mzandrew/idlab-scrod/mechanical-designs/board-stack/fDIRC/from-Jerry/Detector_holder copy.pdf

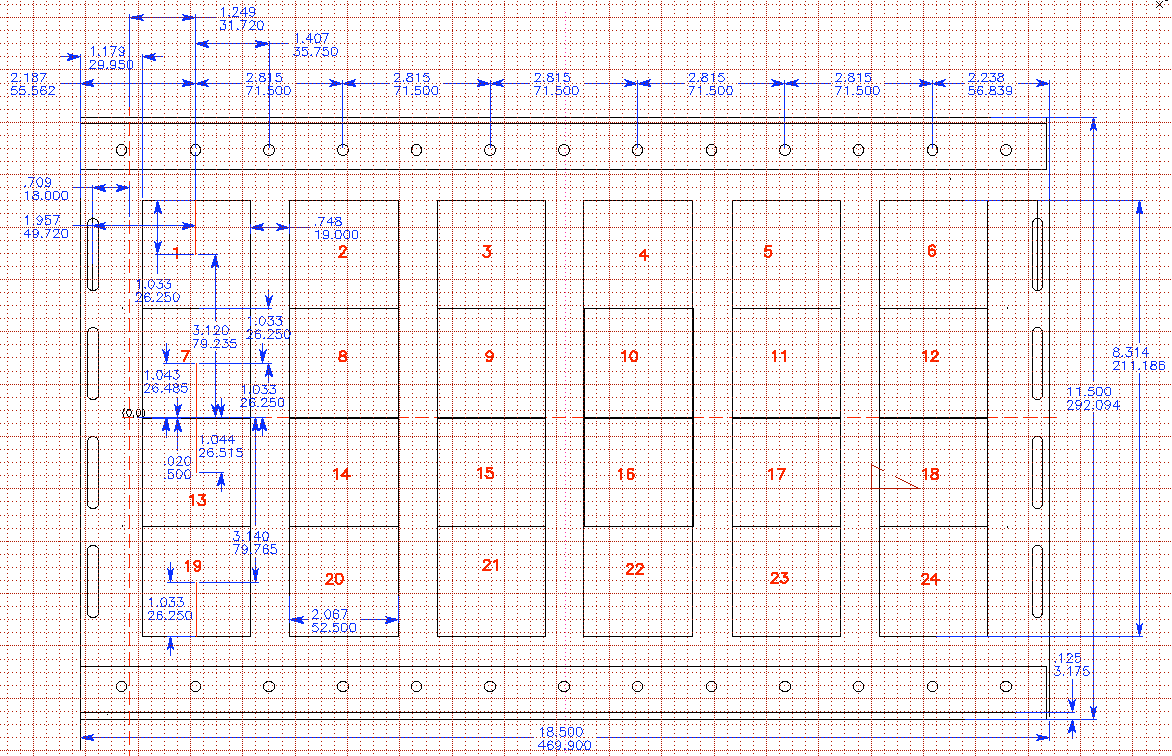
[picture p3: page 1]
