mzandrew/idlab-scrod/mechanical-designs/board-stack/fDIRC/from-Jerry/FDIRC_detector_enclosure.pdf

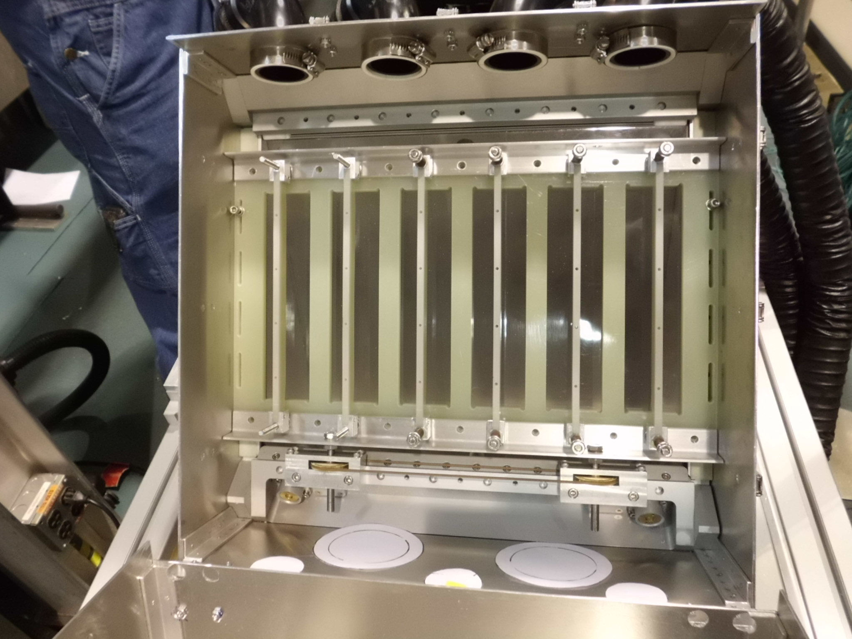
[picture p4: page 1]
