mzandrew/idlab-scrod/mechanical-designs/board-stack/fDIRC/from-Jerry/FDIRC_detector_frame.pdf

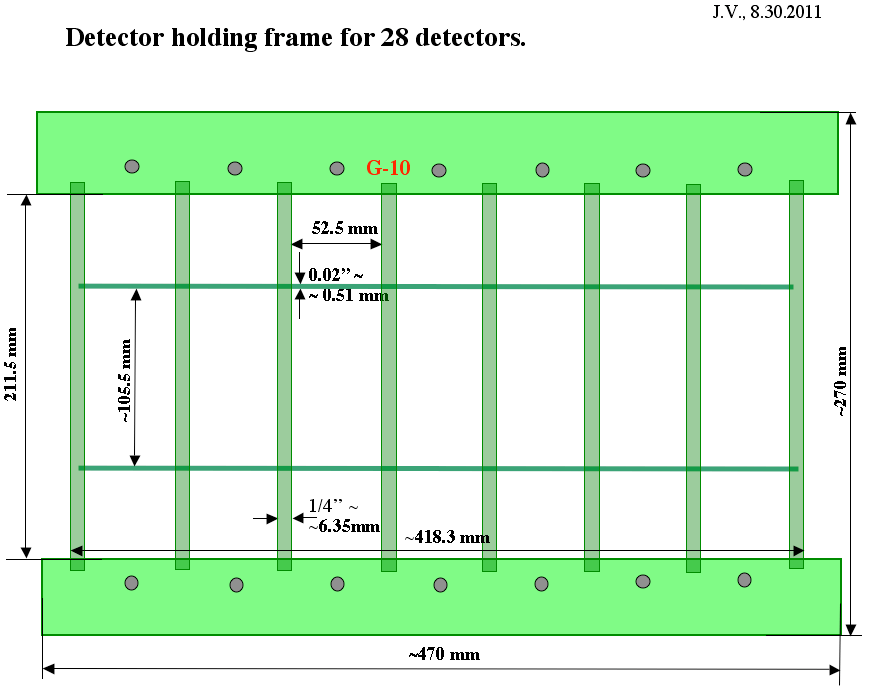
[picture p5: page 1]
