mzandrew/idlab-scrod/mechanical-designs/board-stack/fDIRC/from-Jerry/FDIRC_detector_frame_c.pdf

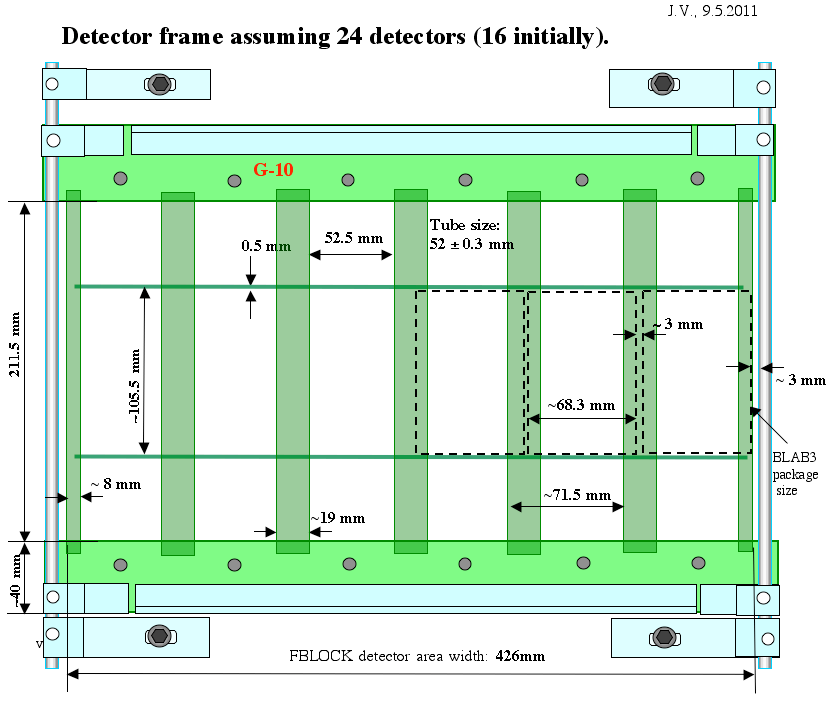
[picture p6: page 1]
