mzandrew/idlab-scrod/mechanical-designs/board-stack/fDIRC/from-Jerry/FDIRC_with_IRS2_electronics.6.pdf

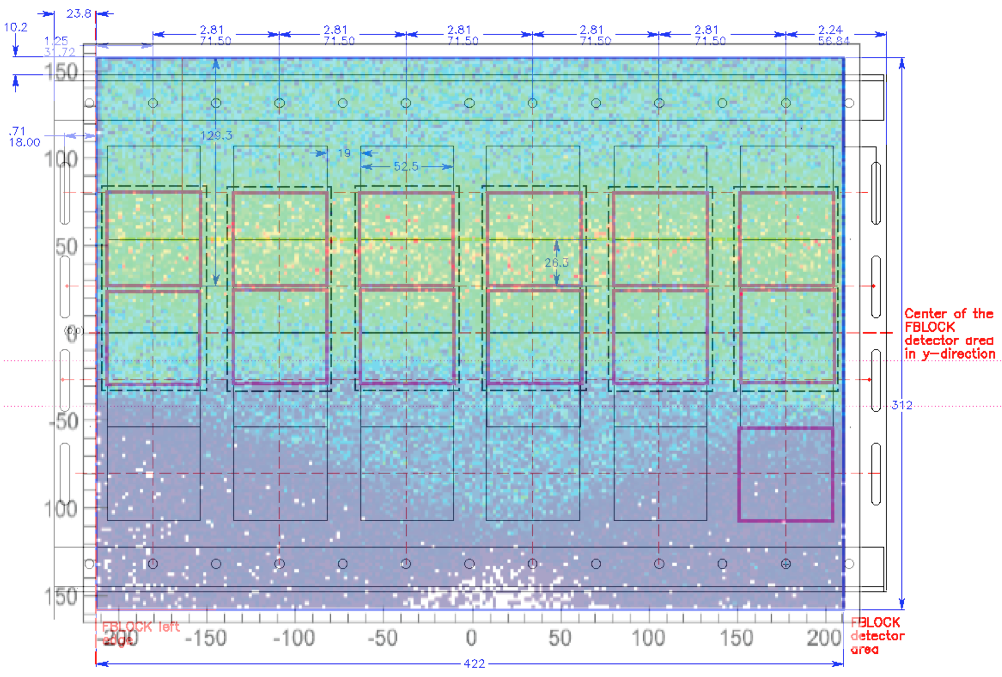
[picture p7: page 1]
