mzandrew/idlab-scrod/mechanical-designs/board-stack/fDIRC/from-Jerry/CIMG1078.JPG

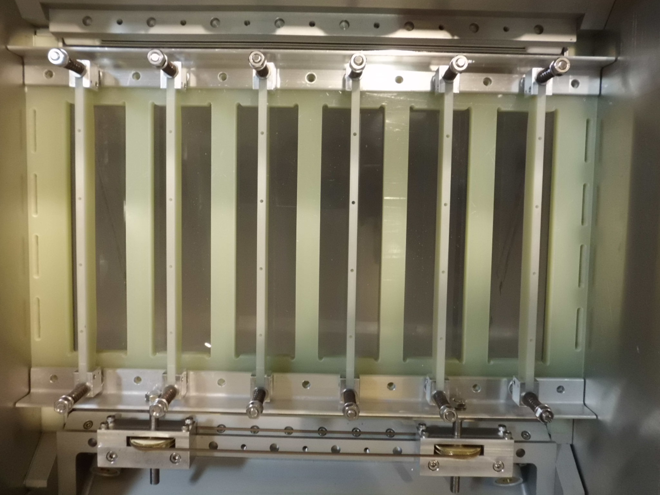
mechanical-designs/board-stack/fDIRC/from-Jerry/CIMG1078.JPG
