mzandrew/idlab-scrod/mechanical-designs/board-stack/fDIRC/from-Jerry/fDIRC_BLAB_PKG.JPG

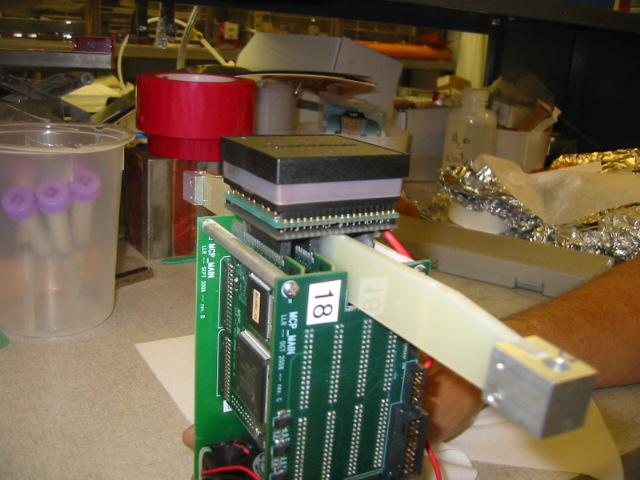
mechanical-designs/board-stack/fDIRC/from-Jerry/fDIRC_BLAB_PKG.JPG
