mzandrew/idlab-scrod/mechanical-designs/board-stack/fDIRC/from-Jerry/IMG_2022.JPG

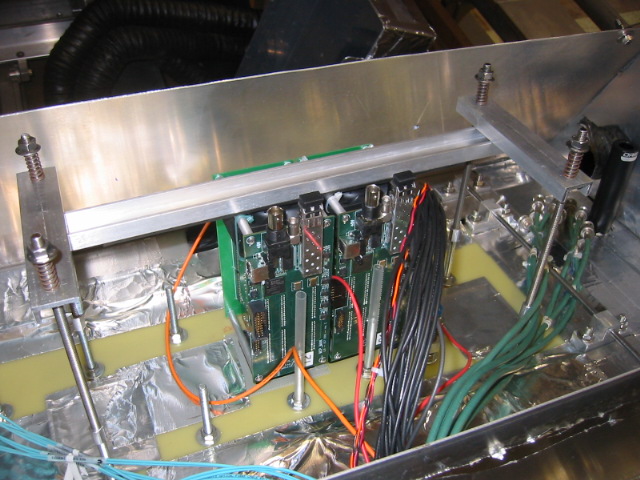
mechanical-designs/board-stack/fDIRC/from-Jerry/IMG_2022.JPG
