mzandrew/idlab-scrod/mechanical-designs/board-stack/iTOP/export/HV-bracket-and-boardstack-spacers.png

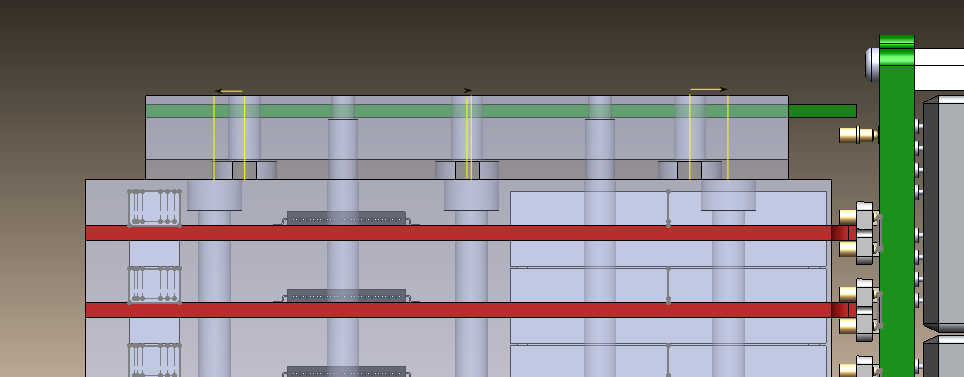
mechanical-designs/board-stack/iTOP/export/HV-bracket-and-boardstack-spacers.png
