mzandrew/idlab-scrod/mechanical-designs/board-stack/iTOP/export/intermediate-boardstack-spacers.cropped.png

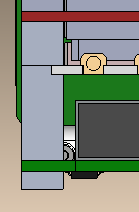
mechanical-designs/board-stack/iTOP/export/intermediate-boardstack-spacers.cropped.png
