mzandrew/idlab-scrod/mechanical-designs/board-stack/iTOP/export/intermediate-boardstack-spacers.png

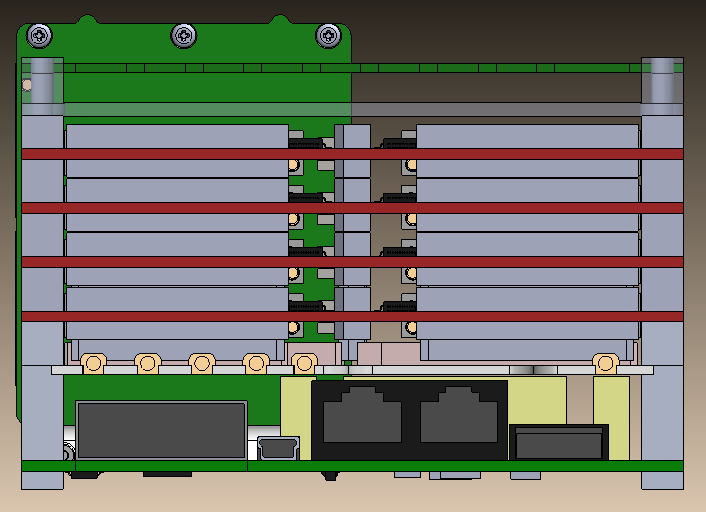
mechanical-designs/board-stack/iTOP/export/intermediate-boardstack-spacers.png
