mzandrew/idlab-scrod/mechanical-designs/board-stack/iTOP/export/iTOP-side-view.intermediate-version.cropped.png

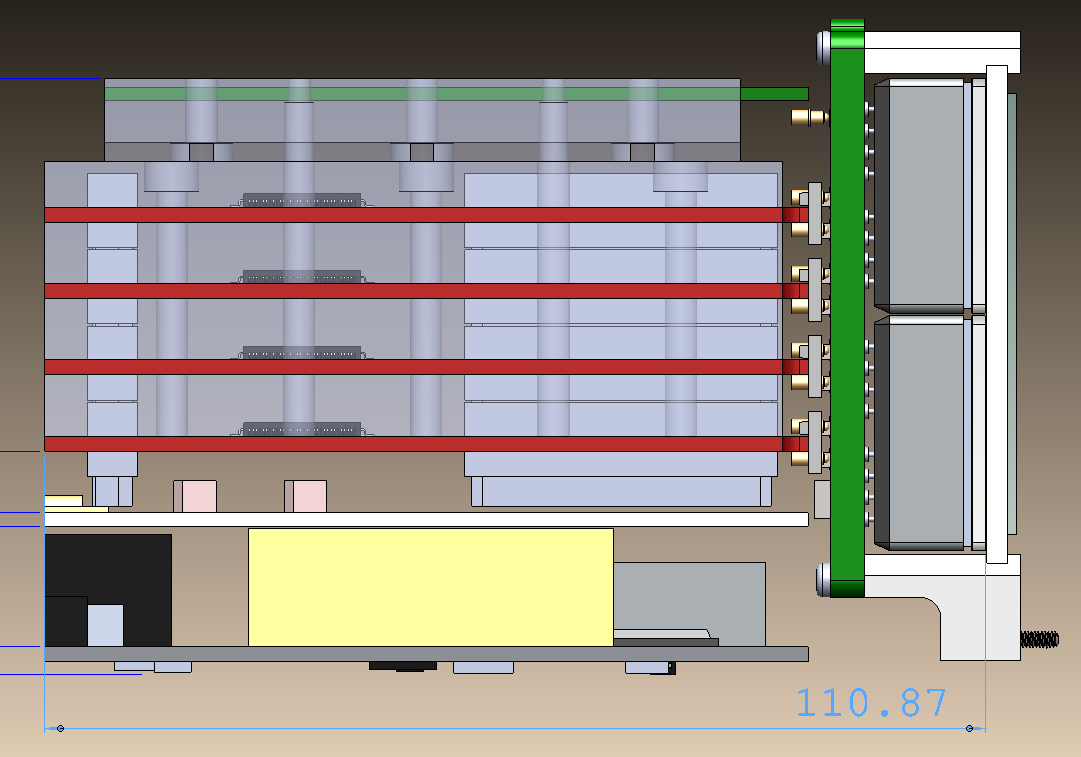
mechanical-designs/board-stack/iTOP/export/iTOP-side-view.intermediate-version.cropped.png
