mzandrew/idlab-scrod/mechanical-designs/board-stack/iTOP/export/iTOP-side-view.pre-production-prototype-version.png

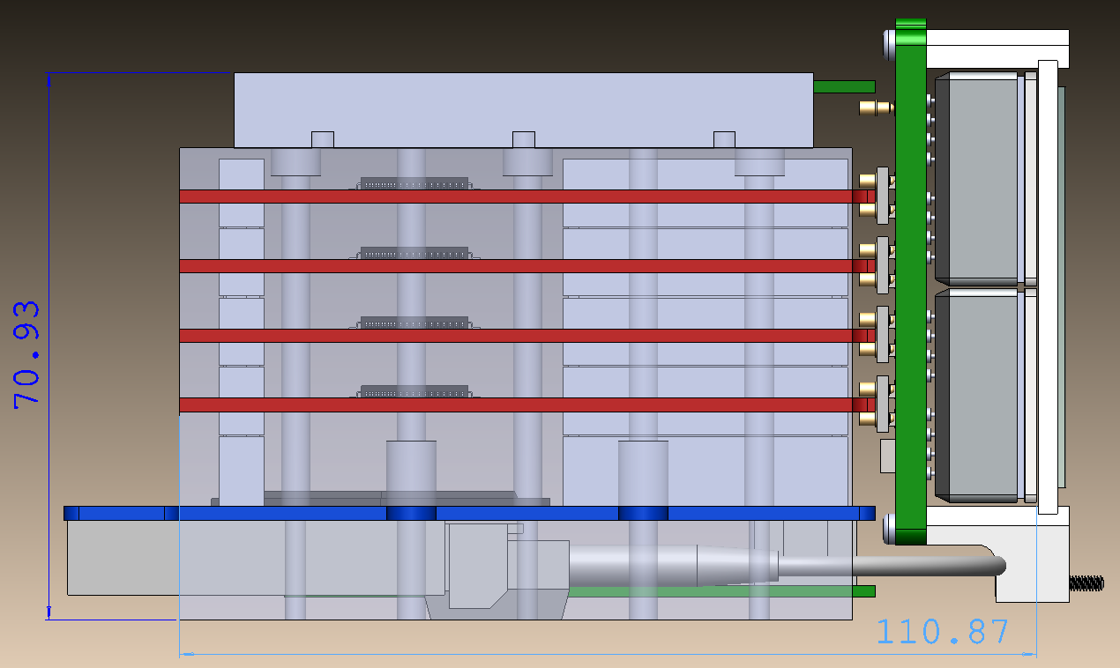
mechanical-designs/board-stack/iTOP/export/iTOP-side-view.pre-production-prototype-version.png
