mzandrew/idlab-scrod/mechanical-designs/board-stack/iTOP/export/iTOP.JPG

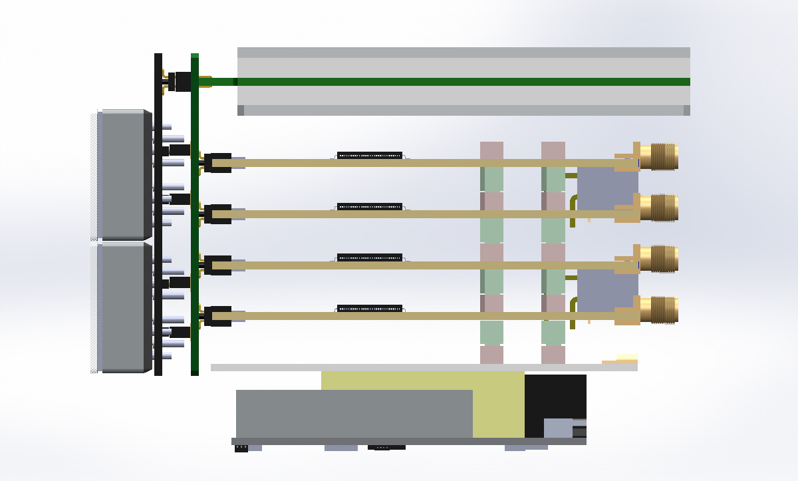
mechanical-designs/board-stack/iTOP/export/iTOP.JPG
