mzandrew/idlab-scrod/mechanical-designs/board-stack/iTOP/export/pogo-pin-carriers.png

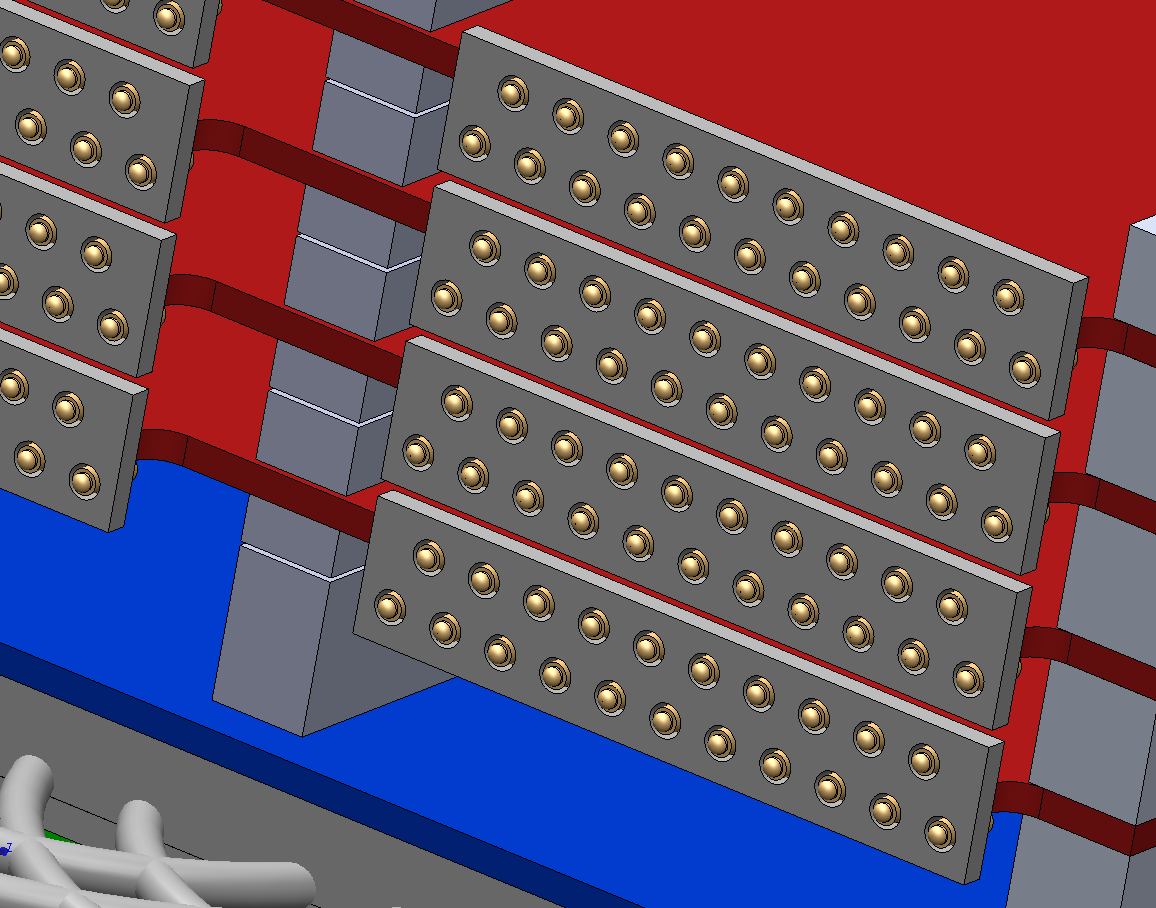
mechanical-designs/board-stack/iTOP/export/pogo-pin-carriers.png
