mzandrew/idlab-scrod/mechanical-designs/board-stack/iTOP/export/pogo-pin-carriers.revB.loaded.png

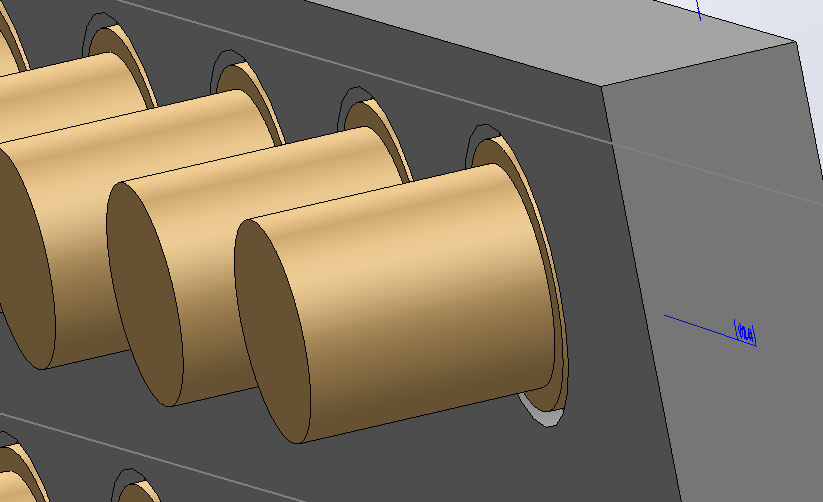
mechanical-designs/board-stack/iTOP/export/pogo-pin-carriers.revB.loaded.png
