mzandrew/idlab-scrod/mechanical-designs/board-stack/iTOP/export/pogo-pin-carriers.revB.png

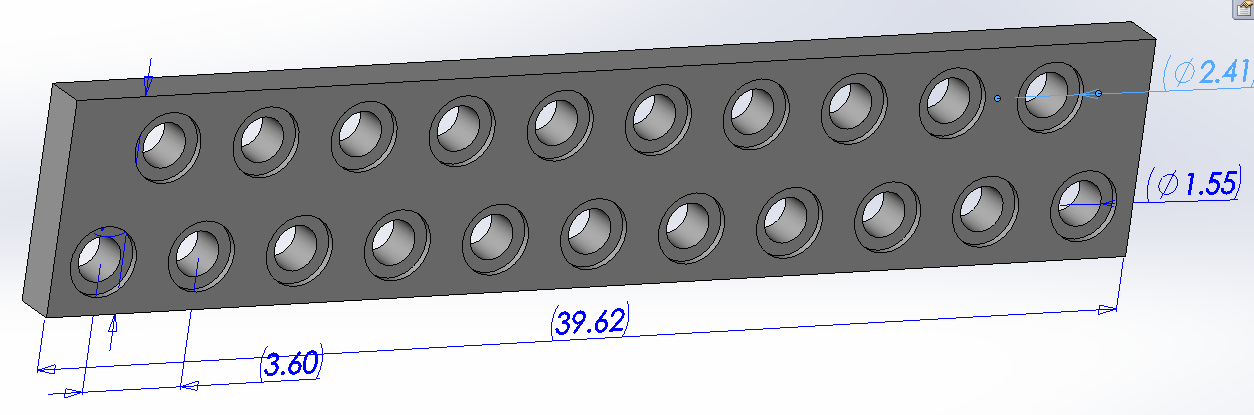
mechanical-designs/board-stack/iTOP/export/pogo-pin-carriers.revB.png
