mzandrew/idlab-scrod/mechanical-designs/board-stack/iTOP/export/pogo-pin-side-view.png

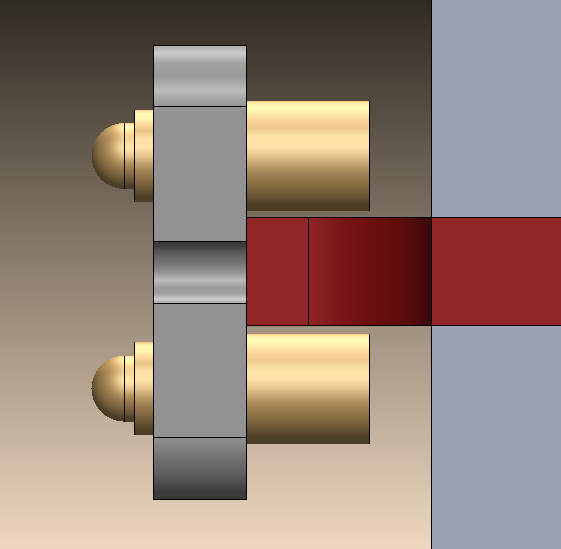
mechanical-designs/board-stack/iTOP/export/pogo-pin-side-view.png
