mzandrew/idlab-scrod/mechanical-designs/board-stack/iTOP/export/pogo-pins-in-pogo-pin-carrier-on-carrier.png

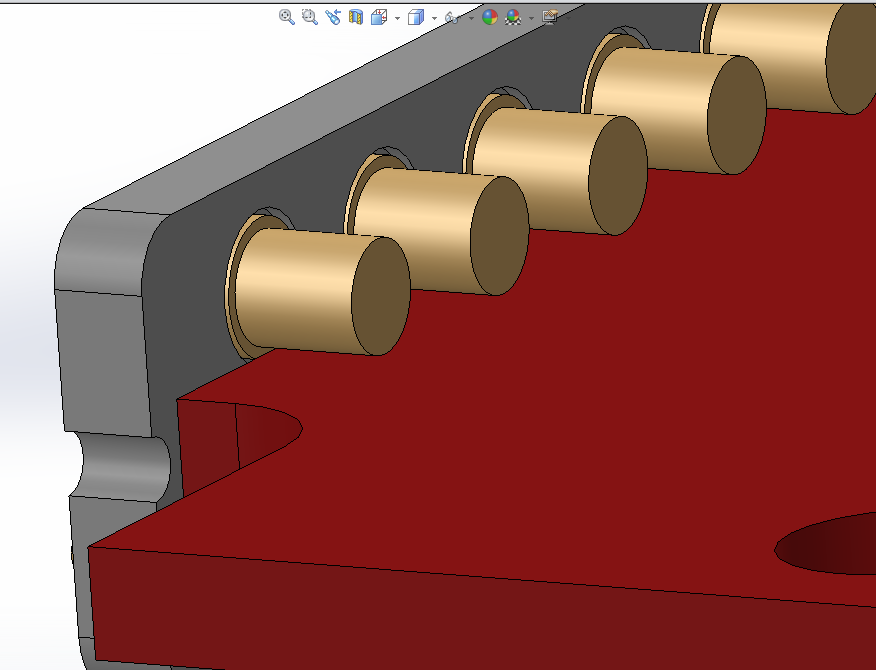
mechanical-designs/board-stack/iTOP/export/pogo-pins-in-pogo-pin-carrier-on-carrier.png
