mzandrew/idlab-scrod/mechanical-designs/board-stack/iTOP/export/SCROD-and-carriers-with-walls.JPG

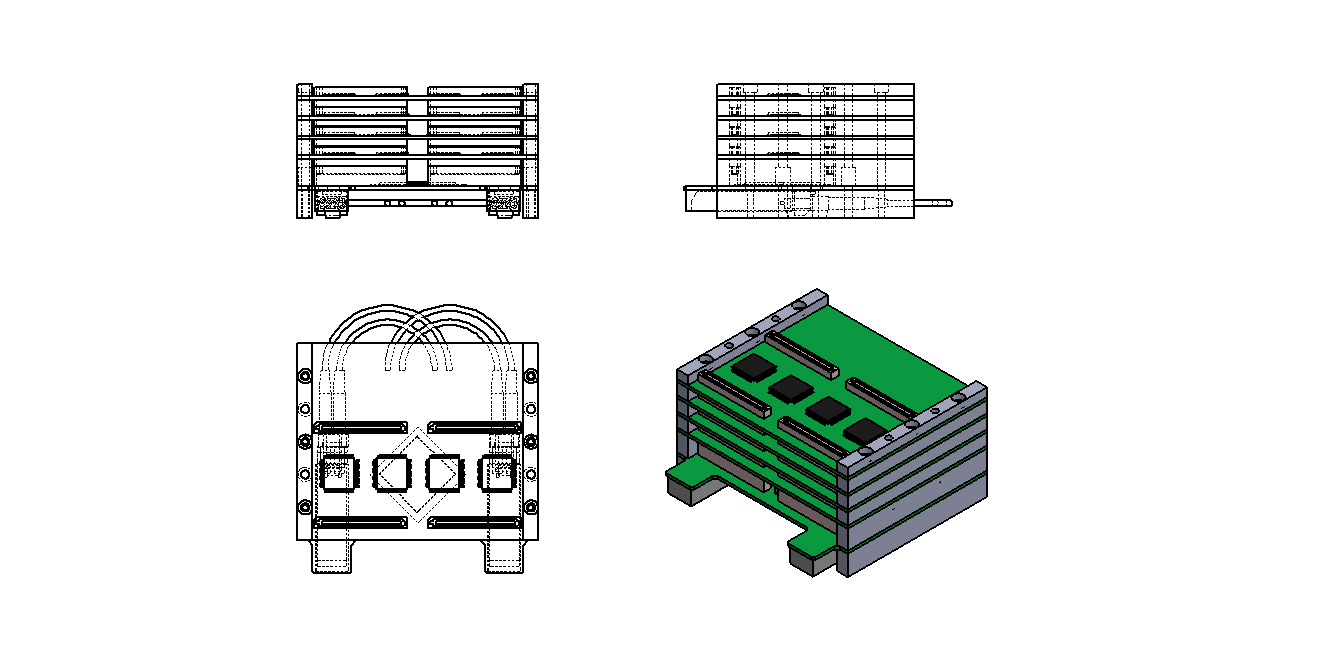
mechanical-designs/board-stack/iTOP/export/SCROD-and-carriers-with-walls.JPG
