mzandrew/idlab-scrod/mechanical-designs/board-stack/iTOP/export/SCROD-to-screwhead-clearance.png

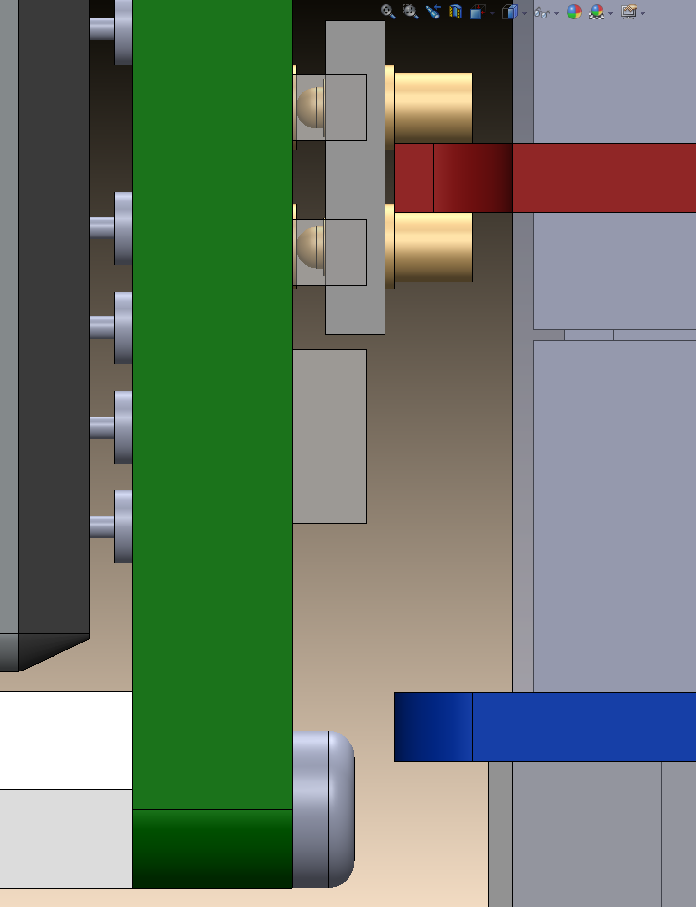
mechanical-designs/board-stack/iTOP/export/SCROD-to-screwhead-clearance.png
