mzandrew/idlab-scrod/mechanical-designs/board-stack/iTOP/export/XY-stage-with-brackets-laser-jig-and-intermediate-boardstack.png

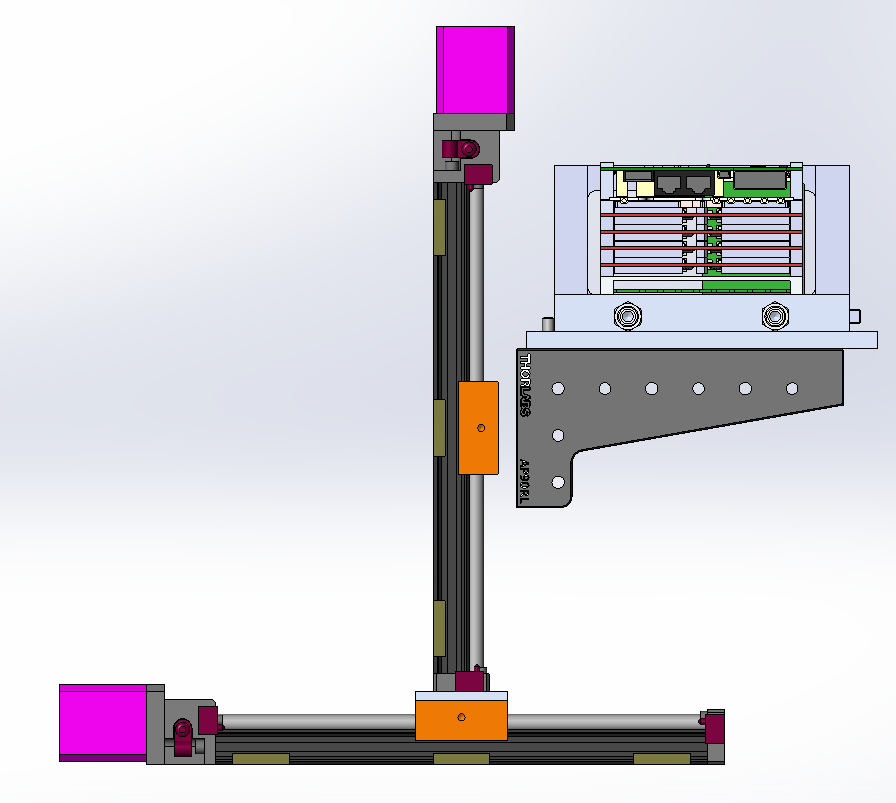
mechanical-designs/board-stack/iTOP/export/XY-stage-with-brackets-laser-jig-and-intermediate-boardstack.png
