mzandrew/idlab-scrod/mechanical-designs/board-stack/mTC/export/mTC.24PMTs.JPG

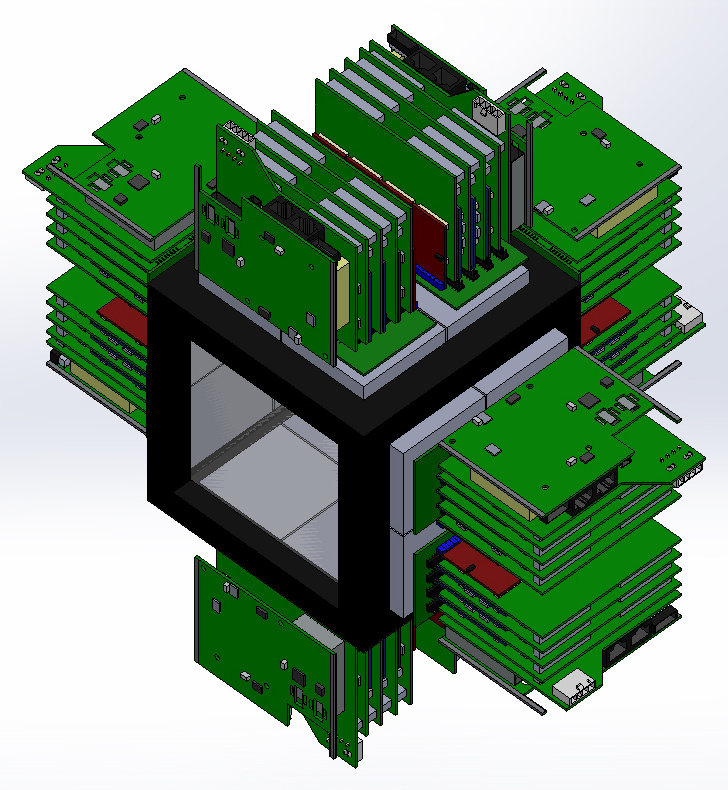
mechanical-designs/board-stack/mTC/export/mTC.24PMTs.JPG
