mzandrew/idlab-scrod/mechanical-designs/tags/r282.iTOP-module-used-at-LEPS-SPRING8/board-stack/export/board-stack.common.top.JPG

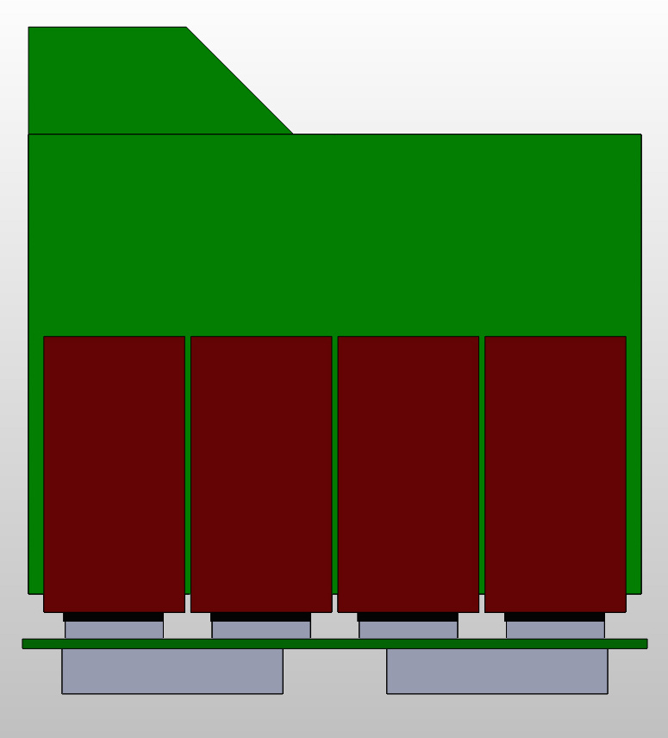
mechanical-designs/tags/r282.iTOP-module-used-at-LEPS-SPRING8/board-stack/export/board-stack.common.top.JPG
