mzandrew/idlab-scrod/mechanical-designs/tags/r282.iTOP-module-used-at-LEPS-SPRING8/board-stack/iTOP/export/iTOP-cutaway.JPG

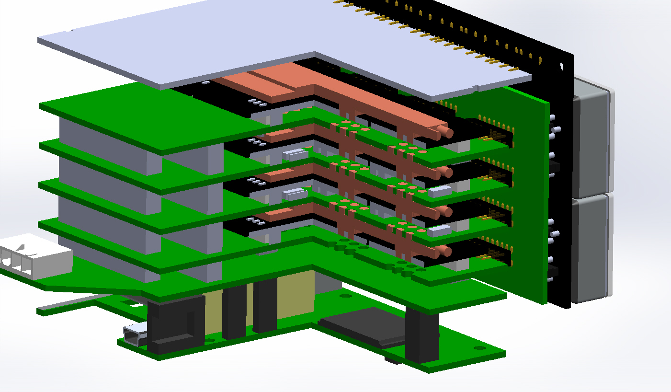
mechanical-designs/tags/r282.iTOP-module-used-at-LEPS-SPRING8/board-stack/iTOP/export/iTOP-cutaway.JPG
