mzandrew/idlab-scrod/mechanical-designs/tags/r282.iTOP-module-used-at-LEPS-SPRING8/board-stack/iTOP/export/iTOP.JPG

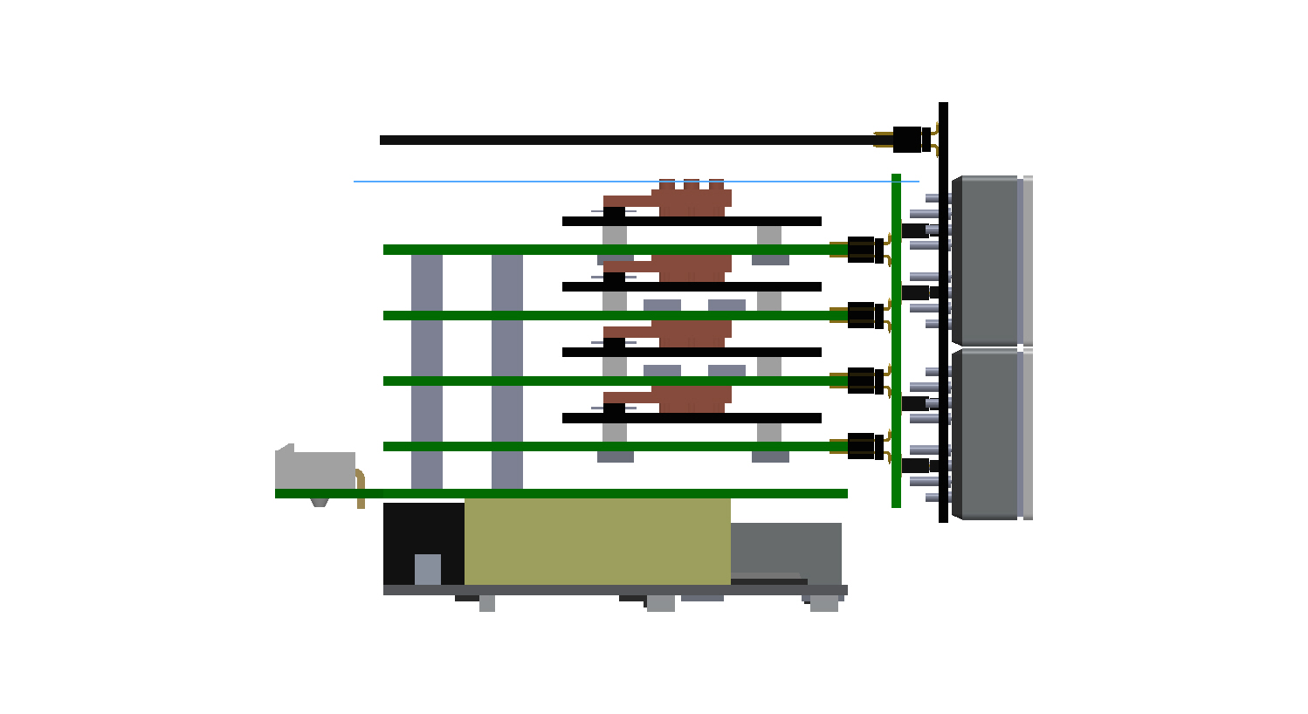
mechanical-designs/tags/r282.iTOP-module-used-at-LEPS-SPRING8/board-stack/iTOP/export/iTOP.JPG
