mzandrew/idlab-scrod/wiki/images/2012-07-12.boardstack.jpeg

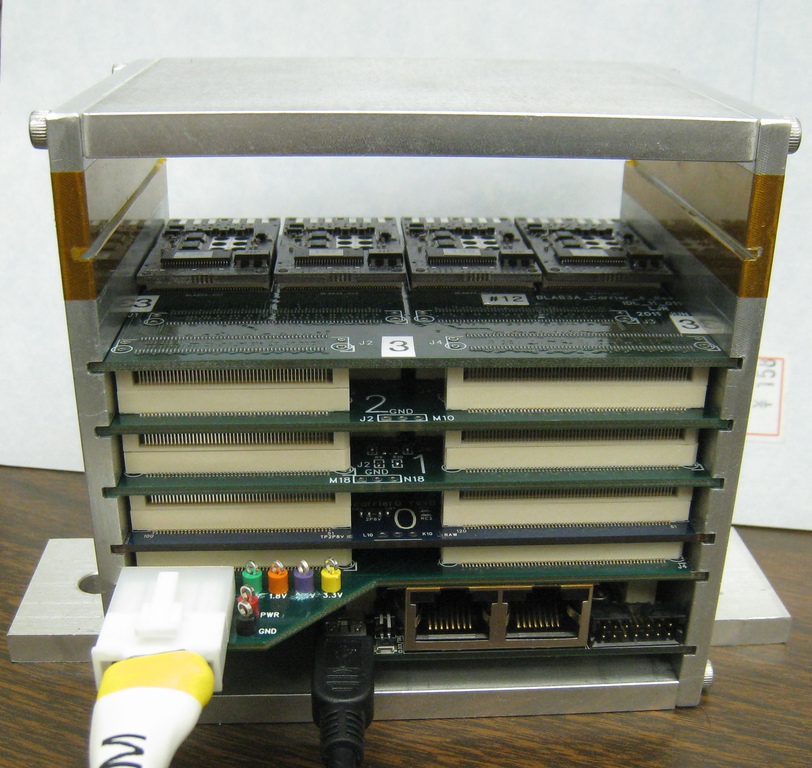
wiki/images/2012-07-12.boardstack.jpeg
