mzandrew/idlab-scrod/wiki/images/2013-12-02.frankenstack.JPG

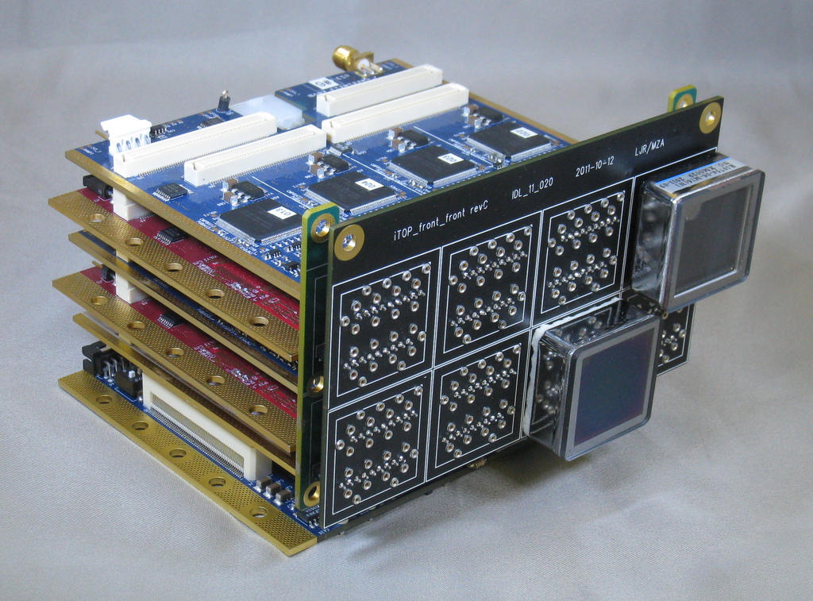
wiki/images/2013-12-02.frankenstack.JPG
