mzandrew/idlab-scrod/wiki/images/intermediate-boardstack-with-thermal-walls.front.jpeg

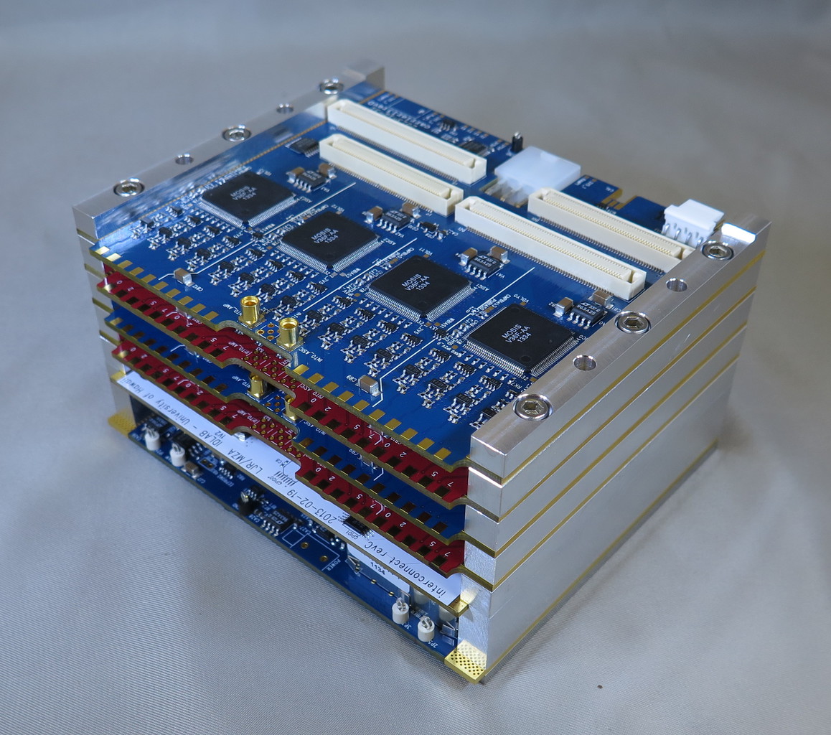
wiki/images/intermediate-boardstack-with-thermal-walls.front.jpeg
