mzandrew/idlab-scrod/wiki/images/pre-production-boardstack.jpeg

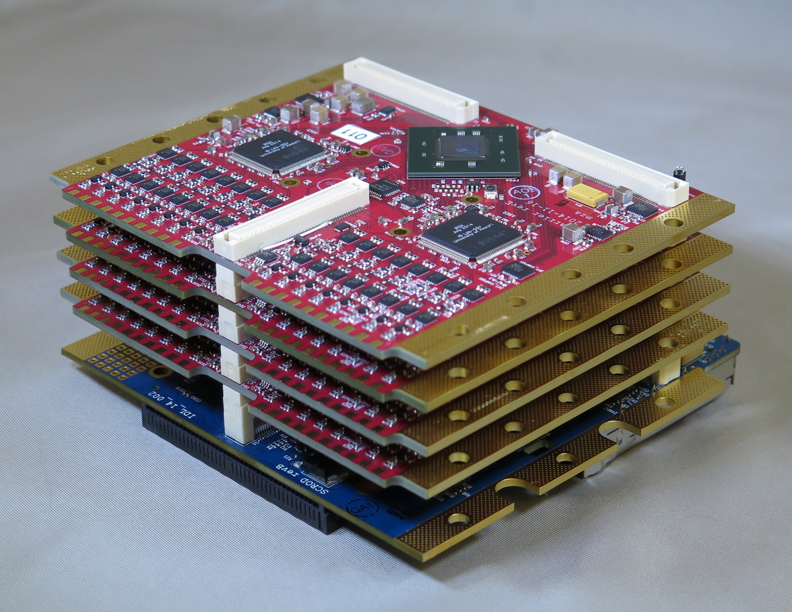
wiki/images/pre-production-boardstack.jpeg
