mzandrew/idlab-scrod/wiki/images/TOP-production-boardstack.carrier3-side.with-heatsinks.JPG

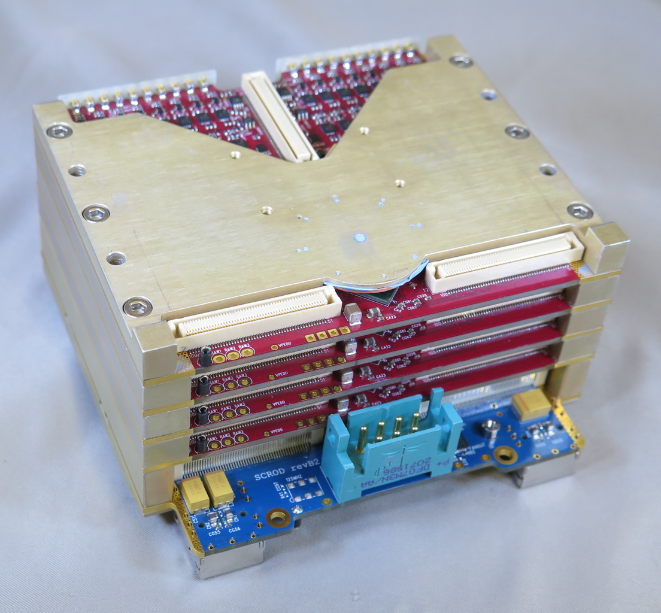
wiki/images/TOP-production-boardstack.carrier3-side.with-heatsinks.JPG
