mzandrew/idlab-scrod/wiki/images/TOP-production-boardstack.SCROD-side.with-heatsinks.JPG

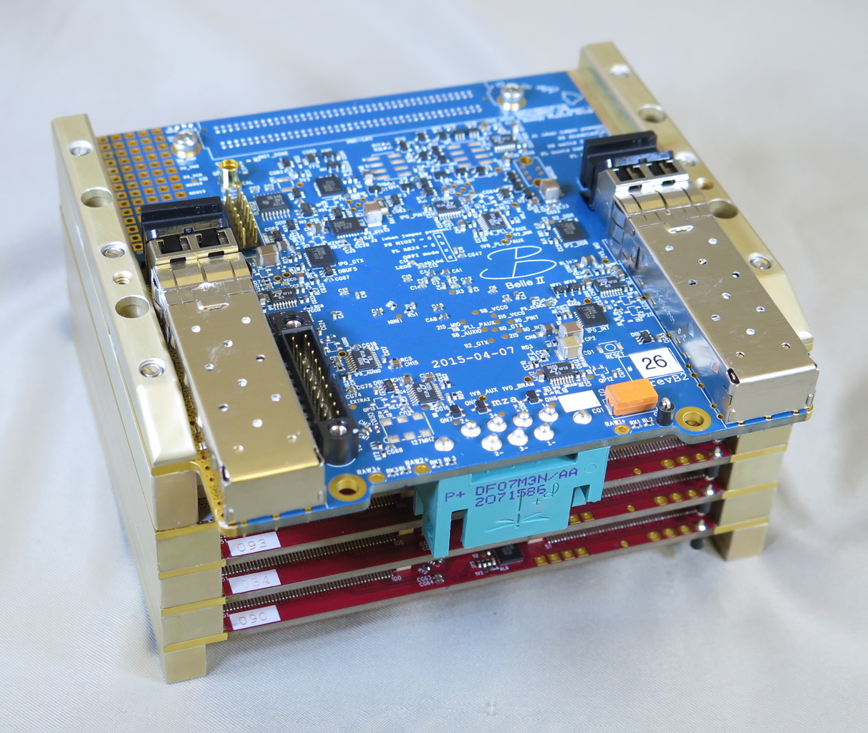
wiki/images/TOP-production-boardstack.SCROD-side.with-heatsinks.JPG
