mzandrew/idlab-scrod/SCROD-boardstack/KLM/TX9UMB-4/src/SCRODRevA4-KLM_TX9UMB_RevB_CONN_pin_mapping.xls

Sheet: SCRODrevA4-TXMBrevB
CONN# | SCRODrevA4 | BANK# | VOLTAGE BANK | SPARTAN-6 PIN | TX 9U M.B. – D.C. (REVB) | COMMENTS | CONN# | SCRODrevA4 | BANK# | VOLTAGE BANK | SPARTAN-6 PIN | TX 9U M.B. – D.C. | COMMENTS
J1.1 | GND |  |  |  |  |  | J3.1 | +5V
J1.2 | J1_002_B1 |  |  |  | J1_002_B1 |  | J3.2 | +5V
J1.3 | J1_003_C2 |  |  |  | J1_003_C2 |  | J3.3 | +5V
J1.4 | J1_004_C1 |  |  |  | J1_004_C1 |  | J3.4 | +5V
J1.5 | D3.3V |  |  |  |  |  | J3.5 | +5V
J1.6 | J1_006_D1 |  |  |  | J1_006_D1 |  | J3.6 | +5V
J1.7 | J1_007_E2 |  |  |  | J1_007_E2 |  | J3.7 | +5V
J1.8 | J1_008_E1 |  |  |  | J1_008_E1 |  | J3.8 | +5V
J1.9 | GND |  |  |  |  |  | J3.9 | GND
J1.10 | J1_010_F1 |  |  |  | TDC3_SIN | D | J3.10 | GND
J1.11 | J1_011_G2 |  |  |  | TDC3_SCLK | D | J3.11 | J3_011_M3 |  |  |  | TDC1_SIN | D
J1.12 | J1_012_G1 |  |  |  | TDC3_PCLK | D | J3.12 | J3_012_K3 |  |  |  | TDC1_SCLK | D
J1.13 | D3.3V |  |  |  |  |  | J3.13 | J3_013_H3 |  |  |  | TDC1_PCLK | D
J1.14 | J1_014_H1 |  |  |  | TDC3_SHOUT | D | J3.14 | GND
J1.15 | J1_015_J2 |  |  |  | TDC3_TRG_3 | D | J3.15 | J3_015_F3 |  |  |  | TDC1_SHOUT | D
J1.16 | J1_016_J1 |  |  |  | TDC3_TRG_4 | D | J3.16 | J3_016_D3 |  |  |  | TDC1_TRG_3 | D
J1.17 | GND |  |  |  |  |  | J3.17 | J3_017_L4 |  |  |  | TDC1_TRG_4 | D
J1.18 | J1_018_K1 |  |  |  | TDC3_TRG_5 | D | J3.18 | D2.5V
J1.19 | J1_019_L2 |  |  |  | TDC3_WR1_ENA | D | J3.19 | J3_019_G4 |  |  |  | TDC1_TRG_5 | D
J1.20 | J1_020_L1 |  |  |  | TDC3_WR2_ENA | D | J3.20 | J3_020_K5 |  |  |  | TDC1_WR1_ENA | D
J1.21 | D3.3V |  |  |  |  |  | J3.21 | J3_021_H5 |  |  |  | TDC1_WR2_ENA | D
J1.22 | J1_022_M1 |  |  |  | TDC3_SAMPLESEL_ANY | D | J3.22 | GND
J1.23 | J1_023_N2 |  |  |  | TDC3_SR_CLOCK | D | J3.23 | J3_023_L6 |  |  |  | TDC1_SAMPLESEL_ANY | D
J1.24 | J1_024_N1 |  |  |  | TDC3_DONE | D | J3.24 | J3_024_H6 |  |  |  | TDC1_SR_CLOCK | D
J1.25 | GND |  |  |  |  |  | J3.25 | J3_025_K7 |  |  |  | TDC1_DONE | D
J1.26 | J1_026_R5 |  |  |  | TDC3_MON_TIMING | D | J3.26 | D2.5V
J1.27 | J1_027_T9 |  |  |  | TDC3_TRG_2 | D | J3.27 | J3_027_M8 |  |  |  | TDC1_MON_TIMING | D
J1.28 | J1_028_T8 |  |  |  | TDC3_TRG_1 | D | J3.28 | J3_028_K8 |  |  |  | TDC1_TRG_2 | D
J1.29 | D3.3V |  |  |  |  |  | J3.29 | J3_029_L9 |  |  |  | TDC1_TRG_1 | D
J1.30 | J1_030_U9 |  |  |  | TDC4_SIN | D | J3.30 | GND
J1.31 | J1_031_U8 |  |  |  | TDC4_SCLK | D | J3.31 | J3_031_K9 |  |  |  | J3_031_K9
J1.32 | J1_032_U5 |  |  |  | TDC4_PCLK | D | J3.32 | J3_032_L10 |  |  |  | J3_032_L10
J1.33 | GND |  |  |  |  |  | J3.33 | NO CONNECTION |  |  |  | NO CONNECTION
J1.34 | J1_034_V7 |  |  |  | TDC4_SHOUT | D | J3.34 | D2.5V
J1.35 | J1_035_V6 |  |  |  | TDC4_TRG_3 | D | J3.35 | J3_035_B3 |  |  |  | PA6 | D
J1.36 | J1_036_V4 |  |  |  | TDC4_TRG_4 | D | J3.36 | J3_036_C3 |  |  |  | PA-5 | D
J1.37 | D3.3V |  |  |  |  |  | J3.37 | J3_037_B4 |  |  |  | PA-4 | D
J1.38 | J1_038_W5 |  |  |  | TDC4_TRG_5 | D | J3.38 | GND
J1.39 | J1_039_P1 |  |  |  | TDC4_WR1_ENA | D | J3.39 | J3_039_E5 |  |  |  | PA-3 | D
J1.40 | J1_040_R1 |  |  |  | TDC4_WR2_ENA | D | J3.40 | J3_040_E6 |  |  |  | PA-2 | D
J1.41 | GND |  |  |  |  |  | J3.41 | J3_041_G6 |  |  |  | PA-1 | D
J1.42 | J1_042_R2 |  |  |  | TDC4_SAMPLESEL_ANY | D | J3.42 | D2.5V
J1.43 | J1_043_U1 |  |  |  | TDC4_SR_CLOCK | D | J3.43 | J3_043_G7 |  |  |  | PA0 | D
J1.44 | J1_044_U2 |  |  |  | TDC4_DONE | D | J3.44 | J3_044_G8 |  |  |  | CTL2 | D
J1.45 | D3.3V |  |  |  |  |  | J3.45 | J3_045_G9 |  |  |  | CTL1 | D
J1.46 | J1_046_V1 |  |  |  | TDC4_MON_TIMING | D | J3.46 | GND
J1.47 | J1_047_W1 |  |  |  | TDC4_TRG_2 | D | J3.47 | J3_047_E10 |  |  |  | CTL0 | D
J1.48 | J1_048_W2 |  |  |  | TDC4_TRG_1 | D | J3.48 | J3_048_G10 |  |  |  | FD0 | D
J1.49 | GND |  |  |  |  |  | J3.49 | J3_049_F11 |  |  |  | FD1 | D
J1.50 | J1_050_Y1 |  |  |  | TDC5_TRG_1 | D | J3.50 | D2.5V
J1.51 | J1_051_AA1 |  |  |  | TDC5_TRG_2 | D | J3.51 | J3_051_J11 |  |  |  | FD2 | D
J1.52 | J1_052_AA2 |  |  |  | TDC5_MON_TIMING | D | J3.52 | J3_052_H12 |  |  |  | FD3 | D
J1.53 | D3.3V |  |  |  |  |  | J3.53 | J3_053_J12 |  |  |  | FD4 | D
J1.54 | J1_054_AB1 |  |  |  | BUSB_SCK_DAC | D | J3.54 | GND
J1.55 | J1_055_AC1 |  |  |  | BUSB_DIN_DAC | D | J3.55 | J3_055_K12 |  |  |  | FD5 | D
J1.56 | J1_056_AC2 |  |  |  | BUSA_RAMP | D | J3.56 | J3_056_D13 |  |  |  | FD6 | D
J1.57 | GND |  |  |  |  |  | J3.57 | J3_057_E13 |  |  |  | FD7 | D
J1.58 | J1_058_AD1 |  |  |  | BUSA_RD_RS_S0 | D | J3.58 | D2.5V
J1.59 | J1_059_AE1 |  |  |  | BUSA_RD_RS_S1 | D | J3.59 | D2.5V
J1.60 | J1_060_AE2 |  |  |  | BUSA_RD_RS_S2 | D | J3.60 | D2.5V
J1.61 | J1_061_AB11_L48N |  |  |  | BUSA_SR_SEL | D | J3.61 | GND
J1.62 | J1_062_AA10_L48P |  |  |  | TDC5_SR_CLOCK | D | J3.62 | GND
J1.63 | J1_063_AA7_L64P |  |  |  | BUSA_SR_CLEAR | D | J3.63 | GND
J1.64 | D3.3V |  |  |  |  |  | J3.64 | J3_064_C13_GCLK+ |  |  |  | IFCLK | D
J1.65 | J1_065_AA6_L64N |  |  |  | BUSA_DO_9 | D | J3.65 | J3_065_A13_GCLK- |  |  |  | CLKOUT | D
J1.66 | J1_066_W8_L62P |  |  |  | BUSA_DO_10 | D | J3.66 | J3_066_G13 |  |  |  | PA7 | D
J1.67 | J1_067_W7_L62N |  |  |  | BUSA_DO_11 | D | J3.67 | D2.5V
J1.68 | GND |  |  |  |  |  | J3.68 | J3_068_G12 |  |  |  | WAKEUP | D
J1.69 | J1_069_AD3 |  |  |  | BUSA_DO_12 | D | J3.69 | J3_069_F12 |  |  |  | FD8 | D
J1.70 | J1_070_AC4 |  |  |  | BUSA_DO_13 | D | J3.70 | J3_070_E12 |  |  |  | FD9 | D
J1.71 | J1_071_AC3 |  |  |  | BUSA_DO_14 | D | J3.71 | GND
J1.72 | D3.3V |  |  |  |  |  | J3.72 | J3_072_G11 |  |  |  | FD10 | D
J1.73 | J1_073_AB5 |  |  |  | BUSA_DO_15 | D | J3.73 | J3_073_H10 |  |  |  | FD11 | D
J1.74 | J1_074_AB4 |  |  |  | BUSA_DO_16 | D | J3.74 | J3_074_F10 |  |  |  | FD12 | D
J1.75 | J1_075_AB3 |  |  |  | TDC5_SAMPLESEL_ANY | D | J3.75 | D2.5V
J1.76 | GND |  |  |  |  |  | J3.76 | J3_076_H9 |  |  |  | FD13 | D
J1.77 | J1_077_AA4 |  |  |  | BUSA_SAMPLESEL_S1 | D | J3.77 | J3_077_F9 |  |  |  | FD14 | D
J1.78 | J1_078_AA3 |  |  |  | BUSA_SAMPLESEL_S2 | D | J3.78 | J3_078_H8 |  |  |  | FD15 | D
J1.79 | J1_079_Y6 |  |  |  | BUSA_SAMPLESEL_S3 | D | J3.79 | GND
J1.80 | D3.3V |  |  |  |  |  | J3.80 | J3_080_F7 |  |  |  | RDY0 | D
J1.81 | J1_081_Y5 |  |  |  | BUSA_SAMPLESEL_S4 | D | J3.81 | J3_081_F6 |  |  |  | RDY1 | D
J1.82 | J1_082_Y3 |  |  |  | TDC5_WR2_ENA | D | J3.82 | J3_082_F5 |  |  |  | J3_082_F5
J1.83 | J1_083_W3 |  |  |  | BUSA_SAMPLESEL_S5 | D | J3.83 | D2.5V
J1.84 | GND |  |  |  |  |  | J3.84 | J3_084_D5 |  |  |  | J3_084_D5
J1.85 | J1_085_V3 |  |  |  | TDC5_WR1_ENA | D | J3.85 | J3_085_A4 |  |  |  | J3_085_A4
J1.86 | J1_086_V5 |  |  |  | BUSA_RD_CS_S5 | D | J3.86 | J3_086_A3 |  |  |  | SDA_MON | D
J1.87 | J1_087_U3 |  |  |  | BUSA_WR_ADDRCLR | D | J3.87 | GND
J1.88 | D3.3V |  |  |  |  |  | J3.88 | J3_088_A2 |  |  |  | SCL_MON | D
J1.89 | J1_089_U4 |  |  |  | BUSA_RD_CS_S4 | D | J3.89 | J3_089_K10 |  |  |  | J3_089_K10
J1.90 | J1_090_U7 |  |  |  | BUSA_RD_CS_S2 | D | J3.90 | J3_090_J9 |  |  |  | J3_090_J9
J1.91 | J1_091_T4 |  |  |  | BUSA_RD_CS_S3 | D | J3.91 | D2.5V
J1.92 | GND |  |  |  |  |  | J3.92 | J3_092_B2 |  |  |  | TDC2_TRG_1 | D
J1.93 | J1_093_T6 |  |  |  | BUSA_RD_CS_S0 | D | J3.93 | J3_093_L8 |  |  |  | TDC2_TRG_2 | D
J1.94 | J1_094_R3 |  |  |  | BUSA_RD_CS_S1 | D | J3.94 | J3_094_J7 |  |  |  | TDC2_MON_TIMING | D
J1.95 | J1_095_R4 |  |  |  | TDC5_TRG_5 | D | J3.95 | GND
J1.96 | D3.3V |  |  |  |  |  | J3.96 | J3_096_L7 |  |  |  | TDC2_DONE | D
J1.97 | J1_097_R6 |  |  |  | TDC5_TRG_4 | D | J3.97 | J3_097_K6 |  |  |  | TDC2_SR_CLOCK | D
J1.98 | J1_098_R7 |  |  |  | TDC5_TRG_3 | D | J3.98 | J3_098_M6 |  |  |  | TDC2_SAMPLESEL_ANY | D
J1.99 | J1_099_R8 |  |  |  | TDC5_SHOUT | D | J3.99 | D2.5V
J1.100 | GND |  |  |  |  |  | J3.100 | J3_100_J5 |  |  |  | TDC2_WR2_ENA | D
J1.101 | J1_101_R9 |  |  |  | TDC5_PCLK | D | J3.101 | J3_101_E4 |  |  |  | TDC2_WR1_ENA | D
J1.102 | J1_102_R10 |  |  |  | TDC5_SCLK | D | J3.102 | J3_102_J4 |  |  |  | TDC2_TRG_5 | D
J1.103 | J1_103_P3 |  |  |  | TDC5_SIN | D | J3.103 | GND
J1.104 | D3.3V |  |  |  |  |  | J3.104 | J3_104_M4 |  |  |  | TDC2_TRG_4 | D
J1.105 | J1_105_P5 |  |  |  | BUSA_DO_8 | D | J3.105 | J3_105_E3 |  |  |  | TDC2_TRG_3 | D
J1.106 | J1_106_P6 |  |  |  | BUSA_DO_7 | D | J3.106 | J3_106_G3 |  |  |  | TDC2_SHOUT | D
J1.107 | J1_107_P8 |  |  |  | BUSA_DO_6 | D | J3.107 | D2.5V
J1.108 | GND |  |  |  |  |  | J3.108 | J3_108_J3 |  |  |  | TDC2_PCLK | D
J1.109 | J1_109_P10 |  |  |  | BUSA_DO_5 | D | J3.109 | J3_109_L3 |  |  |  | TDC2_SCLK | D
J1.110 | J1_110_N4 |  |  |  | BUSA_DO_4 | D | J3.110 | J3_110_N3 |  |  |  | TDC2_SIN | D
J1.111 | J1_111_N5 |  |  |  | BUSA_DO_3 | D | J3.111 | GND
J1.112 | D3.3V |  |  |  |  |  | J3.112 | GND
J1.113 | J1_113_N6 |  |  |  | BUSA_DO_2 | D | J3.113 | +5V
J1.114 | J1_114_N7 |  |  |  | BUSA_DO_1 | D | J3.114 | +5V
J1.115 | J1_115_N8 |  |  |  | TDC5_DONE | D | J3.115 | +5V
J1.116 | GND |  |  |  |  |  | J3.116 | +5V
J1.117 | J1_117_N9 |  |  |  | BUSA_CLR | D | J3.117 | +5V
J1.118 | J1_118_M9 |  |  |  | BUS_REGCLR | D | J3.118 | +5V
J1.119 | J1_119_M10 |  |  |  | BUSA_RD_ENA | D | J3.119 | +5V
J1.120 | D3.3V |  |  |  |  |  | J3.120 | +5V
J2.1 | D2.5V |  |  |  |  |  | J4.1 | D2.5V
J2.2 | D2.5V |  |  |  |  |  | J4.2 | D2.5V
J2.3 | J2_003_V10 |  |  |  | EX_TRIGGER | D | J4.3 | D2.5V
J2.4 | J2_004_AD4_L63P |  |  |  | TDC2_SSTIN_P | D | J4.4 | D2.5V
J2.5 | J2_005_AF4_L63N |  |  |  | TDC2_SSTIN_N | D | J4.5 | D2.5V
J2.6 | GND |  |  |  |  |  | J4.6 | J4_006_C24 |  |  |  | TDC10_DONE | D
J2.7 | J2_007_AE5_L51P |  |  |  | TDC1_WL_CLK_P | D | J4.7 | J4_007_D24 |  |  |  | BUSB_RD_ENA | D
J2.8 | J2_008_AF5_L51N |  |  |  | TDC1_WL_CLK_N | D | J4.8 | J4_008_D23 |  |  |  | BUSB_RD_RS_S2 | D
J2.9 | J2_009_U13 |  |  |  | BUSA_DIN_DAC | D | J4.9 | GND
J2.10 | D2.5V |  |  |  |  |  | J4.10 | J4_010_E24 |  |  |  | BUSB_RD_RS_S1 | D
J2.11 | J2_011_U15 |  |  |  | BUSA_SCK_DAC | D | J4.11 | J4_011_E23 |  |  |  | BUSB__RD_RS_S0 | D
J2.12 | J2_012_AD6_L49P |  |  |  | TDC3_SSTIN_P | D | J4.12 | J4_012_F24 |  |  |  | BUSB_RAMP | D
J2.13 | J2_013_AF6_L49N |  |  |  | TDC3_SSTIN_N | D | J4.13 | D2.5V
J2.14 | GND |  |  |  |  |  | J4.14 | J4_014_F23 |  |  |  | TDC10_MON_TIMING | D
J2.15 | J2_015_AC6_L53N |  |  |  | TDC4_SSTIN_N | D | J4.15 | J4_015_F22 |  |  |  | TDC10_TRG_2 | D
J2.16 | J2_016_AB7_L53P |  |  |  | TDC4_SSTIN_P | D | J4.16 | J4_016_G24 |  |  |  | TDC10_TRG_1 | D
J2.17 | J2_017_Y17_L16P |  |  |  | TDC_AMUX_S0 | D | J4.17 | GND
J2.18 | D1.2V |  |  |  |  |  | J4.18 | J4_018_G23 |  |  |  | BUSB_SR_SEL | D
J2.19 | J2_019_AA17_L16N |  |  |  | TDC_AMUX_S1 | D | J4.19 | J4_019_G20 |  |  |  | BUSB_SR_CLEAR | D
J2.20 | J2_020_W9_L50N |  |  |  | TDC5_SSTIN_N | D | J4.20 | J4_020_H24 |  |  |  | TDC10_SR_CLOCK | D
J2.21 | J2_021_W10_L50P |  |  |  | TDC5_SSTIN_P | D | J4.21 | D2.5V
J2.22 | GND |  |  |  |  |  | J4.22 | J4_022_H22 |  |  |  | BUSB_DO_10 | D
J2.23 | J2_023_AA8_L52N |  |  |  | TDC_AMUX_S2 | D | J4.23 | J4_023_H21 |  |  |  | BUSB_DO_9 | D
J2.24 | J2_024_Y9_L52P |  |  |  | TDC_AMUX_S3 | D | J4.24 | J4_024_H20 |  |  |  | BUSB_DO_12 | D
J2.25 | J2_025_N18 |  |  |  | TOP_AMUX_S0 | D | J4.25 | GND
J2.26 | D1.2V |  |  |  |  |  | J4.26 | J4_026_J24 |  |  |  | BUSB_DO_11 | D
J2.27 | J2_027_T19 |  |  |  | TOP_AMUX_S1 | D | J4.27 | J4_027_J23 |  |  |  | BUSB_DO_14 | D
J2.28 | J2_028_V12_L35P |  |  |  | TOP_AMUX_S2 | D | J4.28 | J4_028_J22 |  |  |  | BUSB_DO_13 | D
J2.29 | J2_029_W12_L35N |  |  |  | TOP_AMUX_S3 | D | J4.29 | D2.5V
J2.30 | GND |  |  |  |  |  | J4.30 | J4_030_J20 |  |  |  | BUSB_DO_15 | D
J2.31 | J2_031_AB13_L36P |  |  |  | TDC10_SSTIN_P | D | J4.31 | J4_031_K24 |  |  |  | BUSB_DO_16 | D
J2.32 | J2_032_AA13_L36N |  |  |  | TDC10_SSTIN_N | D | J4.32 | J4_032_K22 |  |  |  | TDC10_SAMPLESEL_ANY | D
J2.33 | J2_033_P19 |  |  |  | TDC6_DONE | D | J4.33 | GND
J2.34 | D1.2V |  |  |  |  |  | J4.34 | J4_034_K20 |  |  |  | BUSB_SAMPLESEL_S1 | D
J2.35 | J2_035_V20 |  |  |  | TDC6_MON_TIMING | D | J4.35 | J4_035_K21 |  |  |  | BUSB_SAMPLESEL_S2 | D
J2.36 | J2_036_Y16_L19N |  |  |  | TDC9_SSTIN_N | D | J4.36 | J4_036_K19 |  |  |  | BUSB_SAMPLESEL_S3 | D
J2.37 | J2_037_W16_L19P |  |  |  | TDC9_SSTIN_P | D | J4.37 | D2.5V
J2.38 | GND |  |  |  |  |  | J4.38 | J4_038_K18 |  |  |  | BUSB_SAMPLESEL_S4 | D
J2.39 | J2_039_W17_L14P |  |  |  | TDC8_SSTIN_P | D | J4.39 | J4_039_L21 |  |  |  | TDC10_WR2_ENA | D
J2.40 | J2_040_W18_L14N |  |  |  | TDC8_SSTIN_N | D | J4.40 | J4_040_L20 |  |  |  | BUSB_SAMPLESEL_S5 | D
J2.41 | J2_041_V18/D1/MISO2 |  |  |  | TDC6_TRG_2 | D | J4.41 | GND
J2.42 | D1.2V |  |  |  |  |  | J4.42 | J4_042_L19 |  |  |  | TDC10_WR1_ENA | D
J2.43 | J2_043_W19/D2/MISO3 |  |  |  | TDC6_TRG_1 | D | J4.43 | J4_043_M24 |  |  |  | BUSB_RD_CS_S5 | D
J2.44 | J2_044_Y20_L4N |  |  |  | TDC7_WL_CLK_N | D | J4.44 | J4_044_M23 |  |  |  | BUSB_WR_ADDRCLR | D
J2.45 | J2_045_W20_L4P |  |  |  | TDC7_WL_CLK_P | D | J4.45 | D2.5V
J2.46 | GND |  |  |  |  |  | J4.46 | J4_046_M21 |  |  |  | BUSB_RD_CS_S4 | D
J2.47 | J2_047_AB21_L15N |  |  |  | TDC6_SSTIN_N | D | J4.47 | J4_047_M19 |  |  |  | BUSB_RD_CS_S2 | D
J2.48 | J2_048_AA21_L15P |  |  |  | TDC6_SSTIN_P | D | J4.48 | J4_048_M18 |  |  |  | BUSB_RD_CS_S3 | D
J2.49 | J2_049_AF23/MOSI/MISO0 |  |  |  | TDC6_SIN | D | J4.49 | GND
J2.50 | D2.5V |  |  |  |  |  | J4.50 | J4_050_L24 |  |  |  | BUSB_RD_CS_S1 | D
J2.51 | J2_051_N20 |  |  |  | TDC6_SCLK | D | J4.51 | J4_051_L23 |  |  |  | BUSB_RD_CS_S0 | D
J2.52 | J2_052_U21 |  |  |  | TDC6_PCLK | D | J4.52 | J4_052_N24 |  |  |  | TDC10_TRG_4 | D
J2.53 | J2_053_P21 |  |  |  | TDC6_SHOUT | D | J4.53 | D2.5V
J2.54 | GND |  |  |  |  |  | J4.54 | J4_054_T24 |  |  |  | TDC10_TRG_5 | D
J2.55 | J2_055_U22 |  |  |  | TDC6_TRG_3 | D | J4.55 | J4_055_V24 |  |  |  | TDC10_TRG_3 | D
J2.56 | J2_056_P22 |  |  |  | TDC6_TRG_4 | D | J4.56 | J4_056_Y24 |  |  |  | TDC10_SHOUT | D
J2.57 | J2_057_N23 |  |  |  | TDC6_TRG_5 | D | J4.57 | GND
J2.58 | D2.5V |  |  |  |  |  | J4.58 | J4_058_AA24 |  |  |  | TDC10_PCLK | D
J2.59 | J2_059_R23 |  |  |  | TDC6_WR1_ENA | D | J4.59 | J4_059_AB24 |  |  |  | TDC10_SCLK | D
J2.60 | J2_060_P24 |  |  |  | TDC6_WR2_ENA | D | J4.60 | J4_060_AC24 |  |  |  | TDC10_SIN | D
J2.61 | J2_061_AA23 |  |  |  | TDC6_SAMPLESEL_ANY | D | J4.61 | J4_061_V23_GCLK+ |  |  |  | TDC7_SIN | D
J2.62 | J2_062_T23 |  |  |  | TDC6_SR_CLOCK | D | J4.62 | J4_062_W24_GCLK- |  |  |  | TDC7_SCLK | D
J2.63 | GND |  |  |  |  |  | J4.63 | J4_063_AC23 |  |  |  | TDC7_PCLK | D
J2.64 | J2_064_N22 |  |  |  | TDC7_DONE | D | J4.64 | D2.5V
J2.65 | J2_065_T22 |  |  |  | TDC7_MON_TIMING | D | J4.65 | J4_065_AD24 |  |  |  | TDC8_DONE | D
J2.66 | J2_066_N21 |  |  |  | TDC7_TRG_2 | D | J4.66 | J4_066_AE25 |  |  |  | TDC8_MON_TIMING | D
J2.67 | D2.5V |  |  |  |  |  | J4.67 | J4_067_AE26 |  |  |  | TDC8_TRG_2 | D
J2.68 | J2_068_R21 |  |  |  | TDC7_TRG_1 | D | J4.68 | GND
J2.69 | J2_069_V21 |  |  |  | TDC7_SHOUT | D | J4.69 | J4_069_AD26 |  |  |  | TDC8_TRG_1 | D
J2.70 | J2_070_R20 |  |  |  | TDC7_TRG_3 | D | J4.70 | J4_070_AC25 |  |  |  | TDC8_SIN | D
J2.71 | GND |  |  |  |  |  | J4.71 | J4_071_AC26 |  |  |  | TDC8_SCLK | D
J2.72 | J2_072_AB22_L5P |  |  |  | TDC6_WL_CLK_P | D | J4.72 | D2.5V
J2.73 | J2_073_AC22_L5N |  |  |  | TDC6_WL_CLK_N | D | J4.73 | J4_073_AB26 |  |  |  | TDC8_PCLK | D
J2.74 | J2_074_AF22 |  |  |  | TDC7_TRG_4 | D | J4.74 | J4_074_AA26 |  |  |  | TDC8_SHOUT | D
J2.75 | D1.2V |  |  |  |  |  | J4.75 | J4_075_AA25 |  |  |  | TDC8_TRG_3 | D
J2.76 | J2_076_U20 |  |  |  | TDC7_TRG_5 | D | J4.76 | GND
J2.77 | J2_077_AA19_L18P |  |  |  | TDC7_SSTIN_P | D | J4.77 | J4_077_Y26 |  |  |  | TDC8_TRG_4 | D
J2.78 | J2_078_AB19_L18N |  |  |  | TDC7_SSTIN_N | D | J4.78 | J4_078_W26 |  |  |  | TDC8_TRG_5 | D
J2.79 | GND |  |  |  |  |  | J4.79 | J4_079_W25 |  |  |  | TDC8_WR1_ENA | D
J2.80 | J2_080_AA18_L20P |  |  |  | TDC8_WL_CLK_P | D | J4.80 | D2.5V
J2.81 | J2_081_AB17_L20N |  |  |  | TDC8_WL_CLK_N | D | J4.81 | J4_081_V26 |  |  |  | TDC8_WR2_ENA | D
J2.82 | J2_082_T20 |  |  |  | TDC7_WR1_ENA | D | J4.82 | J4_082_U26_GCLK- |  |  |  | TDC8_SAMPLESEL_ANY | D
J2.83 | D1.2V |  |  |  |  |  | J4.83 | J4_083_U25_GCLK+ |  |  |  | TDC8_SR_CLOCK | D
J2.84 | J2_084_N19 |  |  |  | TDC7_WR2_ENA | D | J4.84 | GND
J2.85 | J2_085_AA15_L28P |  |  |  | TDC9_WL_CLK_P | D | J4.85 | J4_085_T26 |  |  |  | TDC9_DONE | D
J2.86 | J2_086_AB15_L28N |  |  |  | TDC9_WL_CLK_N | D | J4.86 | J4_086_R24 |  |  |  | TDC9_MON_TIMING | D
J2.87 | GND |  |  |  |  |  | J4.87 | J4_087_P26 |  |  |  | TDC9_TRG_2 | D
J2.88 | J2_088_V15_L26N |  |  |  | TDC10_WL_CLK_N | D | J4.88 | D2.5V
J2.89 | J2_089_V14_L26P |  |  |  | TDC10_WL_CLK_P | D | J4.89 | J4_089_N26 |  |  |  | TDC9_TRG_1 | D
J2.90 | J2_090_R19 |  |  |  | TDC7_SAMPLESEL_ANY | D | J4.90 | J4_090_N25 |  |  |  | TDC9_SIN | D
J2.91 | D1.2V |  |  |  |  |  | J4.91 | J4_091_M26 |  |  |  | TDC9_SCLK | D
J2.92 | J2_092_U19 |  |  |  | TDC7_SR_CLOCK | D | J4.92 | GND
J2.93 | J2_093_AA11_L41N |  |  |  | TDC10_CS_DAC | D | J4.93 | J4_093_L26 |  |  |  | TDC9_PCLK | D
J2.94 | J2_094_Y11_L41P |  |  |  | TDC9_CS_DAC | D | J4.94 | J4_094_L25 |  |  |  | TDC9_SHOUT | D
J2.95 | GND |  |  |  |  |  | J4.95 | J4_095_K26 |  |  |  | TDC9_TRG_3 | D
J2.96 | J2_096_R18 |  |  |  | TDC8_CS_DAC | D | J4.96 | D2.5V
J2.97 | J2_097_P17 |  |  |  | TDC7_CS_DAC | D | J4.97 | J4_097_J26 |  |  |  | TDC9_TRG_4 | D
J2.98 | J2_098_N17 |  |  |  | TDC6_CS_DAC | D | J4.98 | J4_098_J25 |  |  |  | TDC9_TRG_5 | D
J2.99 | D1.2V |  |  |  |  |  | J4.99 | J4_099_H26 |  |  |  | TDC9_WR1_ENA | D
J2.100 | J2_100_AA22 |  |  |  | TDC5_CS_DAC | D | J4.100 | GND
J2.101 | J2_101_AB9_L47N |  |  |  | TDC5_WL_CLK_N | D | J4.101 | J4_101_G26 |  |  |  | TDC9_WR2_ENA | D
J2.102 | J2_102_AA9_L47P |  |  |  | TDC5_WL_CLK_P | D | J4.102 | J4_102_G25 |  |  |  | TDC9_SAMPLESEL_ANY | D
J2.103 | GND |  |  |  |  |  | J4.103 | J4_103_F26 |  |  |  | TDC9_SR_CLOCK | D
J2.104 | J2_104_Y21 |  |  |  | TDC4_CS_DAC | D | J4.104 | D2.5V
J2.105 | J2_105_AA16_L24N |  |  |  | TDC4_WL_CLK_N | D | J4.105 | J4_105_E26 |  |  |  | BUSB_DO_8 | D
J2.106 | J2_106_Y15_L24P |  |  |  | TDC4_WL_CLK_P | D | J4.106 | J4_106_E25 |  |  |  | BUSB_DO_7 | D
J2.107 | D1.2V |  |  |  |  |  | J4.107 | J4_107_D26 |  |  |  | BUSB_DO_6 | D
J2.108 | J2_108_V16 |  |  |  | TDC3_CS_DAC | D | J4.108 | GND
J2.109 | J2_109_Y13_L34N |  |  |  | TDC3_WL_CLK_N | D | J4.109 | J4_109_C26 |  |  |  | BUSB_DO_5 | D
J2.110 | J2_110_W14_L34P |  |  |  | TDC3_WL_CLK_P | D | J4.110 | J4_110_C25 |  |  |  | BUSB_DO_4 | D
J2.111 | GND |  |  |  |  |  | J4.111 | J4_111_B26 |  |  |  | BUSB_DO_3 | D
J2.112 | J2_112_V13 |  |  |  | TDC2_CS_DAC | D | J4.112 | D2.5V
J2.113 | J2_113_AA12_L33N |  |  |  | TDC1_SSTIN_N | D | J4.113 | J4_113_B25 |  |  |  | BUSB_DO_2 | D
J2.114 | J2_114_Y12_L33P |  |  |  | TDC1_SSTIN_P | D | J4.114 | J4_114_A25 |  |  |  | BUSB_DO_1 | D
J2.115 | D2.5V |  |  |  |  |  | J4.115 | J4_115_B24 |  |  |  | BUSB_CLR | D
J2.116 | J2_116_V11 |  |  |  | TDC1_CS_DAC | D | J4.116 | GND
J2.117 | J2_117_AD5_L61N |  |  |  | TDC2_WL_CLK_N | D | J4.117 | GND
J2.118 | J2_118_AC5_L61P |  |  |  | TDC2_WL_CLK_P | D | J4.118 | GND
J2.119 | GND |  |  |  |  |  | J4.119 | GND
J2.120 | GND |  |  |  |  |  | J4.120 | GND

Sheet: SCRODrevA3-TXMBrevA
SCRODrevA3 | TX 9U M.B_revA. – D.C.
D3.3V
D3.3V
D3.3V
D3.3V
D3.3V
J1_006_P1 | TDC3_SHOUT
J1_007_R1 | TDC1_SSTIN_N
J1_008_R2 | TDC1_SSTIN_P
GND
J1_010_T1 | TDC3_SAMPLESEL_ANY
J1_011_U1 | TDC3_WL_CLK_N
J1_012_U2 | TDC3_WL_CLK_P
D3.3V
J1_014_V1 | TDC3_SR_CLOCK
J1_015_W1 | TDC3_SSTIN_N
J1_016_W2 | TDC3_SSTIN_P
GND | `
J1_018_Y1 | TDC3_DONE
J1_019_AA1 | TDC4_WL_CLK_N
J1_020_AA2 | TDC4_WL_CLK_P
D3.3V
J1_022_AB1 | TDC3_MON_TIMING
J1_023_AC1 | TDC4_SSTIN_N
J1_024_AC2 | TDC4_SSTIN_P
GND
J1_026_AD1 | TDC3_PCLK
J1_027_AE1 | TDC5_WL_CLK_N
J1_028_AE2 | TDC5_WL_CLK_P
D3.3V
J1_030_D3 | TDC3_SIN
J1_031_E4 | TDC3_SCLK
J1_032_G3 | TDC3_WR1_ENA
GND
J1_034_H3 | TDC3_WR2_ENA
J1_035_J3 | TDC4_TRG_1
J1_036_J5 | TDC4_TRG_2
D3.3V
J1_038_K5 | TDC4_TRG_3
J1_039_L4 | TDC4_TRG_4
J1_040_M4 | TDC4_TRG_5
GND
J1_042_N4 | TDC4_PCLK
J1_043_P3 | TDC4_SIN
J1_044_R3 | TDC4_SCLK
D3.3V
J1_046_R5 | TDC4_SHOUT
J1_047_T4 | TDC4_SAMPLESEL_ANY
J1_048_U4 | TDC4_DONE
GND
J1_050_V3 | TDC4_MON_TIMING
J1_051_V5 | TDC5_SSTIN_P
J1_052_W5 | TDC5_SSTIN_N
D3.3V
J1_054_Y5 | TDC4_SR_CLOCK
J1_055_AA4 | TDC4_WR1_ENA
J1_056_AB4 | TDC4_WR2_ENA
GND
J1_058_AC3 | TDC5_TRG_1
J1_059_AD3 | TDC5_TRG_2
NC
NC
J1_062_AC4 | TDC2_WL_CLK_N
J1_063_AB5 | TDC2_WL_CLK_P
D3.3V
J1_065_AB3 | TDC2_TRG_1
J1_066_AA3 | TDC2_TRG_2
J1_067_Y3 | TDC2_TRG_3
GND
J1_069_W3 | TDC2_SSTIN_N
J1_070_V4 | TDC2_SSTIN_P
J1_071_U5 | TDC2_TRG_4
D3.3V
J1_073_U3 | TDC2_TRG_5
J1_074_T3 | TDC2_SHOUT
J1_075_R4 | TDC2_SIN
GND
J1_077_P5 | TDC2_SCLK
J1_078_N5 | TDC2_PCLK
J1_079_N3 | TDC2_MON_TIMING
D3.3V
J1_081_M3 | TDC2_DONE
J1_082_L3 | TDC2_SR_CLOCK
J1_083_K3 | TDC2_SAMPLESEL_ANY
GND
J1_085_J4 | TDC2_WR1_ENA
J1_086_H5 | TDC2_WR2_ENA
J1_087_G4 | TDC1_TRG_1
D3.3V
J1_089_F3 | TDC1_TRG_2
J1_090_E3 | TDC1_TRG_3
J1_091_N2 | TDC1_WL_CLK_P
GND
J1_093_N1 | TDC1_WL_CLK_N
J1_094_M1 | TDC1_TRG_4
J1_095_L2 | TDC1_TRG_5
D3.3V
J1_097_L1 | TDC1_SIN
J1_098_K1 | TDC1_PCLK
J1_099_J2_SCL | TDC1_SHOUT
GND
J1_101_J1 | TDC1_SCLK
J1_102_H1 | TDC1_SAMPLESEL_ANY
J1_103_G2 | TDC1_SR_CLOCK
D3.3V
J1_105_G1 | TDC1_DONE
J1_106_B1 | TDC1_MON_TIMING
J1_107_E2 | TDC1_WR1_ENA
GND
J1_109_B2 | TDC1_WR2_ENA
J1_110_D1 | TDC3_TRG_1
J1_111_C2 | TDC3_TRG_2
D3.3V
J1_113_C1 | TDC3_TRG_3
J1_114_E1 | TDC3_TRG_4
J1_115_F1 | TDC3_TRG_5
GND
GND
GND
GND
GND
D2.5V
D2.5V
J2_003_AD4 | BUSA_DO_1
J2_004_W8 | BUSA_DO_2
J2_005_AC5 | BUSA_DO_3
GND
J2_007_R10 | BUSA_DO_4
J2_008_AF4 | BUSA_DO_5
J2_009_AF5 | BUSA_DO_6
D2.5V
J2_011_AE5 | BUSA_DO_7
J2_012_AF6 | BUSA_DO_8
J2_013_AD6 | BUSA_DO_9
GND
J2_015_AA10 | BUSA_DO_10
J2_016_AA9 | BUSA_DO_11
J2_017_V11 | BUSA_DO_12
D1.2V
J2_019_Y11 | BUSA_DO_13
J2_020_AB13 | BUSA_DO_14
J2_021_V12 | BUSA_DO_15
GND
J2_023_AA12 | BUSA_DO_16
J2_024_AA6 | BUSB_DO_1
J2_025_P10 | BUSB_DO_2
D1.2V
J2_027_M10_SDA | BUSB_DO_3
J2_028_L10_SCL | BUSB_DO_4
J2_029_K10_SDA | BUSB_DO_5
GND
J2_031_AA15 | BUSB_DO_6
J2_032_V14 | BUSB_DO_7
J2_033_Y15 | BUSB_DO_8
D1.2V
J2_035_AA18 | BUSB_DO_9
J2_035_W16 | BUSB_DO_10
J2_037_AA19 | BUSB_DO_11
GND
J2_039_U15 | BUSB_DO_12
J2_040_Y17 | BUSB_DO_13
J2_041_AA21 | BUSB_DO_14
D1.8V
J2_043_W17 | BUSB_DO_15
J2_044_AF22 | BUSB_DO_16
J2_045_B24 | BUSB_CLR
GND
J2_047_AB22 | BUSB_WR_ADDRCLR
J2_048_W20 | BUSB_RAMP
J2_049_Y21 | BUSB_RD_ENA
NC
GND
J2_052_AA22 | BUSB_RD_RS_S0
J2_053_Y20 | BUSB_RD_RS_S1
J2_054_AC22 | BUSB_RD_RS_S2
D1.8V
J2_056_V18/D1/MISO2 | TDC10_MON_TIMING
J2_057_W19/D2/MISO3 | BUS_REGCLR
J2_058_W18 | BUSB_RD_CS_S0
GND
J2_060_AB21 | BUSB_RD_CS_S1
J2_061_AA17 | BUSB_RD_CS_S2
J2_062_V16 | BUSB_RD_CS_S3
D1.2V
J2_064_AB19 | BUSB_RD_CS_S4
J2_065_Y16 | BUSB_RD_CS_S5
J2_066_AB17 | BUSB_SAMPLESEL_S1
GND
J2_068_AA16 | BUSB_SAMPLESEL_S2
J2_069_V15 | BUSB_SAMPLESEL_S3
J2_070_AB15 | BUSB_SAMPLESEL_S4
D1.2V
J2_072_P17 | BUSB_SAMPLESEL_S5
J2_073_W14 | BUSB_SR_CLEAR
J2_074_U13 | BUSB_SR_SEL
GND
J2_076_V13 | BUSA_SAMPLESEL_S1
J2_077_Y12 | BUSA_SAMPLESEL_S2
J2_078_Y13 | BUSA_SAMPLESEL_S3
D1.2V
J2_080_W12 | BUSA_SAMPLESEL_S4
J2_081_AA13 | BUSA_SAMPLESEL_S5
J2_082_AA11 | BUSA_RD_ENA
GND
J2_084_V10 | BUSA_RD_RS_S0
J2_085_AB9 | BUSA_RD_RS_S1
J2_086_AB11 | BUSA_RD_RS_S2
D1.2V
J2_088_W10 | BUSA_RD_CS_S0
J2_089_W9 | BUSA_RD_CS_S1
J2_090_Y9 | BUSA_RD_CS_S2
GND
J2_092_AA8 | BUSA_RD_CS_S3
J2_093_AB7 | BUSA_RD_CS_S4
J2_094_AC6 | BUSA_RD_CS_S5
D2.5V
J2_096_AD5 | BUSA_WR_ADDRCLR
J2_097_W7 | BUSA_RAMP
J2_098_AA7 | BUSA_CLR
GND
GND
D2.5V
D2.5V
J3_003_H6 | BUS_RAM_RS_A10
J3_004_K6 | BUS_RAM_RS_A9
J3_005_K8 | BUS_RAM_RS_A8
GND
J3_007_L7 | BUS_RAM_RS_A7
J3_008_M6 | BUS_RAM_RS_A6
J3_009_N6 | BUS_RAM_RS_A5
D2.5V
J3_011_N8 | BUS_RAM_RS_A4
J3_012_P8 | BUS_RAM_RS_A3
J3_013_R7 | BUS_RAM_RS_A2
GND
J3_015_T6 | BUS_RAM_RS_A1
J3_016_U7 | BUS_RAM_RS_A0
J3_017_V6 | RAM1_WE
D2.5V
J3_019_Y6 | BUSA_SR_CLEAR
J3_020_K9 | BUSA_SR_SEL
J3_021_H13_SCL0 | SCL_MON
GND
J3_023_F14_SDA0 | SDA_MON
J3_024_E14_SCL1 | EX_TRIGGER1
J3_025_K14_SDA1 | EX_TRIGGER2
D2.5V
J3_027_H14_SCL2 | BUSA_SCK_DAC
J3_028_J15_SDA2 | BUSA_DIN_DAC
J3_029_H15_SCL3 | BUSB_SCK_DAC
GND
J3_031_J16_SDA3 | BUSB_DIN_DAC
J3_032_V20 | TOP_AMUX_S0
J3_033_U19 | TOP_AMUX_S1
D2.5V
J3_035_U21 | TOP_AMUX_S2
J3_036_T20 | TOP_AMUX_S3
J3_037_R20 | TDC_AMUX_S0
GND
J3_039_P19 | TDC_AMUX_S1
J3_040_N19 | TDC_AMUX_S2
J3_041_N21 | TDC_AMUX_S3
D2.5V
J3_043_M21 | RAM1_OE
J3_044_L20 | RAM1_CE1
J3_045_K19 | RAM1_CE2
GND
J3_047_K21 | RAM2_WE
J3_048_H20 | RAM2_OE
J3_049_G20 | RAM2_CE1
D2.5V
GND
J3_052_H21 | RAM2_CE2
J3_053_J20 | TDC10_CS_DAC
J3_054_K20 | TDC9_CS_DAC
D2.5V
J3_056_L21 | TDC8_CS_DAC
J3_057_L19 | TDC7_CS_DAC
J3_058_M19 | TDC6_CS_DAC
GND
J3_060_N20 | TDC5_CS_DAC
J3_061_P21 | TDC4_CS_DAC
J3_062_R21 | TDC3_CS_DAC
D2.5V
J3_064_R19 | TDC2_CS_DAC
J3_065_T19 | TDC1_CS_DAC
J3_066_U20 | TDC10_SHOUT
GND
J3_068_V21 | TDC10_TRG_3
J3_069_K18 | TDC10_TRG_4
J3_070_M18_SCL | TDC10_TRG_5
D2.5V
J3_072_N18_SDA | TDC10_WR1_ENA
J3_073_R18 | TDC10_WR2_ENA
J3_074_U9 | TDC10_SAMPLESEL_ANY
GND
J3_076_T9 | TDC10_PCLK
J3_077_R9 | TDC10_SIN
J3_078_N9 | TDC10_SCLK
D2.5V
J3_080_M9 | TDC10_DONE
J3_081_L9 | TDC10_SR_CLOCK
J3_082_J9 | TDC5_MON_TIMING
GND
J3_084_V7 | TDC5_SAMPLESEL_ANY
J3_085_U8 | TDC5_SR_CLOCK
J3_086_T8 | TDC5_DONE
D2.5V
J3_088_R8 | TDC5_PCLK
J3_089_R6 | TDC5_SIN
J3_090_P6 | TDC5_SCLK
GND
J3_092_N7 | TDC5_SHOUT
J3_093_M8 | TDC5_WR1_ENA
J3_094_L8 | TDC5_WR2_ENA
D2.5V
J3_096_L6 | TDC5_TRG_3
J3_097_K7 | TDC5_TRG_4
J3_098_J7 | TDC5_TRG_5
GND
GND
GND
GND
GND
GND
GND
J4_006_A25 | TDC8_TRG_2
J4_007_B26 | TDC8_TRG_3
J4_008_B25 | TDC8_TRG_4
D2.5V
J4_010_C26 | TDC8_WL_CLK_N
J4_011_C25 | TDC8_WL_CLK_P
J4_012_D26 | TDC8_TRG_5
GND
J4_014_E26 | TDC9_SSTIN_N
J4_015_E25 | TDC9_SSTIN_P
J4_016_F26 | TDC8_SHOUT
D2.5V
J4_018_G26 | TDC9_WL_CLK_N
J4_019_G25 | TDC9_WL_CLK_P
J4_020_H26 | TDC8_SAMPLESEL_ANY
GND
J4_022_J26 | TDC10_SSTIN_N
J4_023_J25 | TDC10_SSTIN_P
J4_024_K26 | TDC8_DONE
D2.5V
J4_026_L26 | TDC10_WL_CLK_N
J4_027_L25 | TDC10_WL_CLK_P
J4_028_M26 | TDC8_SR_CLOCK
GND
J4_030_N26 | TDC8_PCLK
J4_031_N25 | TDC8_SIN
J4_032_D23 | TDC8_SCLK
D2.5V
J4_034_E23 | TDC8_WR1_ENA
J4_035_F23 | TDC8_WR2_ENA
J4_036_G24 | TDC8_MON_TIMING
GND
J4_038_H24 | TDC9_TRG_1
J4_039_J24 | TDC9_TRG_2
J4_040_J22 | TDC9_TRG_3
D2.5V
J4_042_K22 | TDC9_TRG_4
NC
J4_044_M24 | TDC9_TRG_5
GND
J4_046_N24 | TDC9_SHOUT
J4_047_N22 | TDC9_WR1_ENA
J4_048_P22 | TDC9_WR2_ENA
D2.5V
J4_050_R23 | TDC9_MON_TIMING
J4_051_T23 | TDC9_SR_CLOCK
J4_052_N17 | TDC9_SAMPLESEL_ANY
GND
J4_054_U22 | TDC9_PCLK
J4_055_V23 | TDC9_SIN
J4_056_Y24 | TDC9_SCLK
D2.5V
J4_058_AA23 | TDC9_DONE
J4_059_AC24 | TDC10_TRG_1
J4_060_AD24 | TDC10_TRG_2
J4_061_AC23 | TDC6_TRG_1
J4_062_AB24 | TDC6_TRG_2
J4_063_AA24 | TDC6_TRG_3
GND
J4_065_W24 | TDC6_TRG_4
J4_066_V24 | TDC6_TRG_5
NC
D2.5V
J4_069_T22 | TDC6_SHOUT
J4_070_T24 | TDC6_WR1_ENA
J4_071_R24 | TDC6_WR2_ENA
GND
J4_073_P24 | TDC6_SCLK
J4_074_N23 | TDC6_SIN
J4_075_M23 | TDC6_PCLK
D2.5V
J4_077_L23 | TDC6_SSTIN_P
J4_078_L24 | TDC6_SSTIN_N
J4_079_K24 | TDC6_MON_TIMING
GND
J4_081_J23 | TDC6_SR_CLOCK
J4_082_H22 | TDC6_SAMPLESEL_ANY
J4_083_G23 | TDC6_DONE
D2.5V
J4_085_F22 | TDC7_TRG_1
J4_086_F24 | TDC7_TRG_2
J4_087_E24 | TDC7_TRG_3
GND
J4_089_D24 | TDC7_TRG_4
J4_090_C24 | TDC7_TRG_5
J4_091_AF23/MOSI/MISO0 | TDC7_SHOUT
D2.5V
J4_093_AE25 | TDC6_WL_CLK_P
J4_094_AE26 | TDC6_WL_CLK_N
J4_095_AD26 | TDC7_SR_CLOCK
GND
J4_097_AC26 | TDC7_SSTIN_N
J4_098_AC25 | TDC7_SSTIN_P
J4_099_AB26 | TDC7_SAMPLESEL_ANY
D2.5V
J4_101_AA26 | TDC7_WL_CLK_N
J4_102_AA25 | TDC7_WL_CLK_P
J4_103_Y26 | TDC7_DONE
GND
J4_105_W25 | TDC8_SSTIN_P
J4_106_W26 | TDC8_SSTIN_N
J4_107_V26 | TDC7_MON_TIMING
D2.5V
J4_109_U24 | TDC7_PCLK
J4_110_U23 | TDC7_SIN
J4_111_T26 | TDC7_SCLK
GND
J4_113_R25 | TDC7_WR1_ENA
J4_114_R26 | TDC7_WR2_ENA
J4_115_P26 | TDC8_TRG_1
D2.5V
D2.5V
D2.5V
D2.5V
D2.5V

Sheet: interconnect
TX 9U M.B_revA. – D.C. | ActualRevA4PinsConnected | MARK | notes
TDC3_SHOUT | J1_006_D1 | D
TDC1_SSTIN_N | J2_015_AC6_L53N | D
TDC1_SSTIN_P | J2_016_AB7_L53P | D
TDC3_SAMPLESEL_ANY | J1_010_F1 | D
TDC3_WL_CLK_N | J2_013_AF6_L49N | D
TDC3_WL_CLK_P | J2_012_AD6_L49P | D
TDC3_SR_CLOCK | J1_014_H1 | D
TDC3_SSTIN_N | J2_109_Y13_L34N | D
TDC3_SSTIN_P | J2_110_W14_L34P | D
`
TDC3_DONE | J1_018_K1 | D
TDC4_WL_CLK_N | J2_008_AF5_L51N | D
TDC4_WL_CLK_P | J2_007_AE5_L51P | D
TDC3_MON_TIMING | J1_022_M1 | D
TDC4_SSTIN_N | J2_113_AA12_L33N | D
TDC4_SSTIN_P | J2_114_Y12_L33P | D
TDC3_PCLK | J1_026_R5 | D
TDC5_WL_CLK_N | J2_005_AF4_L63N | D
TDC5_WL_CLK_P | J2_004_AD4_L63P | D
TDC3_SIN | J1_030_U9 | D
TDC3_SCLK | J1_031_U8 | D
TDC3_WR1_ENA | J1_032_U5 | D
TDC3_WR2_ENA | J1_034_V7 | D
TDC4_TRG_1 | J1_035_V6 | D
TDC4_TRG_2 | J1_036_V4 | D
TDC4_TRG_3 | J1_038_W5 | D
TDC4_TRG_4 | J1_039_P1 | D
TDC4_TRG_5 | J1_040_R1 | D
TDC4_PCLK | J1_042_R2 | D
TDC4_SIN | J1_043_U1 | D
TDC4_SCLK | J1_044_U2 | D
TDC4_SHOUT | J1_046_V1 | D
TDC4_SAMPLESEL_ANY | J1_047_W1 | D
TDC4_DONE | J1_048_W2 | D
TDC4_MON_TIMING | J1_050_Y1 | D
TDC5_SSTIN_P | J2_118_AC5_L61P | D
TDC5_SSTIN_N | J2_117_AD5_L61N | D
TDC4_SR_CLOCK | J1_054_AB1 | D
TDC4_WR1_ENA | J1_055_AC1 | D
TDC4_WR2_ENA | J1_056_AC2 | D
TDC5_TRG_1 | J1_058_AD1 | D
TDC5_TRG_2 | J1_059_AE1 | D
 | J1_060_AE2
TDC2_WL_CLK_N | J1_061_AB11_L48N | D
TDC2_WL_CLK_P | J1_062_AA10_L48P | D
TDC2_TRG_1 | J1_069_AD3 | D
TDC2_TRG_2 | J1_070_AC4 | D
TDC2_TRG_3 | J1_091_T4 | D
TDC2_SSTIN_N | J1_065_AA6_L64N | D
TDC2_SSTIN_P | J1_063_AA7_L64P | D
TDC2_TRG_4 | J1_071_AC3 | D
TDC2_TRG_5 | J1_073_AB5 | D
TDC2_SHOUT | J1_074_AB4 | D
TDC2_SIN | J1_075_AB3 | D
TDC2_SCLK | J1_077_AA4 | D
TDC2_PCLK | J1_078_AA3 | D
TDC2_MON_TIMING | J1_079_Y6 | D
TDC2_DONE | J1_081_Y5 | D
TDC2_SR_CLOCK | J1_082_Y3 | D
TDC2_SAMPLESEL_ANY | J1_083_W3 | D
TDC2_WR1_ENA | J1_085_V3 | D
TDC2_WR2_ENA | J1_086_V5 | D
TDC1_TRG_1 | J1_087_U3 | D
TDC1_TRG_2 | J1_089_U4 | D
TDC1_TRG_3 | J1_090_U7 | D
TDC1_WL_CLK_P | J1_066_W8_L62P | D
TDC1_WL_CLK_N | J1_067_W7_L62N | D
TDC1_TRG_4 | J1_094_R3 | D
TDC1_TRG_5 | J1_095_R4 | D
TDC1_SIN | J1_097_R6 | D
TDC1_PCLK | J1_098_R7 | D
TDC1_SHOUT | J1_099_R8 | D
TDC1_SCLK | J1_101_R9 | D
TDC1_SAMPLESEL_ANY | J1_102_R10 | D
TDC1_SR_CLOCK | J1_103_P3 | D
TDC1_DONE | J1_105_P5 | D
TDC1_MON_TIMING | J1_106_P6 | D
TDC1_WR1_ENA | J1_107_P8 | D
TDC1_WR2_ENA | J1_109_P10 | D
TDC3_TRG_1 | J1_110_N4 | D
TDC3_TRG_2 | J1_111_N5 | D
TDC3_TRG_3 | J1_113_N6 | D
TDC3_TRG_4 | J1_114_N7 | D
TDC3_TRG_5 | J1_115_N8 | D
BUSA_DO_1 | J3_011_M3 | D
BUSA_DO_2 | J3_012_K3 | D
BUSA_DO_3 | J3_013_H3 | D
BUSA_DO_4 | J3_015_F3 | D
BUSA_DO_5 | J3_016_D3 | D
BUSA_DO_6 | J3_017_L4 | D
BUSA_DO_7 | J3_019_G4 | D
BUSA_DO_8 | J3_020_K5 | D
BUSA_DO_9 | J3_021_H5 | D
BUSA_DO_10 | J3_023_L6 | D
BUSA_DO_11 | J3_024_H6 | D
BUSA_DO_12 | J3_025_K7 | D
BUSA_DO_13 | J3_027_M8 | D
BUSA_DO_14 | J3_028_K8 | D
BUSA_DO_15 | J3_032_L10 | D
BUSA_DO_16 | J1_002_B1 | D
BUSB_DO_1 | J1_003_C2 | D
BUSB_DO_2 | J1_004_C1 | D
BUSB_DO_3 | J1_007_E2 | D
BUSB_DO_4 | J1_008_E1 | D
BUSB_DO_5 | J1_011_G2 | D
BUSB_DO_6 | J1_012_G1 | D
BUSB_DO_7 | J1_015_J2 | D
BUSB_DO_8 | J1_016_J1 | D
BUSB_DO_9 | J1_019_L2 | D
BUSB_DO_10 | J1_020_L1 | D
BUSB_DO_11 | J1_023_N2 | D
BUSB_DO_12 | J1_024_N1 | D
BUSB_DO_13 | J1_027_T9 | D
BUSB_DO_14 | J1_028_T8 | D
BUSB_DO_15 | J2_059_R23 | D
BUSB_DO_16 | J2_060_P24 | D
BUSB_CLR | J4_010_E24 | D
BUSB_WR_ADDRCLR | J4_011_E23 | D
BUSB_RAMP | J4_014_F23 | D
BUSB_RD_ENA | J4_015_F22 | D
BUSB_RD_RS_S0 | J2_028_V12_L35P | D
BUSB_RD_RS_S1 | J2_027_T19 | D
BUSB_RD_RS_S2 | J2_025_N18 | D
TDC10_MON_TIMING | J2_024_Y9_L52P | D
BUS_REGCLR | J2_023_AA8_L52N | D
BUSB_RD_CS_S0 | J2_021_W10_L50P | D
BUSB_RD_CS_S1 | J2_020_W9_L50N | D
BUSB_RD_CS_S2 | J2_019_AA17_L16N | D
BUSB_RD_CS_S3 | J1_093_T6 | D
BUSB_RD_CS_S4 | J1_117_N9 | D
BUSB_RD_CS_S5 | J1_118_M9 | D
BUSB_SAMPLESEL_S1 | J1_119_M10 | D
BUSB_SAMPLESEL_S2 | J4_093_L26 | D
BUSB_SAMPLESEL_S3 | J4_094_L25 | D
BUSB_SAMPLESEL_S4 | J4_097_J26 | D
BUSB_SAMPLESEL_S5 | J4_098_J25 | D
BUSB_SR_CLEAR | J4_101_G26 | D
BUSB_SR_SEL | J4_102_G25 | D
BUSA_SAMPLESEL_S1 | J4_105_E26 | D
BUSA_SAMPLESEL_S2 | J4_106_E25 | D
BUSA_SAMPLESEL_S3 | J3_090_J9 | D
BUSA_SAMPLESEL_S4 | J3_092_B2 | D
BUSA_SAMPLESEL_S5 | J3_093_L8 | D
BUSA_RD_ENA | J3_094_J7 | D
BUSA_RD_RS_S0 | J3_096_L7 | D
BUSA_RD_RS_S1 | J3_097_K6 | D
BUSA_RD_RS_S2 | J3_098_M6 | D
BUSA_RD_CS_S0 | J3_100_J5 | D
BUSA_RD_CS_S1 | J3_101_E4 | D
BUSA_RD_CS_S2 | J3_102_J4 | D
BUSA_RD_CS_S3 | J3_104_M4 | D
BUSA_RD_CS_S4 | J3_105_E3 | D
BUSA_RD_CS_S5 | J3_106_G3 | D
BUSA_WR_ADDRCLR | J3_108_J3 | D
BUSA_RAMP | J3_109_L3 | D
BUSA_CLR | J3_110_N3 | D
BUS_RAM_RS_A10 | J2_003_V10 | D | LED0 overloaded
BUS_RAM_RS_A9 | J2_009_U13 | D | LED1 overloaded
BUS_RAM_RS_A8 | NC
BUS_RAM_RS_A7 | NC
BUS_RAM_RS_A6 | NC
BUS_RAM_RS_A5 | NC
BUS_RAM_RS_A4 | NC
BUS_RAM_RS_A3 | NC
BUS_RAM_RS_A2 | NC
BUS_RAM_RS_A1 | NC
BUS_RAM_RS_A0 | NC
RAM1_WE | NC
BUSA_SR_CLEAR | J2_029_W12_L35N | D
BUSA_SR_SEL | J2_033_P19 | D
SCL_MON | J3_088_A2 | D | 3.3V BANK
SDA_MON | J3_086_A3 | D | 3.3V BANK
EX_TRIGGER1 | J2_035_V20 | D | 2.5V BANK
EX_TRIGGER2 | J2_041_V18/D1/MISO2 |  | 2.5V BANK
BUSA_SCK_DAC | J3_085_A4 | D | 3.3V BANK
BUSA_DIN_DAC | J3_084_D5 | D | 3.3V BANK
BUSB_SCK_DAC | J3_082_F5 | D | 3.3V BANK
BUSB_DIN_DAC | J3_089_K10 | D | 2.5V BANK
TOP_AMUX_S0 | J2_043_W19/D2/MISO3 | D
TOP_AMUX_S1 | J2_049_AF23/MOSI/MISO0 | D
TOP_AMUX_S2 | J2_051_N20 | D
TOP_AMUX_S3 | J2_052_U21 | D
TDC_AMUX_S0 | J2_053_P21 | D
TDC_AMUX_S1 | J2_055_U22 | D
TDC_AMUX_S2 | J2_056_P22 | D
TDC_AMUX_S3 | J2_057_N23 | D
RAM1_OE | J2_011_U15 | D | LED2 overloaded with the RAM on MB RevA
RAM1_CE1 | J2_017_Y17_L16P | D | LED3
RAM1_CE2 | J1_051_AA1 | D | LED4
RAM2_WE | J1_052_AA2 | D | LED5
RAM2_OE | J3_029_L9 | D | LED6
RAM2_CE1 | J3_031_K9 | D | LED7
RAM2_CE2 | J4_077_Y26 | D | LED8
TDC10_CS_DAC | J4_078_W26 | D
TDC9_CS_DAC | J4_027_J23 | D
TDC8_CS_DAC | J4_026_J24 | D
TDC7_CS_DAC | J4_023_H21 | D
TDC6_CS_DAC | J4_022_H22 | D
TDC5_CS_DAC | J4_020_H24 | D
TDC4_CS_DAC | J4_018_G23 | D
TDC3_CS_DAC | J2_061_AA23 | D
TDC2_CS_DAC | J2_062_T23 | D
TDC1_CS_DAC | J2_064_N22 | D
TDC10_SHOUT | J2_065_T22 | D
TDC10_TRG_3 | J2_066_N21 | D
TDC10_TRG_4 | J2_068_R21 | D
TDC10_TRG_5 | J2_069_V21 | D
TDC10_WR1_ENA | J2_070_R20 | D
TDC10_WR2_ENA | J2_074_AF22 | D
TDC10_SAMPLESEL_ANY | J2_076_U20 | D
TDC10_PCLK | J2_082_T20 | D
TDC10_SIN | J2_084_N19 | D
TDC10_SCLK | J2_090_R19 | D
TDC10_DONE | J2_092_U19 | D
TDC10_SR_CLOCK | J2_093_AA11_L41N | D
TDC5_MON_TIMING | J2_094_Y11_L41P | D
TDC5_SAMPLESEL_ANY | J2_096_R18 | D
TDC5_SR_CLOCK | J2_097_P17 | D
TDC5_DONE | J2_098_N17 | D
TDC5_PCLK | J2_100_AA22 | D
TDC5_SIN | J2_101_AB9_L47N | D
TDC5_SCLK | J2_102_AA9_L47P | D
TDC5_SHOUT | J2_104_Y21 | D
TDC5_WR1_ENA | J2_105_AA16_L24N | D
TDC5_WR2_ENA | J2_106_Y15_L24P | D
TDC5_TRG_3 | J2_108_V16 | D
TDC5_TRG_4 | J2_112_V13 | D
TDC5_TRG_5 | J2_116_V11 | D
TDC8_TRG_2 | J4_006_C24 | D
TDC8_TRG_3 | J4_007_D24 | D
TDC8_TRG_4 | J4_008_D23 | D
TDC8_WL_CLK_N | J2_032_AA13_L36N | D
TDC8_WL_CLK_P | J2_031_AB13_L36P | D
TDC8_TRG_5 | J4_012_F24 | D
TDC9_SSTIN_N | J2_036_Y16_L19N | D
TDC9_SSTIN_P | J2_037_W16_L19P | D
TDC8_SHOUT | J4_016_G24 | D
TDC9_WL_CLK_N | J2_040_W18_L14N | D
TDC9_WL_CLK_P | J2_039_W17_L14P | D
TDC8_SAMPLESEL_ANY | J4_019_G20 | D
TDC10_SSTIN_N | J2_044_Y20_L4N | D
TDC10_SSTIN_P | J2_045_W20_L4P | D
TDC8_DONE | J4_024_H20 | D
TDC10_WL_CLK_N | J2_047_AB21_L15N | D
TDC10_WL_CLK_P | J2_048_AA21_L15P | D
TDC8_SR_CLOCK | J4_028_J22 | D
TDC8_PCLK | J4_030_J20 | D
TDC8_SIN | J4_031_K24 | D
TDC8_SCLK | J4_032_K22 | D
TDC8_WR1_ENA | J4_034_K20 | D
TDC8_WR2_ENA | J4_035_K21 | D
TDC8_MON_TIMING | J4_036_K19 | D
TDC9_TRG_1 | J4_038_K18 | D
TDC9_TRG_2 | J4_039_L21 | D
TDC9_TRG_3 | J4_040_L20 | D
TDC9_TRG_4 | J4_042_L19 | D
 | J4_043_M24
TDC9_TRG_5 | J4_044_M23 | D
TDC9_SHOUT | J4_046_M21 | D
TDC9_WR1_ENA | J4_047_M19 | D
TDC9_WR2_ENA | J4_048_M18 | D
TDC9_MON_TIMING | J4_050_L24 | D
TDC9_SR_CLOCK | J4_051_L23 | D
TDC9_SAMPLESEL_ANY | J4_052_N24 | D
TDC9_PCLK | J4_054_T24 | D
TDC9_SIN | J4_055_V24 | D
TDC9_SCLK | J4_056_Y24 | D
TDC9_DONE | J4_058_AA24 | D
TDC10_TRG_1 | J4_059_AB24 | D
TDC10_TRG_2 | J4_060_AC24 | D
TDC6_TRG_1 | J4_061_V23_GCLK+ | D
TDC6_TRG_2 | J4_062_W24_GCLK- | D
TDC6_TRG_3 | J4_063_AC23 | D
TDC6_TRG_4 | J4_065_AD24 | D
TDC6_TRG_5 | J4_066_AE25 | D
 | J4_067_AE26
TDC6_SHOUT | J4_069_AD26 | D
TDC6_WR1_ENA | J4_070_AC25 | D
TDC6_WR2_ENA | J4_071_AC26 | D
TDC6_SCLK | J4_073_AB26 | D
TDC6_SIN | J4_074_AA26 | D
TDC6_PCLK | J4_075_AA25 | D
TDC6_SSTIN_P | J2_072_AB22_L5P | D
TDC6_SSTIN_N | J2_073_AC22_L5N | D
TDC6_MON_TIMING | J4_079_W25 | D
TDC6_SR_CLOCK | J4_081_V26 | D
TDC6_SAMPLESEL_ANY | J4_082_U26_GCLK- | D
TDC6_DONE | J4_083_U25_GCLK+ | D
TDC7_TRG_1 | J4_085_T26 | D
TDC7_TRG_2 | J4_086_R24 | D
TDC7_TRG_3 | J4_087_P26 | D
TDC7_TRG_4 | J4_089_N26 | D
TDC7_TRG_5 | J4_090_N25 | D
TDC7_SHOUT | J4_091_M26 | D
TDC6_WL_CLK_P | J2_077_AA19_L18P | D
TDC6_WL_CLK_N | J2_078_AB19_L18N | D
TDC7_SR_CLOCK | J4_095_K26 | D
TDC7_SSTIN_N | J2_081_AB17_L20N | D
TDC7_SSTIN_P | J2_080_AA18_L20P | D
TDC7_SAMPLESEL_ANY | J4_099_H26 | D
TDC7_WL_CLK_N | J2_086_AB15_L28N | D
TDC7_WL_CLK_P | J2_085_AA15_L28P | D
TDC7_DONE | J4_103_F26 | D
TDC8_SSTIN_P | J2_089_V14_L26P | D
TDC8_SSTIN_N | J2_088_V15_L26N | D
TDC7_MON_TIMING | J4_107_D26 | D
TDC7_PCLK | J4_109_C26 | D
TDC7_SIN | J4_110_C25 | D
TDC7_SCLK | J4_111_B26 | D
TDC7_WR1_ENA | J4_113_B25 | D
TDC7_WR2_ENA | J4_114_A25 | D
TDC8_TRG_1 | J4_115_B24 | D
