mzandrew/idlab-scrod/mechanical-designs/board-stack/fDIRC/existing-support-structure/G10-frame.SLDASM

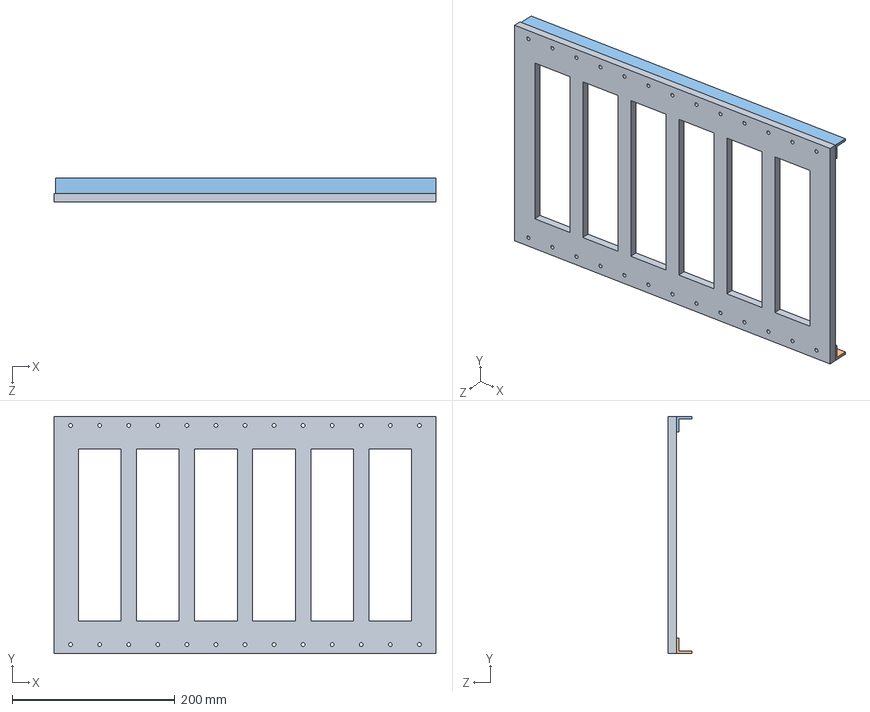
[picture p61: CAD file, 2012-07-12]
mechanical-designs/board-stack/fDIRC/existing-support-structure/G10-frame.SLDASM
469.9 x 292.1 x 29.0 mm
G10-frame
angle-aluminum-with-holes.bottom
angle-aluminum-with-holes.top
