mzandrew/idlab-scrod/mechanical-designs/board-stack/fDIRC/H8500-amp.revB.SLDASM

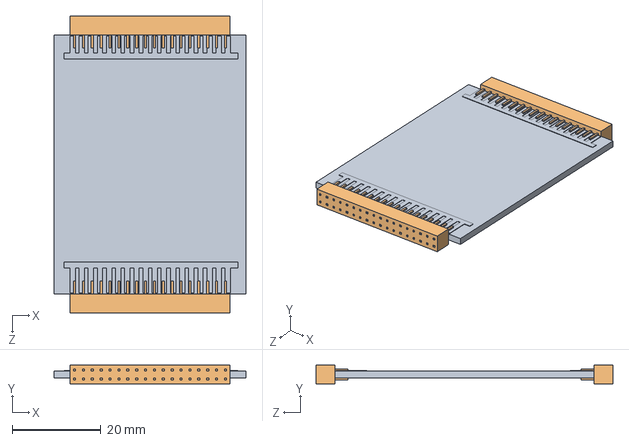
[picture p62: CAD file, 2013-02-14]
mechanical-designs/board-stack/fDIRC/H8500-amp.revB.SLDASM
43.2 x 4.25 x 66.9 mm
H8500-amp.revB
connector.2mm.36-pin.female x 2
