mzandrew/idlab-scrod/mechanical-designs/board-stack/iTOP/contrib/front-board.SLDASM

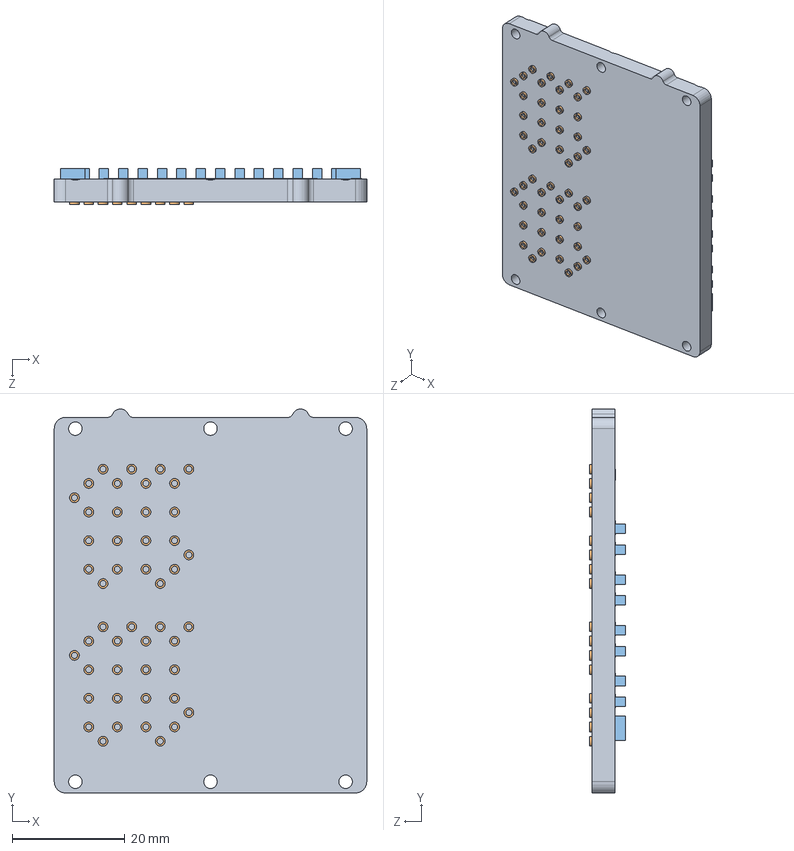
[picture p63: CAD file, 2014-05-03]
mechanical-designs/board-stack/iTOP/contrib/front-board.SLDASM
55.5 x 68.2 x 6.47 mm
front-board
pin-socket.mill-max-8252-32 x 48
1206.capacitor x 32
pogo-pin.millmax-0926-1 x 85
