mzandrew/idlab-scrod/mechanical-designs/board-stack/iTOP/CRT/HV-panel.SLDASM

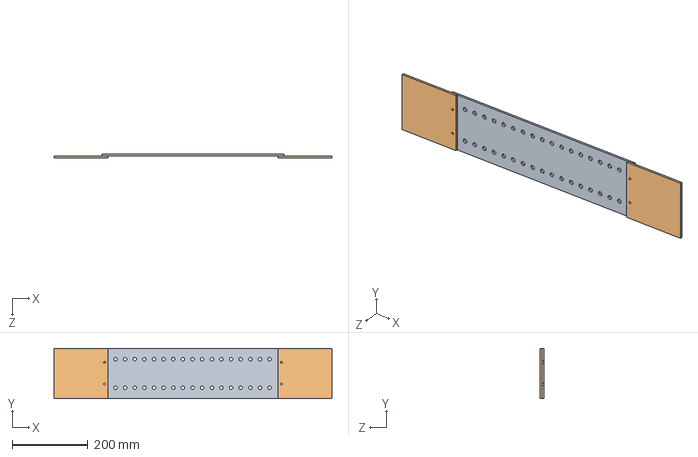
[picture p64: CAD file, 2013-03-19]
mechanical-designs/board-stack/iTOP/CRT/HV-panel.SLDASM
733.4 x 132.2 x 9.53 mm
HV-panel
HV-panel-holder x 2
