mzandrew/idlab-scrod/mechanical-designs/board-stack/iTOP/SCROD-and-carriers.SLDASM

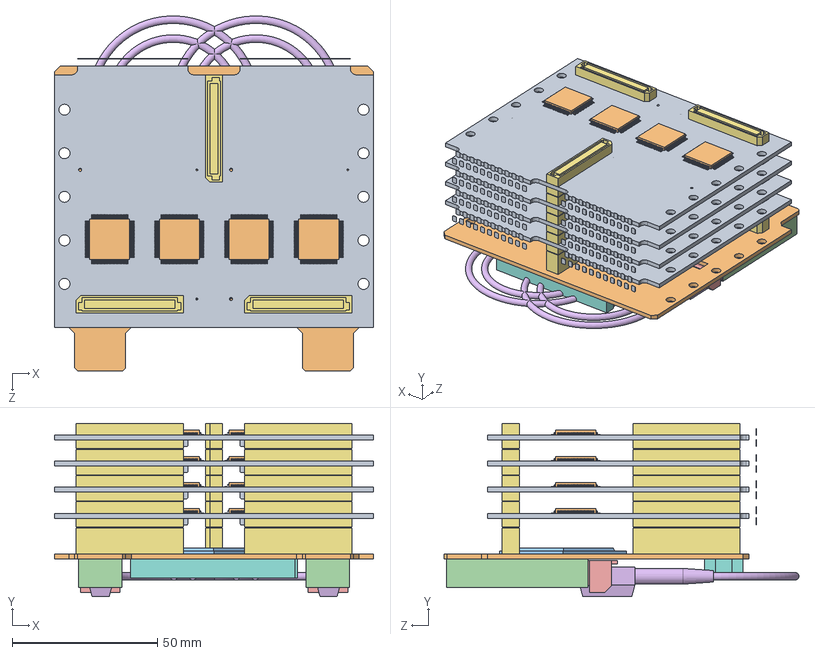
[picture p65: CAD file, 2014-05-03]
mechanical-designs/board-stack/iTOP/SCROD-and-carriers.SLDASM
110.0 x 59.8 x 122.3 mm
SCROD.revB
zynq.900-FFG
fiber-cage.single-wide x 2
fiber-transceiver x 2
fiber-cable-end.LC-duplex x 2
FX8C-board-to-board-interconnects x 15
VITA57-FMC-female
carrier.revE x 4
TQFP-128 x 16
pogo-pin.millmax-0926-1 x 168
