mzandrew/idlab-scrod/mechanical-designs/board-stack/SCROD.revB.SLDASM

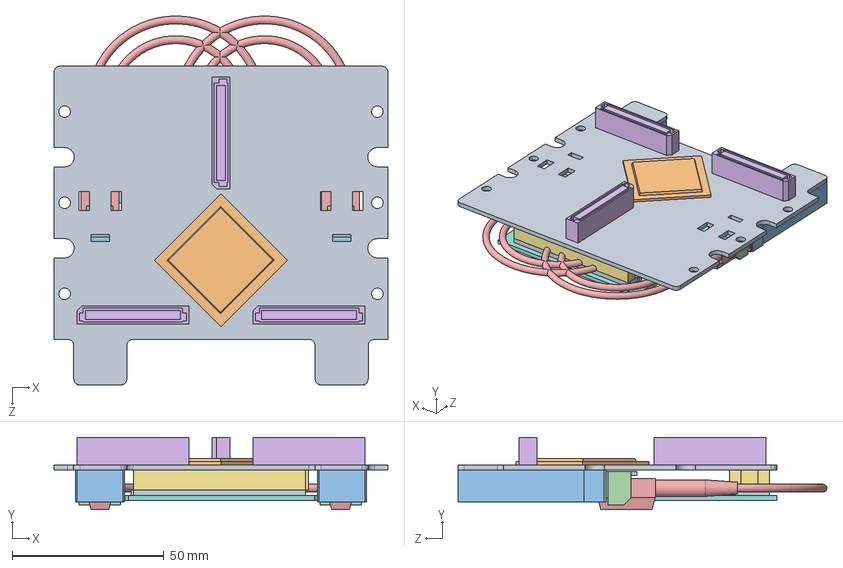
[picture p66: CAD file, 2014-05-03]
mechanical-designs/board-stack/SCROD.revB.SLDASM
110.0 x 23.8 x 121.5 mm
SCROD.revB
zynq.900-FFG
fiber-cage.single-wide x 2
fiber-transceiver x 2
fiber-cable-end.LC-duplex x 2
FX8C-board-to-board-interconnects x 3
VITA57-FMC-female
VITA57-FMC-PCB
VITA57-FMC-male
