mzandrew/idlab-scrod/mechanical-designs/common-components/boxes/FTSW-in-box.SLDASM

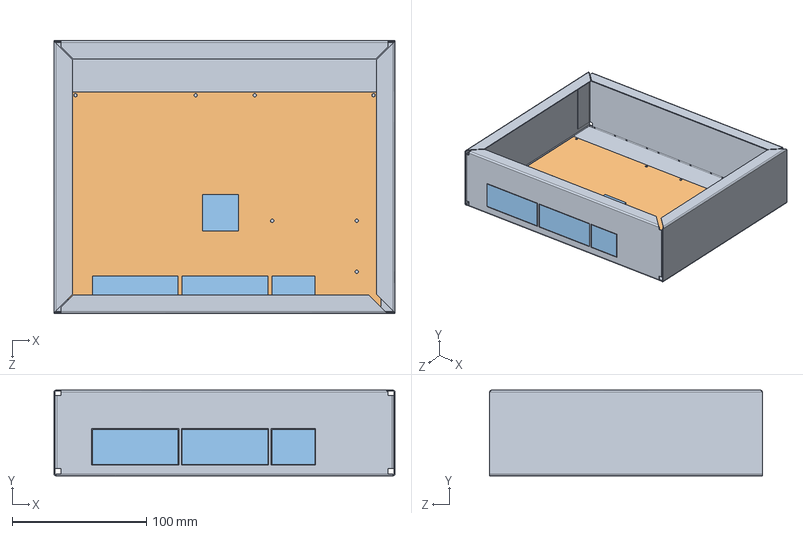
[picture p67: CAD file, 2013-10-08]
mechanical-designs/common-components/boxes/FTSW-in-box.SLDASM
254.0 x 63.9 x 203.2 mm
bud-10x8x2.5-for-FTSW
VME-6U-PCB
VME-6U-PCB.FTSW
