mzandrew/idlab-scrod/mechanical-designs/common-components/VITA57-FMC.SLDASM

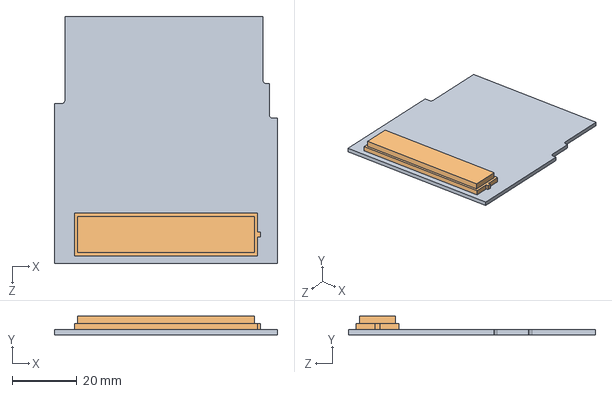
[picture p68: CAD file, 2013-11-13]
mechanical-designs/common-components/VITA57-FMC.SLDASM
69.0 x 5.79 x 76.5 mm
VITA57-FMC-PCB
VITA57-FMC-male
