mzandrew/idlab-scrod/mechanical-designs/other/velmex-motor-to-motor-mount.right-angle.SLDASM

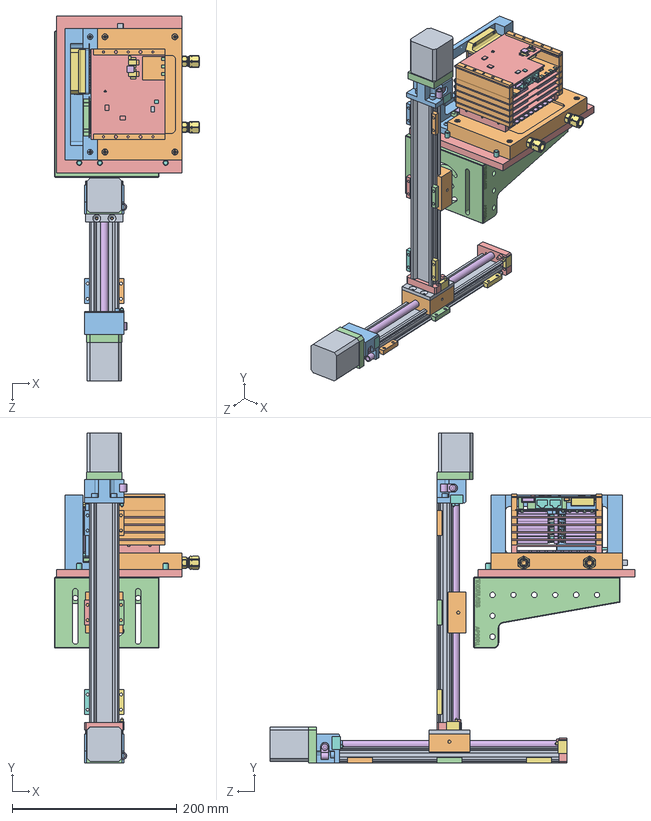
[picture p69: CAD file, 2014-02-25]
mechanical-designs/other/velmex-motor-to-motor-mount.right-angle.SLDASM
176.3 x 400.6 x 443.5 mm
Velmex-xn10_0080_71_Imported x 2
Velmex-xn10_0080_71_Imported1 x 2
Velmex-xn10_0080_71_Imported2 x 2
Velmex-xn10_0080_71_Imported3 x 2
Velmex-xn10_0080_71_Imported4 x 2
Velmex-xn10_0080_71_Imported5 x 2
Velmex-xn10_0080_71_Imported6 x 2
Velmex-xn10_0080_71_Imported7 x 2
Velmex-xn10_0080_71_Imported8 x 2
Velmex-xn10_0080_71_Imported9 x 2
Velmex-xn10_0080_71_Imported10 x 2
Velmex-xn10_0080_71_Imported11 x 2
Velmex-xn10_0080_71_Imported12 x 2
Velmex-xn10_0080_71_Imported13 x 2
Velmex-xn10_0080_71_Imported14 x 2
Velmex-xn10_0080_71_Imported15 x 2
velmex-motor-to-motor-mount.right-angle
ElectronicsTestPlate
ElectronicsTestFrontPlate
ElectronicTestPMTClamp x 2
McMaster-Carr-3511T22
MC91292A32 x 4
5220K670 x 2
97325A460 x 3
44705K382
BUTTON HEAD NUM6 x 4
BUTTON HEAD NUM6 short x 2
AP90RL-Solidworks
carrier.revE x 4
FX8C-board-to-board-interconnects x 12
TQFP-128 x 16
pogo-pin.millmax-0926-1 x 254
pogo-pin-carrier-for-signal-pins x 8
interconnect.revC
board-interconnects.100-and-120-pin.bottom-SV4.top-SV.interconnect
MMCX-board-edge-cutout x 6
SCROD.revA3
14-pin.2mm.jtag-header.right-angle
fiber-cage.double-wide
RJ45.surface-mount.double-wide
spartan6.676-FGG
USB-mini
SOT23-5
board-to-board-interconnects.SCROD-pattern
5mm-by-7mm.oscillator x 2
8mm-by-8mm.cypress
TSSOP-8
TSSOP-16
TSSOP-20
board-spacers x 7
front-board
pin-socket.mill-max-8252-32 x 48
1206.capacitor x 32
SL10.4x4 x 4
MOCKUP LOWER peek in between filter and front board
peek in between filter and front board
92492A104 x 6
full filterrev b
cookie jellorev b
92290A019 x 2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
