mzandrew/idlab-scrod/mechanical-designs/tags/r282.iTOP-module-used-at-LEPS-SPRING8/board-stack/interconnect.revC.SLDASM

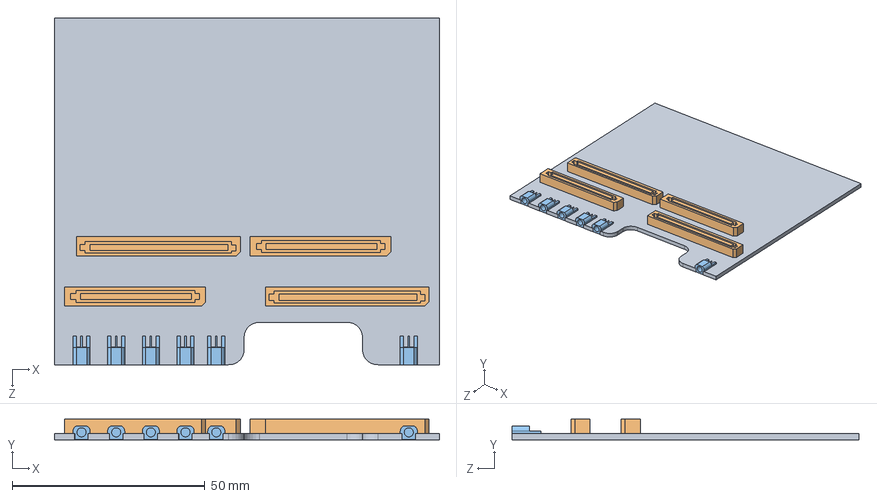
[picture p70: CAD file, 2013-11-14]
mechanical-designs/tags/r282.iTOP-module-used-at-LEPS-SPRING8/board-stack/interconnect.revC.SLDASM
100.0 x 5.34 x 90.0 mm
interconnect.revC
board-interconnects.100-and-120-pin.bottom-SV4.top-SV.interconnect
MMCX-board-edge-cutout x 6
