mzandrew/idlab-scrod/mechanical-designs/board-stack/fDIRC/H8500-front.components-back.SLDASM

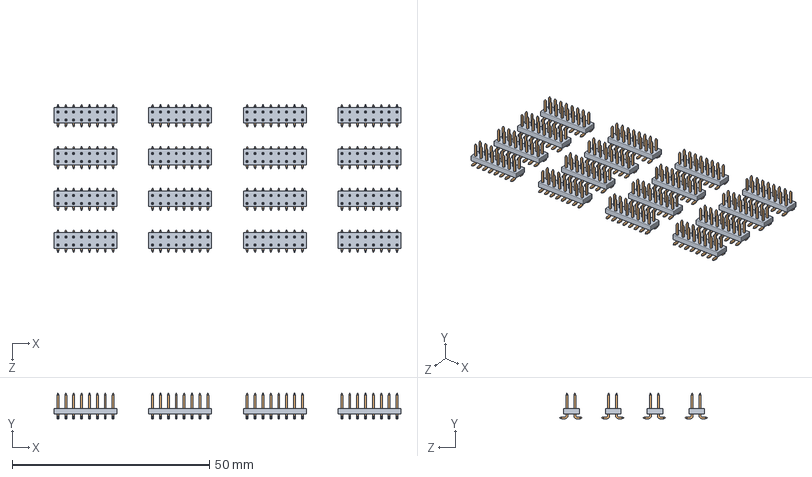
[picture p71: CAD file, 2013-02-14]
mechanical-designs/board-stack/fDIRC/H8500-front.components-back.SLDASM
88.0 x 6.50 x 37.5 mm
connector.2mm.16-pin.male x 16
2mm-connector-male-pin-surface-mount.pair.1 x 128
