mzandrew/idlab-scrod/mechanical-designs/board-stack/IRS2_DC.revB2/IRS2_DC.revB2.4.SLDASM

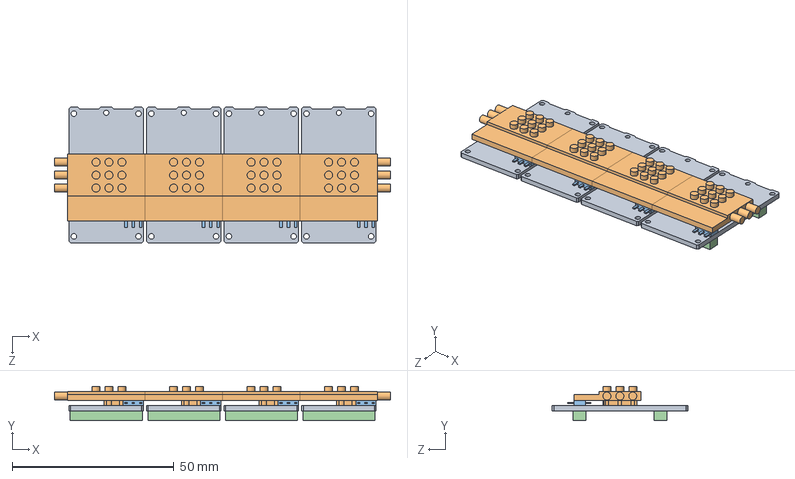
[picture p72: CAD file, 2013-01-11]
mechanical-designs/board-stack/IRS2_DC.revB2/IRS2_DC.revB2.4.SLDASM
104.0 x 10.6 x 42.0 mm
IRS2_DC.revB2 x 4
IRS2_DC.revB2.heatsink x 4
SOT-223 x 4
80-pin-connectors x 4
