mzandrew/idlab-scrod/mechanical-designs/board-stack/iTOP/contrib/MOCKUP PMT unit assembly.SLDASM

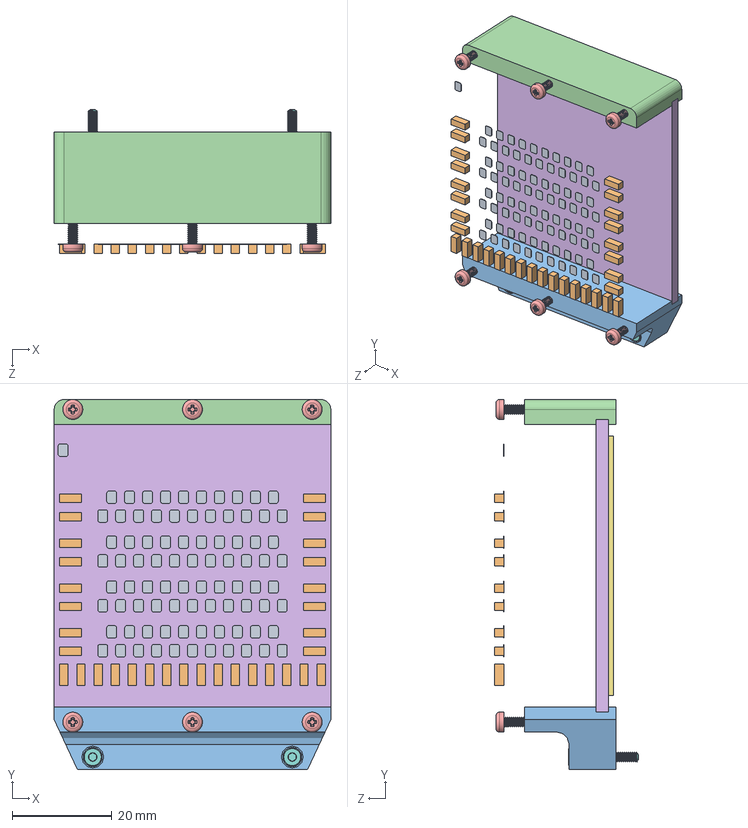
[picture p73: CAD file, 2014-05-03]
mechanical-designs/board-stack/iTOP/contrib/MOCKUP PMT unit assembly.SLDASM
55.5 x 74.2 x 28.9 mm
1206.capacitor x 32
pogo-pin.millmax-0926-1 x 85
MOCKUP LOWER peek in between filter and front board
peek in between filter and front board
92492A104 x 6
full filterrev b
cookie jellorev b
92290A019 x 2
