mzandrew/idlab-scrod/mechanical-designs/board-stack/iTOP/pogo-pins-for-signals.SLDASM

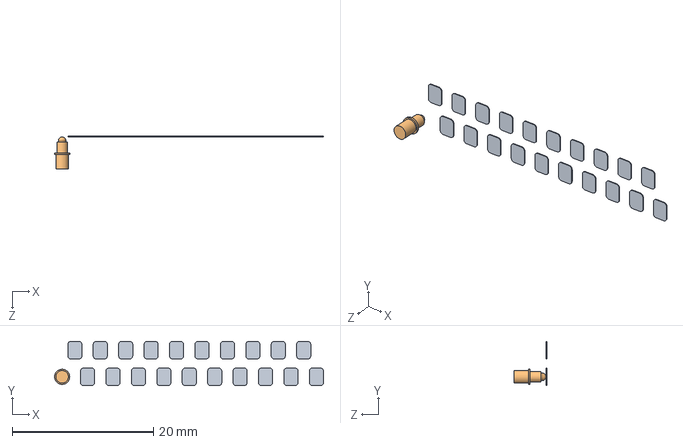
[picture p74: CAD file, 2014-05-03]
mechanical-designs/board-stack/iTOP/pogo-pins-for-signals.SLDASM
38.1 x 6.27 x 4.61 mm
pogo-pin.millmax-0926-1 x 21
