mzandrew/idlab-scrod/mechanical-designs/board-stack/mTC/detector.24PMTs.sldasm

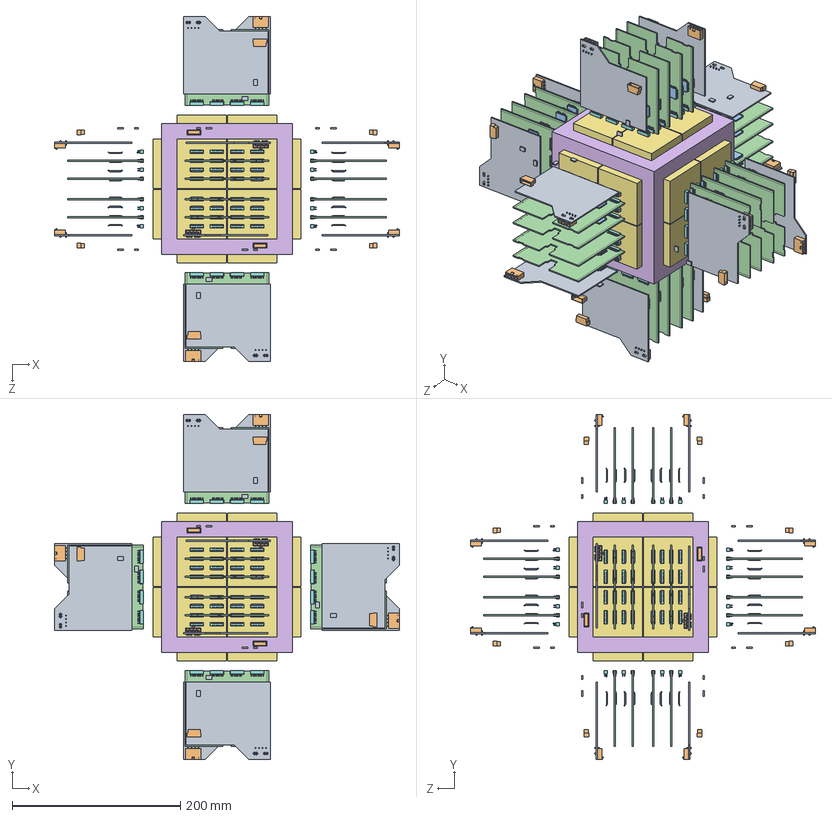
[picture p75: CAD file, 2013-01-31]
mechanical-designs/board-stack/mTC/detector.24PMTs.sldasm
410.6 x 410.6 x 410.6 mm
scintillator
polyoxymethylene.4PMTs x 6
planacon-XP85012-A1 x 24
carrier13.revB.PCB x 24
connector.2mm.16-pin.female x 192
TQFP-128 x 120
interconnect.revB x 12
mini-fit-jr.right-angle.4-position x 12
14-pin.2mm.jtag-header.right-angle x 12
5mm-by-7mm.oscillator x 24
