mzandrew/idlab-scrod/mechanical-designs/common-components/connectors/fiber-optic.SLDASM

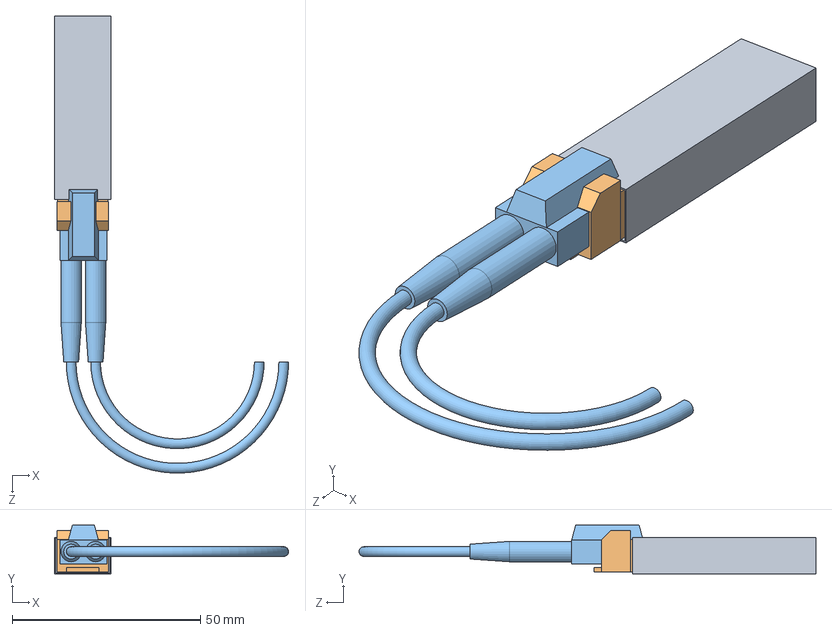
[picture p76: CAD file, 2014-05-03]
mechanical-designs/common-components/connectors/fiber-optic.SLDASM
62.3 x 13.0 x 121.5 mm
fiber-cage.single-wide
fiber-transceiver
fiber-cable-end.LC-duplex
