mzandrew/idlab-scrod/mechanical-designs/tags/r282.iTOP-module-used-at-LEPS-SPRING8/board-stack/carriers/carrier02.revB.SLDASM

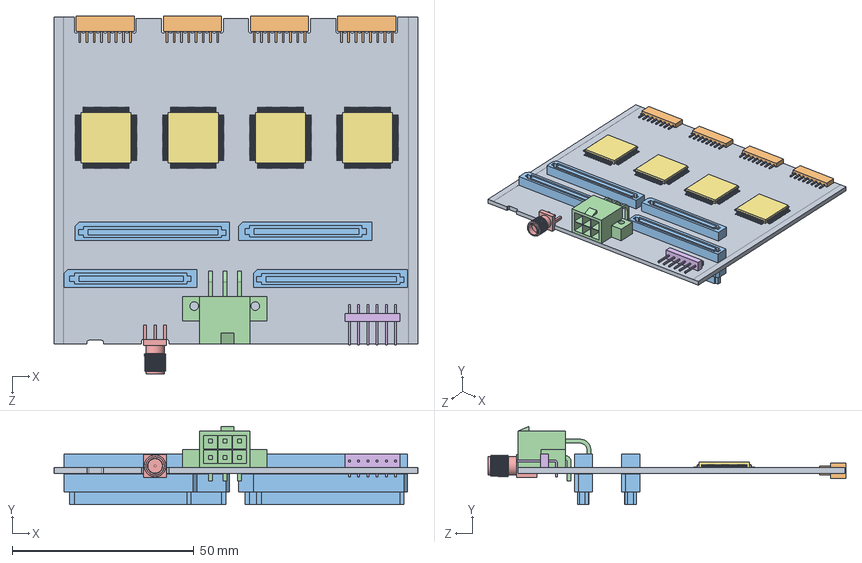
[picture p77: CAD file, 2013-11-14]
mechanical-designs/tags/r282.iTOP-module-used-at-LEPS-SPRING8/board-stack/carriers/carrier02.revB.SLDASM
100.1 x 21.6 x 98.5 mm
carrier02.revB.PCB
connector.2mm.16-pin.female x 4
board-interconnects.100-and-120-pin.bottom-SV4.top-SV.carrier02
molex-mini-fit-jr-6-pin-right-angle.simplified
SMA.PC-edge-mount.short
6-pin-0.1-inch-right-angle
TQFP-128 x 4
