mzandrew/idlab-scrod/mechanical-designs/tags/r282.iTOP-module-used-at-LEPS-SPRING8/board-stack/frames/2013-Rosen-cardcage/crt-card-cage-mated-to-iTOP-boardstack.SLDASM

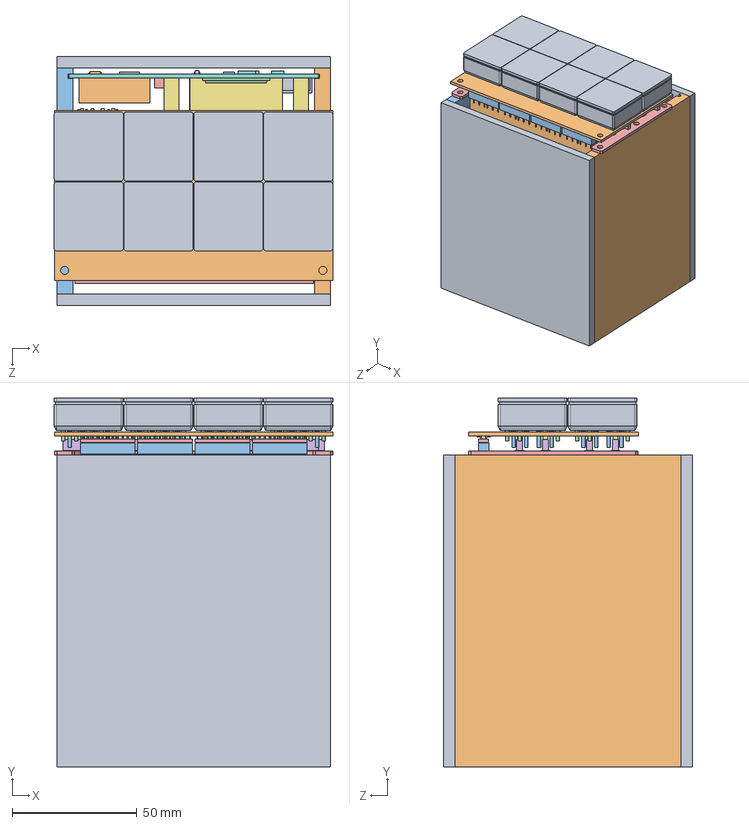
[picture p78: CAD file, 2013-01-31]
mechanical-designs/tags/r282.iTOP-module-used-at-LEPS-SPRING8/board-stack/frames/2013-Rosen-cardcage/crt-card-cage-mated-to-iTOP-boardstack.SLDASM
111.7 x 148.0 x 100.0 mm
CAP-PLATE x 2
LH-SIDE-PLATE
RH-SIDE_PLATE
carrier13.revB.PCB x 2
connector.2mm.16-pin.female x 16
board-interconnects.100-and-120-pin.bottom-SV4.top-SV.carrier13 x 2
SMA.PC-edge-mount.short x 4
TQFP-128 x 16
carrier02.revB.PCB x 2
board-interconnects.100-and-120-pin.bottom-SV4.top-SV.carrier02 x 2
molex-mini-fit-jr-6-pin-right-angle.simplified x 2
6-pin-0.1-inch-right-angle x 2
interconnect.revB
board-interconnects.100-and-120-pin.bottom-SV4.top-SV.interconnect
mini-fit-jr.right-angle.4-position
SCROD.revA2
14-pin.2mm.jtag-header.right-angle
fiber-cage.double-wide
RJ45.surface-mount.double-wide
spartan6.676-FGG
USB-mini
SOT23-5
board-to-board-interconnects.SCROD-pattern
5mm-by-7mm.oscillator x 2
8mm-by-8mm.cypress
TSSOP-8
TSSOP-16
TSSOP-20
front-back.revC
connector.2mm.09-pin.male.2 x 16
surface-mount-2mm-pin-socket-tab x 144
connector.2mm.16-pin.male x 16
2mm-connector-male-pin-surface-mount.pair.1 x 128
front-front.revC
pin-socket.ED5008 x 128
pin-socket.ED5044 x 64
connector.2mm.22-pin.male x 4
2mm-connector-male-pin-surface-mount.3 x 48
connector.2mm.09-pin.male.1 x 16
2mm-connector-male-pin-through-hole.chopped-off.3 x 192
SL10.4x4 x 8
SL10-HV-module.revA.IU.PCB
connector.2mm.22-pin.female x 4
SL10-HV-module.revA.IU.bottom-plate
SL10-HV-module.revA.IU.top-plate
SL10-HV-module.revA.IU.gap-pad x 2
