mzandrew/idlab-scrod/mechanical-designs/tags/r282.iTOP-module-used-at-LEPS-SPRING8/common-components/connectors/2mm/connector.2mm.22-pin.female.through-hole.11-pins-populated.SLDASM

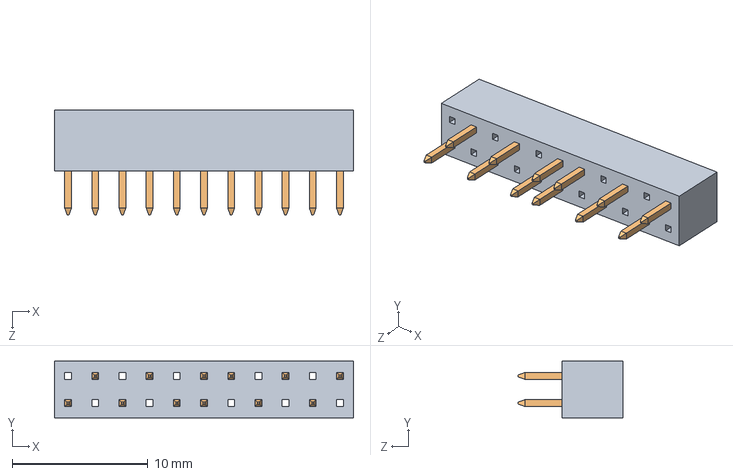
[picture p80: CAD file, 2013-02-14]
mechanical-designs/tags/r282.iTOP-module-used-at-LEPS-SPRING8/common-components/connectors/2mm/connector.2mm.22-pin.female.through-hole.11-pins-populated.SLDASM
22.0 x 4.17 x 7.72 mm
connector.2mm.22-pin.female
2mm-connector-male-pin-through-hole.chopped-off.3 x 12
