mzandrew/idlab-scrod/mechanical-designs/board-stack/fDIRC/fDIRC-boardstack-with-8-amps-and-2-PMTs.SLDASM

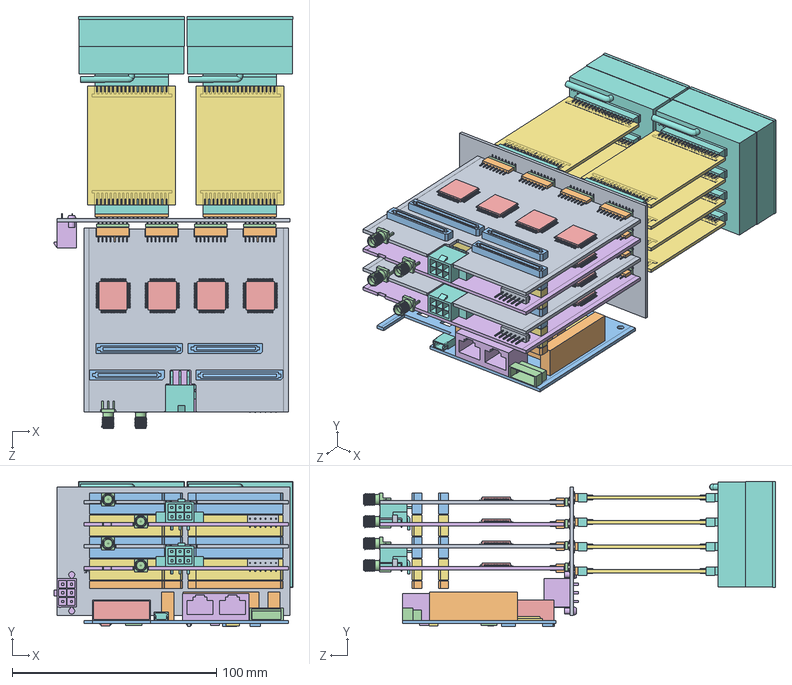
[picture p81: CAD file, 2013-02-14]
mechanical-designs/board-stack/fDIRC/fDIRC-boardstack-with-8-amps-and-2-PMTs.SLDASM
117.0 x 71.2 x 201.9 mm
carrier13.revB.PCB x 2
connector.2mm.16-pin.female x 16
board-interconnects.100-and-120-pin.bottom-SV4.top-SV.carrier13 x 2
SMA.PC-edge-mount.short x 4
TQFP-128 x 16
carrier02.revB.PCB x 2
board-interconnects.100-and-120-pin.bottom-SV4.top-SV.carrier02 x 2
molex-mini-fit-jr-6-pin-right-angle.simplified x 2
6-pin-0.1-inch-right-angle x 2
board-interconnects.100-and-120-pin.bottom-SV4.top-SV.interconnect
SCROD.revA2
14-pin.2mm.jtag-header.right-angle
fiber-cage.double-wide
RJ45.surface-mount.double-wide
spartan6.676-FGG
USB-mini
SOT23-5
board-to-board-interconnects.SCROD-pattern
5mm-by-7mm.oscillator x 2
8mm-by-8mm.cypress
TSSOP-8
TSSOP-16
TSSOP-20
H8500 x 2
H8500-front.revB
connector.2mm.36-pin.male x 8
2mm-connector-male-pin-surface-mount.pair.2 x 144
connector.2mm.16-pin.male x 16
2mm-connector-male-pin-surface-mount.pair.1 x 128
mini-fit-jr.vertical.6-position
H8500-amp.revB x 8
connector.2mm.36-pin.female x 16
