mzandrew/idlab-scrod/mechanical-designs/board-stack/IRS3_DC.revA/IRS3_DC.4.SLDASM

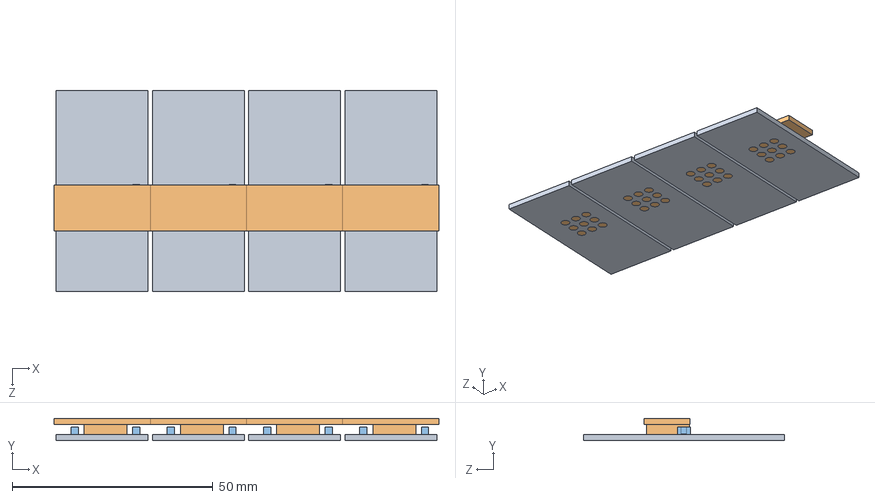
[picture p82: CAD file, 2012-03-23]
mechanical-designs/board-stack/IRS3_DC.revA/IRS3_DC.4.SLDASM
96.0 x 5.59 x 50.0 mm
IRS3_DC.revA x 4
IRS3_DC.heatsink x 4
1206.inductor x 8
