mzandrew/idlab-scrod/mechanical-designs/board-stack/iTOP/carrier.revE.SLDASM

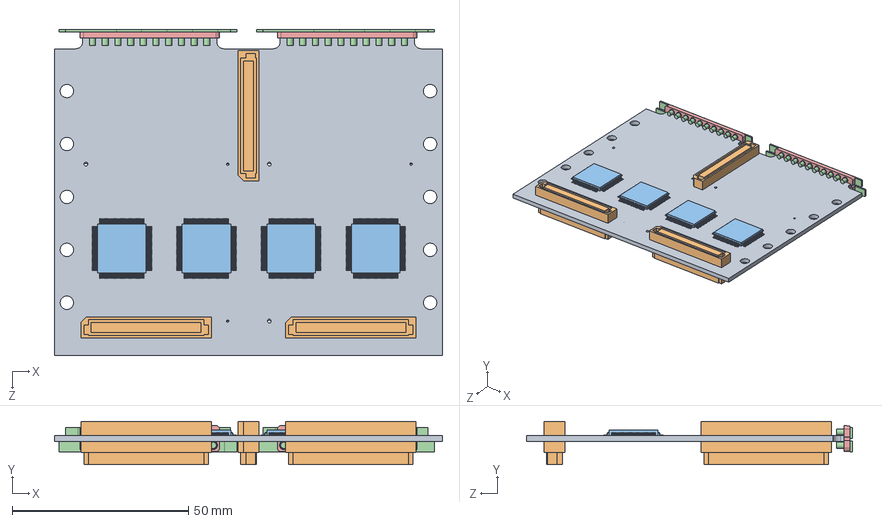
[picture p83: CAD file, 2014-05-03]
mechanical-designs/board-stack/iTOP/carrier.revE.SLDASM
110.0 x 12.3 x 92.5 mm
carrier.revE
FX8C-board-to-board-interconnects x 3
TQFP-128 x 4
pogo-pin.millmax-0926-1 x 42
pogo-pin-carrier-for-signal-pins x 2
