mzandrew/idlab-scrod/mechanical-designs/board-stack/iTOP/CRT/CRT-stand.SLDASM

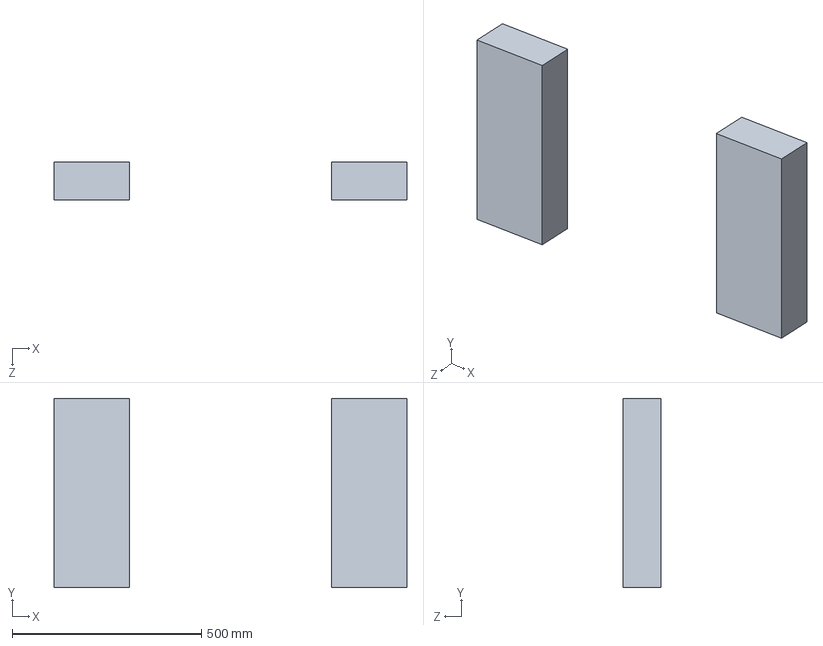
[picture p84: CAD file, 2013-03-11]
mechanical-designs/board-stack/iTOP/CRT/CRT-stand.SLDASM
933.4 x 500.0 x 100.0 mm
CRT-leg x 2
