mzandrew/idlab-scrod/mechanical-designs/board-stack/mTC/polyoxymethylene-with-readout.4PMTs.SLDASM

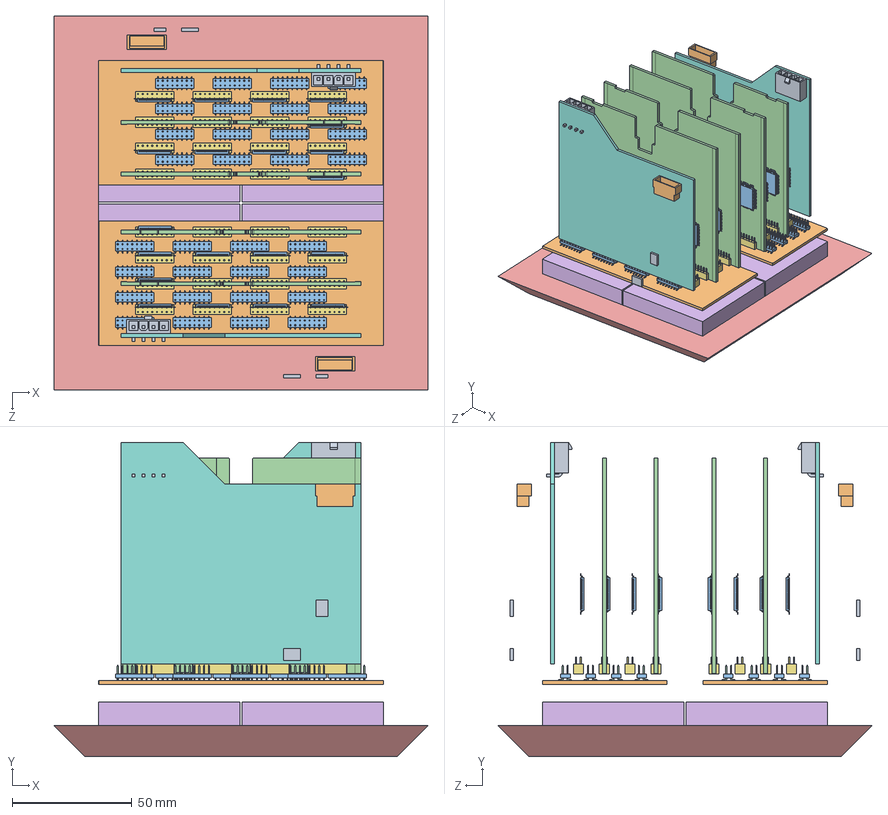
[picture p85: CAD file, 2013-01-31]
mechanical-designs/board-stack/mTC/polyoxymethylene-with-readout.4PMTs.SLDASM
156.0 x 131.1 x 156.0 mm
polyoxymethylene.4PMTs
planacon-XP85012-A1 x 4
carrier13.revB.PCB x 4
connector.2mm.16-pin.female x 32
TQFP-128 x 20
interconnect.revB x 2
mini-fit-jr.right-angle.4-position x 2
14-pin.2mm.jtag-header.right-angle x 2
5mm-by-7mm.oscillator x 4
front.revB x 2
connector.2mm.16-pin.male x 32
2mm-connector-male-pin-surface-mount.pair.1 x 256
