mzandrew/idlab-scrod/mechanical-designs/common-components/panels/FTSW-bracket.SLDASM

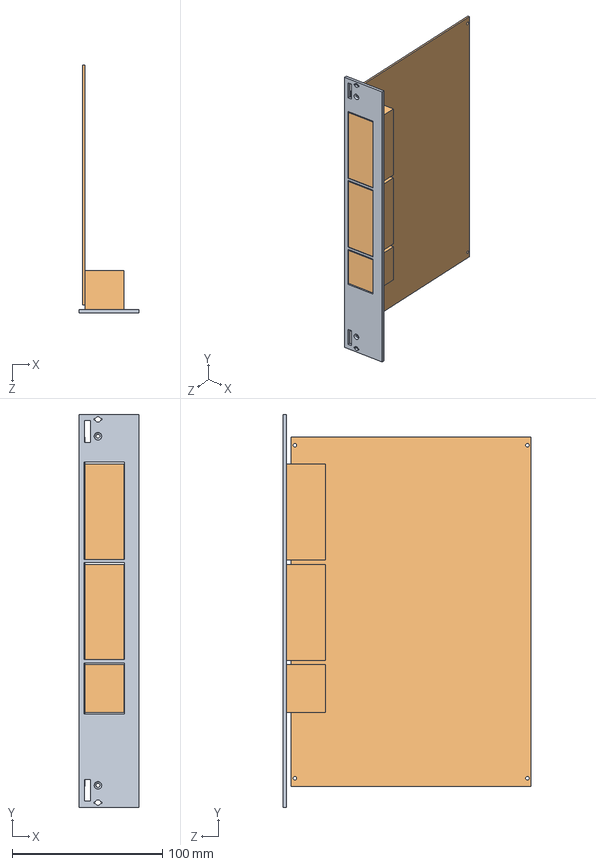
[picture p86: CAD file, 2013-10-08]
mechanical-designs/common-components/panels/FTSW-bracket.SLDASM
40.0 x 262.0 x 165.5 mm
VME-6U-front-panel
VME-6U-PCB.FTSW
