mzandrew/idlab-scrod/mechanical-designs/COPPER/COPPER-CRATE.with-COPPER-PCB-and-RTM.SLDASM

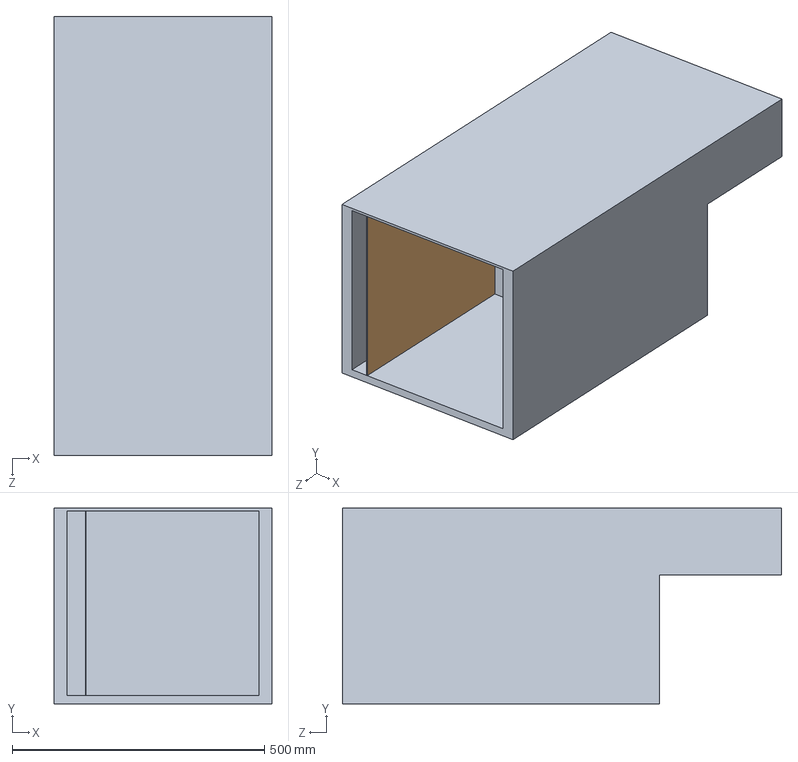
[picture p87: CAD file, 2013-05-14]
mechanical-designs/COPPER/COPPER-CRATE.with-COPPER-PCB-and-RTM.SLDASM
431.8 x 387.4 x 869.7 mm
COPPER-CRATE
COPPER-PCB.9U-VME
COPPER-RTM
