mzandrew/idlab-scrod/mechanical-designs/tags/r282.iTOP-module-used-at-LEPS-SPRING8/board-stack/carriers/carrier3.SLDASM

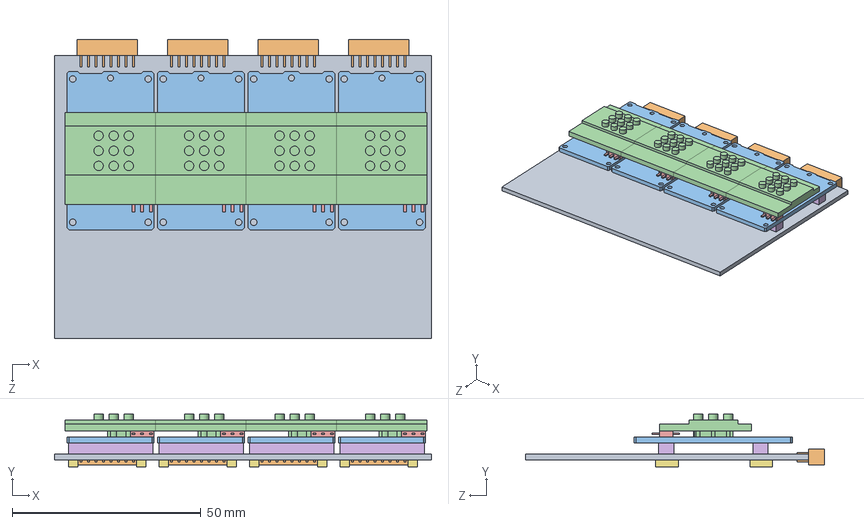
[picture p88: CAD file, 2013-01-18]
mechanical-designs/tags/r282.iTOP-module-used-at-LEPS-SPRING8/board-stack/carriers/carrier3.SLDASM
100.0 x 14.0 x 79.2 mm
carrier.common
connector.2mm.16-pin.female x 4
IRS2_DC.revB2 x 4
IRS2_DC.revB2.heatsink x 4
SOT-223 x 4
80-pin-connectors x 4
carrier04-capacitors
