mzandrew/idlab-scrod/mechanical-designs/tags/r282.iTOP-module-used-at-LEPS-SPRING8/board-stack/iTOP/front-front-with-SL10s.SLDASM

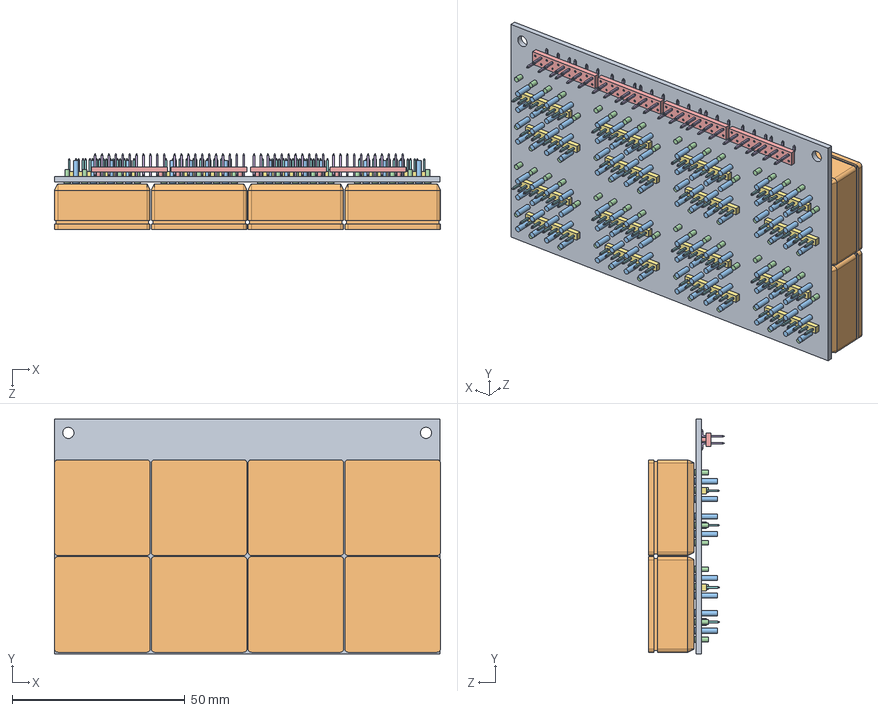
[picture p89: CAD file, 2013-02-14]
mechanical-designs/tags/r282.iTOP-module-used-at-LEPS-SPRING8/board-stack/iTOP/front-front-with-SL10s.SLDASM
111.7 x 68.0 x 21.9 mm
front-front.revC
SL10.4x4 x 8
pin-socket.ED5008 x 128
pin-socket.ED5044 x 64
connector.2mm.22-pin.male x 4
2mm-connector-male-pin-surface-mount.3 x 48
connector.2mm.09-pin.male.1 x 16
2mm-connector-male-pin-through-hole.chopped-off.3 x 144
