mzandrew/idlab-scrod/mechanical-designs/tags/r282.iTOP-module-used-at-LEPS-SPRING8/common-components/connectors/2mm/connector.2mm.16-pin.male.SLDASM

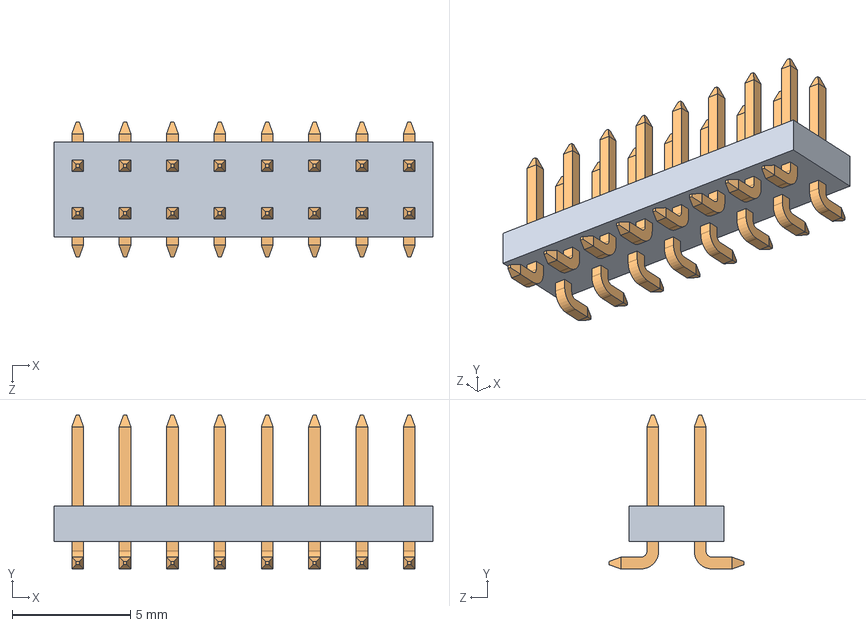
[picture p90: CAD file, 2013-02-11]
mechanical-designs/tags/r282.iTOP-module-used-at-LEPS-SPRING8/common-components/connectors/2mm/connector.2mm.16-pin.male.SLDASM
16.0 x 6.50 x 5.70 mm
connector.2mm.16-pin.male
2mm-connector-male-pin-surface-mount.pair.1 x 8
