mzandrew/idlab-scrod/mechanical-designs/board-stack/board-interconnects.120-pin.top-SV5.SLDASM

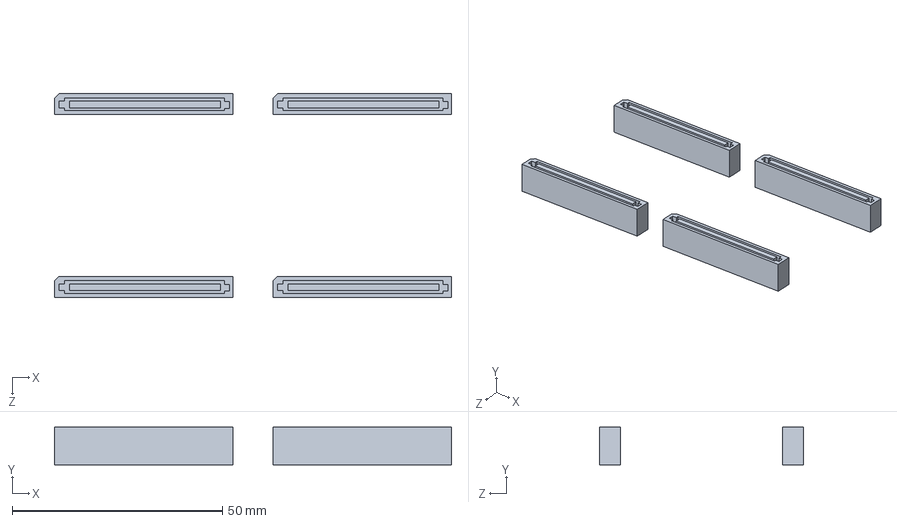
[picture p91: CAD file, 2013-10-26]
mechanical-designs/board-stack/board-interconnects.120-pin.top-SV5.SLDASM
94.5 x 9.00 x 48.5 mm
board-interconnects.120-pin.top-SV5 x 4
