mzandrew/idlab-scrod/mechanical-designs/board-stack/fDIRC/H8500-front.SLDASM

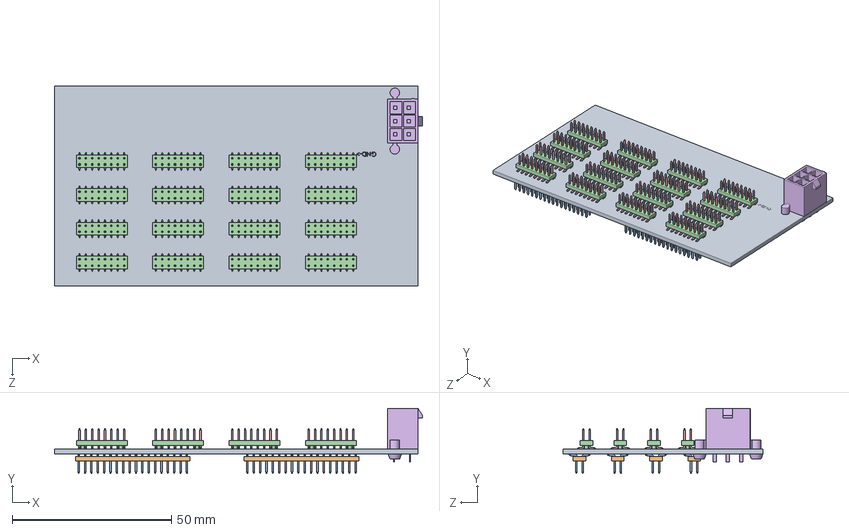
[picture p92: CAD file, 2013-02-14]
mechanical-designs/board-stack/fDIRC/H8500-front.SLDASM
115.6 x 20.5 x 62.8 mm
H8500-front.revB
connector.2mm.36-pin.male x 8
2mm-connector-male-pin-surface-mount.pair.2 x 144
connector.2mm.16-pin.male x 16
2mm-connector-male-pin-surface-mount.pair.1 x 128
mini-fit-jr.vertical.6-position
