mzandrew/idlab-scrod/mechanical-designs/board-stack/iTOP/SCROD-and-carriers-with-walls-and-front-PMT-PEEK-assembly-and-HV-module.SLDASM

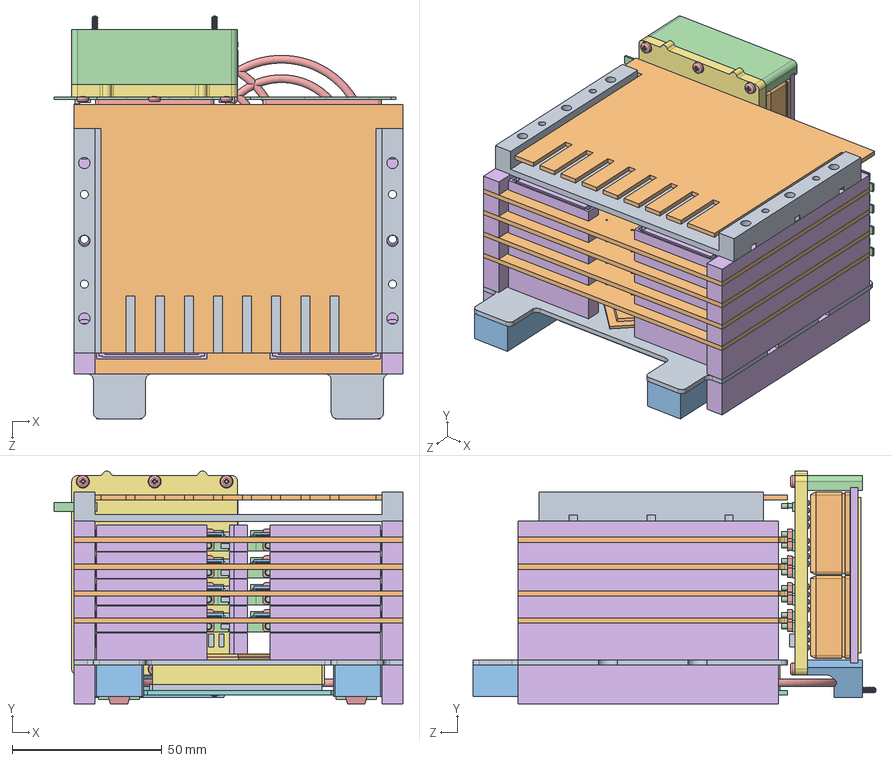
[picture p93: CAD file, 2014-05-03]
mechanical-designs/board-stack/iTOP/SCROD-and-carriers-with-walls-and-front-PMT-PEEK-assembly-and-HV-module.SLDASM
116.7 x 77.8 x 134.6 mm
SCROD.revB
zynq.900-FFG
fiber-cage.single-wide x 2
fiber-transceiver x 2
fiber-cable-end.LC-duplex x 2
FX8C-board-to-board-interconnects x 15
VITA57-FMC-female
VITA57-FMC-PCB
VITA57-FMC-male
carrier.revE x 4
TQFP-128 x 16
pogo-pin.millmax-0926-1 x 254
pogo-pin-carrier-for-signal-pins x 8
board-spacers x 6
front-board
pin-socket.mill-max-8252-32 x 48
1206.capacitor x 32
SL10.4x4 x 4
MOCKUP LOWER peek in between filter and front board
peek in between filter and front board
92492A104 x 6
full filterrev b
cookie jellorev b
92290A019 x 2
SL10-HV-module.revA.IU.bottom-platerev bc
SL10-HV-module.revA.IU.PCBrev bc
