mzandrew/idlab-scrod/mechanical-designs/common-components/connectors/VITA57-FMC-mated.SLDASM

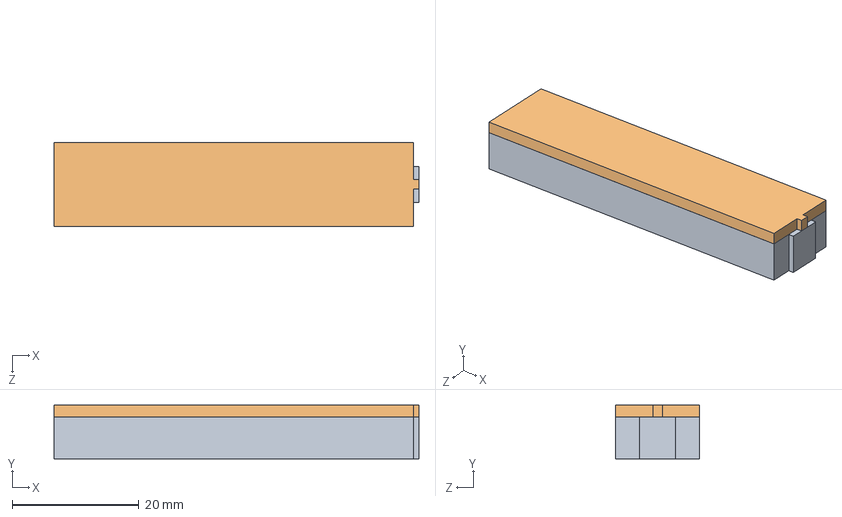
[picture p94: CAD file, 2013-10-26]
mechanical-designs/common-components/connectors/VITA57-FMC-mated.SLDASM
57.5 x 8.45 x 13.2 mm
VITA57-FMC-female
VITA57-FMC-male
