mzandrew/idlab-scrod/mechanical-designs/tags/r282.iTOP-module-used-at-LEPS-SPRING8/board-stack/carriers/carrier1.SLDASM

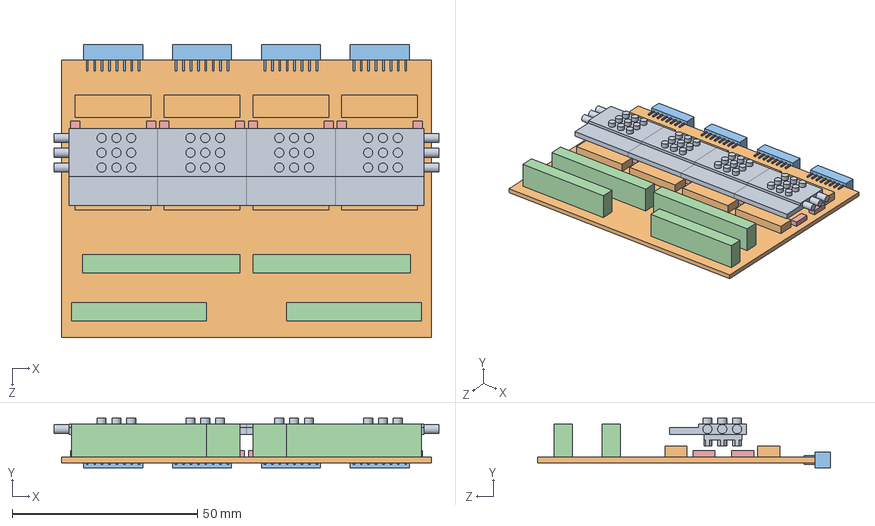
[picture p95: CAD file, 2013-01-18]
mechanical-designs/tags/r282.iTOP-module-used-at-LEPS-SPRING8/board-stack/carriers/carrier1.SLDASM
104.0 x 13.5 x 79.2 mm
carrier.common
connector.2mm.16-pin.female x 4
IRS2_DC.revB2.heatsink x 4
board-interconnects.100-and-120-pin.9mm
carrier12-capacitors
