mzandrew/idlab-scrod/mechanical-designs/tags/r282.iTOP-module-used-at-LEPS-SPRING8/board-stack/iTOP/front-back.SLDASM

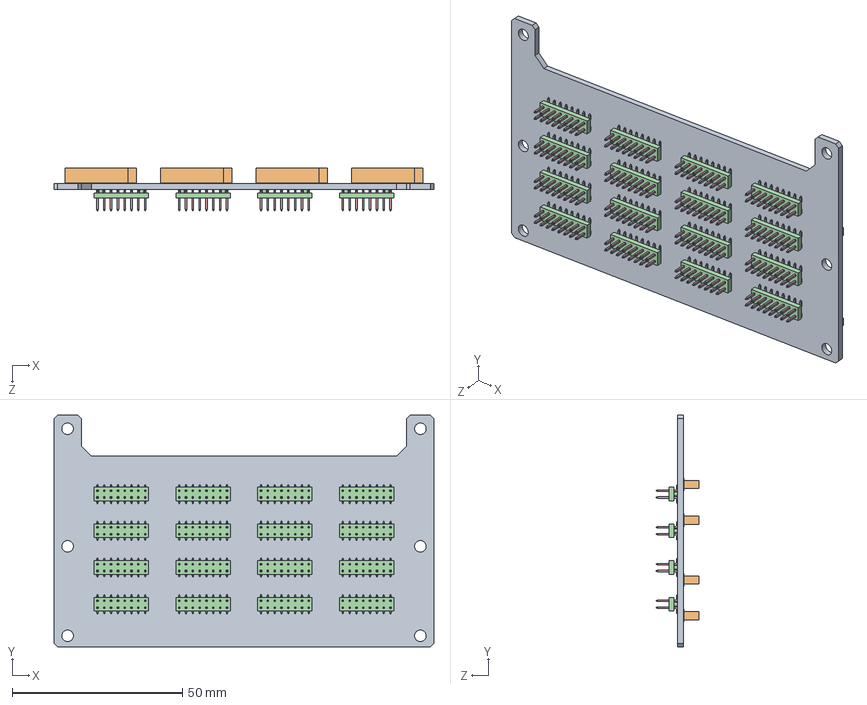
[picture p96: CAD file, 2013-02-14]
mechanical-designs/tags/r282.iTOP-module-used-at-LEPS-SPRING8/board-stack/iTOP/front-back.SLDASM
111.5 x 68.0 x 12.7 mm
front-back.revC
connector.2mm.09-pin.male.2 x 16
surface-mount-2mm-pin-socket-tab x 144
connector.2mm.16-pin.male x 16
2mm-connector-male-pin-surface-mount.pair.1 x 128
