mzandrew/idlab-scrod/mechanical-designs/board-stack/board-interconnects.120-pin.top-SV.bottom-SV2.SLDASM

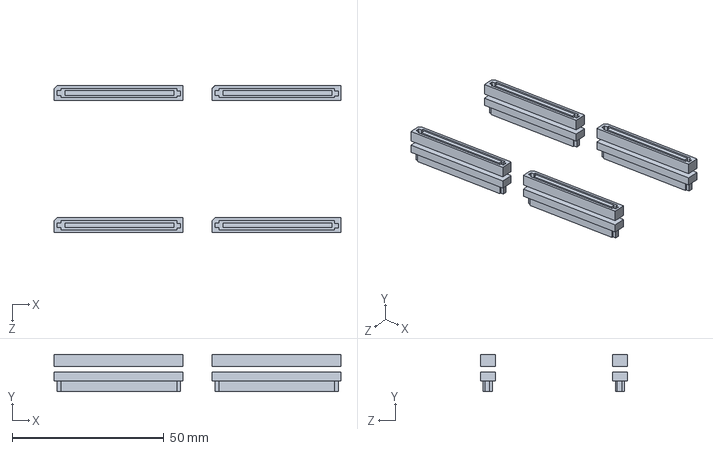
[picture p97: CAD file, 2013-10-14]
mechanical-designs/board-stack/board-interconnects.120-pin.top-SV.bottom-SV2.SLDASM
94.5 x 12.3 x 48.5 mm
board-interconnects.120-pin.top-SV.bottom-SV2 x 4
