mzandrew/idlab-scrod/mechanical-designs/board-stack/iTOP/SCROD-and-carriers-with-walls.SLDASM

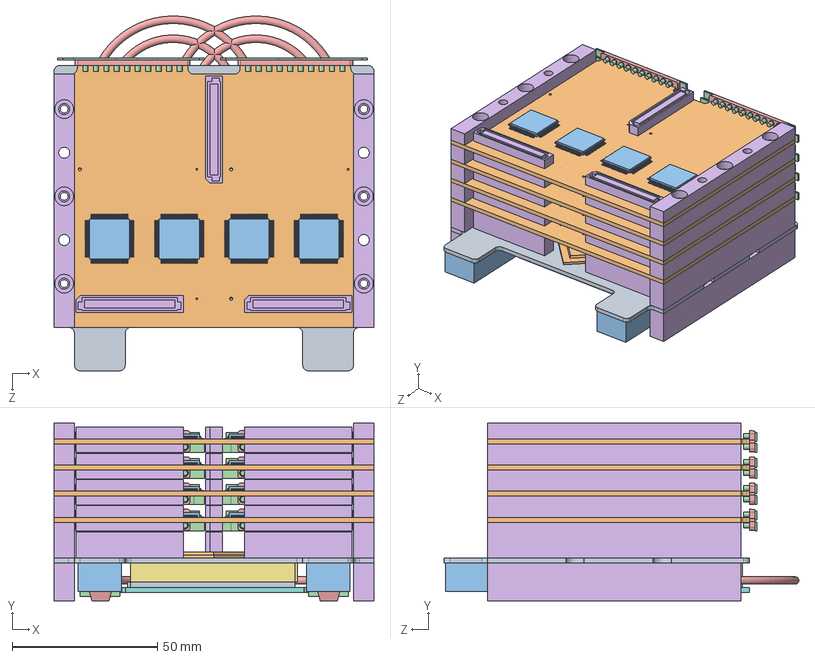
[picture p99: CAD file, 2014-03-24]
mechanical-designs/board-stack/iTOP/SCROD-and-carriers-with-walls.SLDASM
110.0 x 61.2 x 122.0 mm
SCROD.revB
zynq.900-FFG
fiber-cage.single-wide x 2
fiber-transceiver x 2
fiber-cable-end.LC-duplex x 2
FX8C-board-to-board-interconnects x 15
VITA57-FMC-female
VITA57-FMC-PCB
VITA57-FMC-male
carrier.revE x 4
TQFP-128 x 16
pogo-pin.millmax-0926-1 x 168
pogo-pin-carrier-for-signal-pins x 8
board-spacers x 6
