mzandrew/idlab-scrod/mechanical-designs/board-stack/mTC/mTC.24PMTs.SLDASM

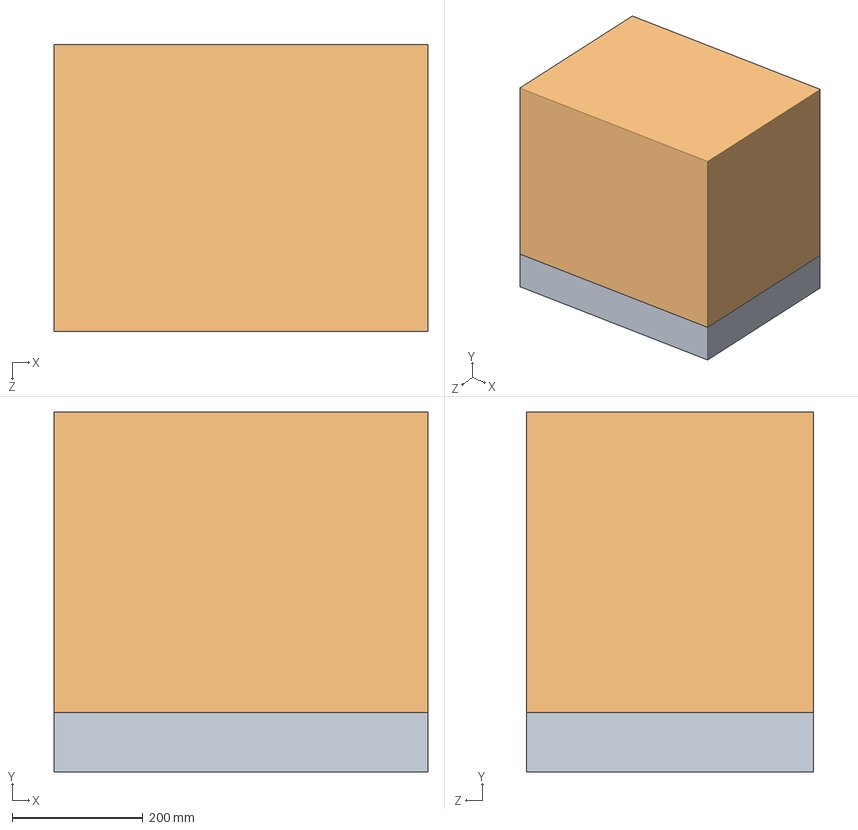
[picture p100: CAD file, 2013-01-31]
mechanical-designs/board-stack/mTC/mTC.24PMTs.SLDASM
572.5 x 550.4 x 439.1 mm
enclosure.bottom
enclosure.top
scintillator
polyoxymethylene.4PMTs x 6
planacon-XP85012-A1 x 24
carrier13.revB.PCB x 24
connector.2mm.16-pin.female x 192
board-interconnects.100-and-120-pin.bottom-SV4.top-SV.carrier13 x 24
SMA.PC-edge-mount.short x 48
TQFP-128 x 120
carrier02.revB.PCB x 24
board-interconnects.100-and-120-pin.bottom-SV4.top-SV.carrier02 x 24
molex-mini-fit-jr-6-pin-right-angle.simplified x 24
6-pin-0.1-inch-right-angle x 24
interconnect.revB x 12
board-interconnects.100-and-120-pin.bottom-SV4.top-SV.interconnect x 12
mini-fit-jr.right-angle.4-position x 12
SCROD.revA2 x 12
14-pin.2mm.jtag-header.right-angle x 12
fiber-cage.double-wide x 12
RJ45.surface-mount.double-wide x 12
spartan6.676-FGG x 12
USB-mini x 12
SOT23-5 x 12
board-to-board-interconnects.SCROD-pattern x 12
5mm-by-7mm.oscillator x 24
8mm-by-8mm.cypress x 12
TSSOP-8 x 12
TSSOP-16 x 12
TSSOP-20 x 12
front.revB x 12
connector.2mm.16-pin.male x 192
2mm-connector-male-pin-surface-mount.pair.1 x 1536
