mzandrew/idlab-scrod/mechanical-designs/common-components/panels/VME-6U-front-panel.SLDASM

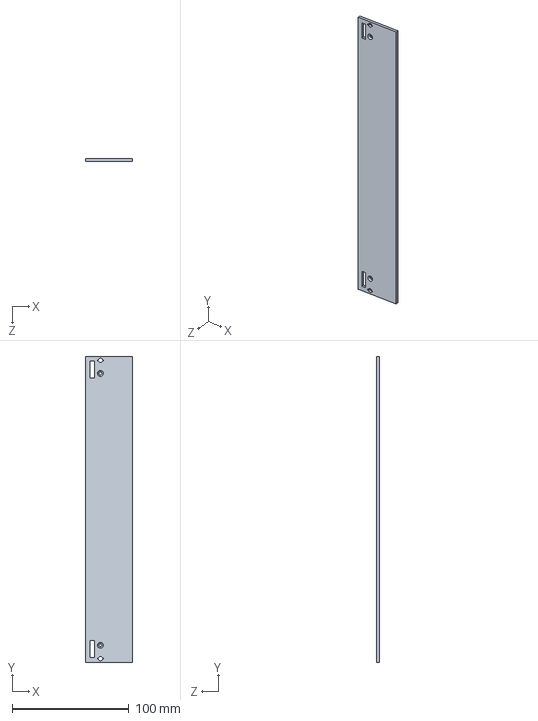
[picture p101: CAD file, 2013-10-08]
mechanical-designs/common-components/panels/VME-6U-front-panel.SLDASM
40.0 x 262.0 x 2.50 mm
