mzandrew/idlab-scrod/mechanical-designs/tags/r282.iTOP-module-used-at-LEPS-SPRING8/common-components/connectors/2mm/connector.2mm.09-pin.female.surface-mount.SLDASM

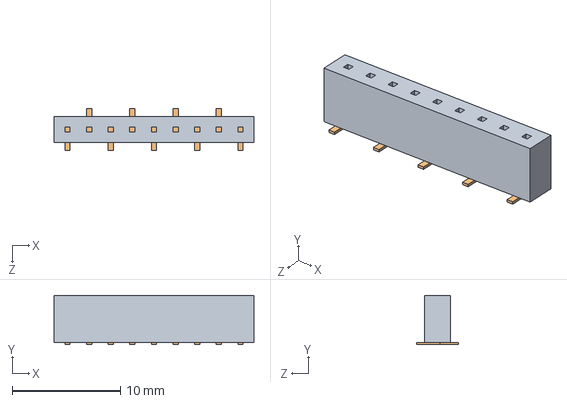
[picture p102: CAD file, 2013-02-11]
mechanical-designs/tags/r282.iTOP-module-used-at-LEPS-SPRING8/common-components/connectors/2mm/connector.2mm.09-pin.female.surface-mount.SLDASM
18.5 x 4.57 x 3.84 mm
connector.2mm.09-pin.male.2
surface-mount-2mm-pin-socket-tab x 9
