mzandrew/idlab-scrod/mechanical-designs/board-stack/fDIRC/fDIRC.SLDASM

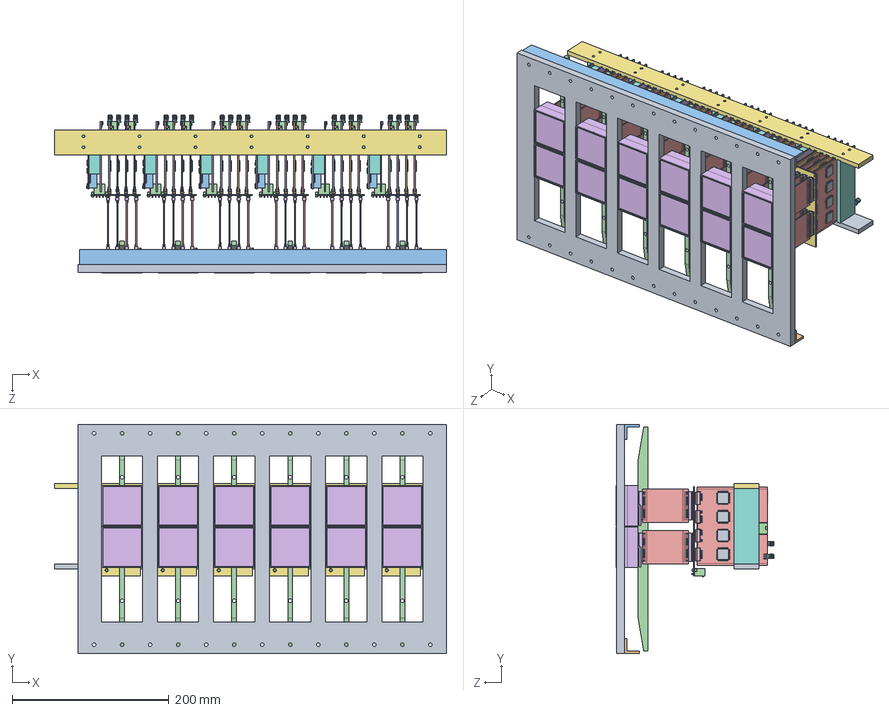
[picture p103: CAD file, 2013-02-14]
mechanical-designs/board-stack/fDIRC/fDIRC.SLDASM
500.0 x 292.1 x 201.9 mm
G10-frame
angle-aluminum-with-holes.bottom
angle-aluminum-with-holes.top
G10-PMT-support x 6
carrier13.revB.PCB x 12
connector.2mm.16-pin.female x 96
board-interconnects.100-and-120-pin.bottom-SV4.top-SV.carrier13 x 12
SMA.PC-edge-mount.short x 24
TQFP-128 x 96
carrier02.revB.PCB x 12
board-interconnects.100-and-120-pin.bottom-SV4.top-SV.carrier02 x 12
molex-mini-fit-jr-6-pin-right-angle.simplified x 12
6-pin-0.1-inch-right-angle x 12
interconnect.revC x 6
board-interconnects.100-and-120-pin.bottom-SV4.top-SV.interconnect x 6
MMCX-board-edge-cutout x 36
SCROD.revA2 x 6
14-pin.2mm.jtag-header.right-angle x 6
fiber-cage.double-wide x 6
RJ45.surface-mount.double-wide x 6
spartan6.676-FGG x 6
USB-mini x 6
SOT23-5 x 6
board-to-board-interconnects.SCROD-pattern x 6
5mm-by-7mm.oscillator x 12
8mm-by-8mm.cypress x 6
TSSOP-8 x 6
TSSOP-16 x 6
TSSOP-20 x 6
H8500 x 12
H8500-front.revB x 6
connector.2mm.36-pin.male x 48
2mm-connector-male-pin-surface-mount.pair.2 x 864
connector.2mm.16-pin.male x 96
2mm-connector-male-pin-surface-mount.pair.1 x 768
mini-fit-jr.vertical.6-position x 6
H8500-amp.revB x 48
connector.2mm.36-pin.female x 96
top_strip
mount-slats
bottom_strip
