mzandrew/idlab-scrod/mechanical-designs/board-stack/iTOP/SCROD-and-carriers-with-walls-and-front-PMT-PEEK-assembly-and-HV-module.intermediate.SLDASM

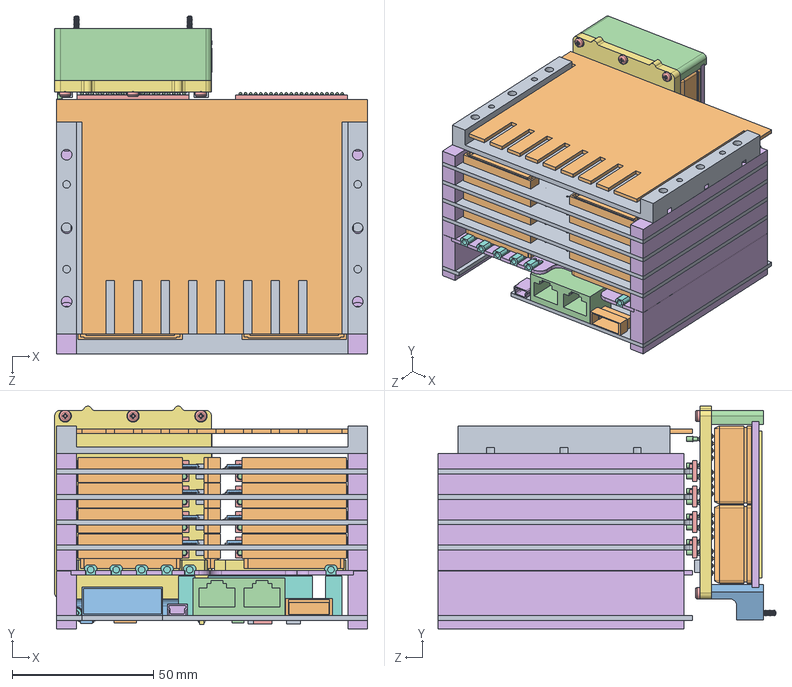
[picture p104: CAD file, 2014-02-25]
mechanical-designs/board-stack/iTOP/SCROD-and-carriers-with-walls-and-front-PMT-PEEK-assembly-and-HV-module.intermediate.SLDASM
110.8 x 78.8 x 119.6 mm
carrier.revE x 4
FX8C-board-to-board-interconnects x 12
TQFP-128 x 16
pogo-pin.millmax-0926-1 x 254
pogo-pin-carrier-for-signal-pins x 8
interconnect.revC
board-interconnects.100-and-120-pin.bottom-SV4.top-SV.interconnect
MMCX-board-edge-cutout x 6
SCROD.revA3
14-pin.2mm.jtag-header.right-angle
fiber-cage.double-wide
RJ45.surface-mount.double-wide
spartan6.676-FGG
USB-mini
SOT23-5
board-to-board-interconnects.SCROD-pattern
5mm-by-7mm.oscillator x 2
8mm-by-8mm.cypress
TSSOP-8
TSSOP-16
TSSOP-20
board-spacers x 7
front-board
pin-socket.mill-max-8252-32 x 48
1206.capacitor x 32
SL10.4x4 x 4
MOCKUP LOWER peek in between filter and front board
peek in between filter and front board
92492A104 x 6
full filterrev b
cookie jellorev b
92290A019 x 2
SL10-HV-module.revA.IU.bottom-platerev bc
SL10-HV-module.revA.IU.PCBrev bc
