mzandrew/idlab-scrod/mechanical-designs/board-stack/mTC/mTC-readout.2PMTs.SLDASM

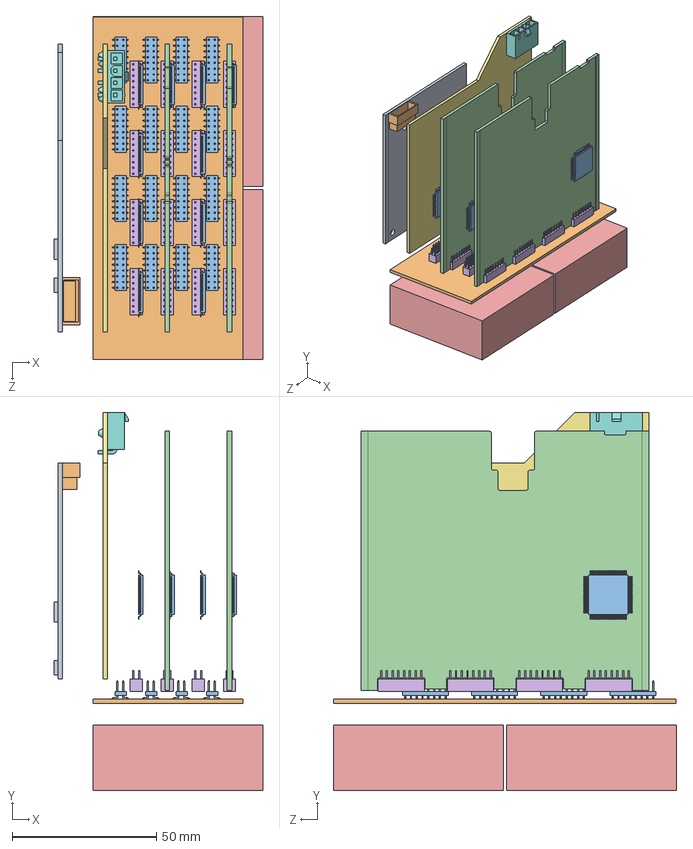
[picture p105: CAD file, 2013-01-31]
mechanical-designs/board-stack/mTC/mTC-readout.2PMTs.SLDASM
72.4 x 131.1 x 119.0 mm
planacon-XP85012-A1 x 2
carrier13.revB.PCB x 2
connector.2mm.16-pin.female x 16
TQFP-128 x 10
interconnect.revB
mini-fit-jr.right-angle.4-position
SCROD.revA2
14-pin.2mm.jtag-header.right-angle
5mm-by-7mm.oscillator x 2
front.revB
connector.2mm.16-pin.male x 16
2mm-connector-male-pin-surface-mount.pair.1 x 128
