mzandrew/idlab-scrod/mechanical-designs/common-components/panels/NIM-bin.SLDASM

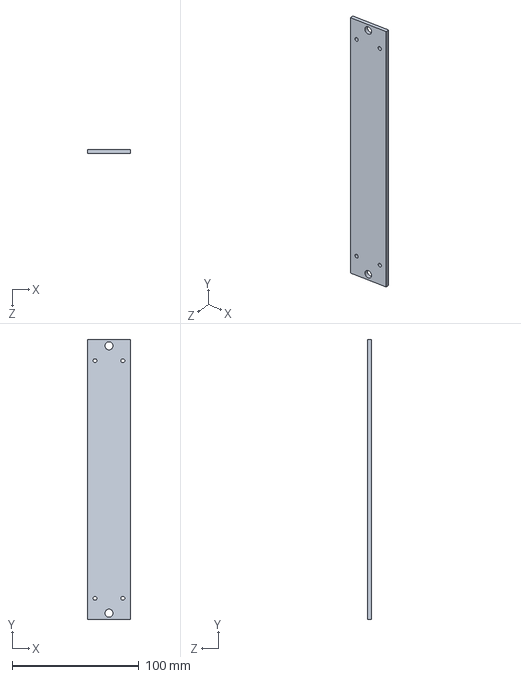
[picture p106: CAD file, 2013-10-08]
mechanical-designs/common-components/panels/NIM-bin.SLDASM
34.1 x 221.0 x 3.10 mm
