mzandrew/idlab-scrod/mechanical-designs/tags/r282.iTOP-module-used-at-LEPS-SPRING8/common-components/connectors/2mm/connector.2mm.09-pin.male.through-hole.chopped-off.SLDASM

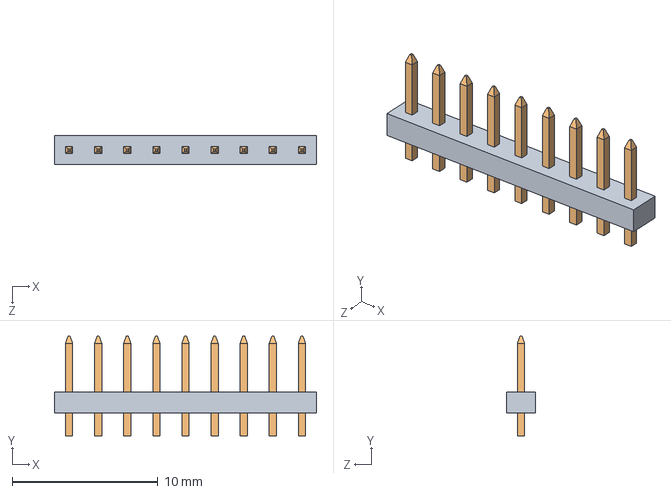
[picture p108: CAD file, 2013-02-11]
mechanical-designs/tags/r282.iTOP-module-used-at-LEPS-SPRING8/common-components/connectors/2mm/connector.2mm.09-pin.male.through-hole.chopped-off.SLDASM
18.0 x 6.87 x 2.00 mm
connector.2mm.09-pin.male.1
2mm-connector-male-pin-through-hole.chopped-off.3 x 9
