mzandrew/idlab-scrod/mechanical-designs/board-stack/board-stack.common.with-frame.SLDASM

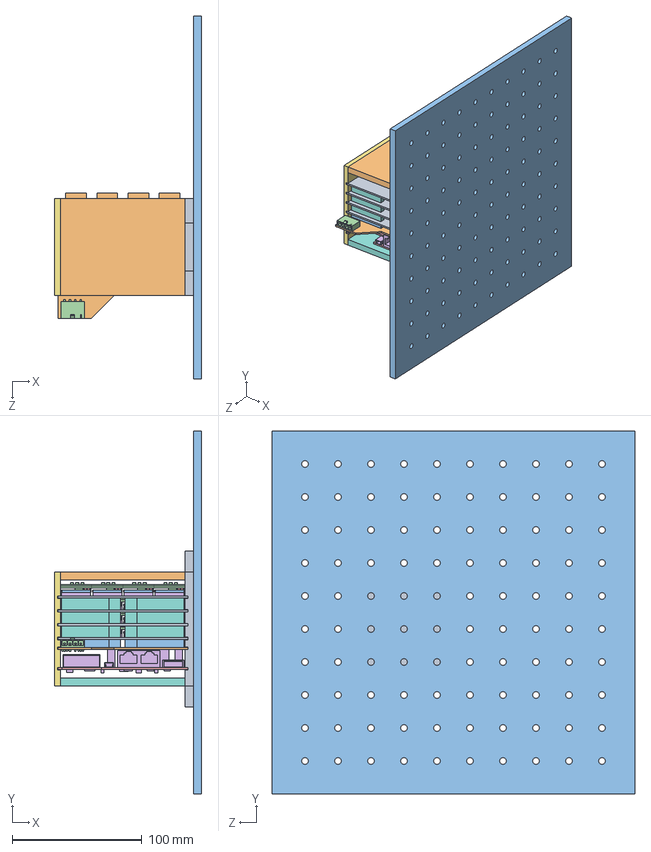
[picture p109: CAD file, 2013-01-11]
mechanical-designs/board-stack/board-stack.common.with-frame.SLDASM
113.5 x 279.4 x 279.4 mm
carrier.common x 4
connector.2mm.16-pin.female x 16
IRS2_DC.revB2 x 16
IRS2_DC.revB2.heatsink x 16
SOT-223 x 16
80-pin-connectors x 16
carrier04-capacitors x 2
board-interconnects.100-and-120-pin.9mm x 3
carrier12-capacitors x 2
interconnect.revB
board-interconnects.100-and-120-pin.6mm
mini-fit-jr.right-angle.4-position
SCROD.revA2
SCROD.components
simple-frame.left
simple-frame.bottom
simple-frame.right
simple-frame.top
