mzandrew/idlab-scrod/mechanical-designs/board-stack/iTOP/pogo-pins-for-HV.SLDASM

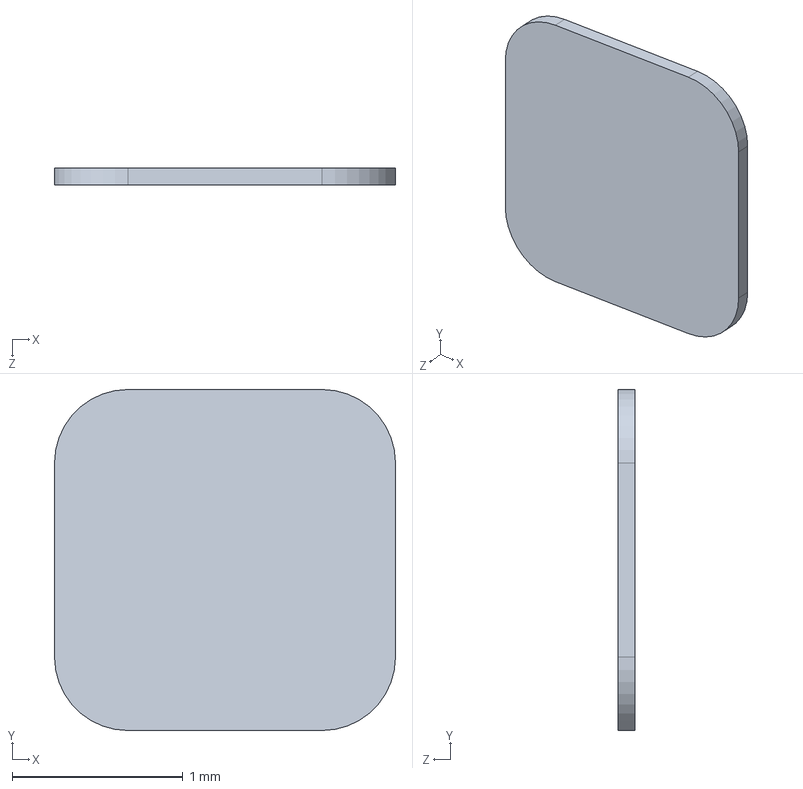
[picture p111: CAD file, 2014-02-25]
mechanical-designs/board-stack/iTOP/pogo-pins-for-HV.SLDASM
2.00 x 2.00 x 0.1 mm
