mzandrew/idlab-scrod/mechanical-designs/board-stack/mTC/polyoxymethylene.24PMTs.SLDASM

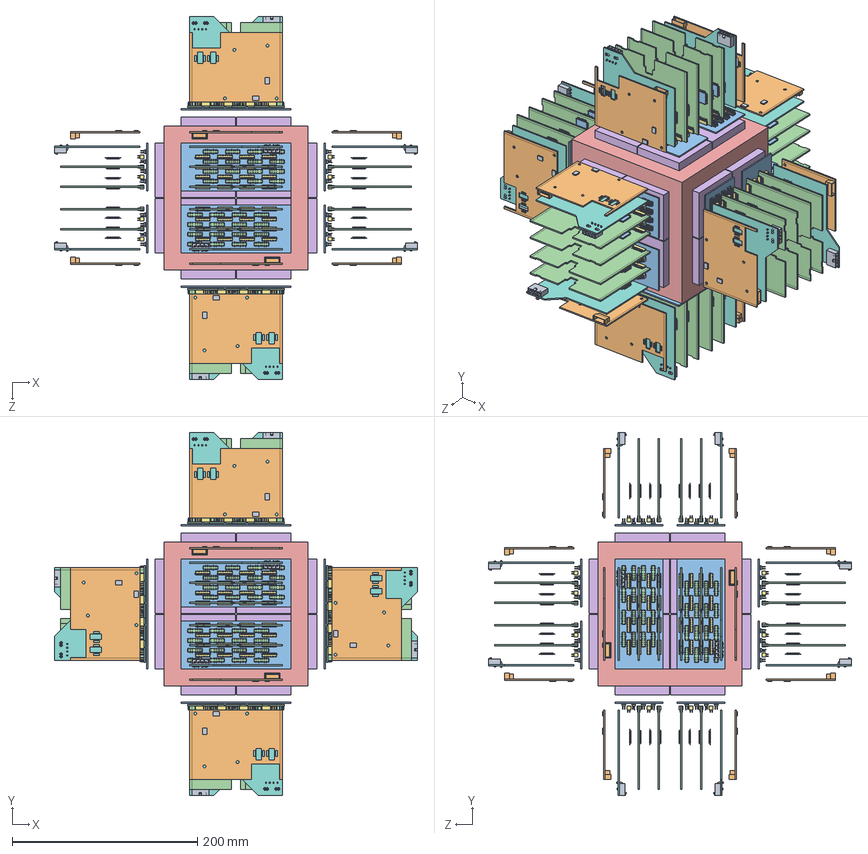
[picture p112: CAD file, 2013-01-31]
mechanical-designs/board-stack/mTC/polyoxymethylene.24PMTs.SLDASM
392.3 x 392.3 x 392.3 mm
polyoxymethylene.4PMTs x 6
planacon-XP85012-A1 x 24
carrier13.revB.PCB x 24
connector.2mm.16-pin.female x 192
TQFP-128 x 120
interconnect.revB x 12
mini-fit-jr.right-angle.4-position x 12
SCROD.revA2 x 12
14-pin.2mm.jtag-header.right-angle x 12
5mm-by-7mm.oscillator x 24
front.revB x 12
connector.2mm.16-pin.male x 192
2mm-connector-male-pin-surface-mount.pair.1 x 1536
