mzandrew/idlab-scrod/mechanical-designs/common-components/panels/FTSW.SLDASM

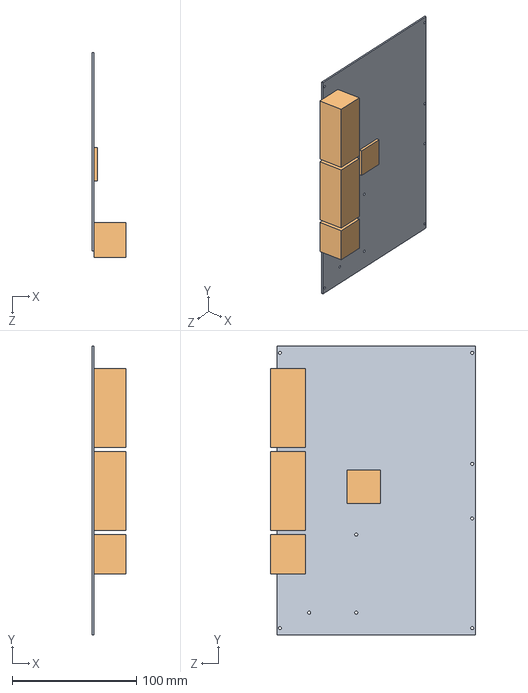
[picture p113: CAD file, 2013-10-08]
mechanical-designs/common-components/panels/FTSW.SLDASM
27.6 x 233.0 x 165.0 mm
VME-6U-PCB
VME-6U-PCB.FTSW
