mzandrew/idlab-scrod/mechanical-designs/tags/r282.iTOP-module-used-at-LEPS-SPRING8/common-components/connectors/2mm/connector.2mm.22-pin.male.11-pins-populated.SLDASM

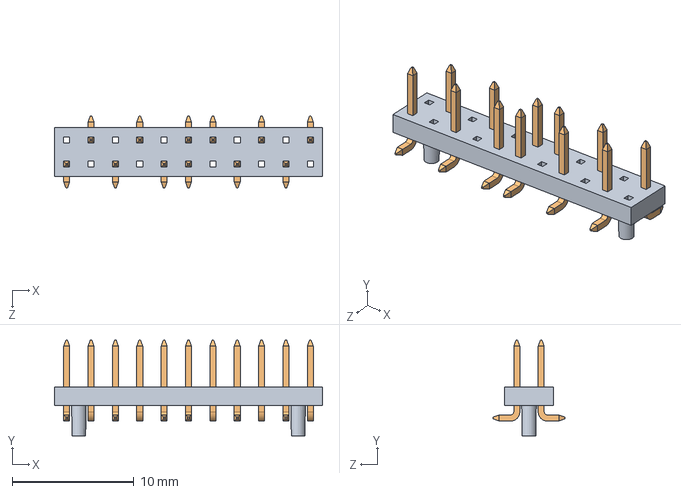
[picture p114: CAD file, 2013-02-11]
mechanical-designs/tags/r282.iTOP-module-used-at-LEPS-SPRING8/common-components/connectors/2mm/connector.2mm.22-pin.male.11-pins-populated.SLDASM
22.0 x 7.86 x 5.90 mm
connector.2mm.22-pin.male
2mm-connector-male-pin-surface-mount.3 x 12
