mzandrew/idlab-scrod/mechanical-designs/board-stack/iTOP/contrib/full filterrev b.SLDPRT

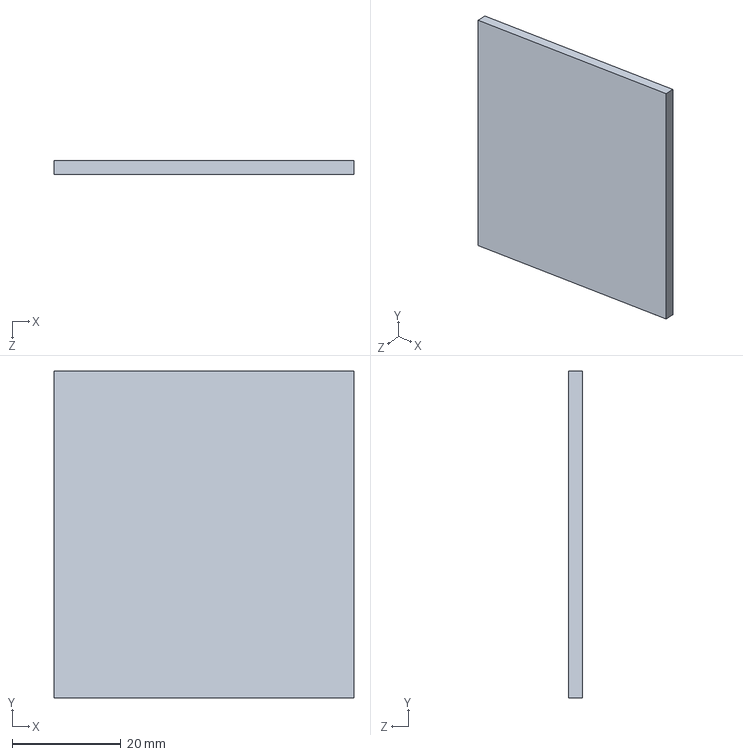
[picture p115: CAD file, 2013-11-13]
mechanical-designs/board-stack/iTOP/contrib/full filterrev b.SLDPRT
55.0 x 60.0 x 2.50 mm
