mzandrew/idlab-scrod/mechanical-designs/board-stack/iTOP/SL10-HV-module.SLDASM

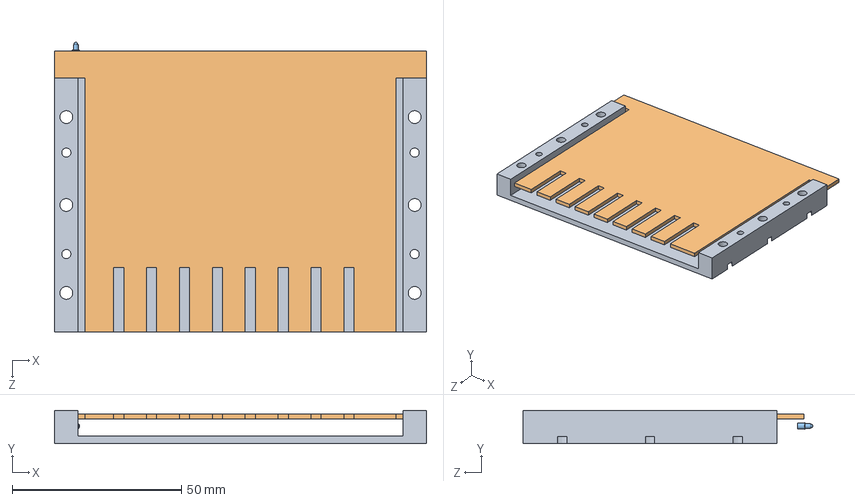
[picture p116: CAD file, 2014-02-25]
mechanical-designs/board-stack/iTOP/SL10-HV-module.SLDASM
110.0 x 9.80 x 85.6 mm
SL10-HV-module.revA.IU.bottom-platerev bc
SL10-HV-module.revA.IU.PCBrev bc
pogo-pin.millmax-0926-1
