mzandrew/idlab-scrod/mechanical-designs/board-stack/mTC/front.SLDASM

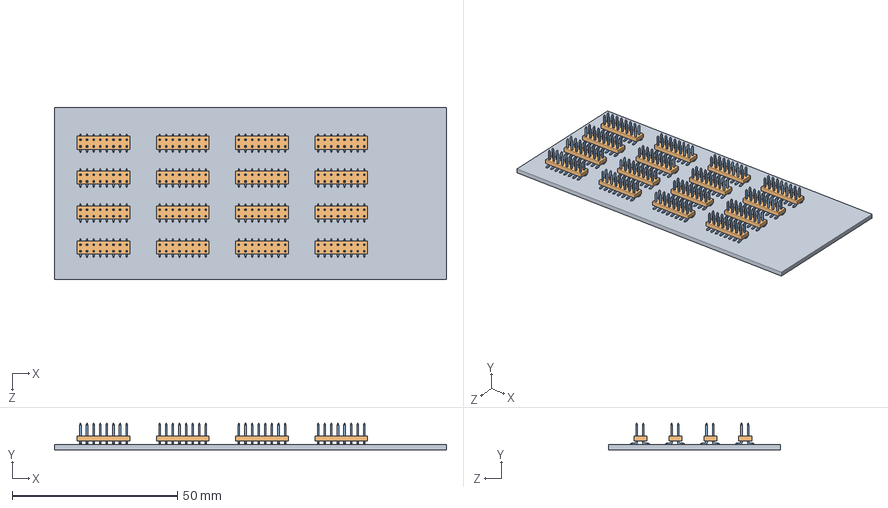
[picture p117: CAD file, 2013-01-31]
mechanical-designs/board-stack/mTC/front.SLDASM
118.7 x 8.09 x 52.1 mm
front.revB
connector.2mm.16-pin.male x 16
2mm-connector-male-pin-surface-mount.pair.1 x 128
