mzandrew/idlab-scrod/mechanical-designs/board-stack/mTC/polyoxymethylene.12PMTs.SLDASM

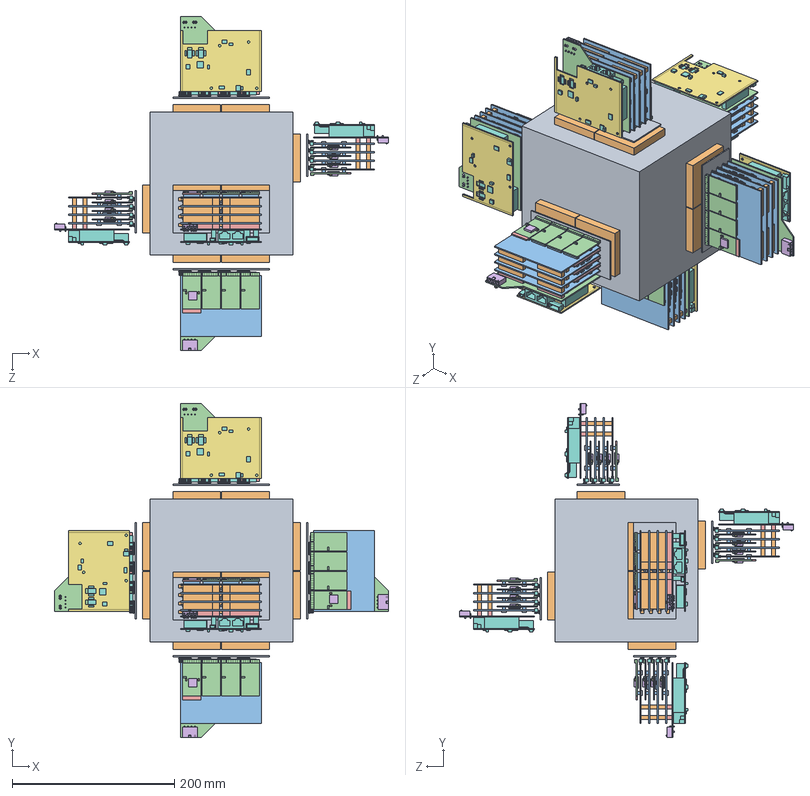
[picture p118: CAD file, 2012-07-12]
mechanical-designs/board-stack/mTC/polyoxymethylene.12PMTs.SLDASM
412.3 x 412.3 x 412.3 mm
polyoxymethylene.2PMTs x 6
planacon-XP85012-A1 x 12
carrier.common x 24
IRS2_DC.revB x 42
IRS3_DC.revA x 78
IRS3_DC.heatsink x 78
1206.inductor x 156
connector.2mm.16-pin.female x 96
carrier04-capacitors x 12
board-interconnects.100-and-120-pin.9mm x 18
carrier12-capacitors x 12
interconnect.revB x 6
board-interconnects.100-and-120-pin.6mm x 6
mini-fit-jr.right-angle.4-position x 6
SCROD.revA2 x 6
SCROD.components x 6
front.revB x 6
connector.2mm.16-pin.male x 96
2mm-connector-male-pin-surface-mount.pair.1 x 768
