mzandrew/idlab-scrod/mechanical-designs/tags/r282.iTOP-module-used-at-LEPS-SPRING8/board-stack/iTOP/SL10.4x4.pin-sockets.SLDASM

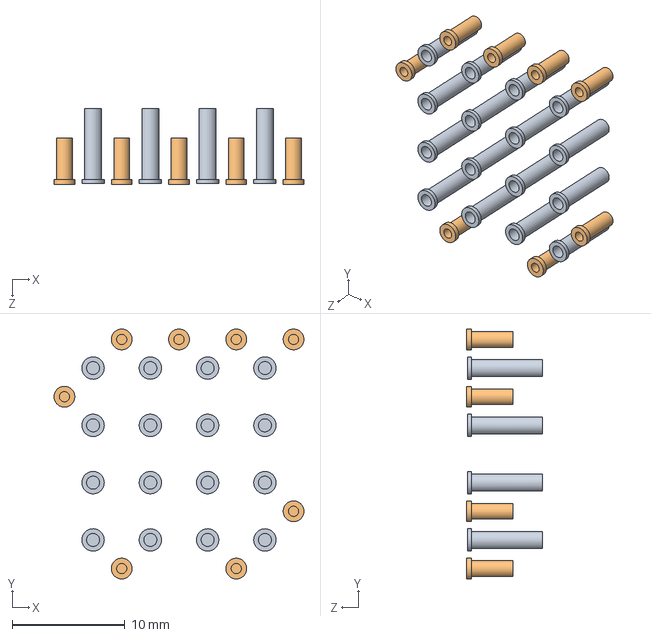
[picture p119: CAD file, 2013-01-23]
mechanical-designs/tags/r282.iTOP-module-used-at-LEPS-SPRING8/board-stack/iTOP/SL10.4x4.pin-sockets.SLDASM
22.2 x 22.2 x 6.74 mm
pin-socket.ED5008 x 16
pin-socket.ED5044 x 8
