mzandrew/idlab-scrod/mechanical-designs/tags/r282.iTOP-module-used-at-LEPS-SPRING8/common-components/connectors/2mm/connector.2mm.36-pin.male.SLDASM

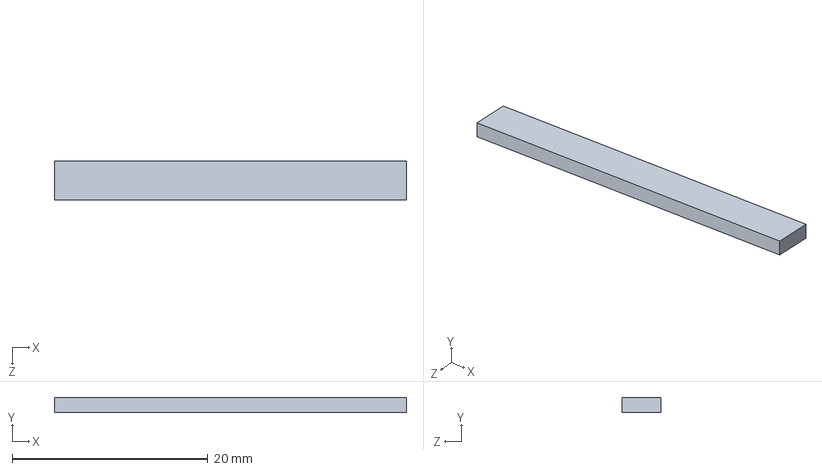
[picture p120: CAD file, 2012-07-12]
mechanical-designs/tags/r282.iTOP-module-used-at-LEPS-SPRING8/common-components/connectors/2mm/connector.2mm.36-pin.male.SLDASM
36.0 x 1.50 x 4.00 mm
