mzandrew/idlab-scrod/mechanical-designs/board-stack/iTOP/SCROD-and-interconnect-and-carriers.intermediate.SLDASM

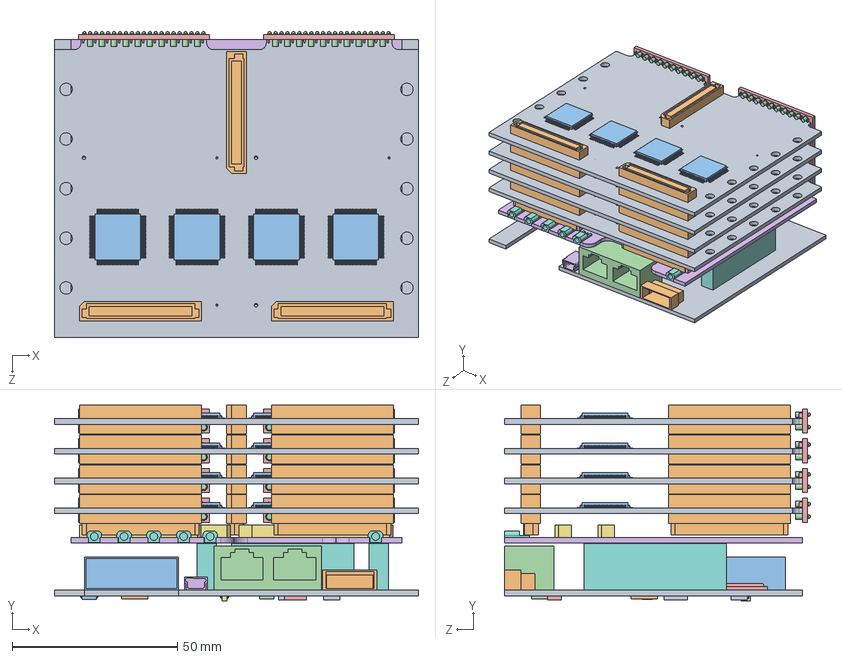
[picture p121: CAD file, 2014-02-25]
mechanical-designs/board-stack/iTOP/SCROD-and-interconnect-and-carriers.intermediate.SLDASM
110.0 x 59.1 x 92.5 mm
carrier.revE x 4
FX8C-board-to-board-interconnects x 12
TQFP-128 x 16
pogo-pin.millmax-0926-1 x 168
pogo-pin-carrier-for-signal-pins x 8
interconnect.revC
board-interconnects.100-and-120-pin.bottom-SV4.top-SV.interconnect
MMCX-board-edge-cutout x 6
SCROD.revA3
14-pin.2mm.jtag-header.right-angle
fiber-cage.double-wide
RJ45.surface-mount.double-wide
spartan6.676-FGG
USB-mini
SOT23-5
board-to-board-interconnects.SCROD-pattern
5mm-by-7mm.oscillator x 2
8mm-by-8mm.cypress
TSSOP-8
TSSOP-16
TSSOP-20
