mzandrew/idlab-scrod/mechanical-designs/board-stack/mTC/polyoxymethylene-with-readout.2PMTs.SLDASM

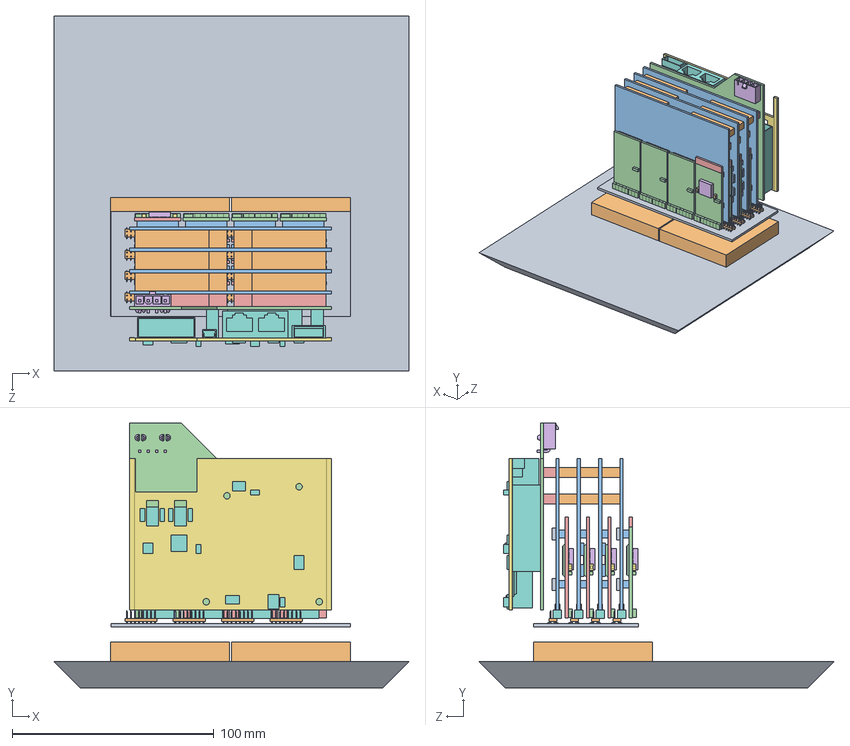
[picture p122: CAD file, 2012-07-12]
mechanical-designs/board-stack/mTC/polyoxymethylene-with-readout.2PMTs.SLDASM
176.0 x 131.1 x 176.0 mm
polyoxymethylene.2PMTs
planacon-XP85012-A1 x 2
carrier.common x 4
IRS2_DC.revB x 7
IRS3_DC.revA x 13
IRS3_DC.heatsink x 13
1206.inductor x 26
connector.2mm.16-pin.female x 16
carrier04-capacitors x 2
board-interconnects.100-and-120-pin.9mm x 3
carrier12-capacitors x 2
interconnect.revB
board-interconnects.100-and-120-pin.6mm
mini-fit-jr.right-angle.4-position
SCROD.revA2
SCROD.components
front.revB
connector.2mm.16-pin.male x 16
2mm-connector-male-pin-surface-mount.pair.1 x 128
