mzandrew/idlab-scrod/mechanical-designs/board-stack/iTOP/SL10.4x4.pin-sockets.v2.SLDASM

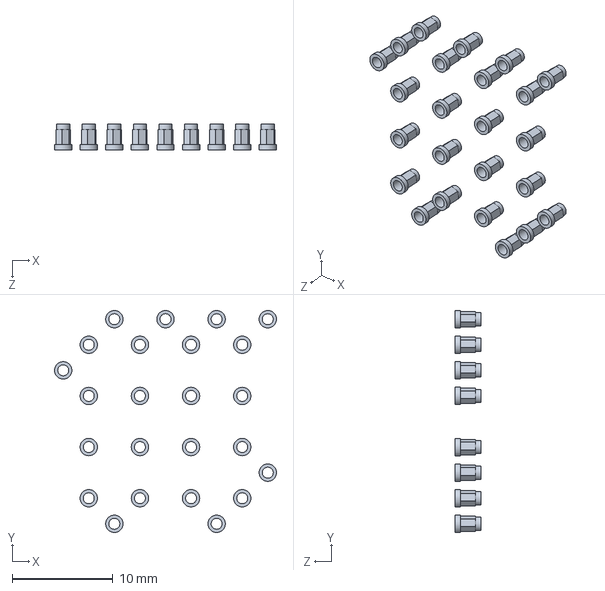
[picture p124: CAD file, 2013-11-13]
mechanical-designs/board-stack/iTOP/SL10.4x4.pin-sockets.v2.SLDASM
22.0 x 22.0 x 2.54 mm
pin-socket.mill-max-8252-32 x 24
