mzandrew/idlab-scrod/mechanical-designs/board-stack/mTC/enclosure.SLDASM

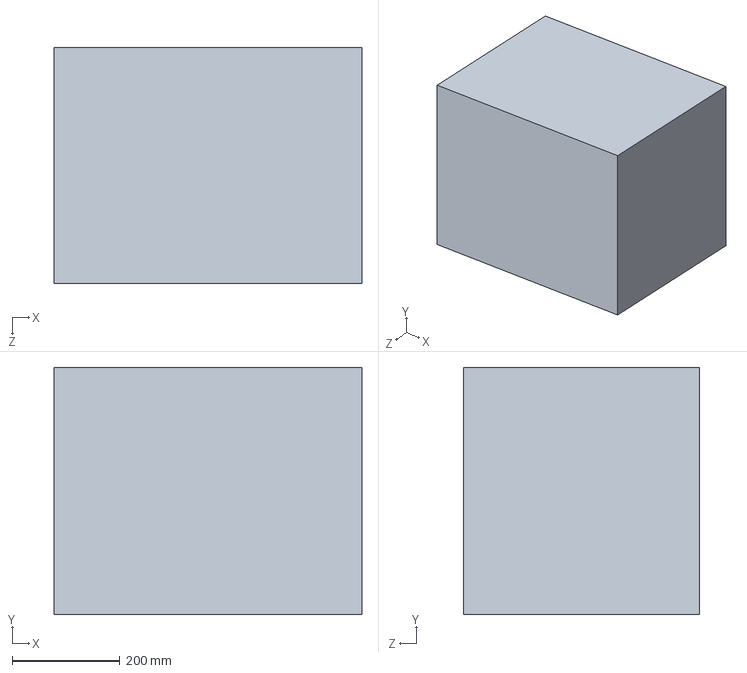
[picture p125: CAD file, 2012-04-05]
mechanical-designs/board-stack/mTC/enclosure.SLDASM
572.5 x 460.0 x 439.1 mm
