mzandrew/idlab-scrod/mechanical-designs/board-stack/iTOP/SCROD-and-carriers-with-walls-and-front-board.SLDASM

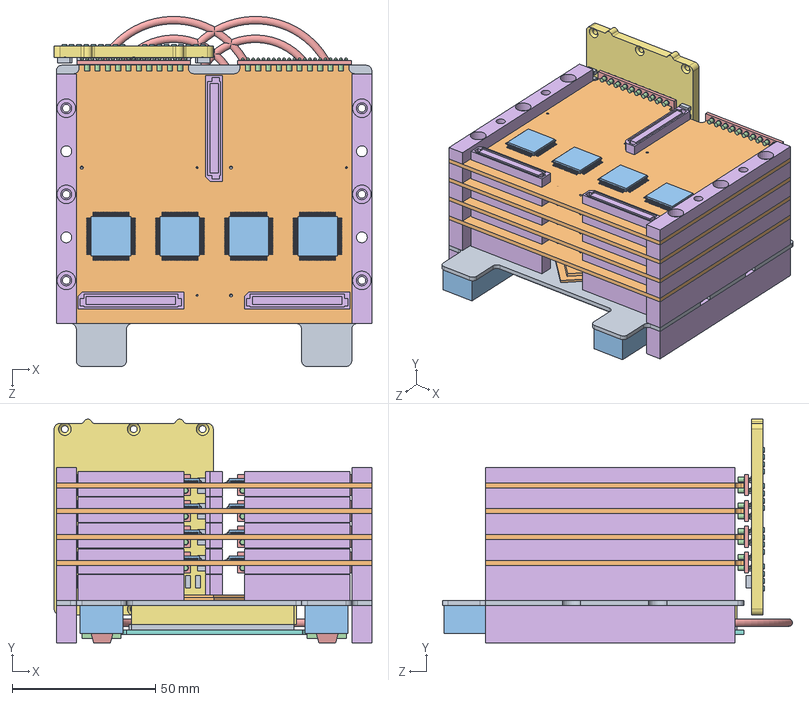
[picture p126: CAD file, 2013-11-08]
mechanical-designs/board-stack/iTOP/SCROD-and-carriers-with-walls-and-front-board.SLDASM
110.8 x 78.0 x 122.0 mm
SCROD.revB
zynq.900-FFG
fiber-cage.single-wide x 2
fiber-transceiver x 2
fiber-cable-end.LC-duplex x 2
FX8C-board-to-board-interconnects x 15
VITA57-FMC-female
VITA57-FMC-PCB
VITA57-FMC-male
carrier.revE x 4
TQFP-128 x 16
pogo-pin.millmax-0926-1 x 252
pogo-pin-carrier-for-signal-pins x 8
board-spacers x 6
front-board
pin-socket.mill-max-8252-32 x 96
1206.capacitor x 32
