mzandrew/idlab-scrod/mechanical-designs/board-stack/iTOP/iTOP.SLDASM

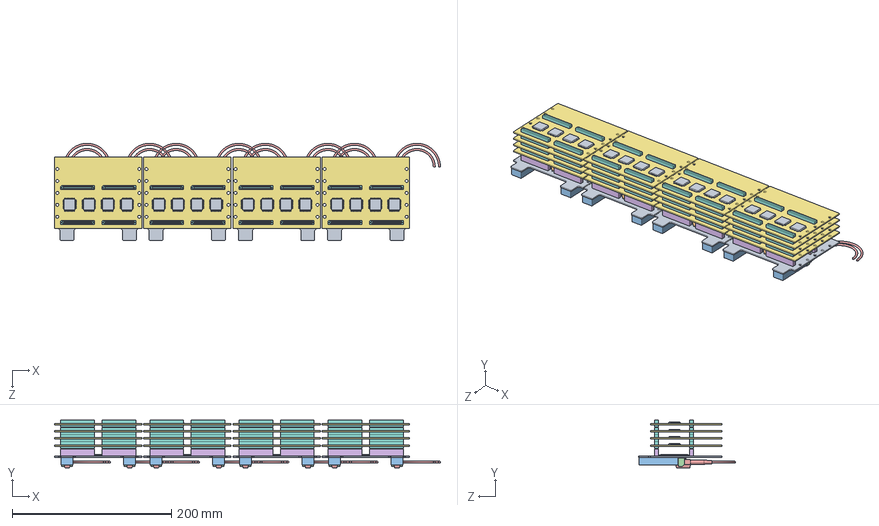
[picture p127: CAD file, 2013-10-08]
mechanical-designs/board-stack/iTOP/iTOP.SLDASM
485.0 x 59.8 x 122.3 mm
SCROD.revB x 4
zynq.900-FFG x 4
fiber-cage.single-wide x 8
fiber-transceiver x 8
fiber-cable-end.LC-duplex x 8
board-interconnects.120-pin.top-SV5 x 16
carrier.revD x 16
board-interconnects.120-pin.top-SV.bottom-SV2 x 64
TQFP-128 x 64
