mzandrew/idlab-scrod/mechanical-designs/board-stack/iTOP/PMT-with-cookie.SLDASM

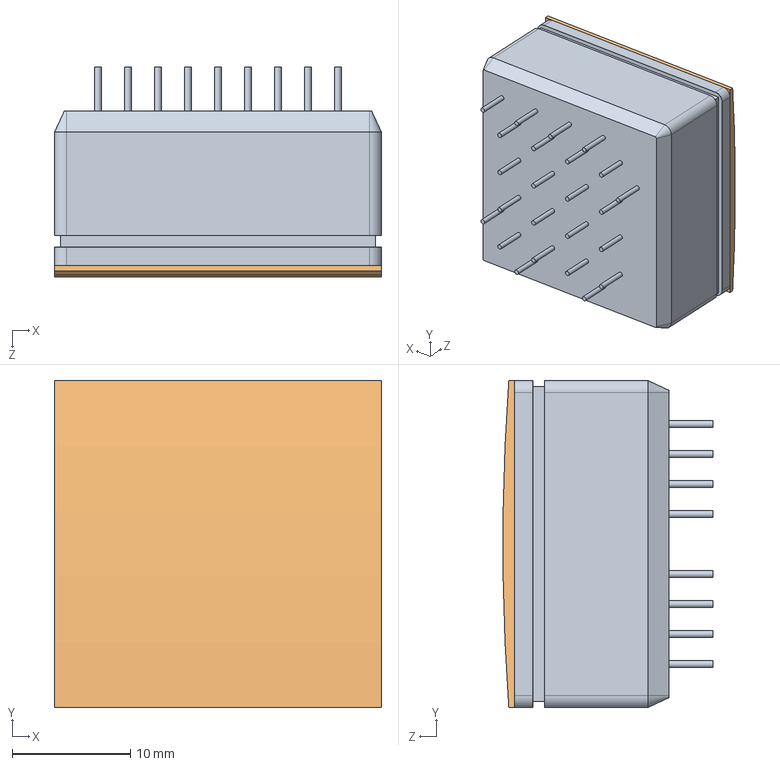
[picture p129: CAD file, 2013-10-08]
mechanical-designs/board-stack/iTOP/PMT-with-cookie.SLDASM
27.7 x 27.7 x 17.8 mm
SL10.4x4
cookie
