mzandrew/idlab-scrod/mechanical-designs/board-stack/mTC/mTC.12PMTs.SLDASM

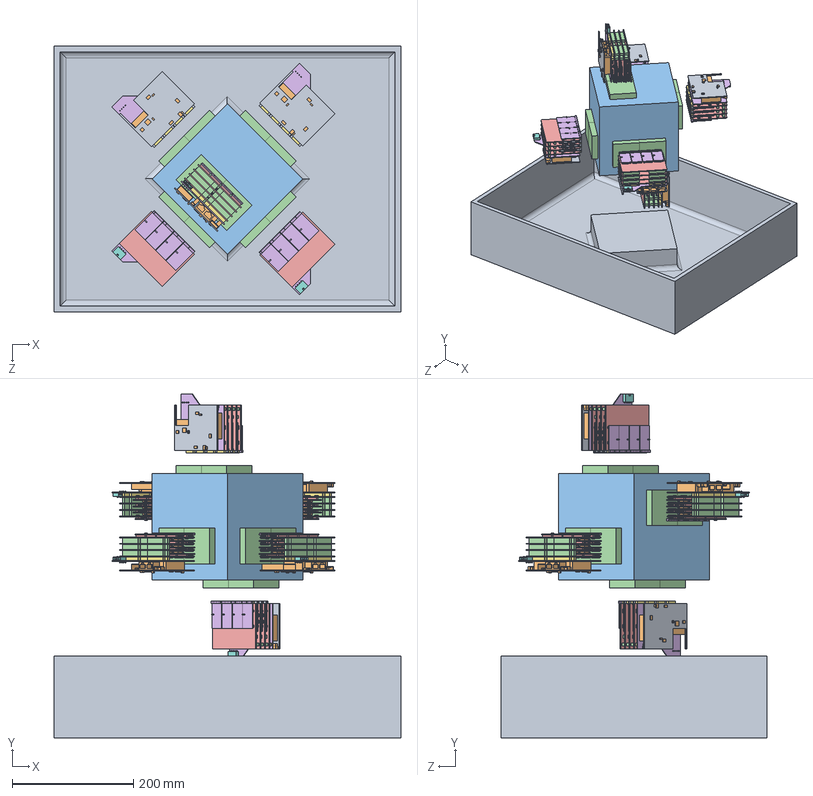
[picture p130: CAD file, 2012-04-03]
mechanical-designs/board-stack/mTC/mTC.12PMTs.SLDASM
572.5 x 566.8 x 439.1 mm
enclosure.bottom
scintillator
polyoxymethylene.2PMTs x 6
planacon-XP85012-A1 x 12
carrier.common x 24
IRS2_DC.revB x 24
connector.2mm.16-pin.female x 96
carrier04-capacitors x 12
IRS3_DC.revA x 72
IRS3_DC.heatsink x 72
1206.inductor x 144
board-interconnects.100-and-120-pin.9mm x 18
carrier12-capacitors x 12
interconnect.revB x 6
board-interconnects.100-and-120-pin.6mm x 6
mini-fit-jr.right-angle.4-position x 6
SCROD.revA x 6
SCROD.components x 6
