mzandrew/idlab-scrod/mechanical-designs/board-stack/iTOP/PMT-with-filter-and-coupling.SLDASM

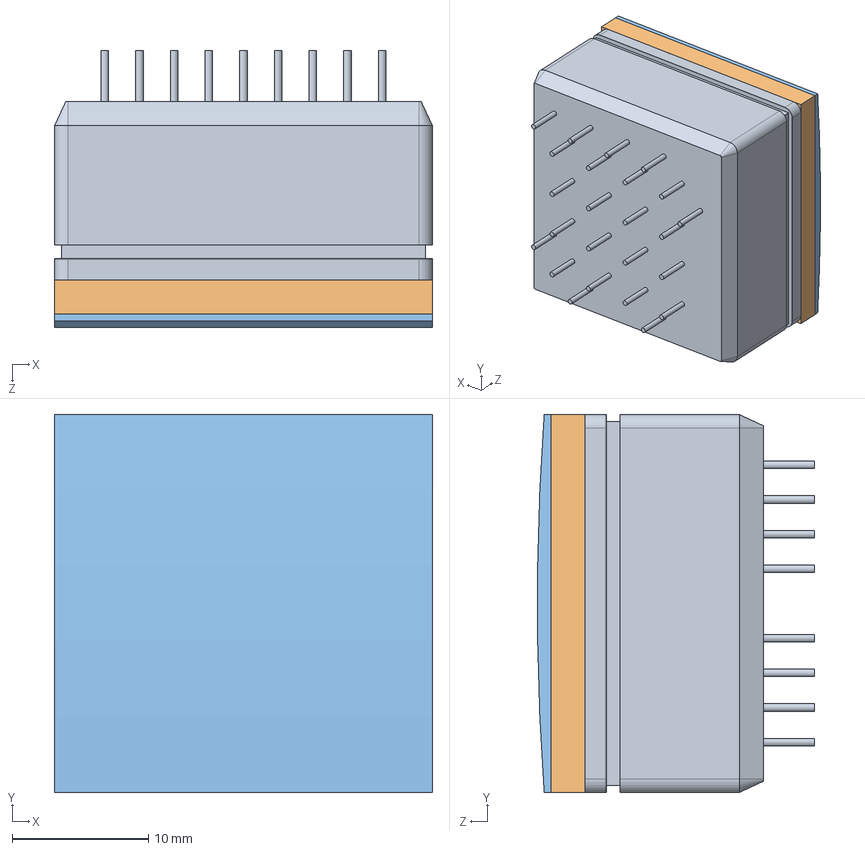
[picture p131: CAD file, 2013-10-08]
mechanical-designs/board-stack/iTOP/PMT-with-filter-and-coupling.SLDASM
27.7 x 27.7 x 20.3 mm
SL10.4x4
filter
cookie
