mzandrew/idlab-scrod/mechanical-designs/board-stack/iTOP/pogo-plate.HV.SLDASM

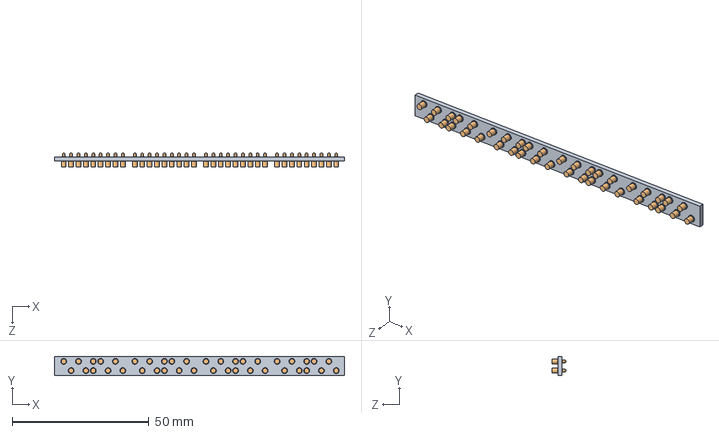
[picture p132: CAD file, 2013-10-08]
mechanical-designs/board-stack/iTOP/pogo-plate.HV.SLDASM
106.0 x 7.00 x 5.21 mm
pogo-plate
pogo-pin.millmax-0926-1 x 40
