mzandrew/idlab-scrod/mechanical-designs/board-stack/IRS2_DC.revB/IRS2_DC.revB.SLDPRT

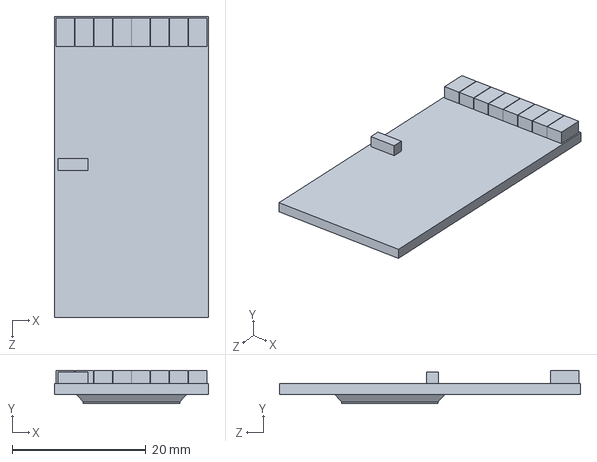
[picture p134: CAD file, 2012-04-11]
mechanical-designs/board-stack/IRS2_DC.revB/IRS2_DC.revB.SLDPRT
23.0 x 4.99 x 45.0 mm
