mzandrew/idlab-scrod/mechanical-designs/board-stack/IRS2_DC.revB2/export/IRS2_DC.revB2.16.heatsink.STEP

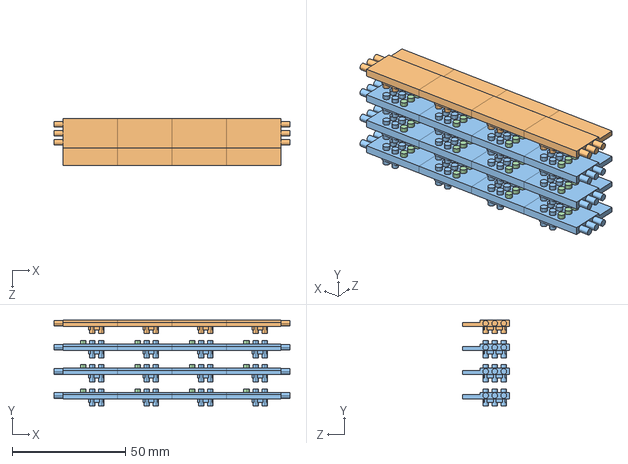
[picture p135: CAD file, 2013-01-11]
mechanical-designs/board-stack/IRS2_DC.revB2/export/IRS2_DC.revB2.16.heatsink.STEP
104.0 x 37.8 x 20.8 mm
IRS2_DC.revB2.heatsink x 16
