mzandrew/idlab-scrod/mechanical-designs/board-stack/IRS3_DC.revA/export/IRS3_DC.heatsink.STEP

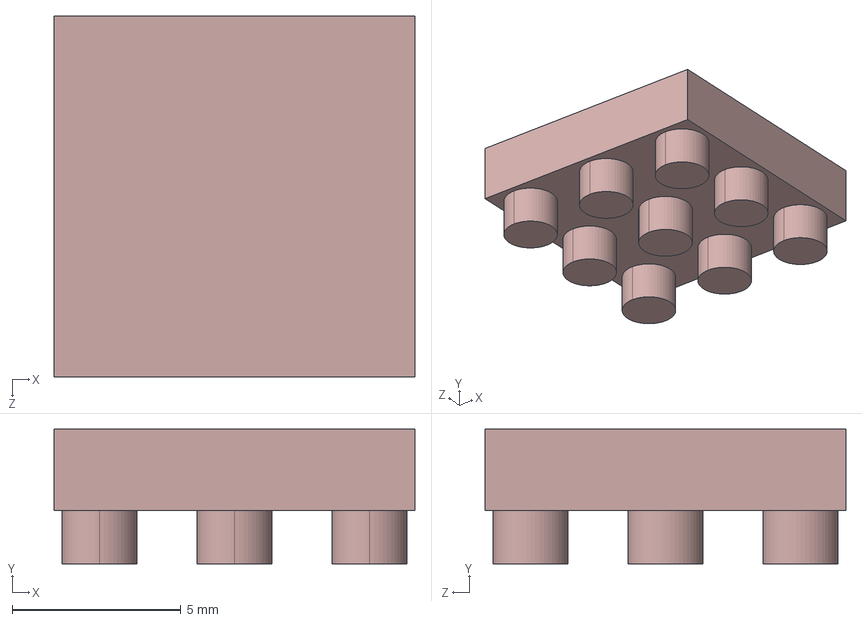
[picture p136: CAD file, 2012-03-23]
mechanical-designs/board-stack/IRS3_DC.revA/export/IRS3_DC.heatsink.STEP
10.7 x 4.00 x 10.7 mm
