mzandrew/idlab-scrod/mechanical-designs/board-stack/iTOP/contrib/SL10-HV-module.revA.IU.bottom-platerev bc.SLDPRT

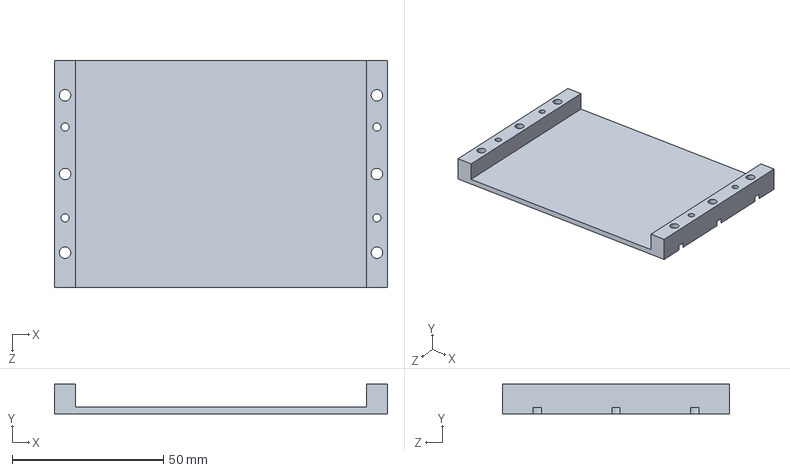
[picture p137: CAD file, 2014-05-03]
mechanical-designs/board-stack/iTOP/contrib/SL10-HV-module.revA.IU.bottom-platerev bc.SLDPRT
110.0 x 9.80 x 75.0 mm
