mzandrew/idlab-scrod/mechanical-designs/board-stack/iTOP/CRT/HV-panel-holder.SLDPRT

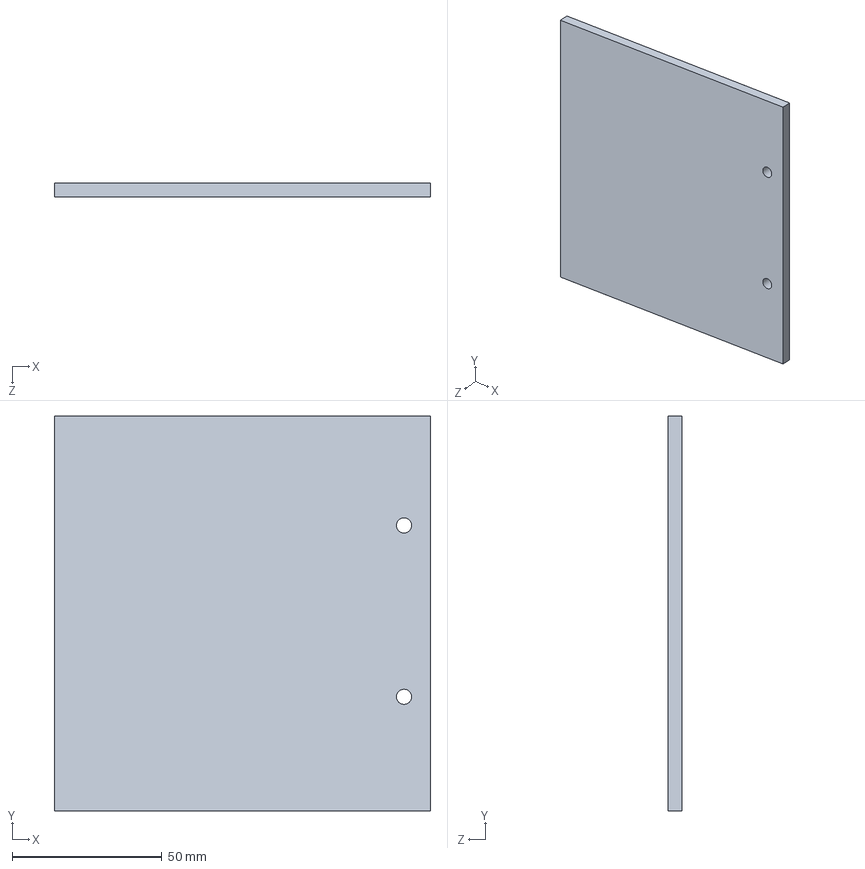
[picture p138: CAD file, 2013-03-19]
mechanical-designs/board-stack/iTOP/CRT/HV-panel-holder.SLDPRT
125.5 x 131.8 x 4.76 mm
