mzandrew/idlab-scrod/mechanical-designs/board-stack/iTOP/export/board-spacers.15.75mm-middle-for-intermediate-Al.STEP

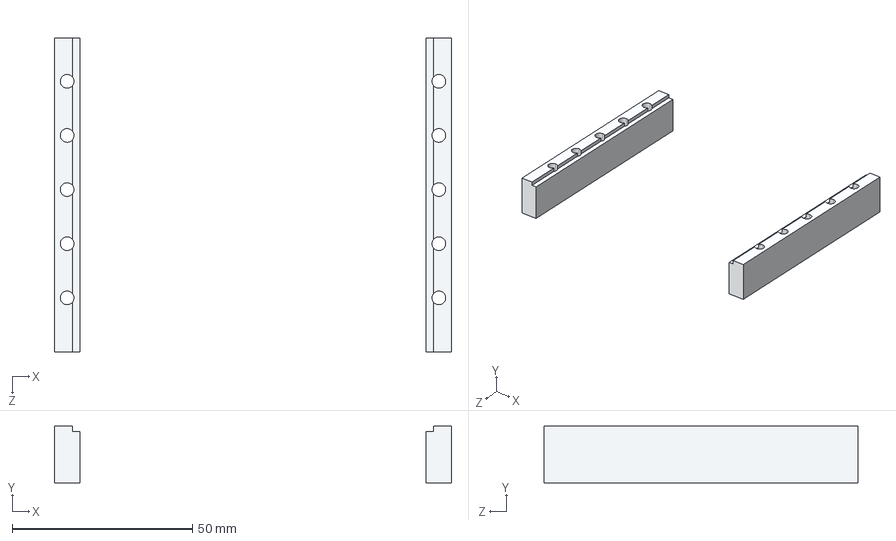
[picture p139: CAD file, 2014-02-25]
mechanical-designs/board-stack/iTOP/export/board-spacers.15.75mm-middle-for-intermediate-Al.STEP
110.0 x 15.8 x 87.0 mm
