mzandrew/idlab-scrod/mechanical-designs/common-components/boxes/bud-10x8x2.5-try2.SLDPRT

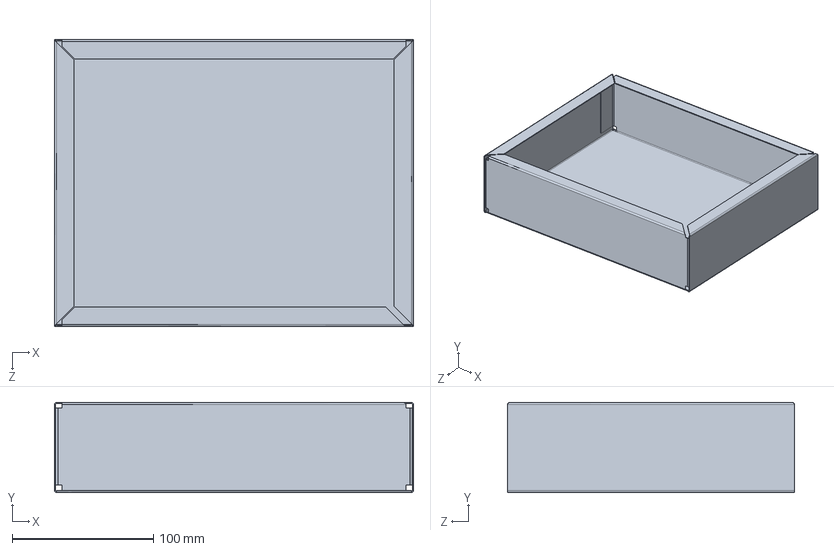
[picture p140: CAD file, 2013-10-08]
mechanical-designs/common-components/boxes/bud-10x8x2.5-try2.SLDPRT
254.0 x 63.9 x 203.2 mm
