mzandrew/idlab-scrod/mechanical-designs/common-components/connectors/fiber-cage.single-wide.SLDPRT

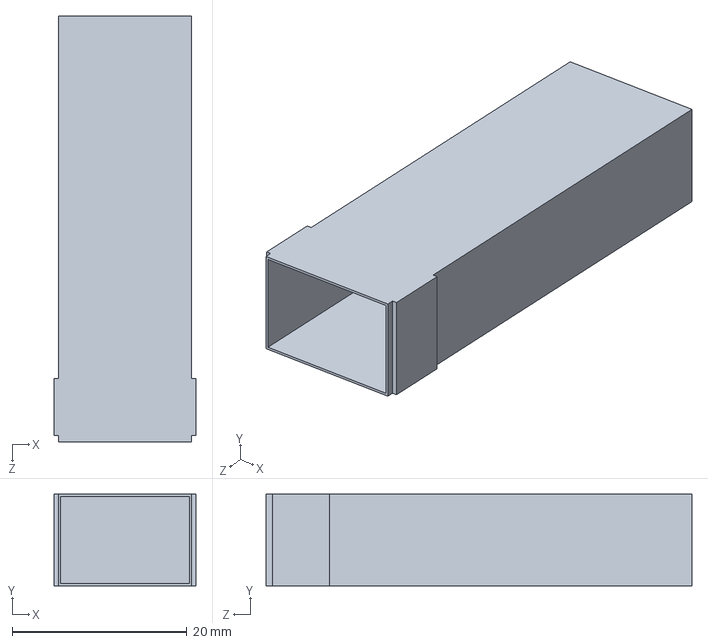
[picture p141: CAD file, 2014-05-03]
mechanical-designs/common-components/connectors/fiber-cage.single-wide.SLDPRT
16.2 x 10.5 x 48.8 mm
