mzandrew/idlab-scrod/mechanical-designs/common-components/integrated-circuits/TQFP-128.SLDPRT

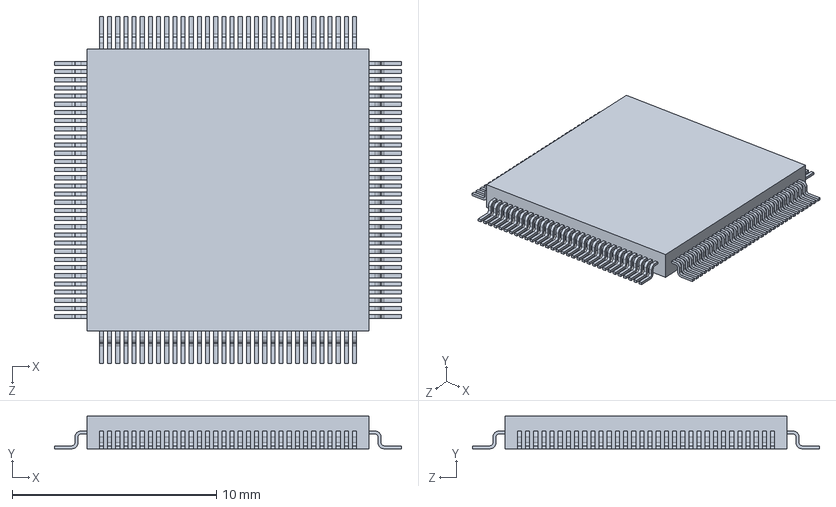
[picture p142: CAD file, 2014-05-03]
mechanical-designs/common-components/integrated-circuits/TQFP-128.SLDPRT
17.0 x 1.60 x 17.0 mm
