mzandrew/idlab-scrod/mechanical-designs/common-components/pogo-pin.millmax-0926-1.SLDPRT

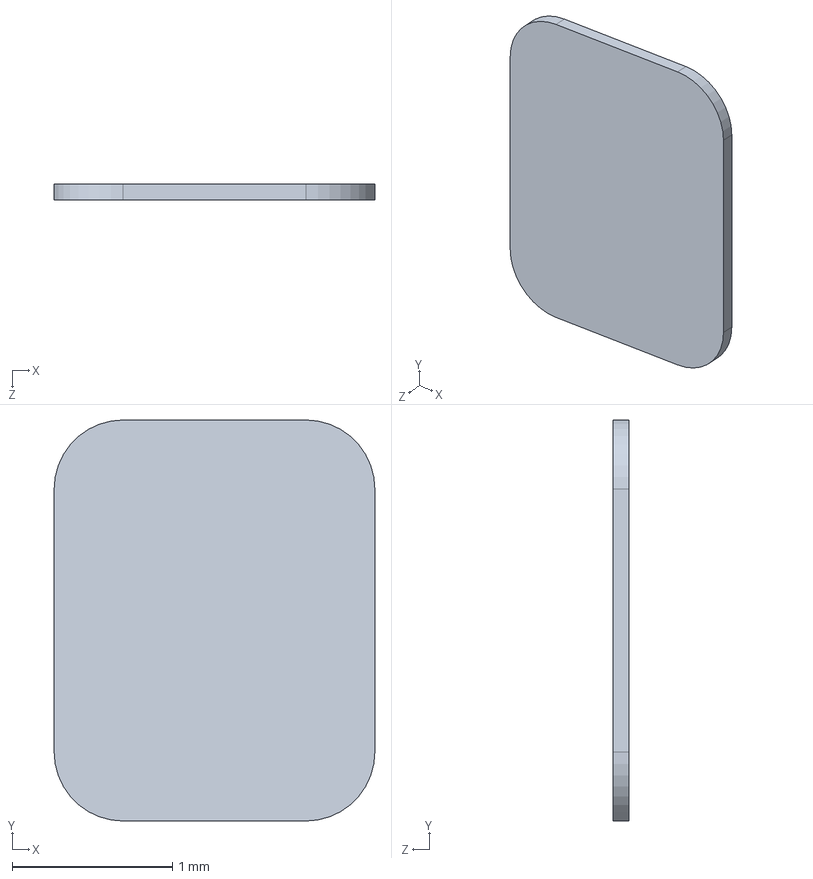
[picture p143: CAD file, 2014-02-25]
mechanical-designs/common-components/pogo-pin.millmax-0926-1.SLDPRT
2.00 x 2.50 x 0.1 mm
