mzandrew/idlab-scrod/mechanical-designs/COPPER/COPPER-CRATE.SLDPRT

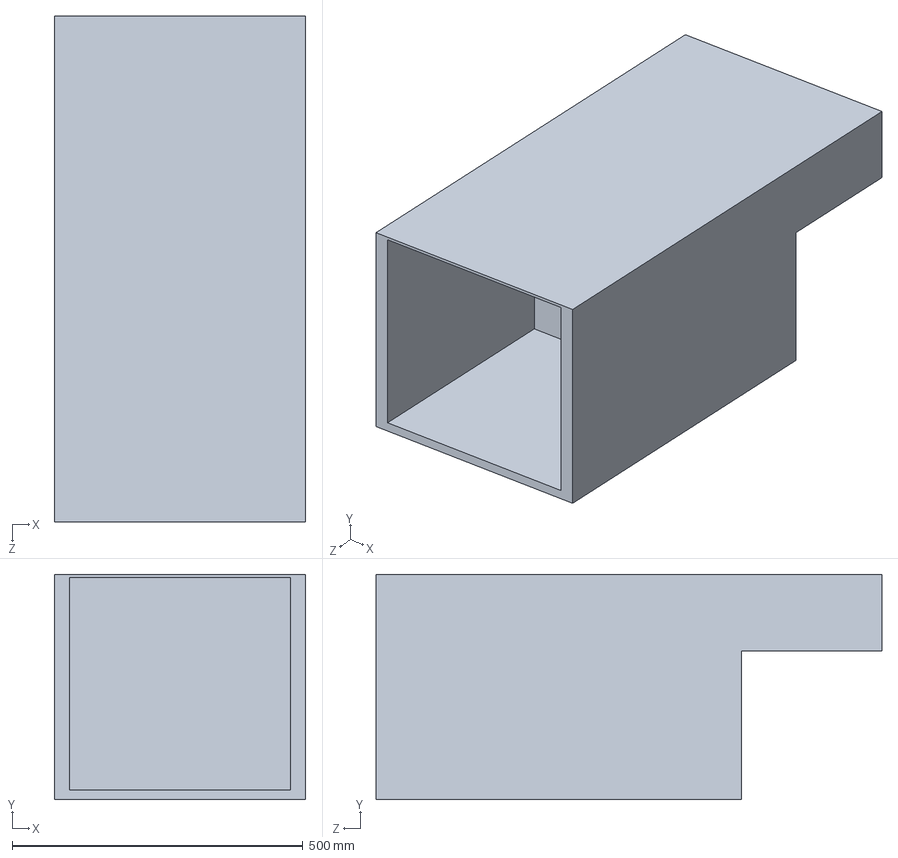
[picture p144: CAD file, 2014-02-25]
mechanical-designs/COPPER/COPPER-CRATE.SLDPRT
431.8 x 387.4 x 869.7 mm
