mzandrew/idlab-scrod/mechanical-designs/other/raspberry-pi-mount.SLDPRT

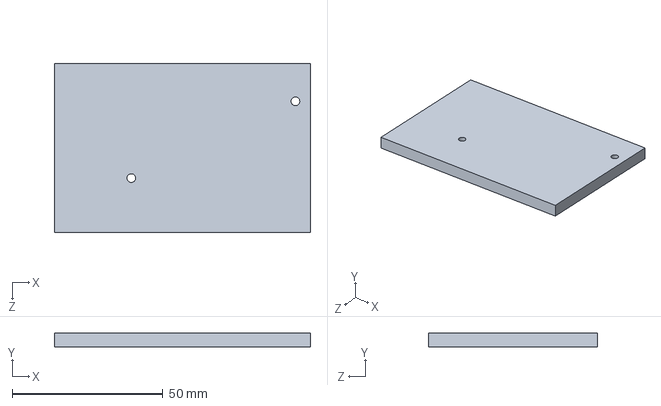
[picture p145: CAD file, 2014-02-25]
mechanical-designs/other/raspberry-pi-mount.SLDPRT
85.0 x 4.76 x 56.0 mm
