mzandrew/idlab-scrod/mechanical-designs/tags/r282.iTOP-module-used-at-LEPS-SPRING8/board-stack/carriers/export/carrier02.revB.PCB.STEP

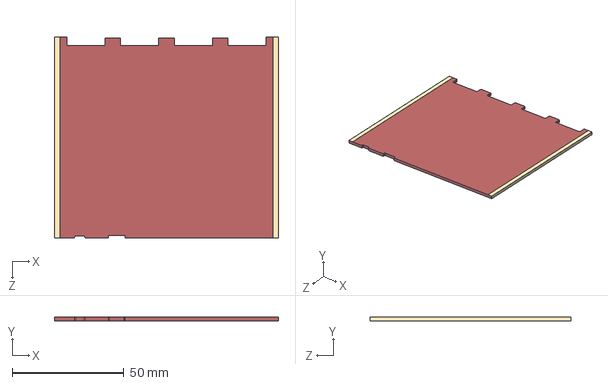
[picture p146: CAD file, 2013-01-11]
mechanical-designs/tags/r282.iTOP-module-used-at-LEPS-SPRING8/board-stack/carriers/export/carrier02.revB.PCB.STEP
100.1 x 1.69 x 90.0 mm
