mzandrew/idlab-scrod/mechanical-designs/tags/r282.iTOP-module-used-at-LEPS-SPRING8/board-stack/export/interconnect.revB.STEP

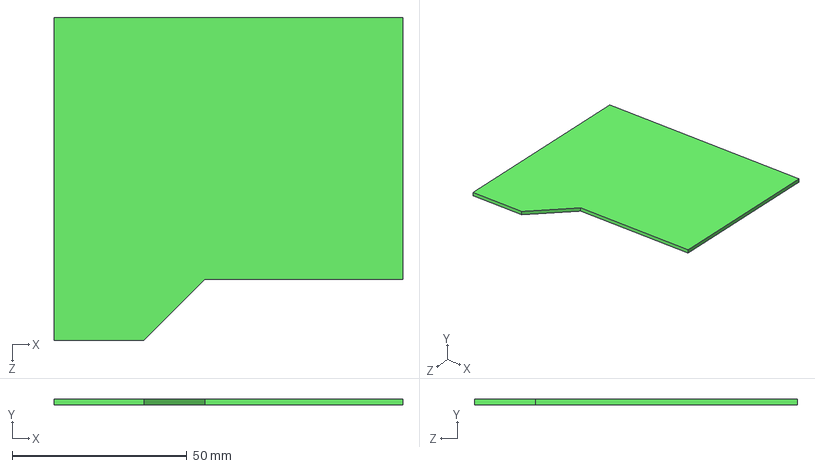
[picture p147: CAD file, 2013-01-11]
mechanical-designs/tags/r282.iTOP-module-used-at-LEPS-SPRING8/board-stack/export/interconnect.revB.STEP
100.0 x 1.59 x 92.5 mm
