mzandrew/idlab-scrod/mechanical-designs/tags/r282.iTOP-module-used-at-LEPS-SPRING8/board-stack/frames/simple-frame.right.sldprt

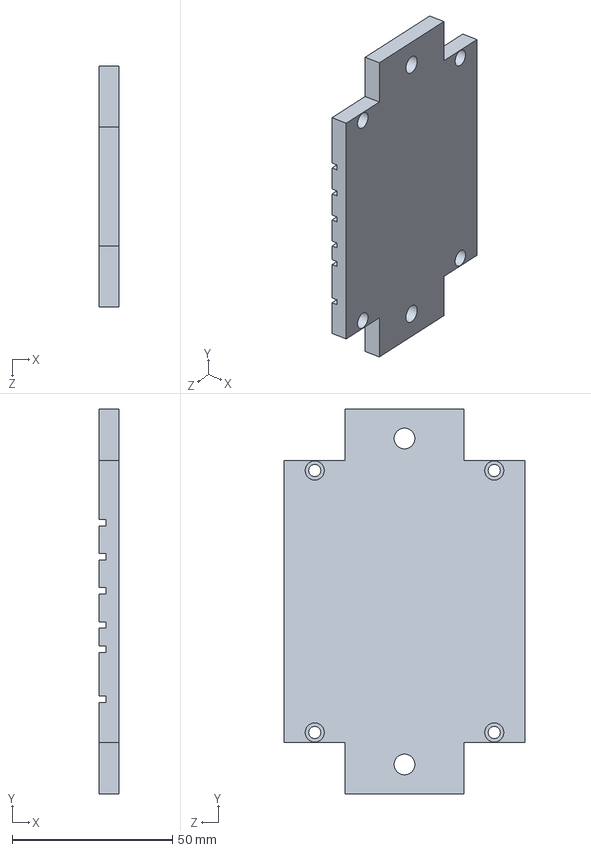
[picture p148: CAD file, 2013-01-11]
mechanical-designs/tags/r282.iTOP-module-used-at-LEPS-SPRING8/board-stack/frames/simple-frame.right.sldprt
6.35 x 120.0 x 75.0 mm
