mzandrew/idlab-scrod/mechanical-designs/tags/r282.iTOP-module-used-at-LEPS-SPRING8/board-stack/iTOP/export/front-back.revC.STEP

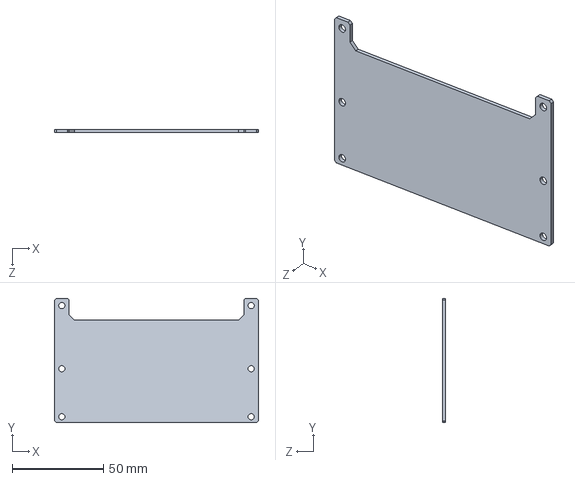
[picture p149: CAD file, 2013-01-31]
mechanical-designs/tags/r282.iTOP-module-used-at-LEPS-SPRING8/board-stack/iTOP/export/front-back.revC.STEP
111.5 x 68.0 x 1.69 mm
