mzandrew/idlab-scrod/mechanical-designs/tags/r282.iTOP-module-used-at-LEPS-SPRING8/common-components/connectors/2mm/connector.2mm.16-pin.female.SLDPRT

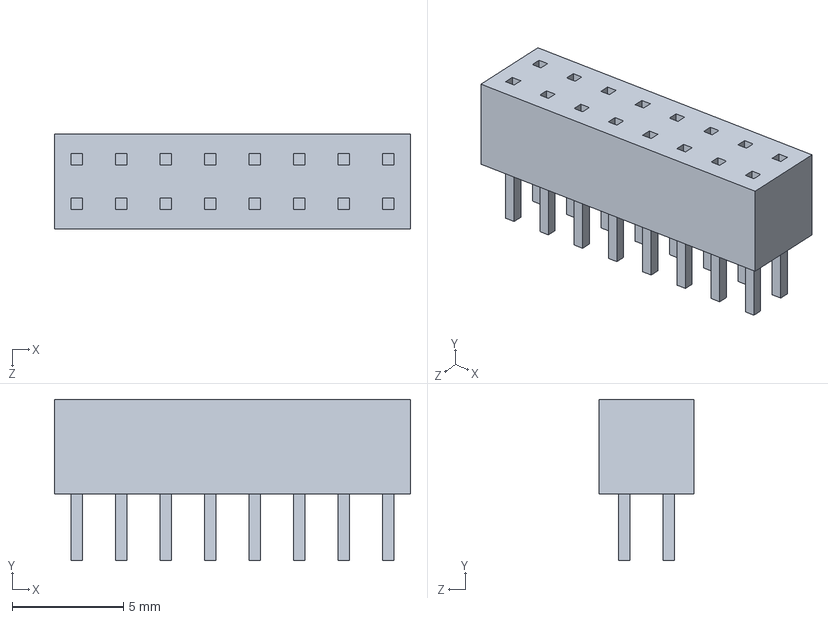
[picture p150: CAD file, 2013-11-14]
mechanical-designs/tags/r282.iTOP-module-used-at-LEPS-SPRING8/common-components/connectors/2mm/connector.2mm.16-pin.female.SLDPRT
16.0 x 7.25 x 4.25 mm
