mzandrew/idlab-scrod/mechanical-designs/tags/r282.iTOP-module-used-at-LEPS-SPRING8/common-components/integrated-circuits/5mm-by-7mm.oscillator.SLDPRT

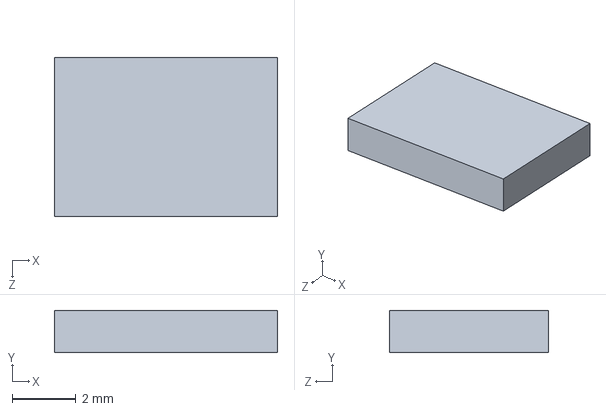
[picture p151: CAD file, 2013-11-14]
mechanical-designs/tags/r282.iTOP-module-used-at-LEPS-SPRING8/common-components/integrated-circuits/5mm-by-7mm.oscillator.SLDPRT
7.00 x 1.32 x 5.00 mm
