mzandrew/idlab-scrod/mechanical-designs/tags/r282.iTOP-module-used-at-LEPS-SPRING8/common-components/optical-table.SLDPRT

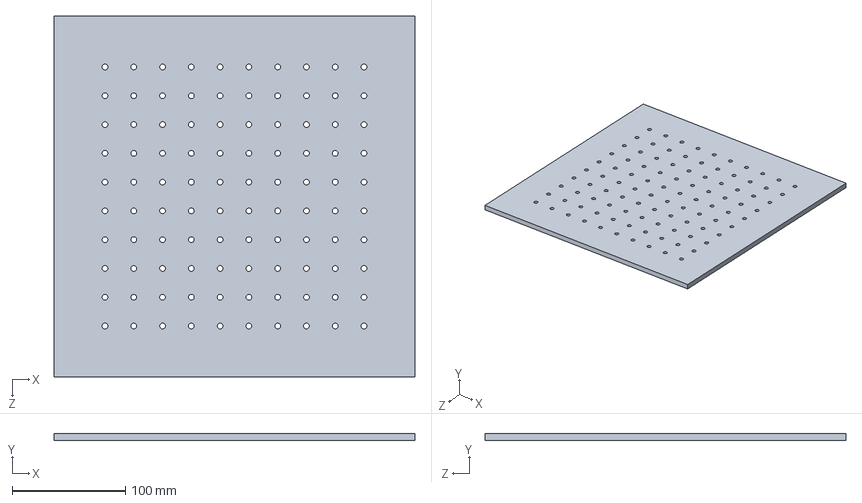
[picture p152: CAD file, 2013-02-11]
mechanical-designs/tags/r282.iTOP-module-used-at-LEPS-SPRING8/common-components/optical-table.SLDPRT
318.6 x 6.35 x 318.6 mm
