mzandrew/idlab-scrod/mechanical-designs/board-stack/carriers/carrier0.revA.SLDPRT

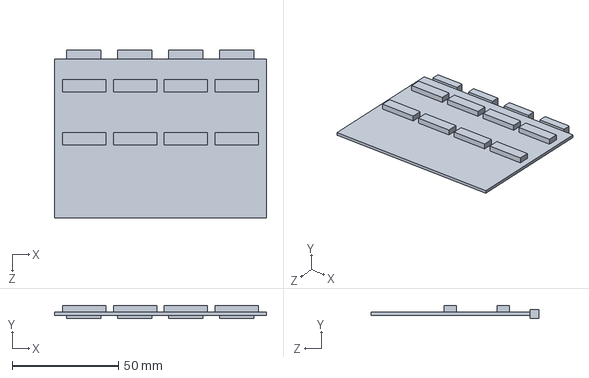
[picture p153: CAD file, 2012-03-23]
mechanical-designs/board-stack/carriers/carrier0.revA.SLDPRT
100.0 x 5.96 x 79.4 mm
