mzandrew/idlab-scrod/mechanical-designs/board-stack/fDIRC/mechanical-mount-for-6-boardstacks/bottom_strip.sldprt

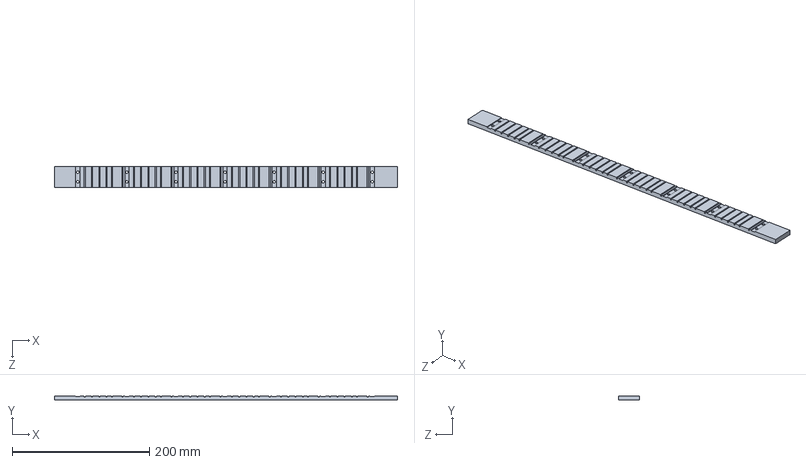
[picture p154: CAD file, 2012-07-12]
mechanical-designs/board-stack/fDIRC/mechanical-mount-for-6-boardstacks/bottom_strip.sldprt
500.0 x 6.35 x 30.0 mm
