mzandrew/idlab-scrod/mechanical-designs/board-stack/IRS2_DC.revB2/IRS2_DC.revB2.heatsink.SLDPRT

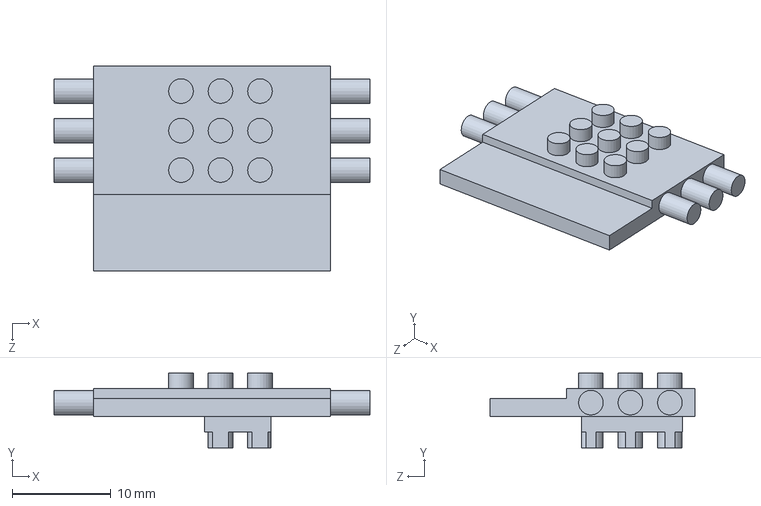
[picture p156: CAD file, 2013-01-11]
mechanical-designs/board-stack/IRS2_DC.revB2/IRS2_DC.revB2.heatsink.SLDPRT
32.0 x 7.55 x 20.8 mm
