mzandrew/idlab-scrod/mechanical-designs/board-stack/IRS3_DC.revA/export/IRS3_DC.heatsink.2.5mm.STEP

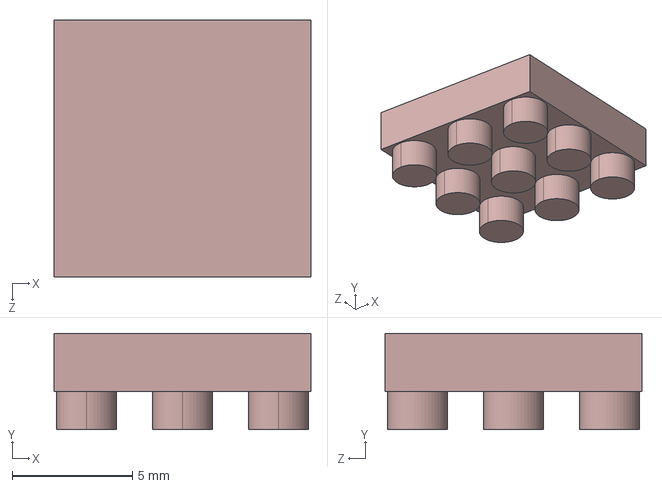
[picture p157: CAD file, 2012-03-23]
mechanical-designs/board-stack/IRS3_DC.revA/export/IRS3_DC.heatsink.2.5mm.STEP
10.7 x 4.00 x 10.7 mm
