mzandrew/idlab-scrod/mechanical-designs/board-stack/IRS3_DC.revA/IRS3_DC.revA.SLDPRT

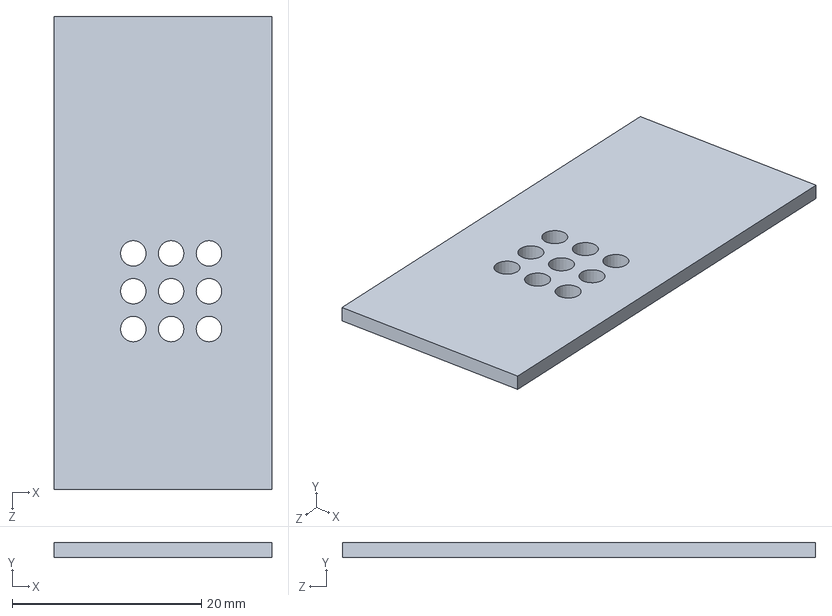
[picture p158: CAD file, 2012-03-23]
mechanical-designs/board-stack/IRS3_DC.revA/IRS3_DC.revA.SLDPRT
23.0 x 1.59 x 50.0 mm
