mzandrew/idlab-scrod/mechanical-designs/board-stack/iTOP/export/board-spacers.3mm-bottom-for-intermediate-SS.STEP

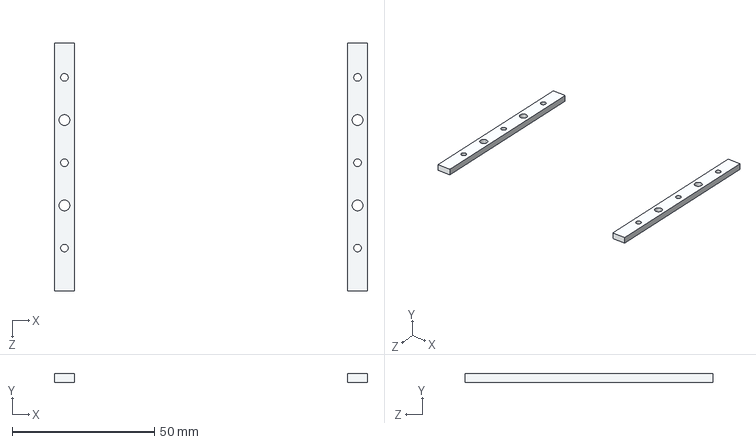
[picture p159: CAD file, 2014-02-25]
mechanical-designs/board-stack/iTOP/export/board-spacers.3mm-bottom-for-intermediate-SS.STEP
110.0 x 3.00 x 87.0 mm
