mzandrew/idlab-scrod/mechanical-designs/common-components/connectors/fiber-transceiver.SLDPRT

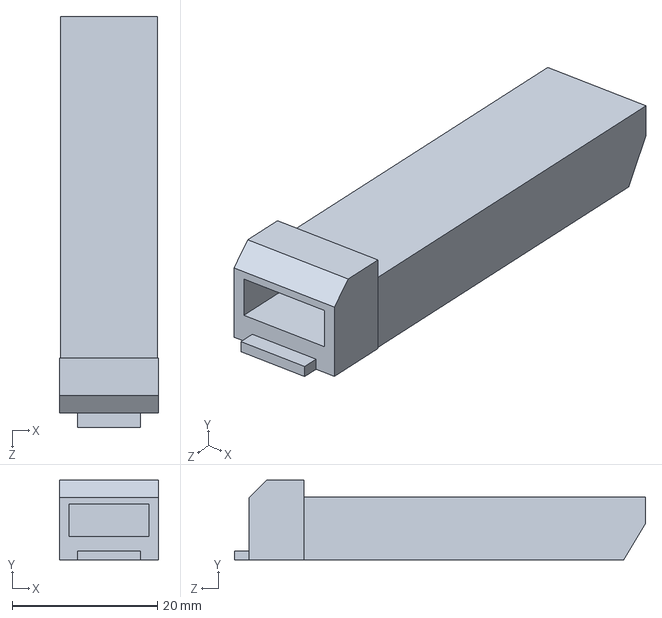
[picture p160: CAD file, 2014-05-03]
mechanical-designs/common-components/connectors/fiber-transceiver.SLDPRT
13.7 x 11.0 x 56.6 mm
