mzandrew/idlab-scrod/mechanical-designs/COPPER/COPPER-PCB.9U-VME.SLDPRT

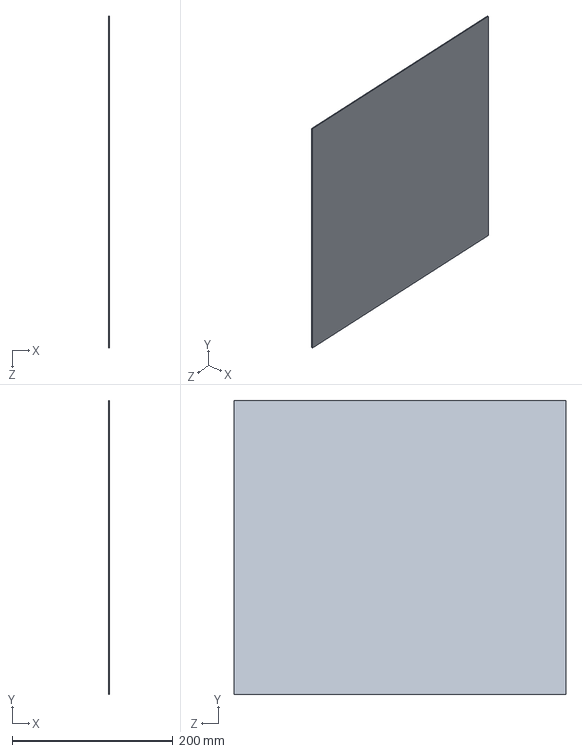
[picture p161: CAD file, 2014-02-25]
mechanical-designs/COPPER/COPPER-PCB.9U-VME.SLDPRT
1.59 x 365.8 x 412.5 mm
