mzandrew/idlab-scrod/mechanical-designs/tags/r282.iTOP-module-used-at-LEPS-SPRING8/board-stack/carriers/carrier13.revB.PCB.SLDPRT

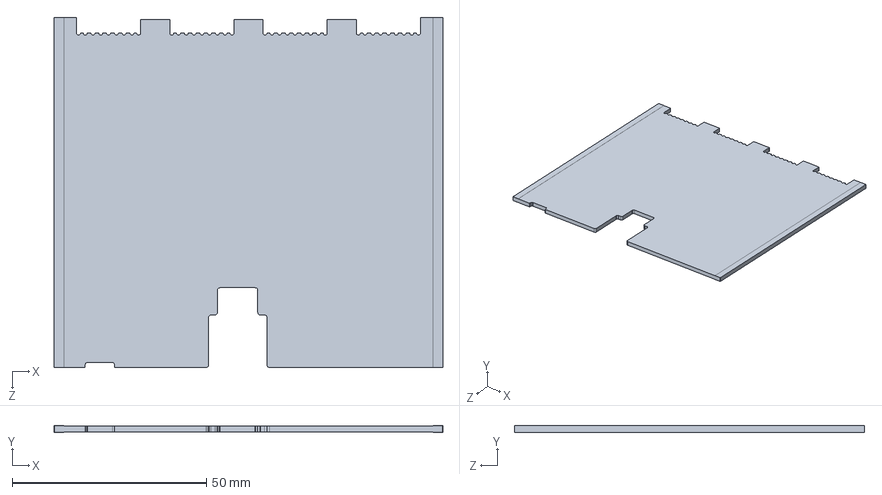
[picture p162: CAD file, 2013-11-14]
mechanical-designs/tags/r282.iTOP-module-used-at-LEPS-SPRING8/board-stack/carriers/carrier13.revB.PCB.SLDPRT
100.1 x 1.69 x 90.1 mm
