mzandrew/idlab-scrod/mechanical-designs/tags/r282.iTOP-module-used-at-LEPS-SPRING8/board-stack/frames/simple-frame.left.sldprt

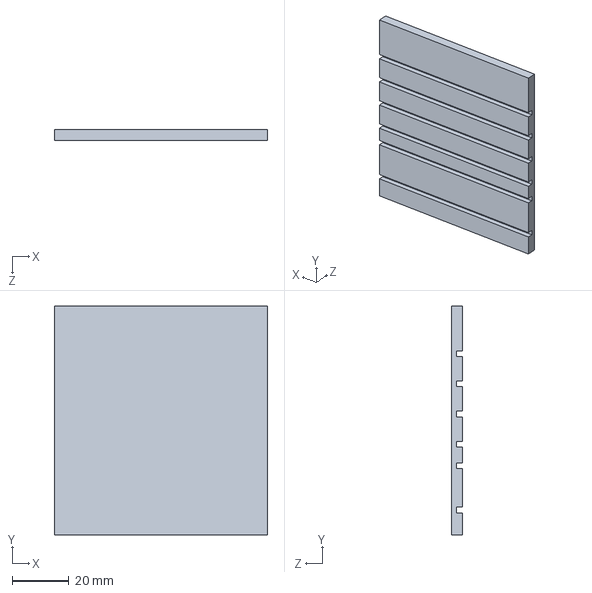
[picture p163: CAD file, 2013-01-11]
mechanical-designs/tags/r282.iTOP-module-used-at-LEPS-SPRING8/board-stack/frames/simple-frame.left.sldprt
75.0 x 80.6 x 4.00 mm
