mzandrew/idlab-scrod/mechanical-designs/tags/r282.iTOP-module-used-at-LEPS-SPRING8/board-stack/iTOP/export/SL10.4x4.STEP

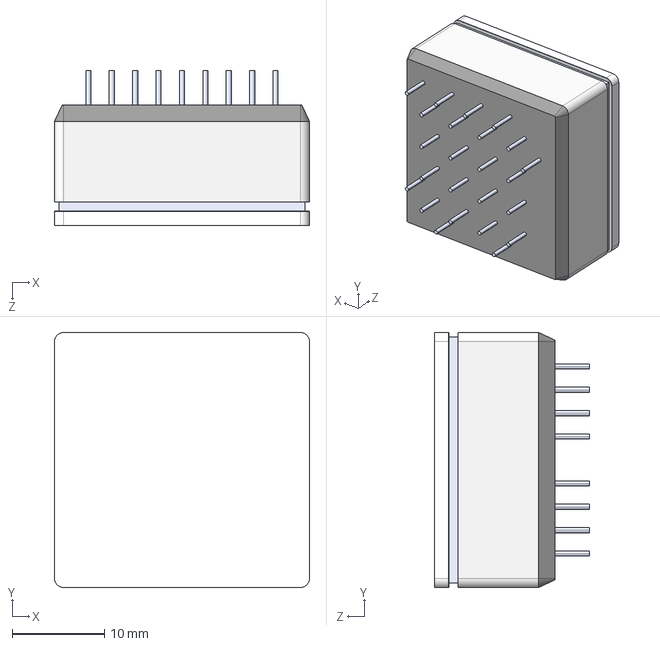
[picture p164: CAD file, 2013-01-31]
mechanical-designs/tags/r282.iTOP-module-used-at-LEPS-SPRING8/board-stack/iTOP/export/SL10.4x4.STEP
27.7 x 27.7 x 16.8 mm
