mzandrew/idlab-scrod/mechanical-designs/tags/r282.iTOP-module-used-at-LEPS-SPRING8/common-components/angle-aluminum.SLDPRT

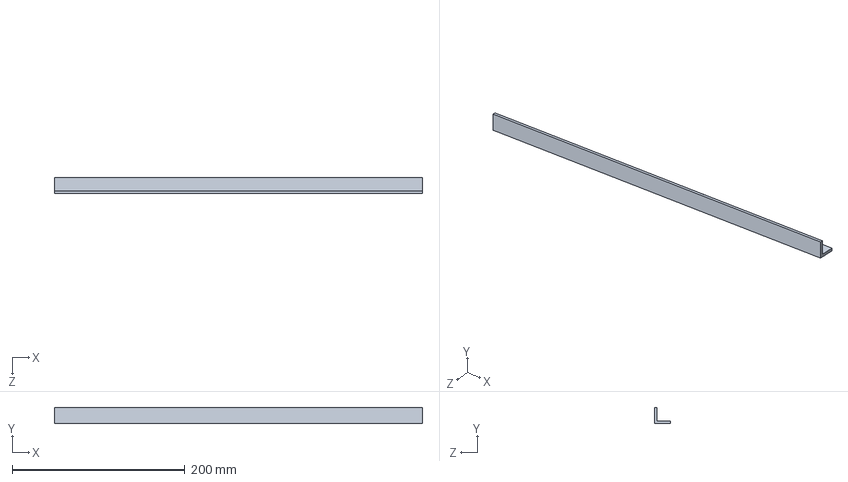
[picture p165: CAD file, 2012-03-29]
mechanical-designs/tags/r282.iTOP-module-used-at-LEPS-SPRING8/common-components/angle-aluminum.SLDPRT
426.0 x 19.1 x 19.1 mm
