mzandrew/idlab-scrod/mechanical-designs/tags/r282.iTOP-module-used-at-LEPS-SPRING8/common-components/connectors/2mm/14-pin.2mm.jtag-header.right-angle.SLDPRT

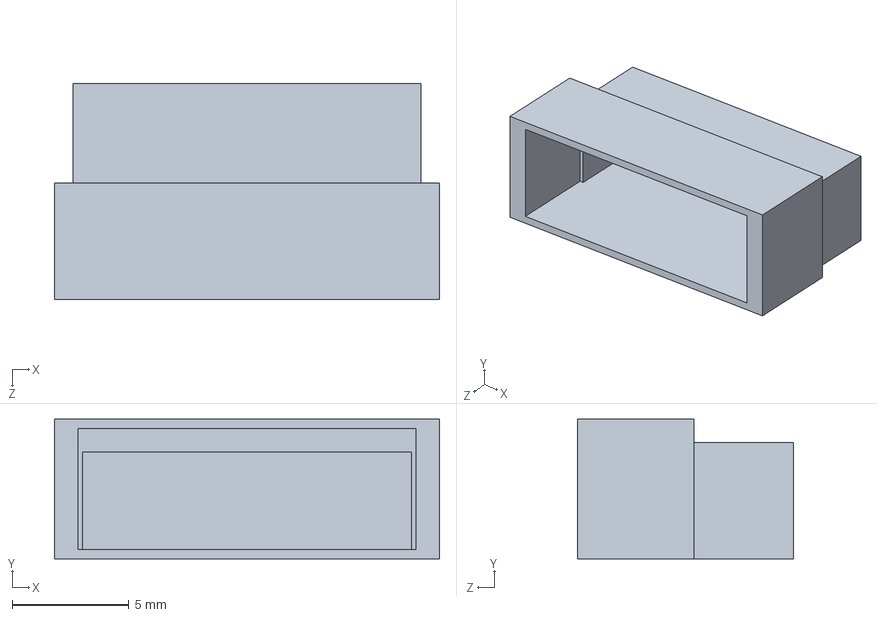
[picture p166: CAD file, 2013-11-14]
mechanical-designs/tags/r282.iTOP-module-used-at-LEPS-SPRING8/common-components/connectors/2mm/14-pin.2mm.jtag-header.right-angle.SLDPRT
16.5 x 6.00 x 9.25 mm
