mzandrew/idlab-scrod/mechanical-designs/tags/r282.iTOP-module-used-at-LEPS-SPRING8/common-components/jigs/16pin-2mm-pin-puller.STEP

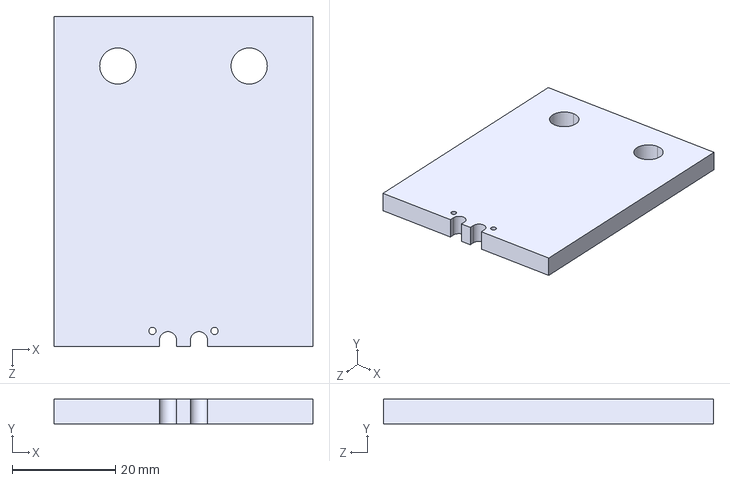
[picture p167: CAD file, 2013-02-11]
mechanical-designs/tags/r282.iTOP-module-used-at-LEPS-SPRING8/common-components/jigs/16pin-2mm-pin-puller.STEP
50.0 x 4.76 x 63.8 mm
