mzandrew/idlab-scrod/mechanical-designs/board-stack/carriers/carrier04-capacitors.SLDPRT

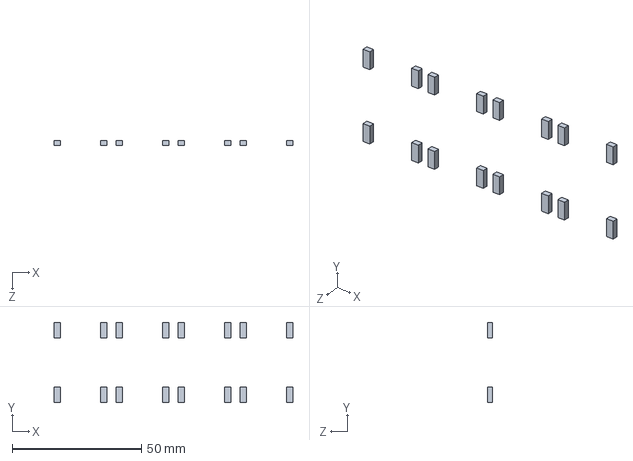
[picture p168: CAD file, 2012-03-23]
mechanical-designs/board-stack/carriers/carrier04-capacitors.SLDPRT
92.5 x 31.0 x 1.78 mm
