mzandrew/idlab-scrod/mechanical-designs/board-stack/fDIRC/existing-support-structure/G10-PMT-support.SLDPRT

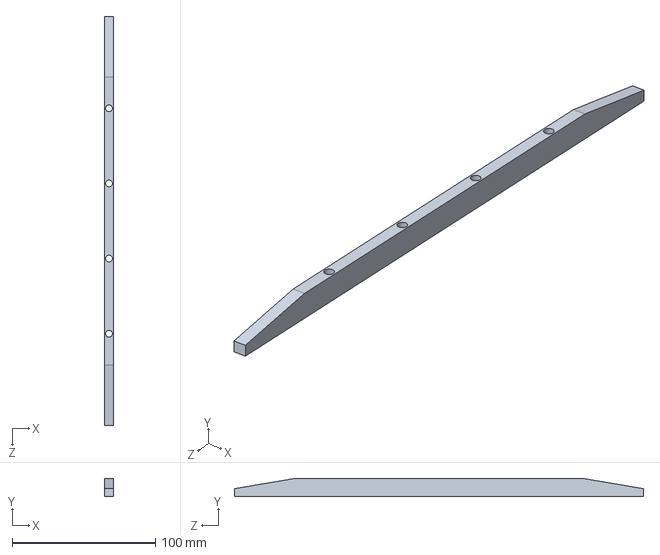
[picture p169: CAD file, 2012-03-30]
mechanical-designs/board-stack/fDIRC/existing-support-structure/G10-PMT-support.SLDPRT
6.35 x 12.7 x 285.7 mm
