mzandrew/idlab-scrod/mechanical-designs/board-stack/fDIRC/export/frame-for-fDIRC-laser-scan.STEP

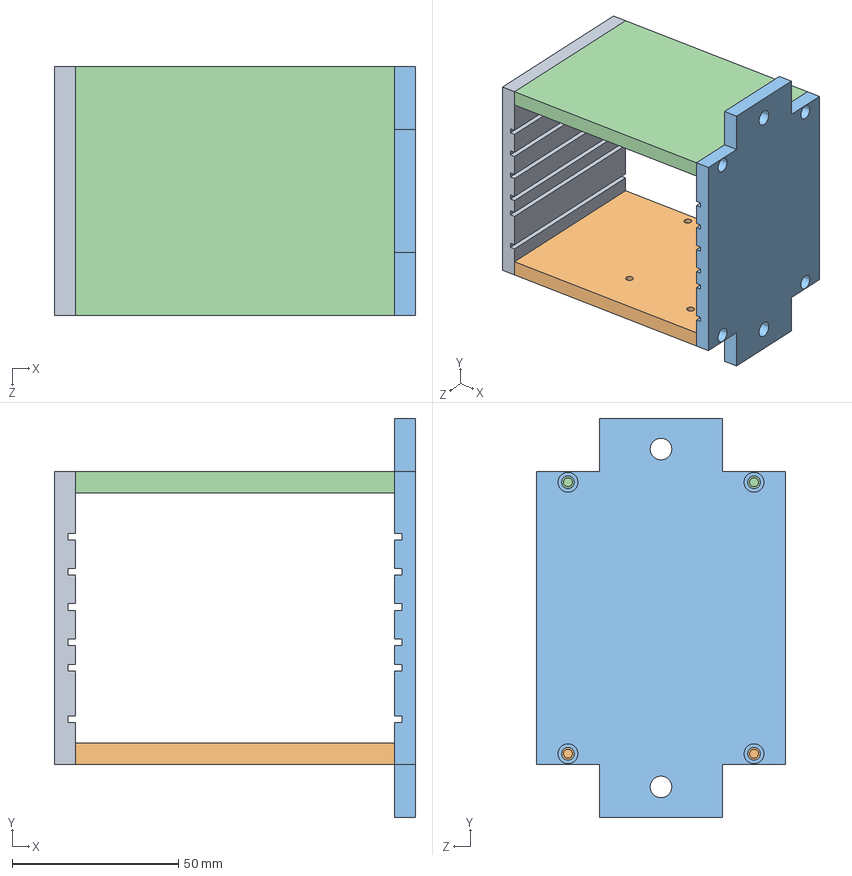
[picture p170: CAD file, 2012-06-02]
mechanical-designs/board-stack/fDIRC/export/frame-for-fDIRC-laser-scan.STEP
108.7 x 120.0 x 75.0 mm
simple-frame.left
simple-frame.bottom
simple-frame.right
simple-frame.top
