mzandrew/idlab-scrod/mechanical-designs/board-stack/iTOP/CRT/CRT-leg.SLDPRT

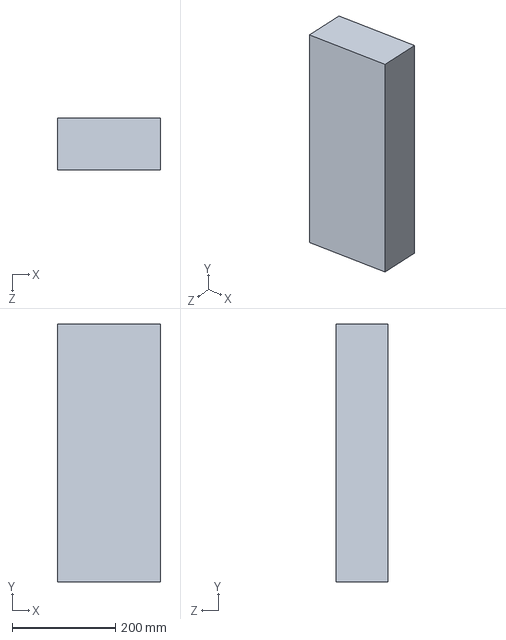
[picture p171: CAD file, 2013-03-11]
mechanical-designs/board-stack/iTOP/CRT/CRT-leg.SLDPRT
200.0 x 500.0 x 100.0 mm
