mzandrew/idlab-scrod/mechanical-designs/board-stack/iTOP/export/board-spacers.15.75mm-middle-for-intermediate-Al.right.STEP

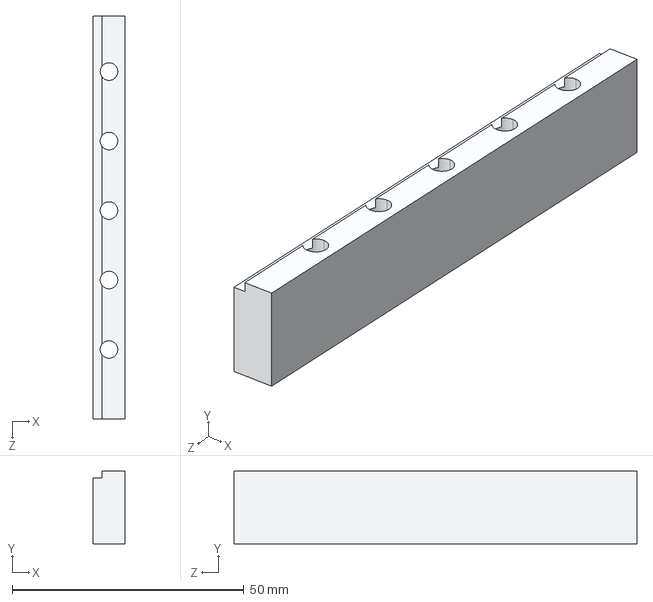
[picture p172: CAD file, 2014-02-25]
mechanical-designs/board-stack/iTOP/export/board-spacers.15.75mm-middle-for-intermediate-Al.right.STEP
7.00 x 15.8 x 87.0 mm
