mzandrew/idlab-scrod/mechanical-designs/common-components/1206.capacitor.SLDPRT

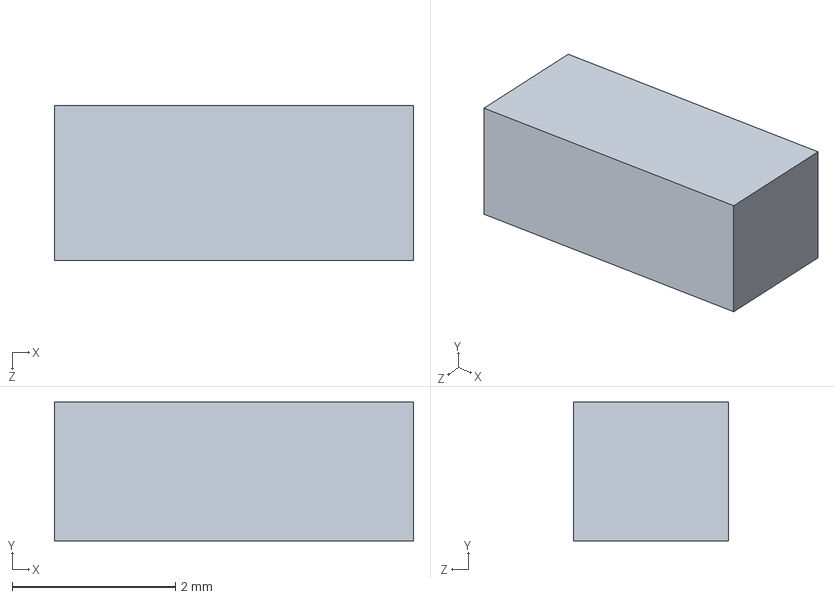
[picture p173: CAD file, 2013-11-08]
mechanical-designs/common-components/1206.capacitor.SLDPRT
4.40 x 1.70 x 1.90 mm
