mzandrew/idlab-scrod/mechanical-designs/tags/r282.iTOP-module-used-at-LEPS-SPRING8/board-stack/frames/simple-frame.SLDASM

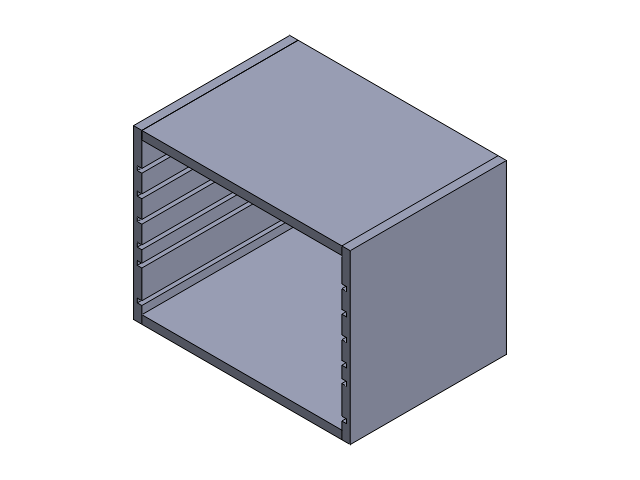
[picture p174: CAD file, 2013-01-11]
mechanical-designs/tags/r282.iTOP-module-used-at-LEPS-SPRING8/board-stack/frames/simple-frame.SLDASM
simple-frame.left
simple-frame.bottom
simple-frame.right
simple-frame.top
