mzandrew/idlab-scrod/mechanical-designs/board-stack/fDIRC/images/fDIRC-assembly.back.JPG

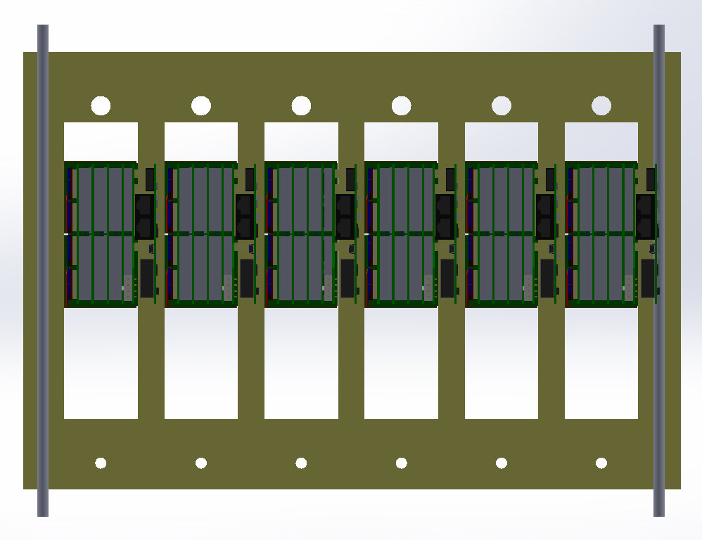
mechanical-designs/board-stack/fDIRC/images/fDIRC-assembly.back.JPG
