mzandrew/idlab-scrod/mechanical-designs/board-stack/fDIRC/images/fDIRC-assembly.JPG

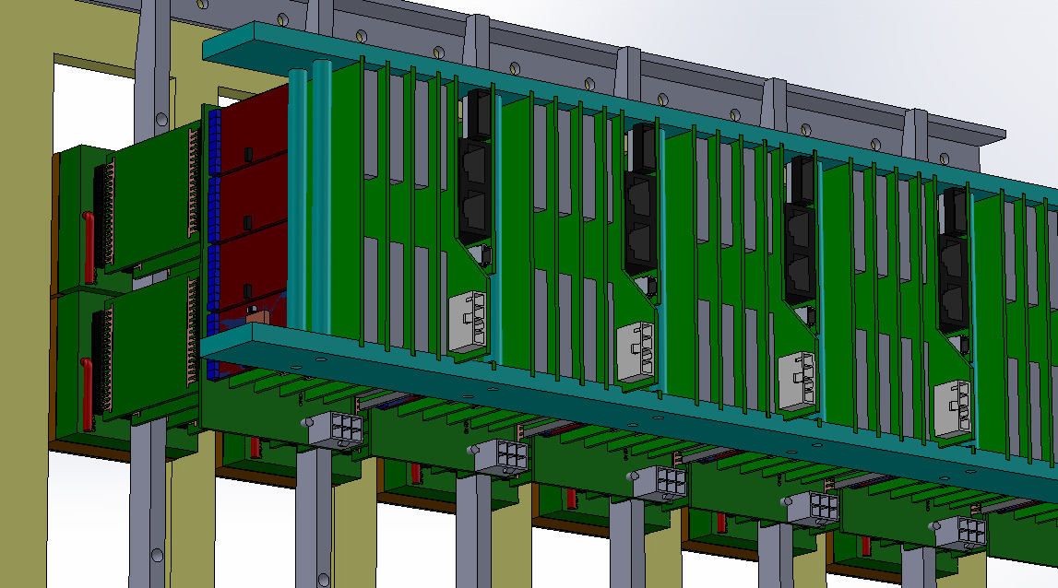
mechanical-designs/board-stack/fDIRC/images/fDIRC-assembly.JPG
