mzandrew/idlab-scrod/mechanical-designs/board-stack/fDIRC/images/fDIRC-assembly.top.JPG

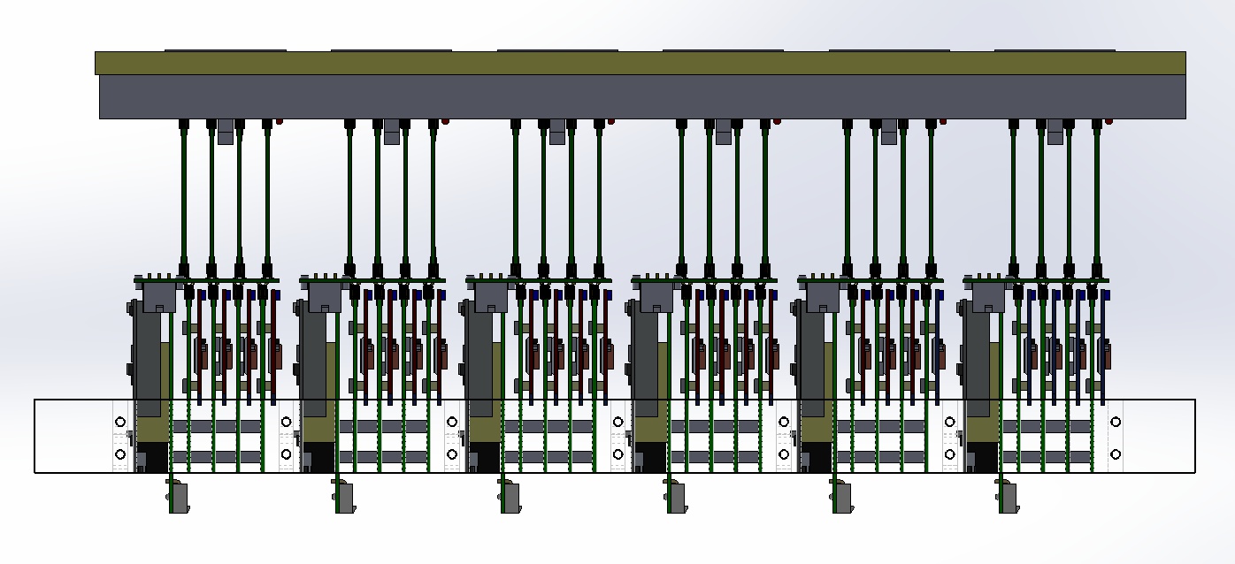
mechanical-designs/board-stack/fDIRC/images/fDIRC-assembly.top.JPG
