mzandrew/idlab-scrod/mechanical-designs/board-stack/fDIRC/images/fDIRC-assembly.top.with-power-cables.png

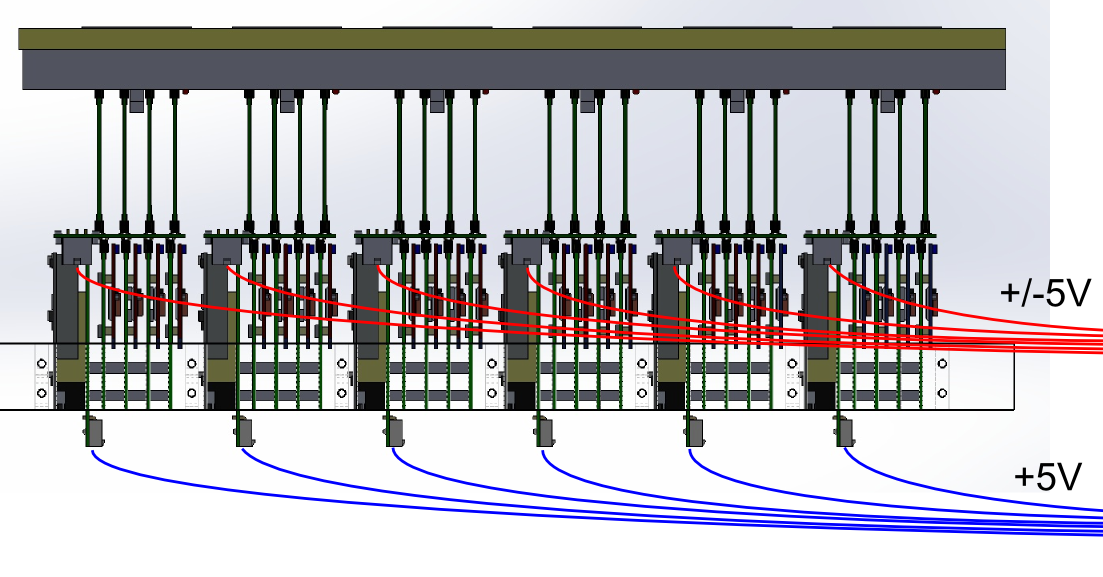
mechanical-designs/board-stack/fDIRC/images/fDIRC-assembly.top.with-power-cables.png
