mzandrew/idlab-scrod/mechanical-designs/board-stack/iTOP/export/laser-jig-pieces-required-for-Hawaii-testing.png

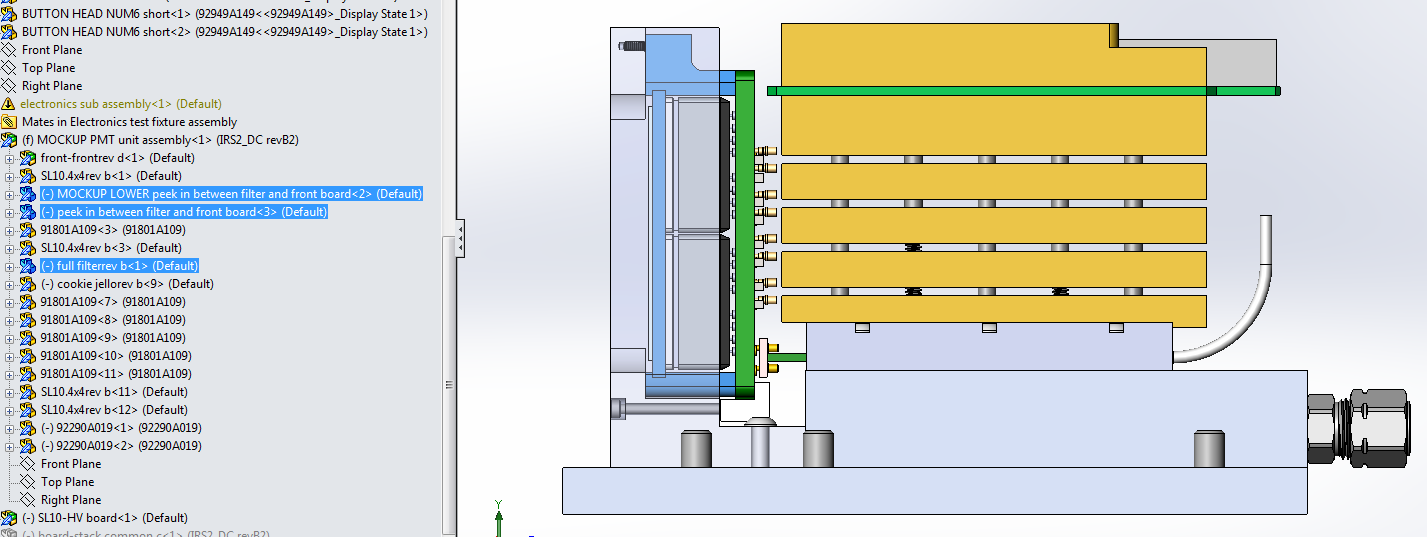
mechanical-designs/board-stack/iTOP/export/laser-jig-pieces-required-for-Hawaii-testing.png
