mzandrew/idlab-scrod/wiki/images/2011-09-26.iTOP-cosmic-ray-beam-test-electronics-module-fully-populated.cropped-and-scaled.jpeg

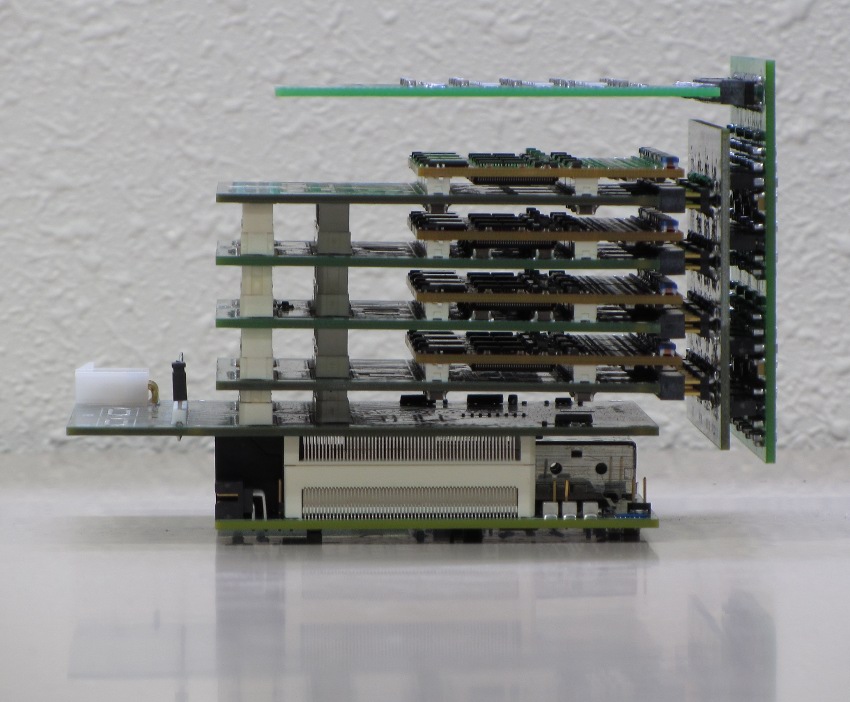
wiki/images/2011-09-26.iTOP-cosmic-ray-beam-test-electronics-module-fully-populated.cropped-and-scaled.jpeg
