mzandrew/idlab-scrod/mechanical-designs/board-stack/iTOP/export/carrier.revE.PDF

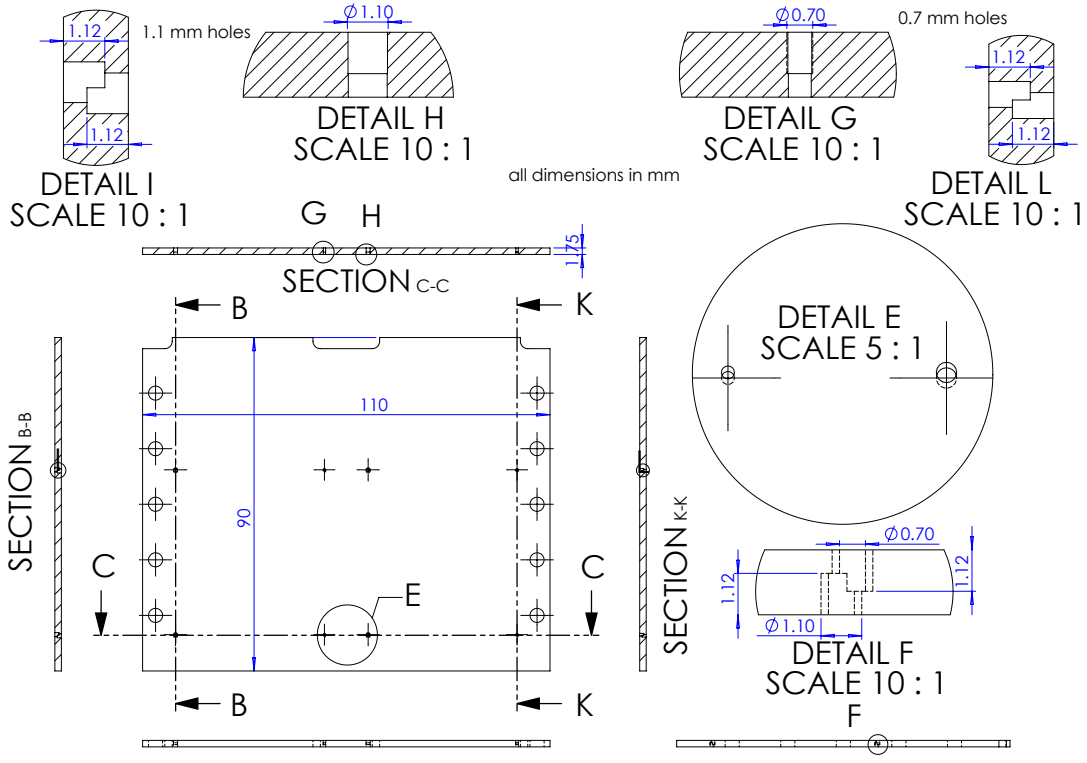
[picture p184: page 1]
SECTION B-B; SECTION C-C; DETAIL E SCALE 5 : 1; DETAIL F SCALE 10 : 1; DETAIL G SCALE 10 : 1; 0.7 mm holes 1.10; DETAIL H SCALE 10 : 1; 1.1 mm holes; DETAIL I SCALE 10 : 1; SECTION K-K; DETAIL L SCALE 10 : 1

all dimensions in mm
