mzandrew/idlab-scrod/SCROD-boardstack/STURM2-ATF2/hardware/STURM2_eval.revB/STURM2_eval.revB.pdf

D

6 | 5 | 4 | 3 | 2 | 1

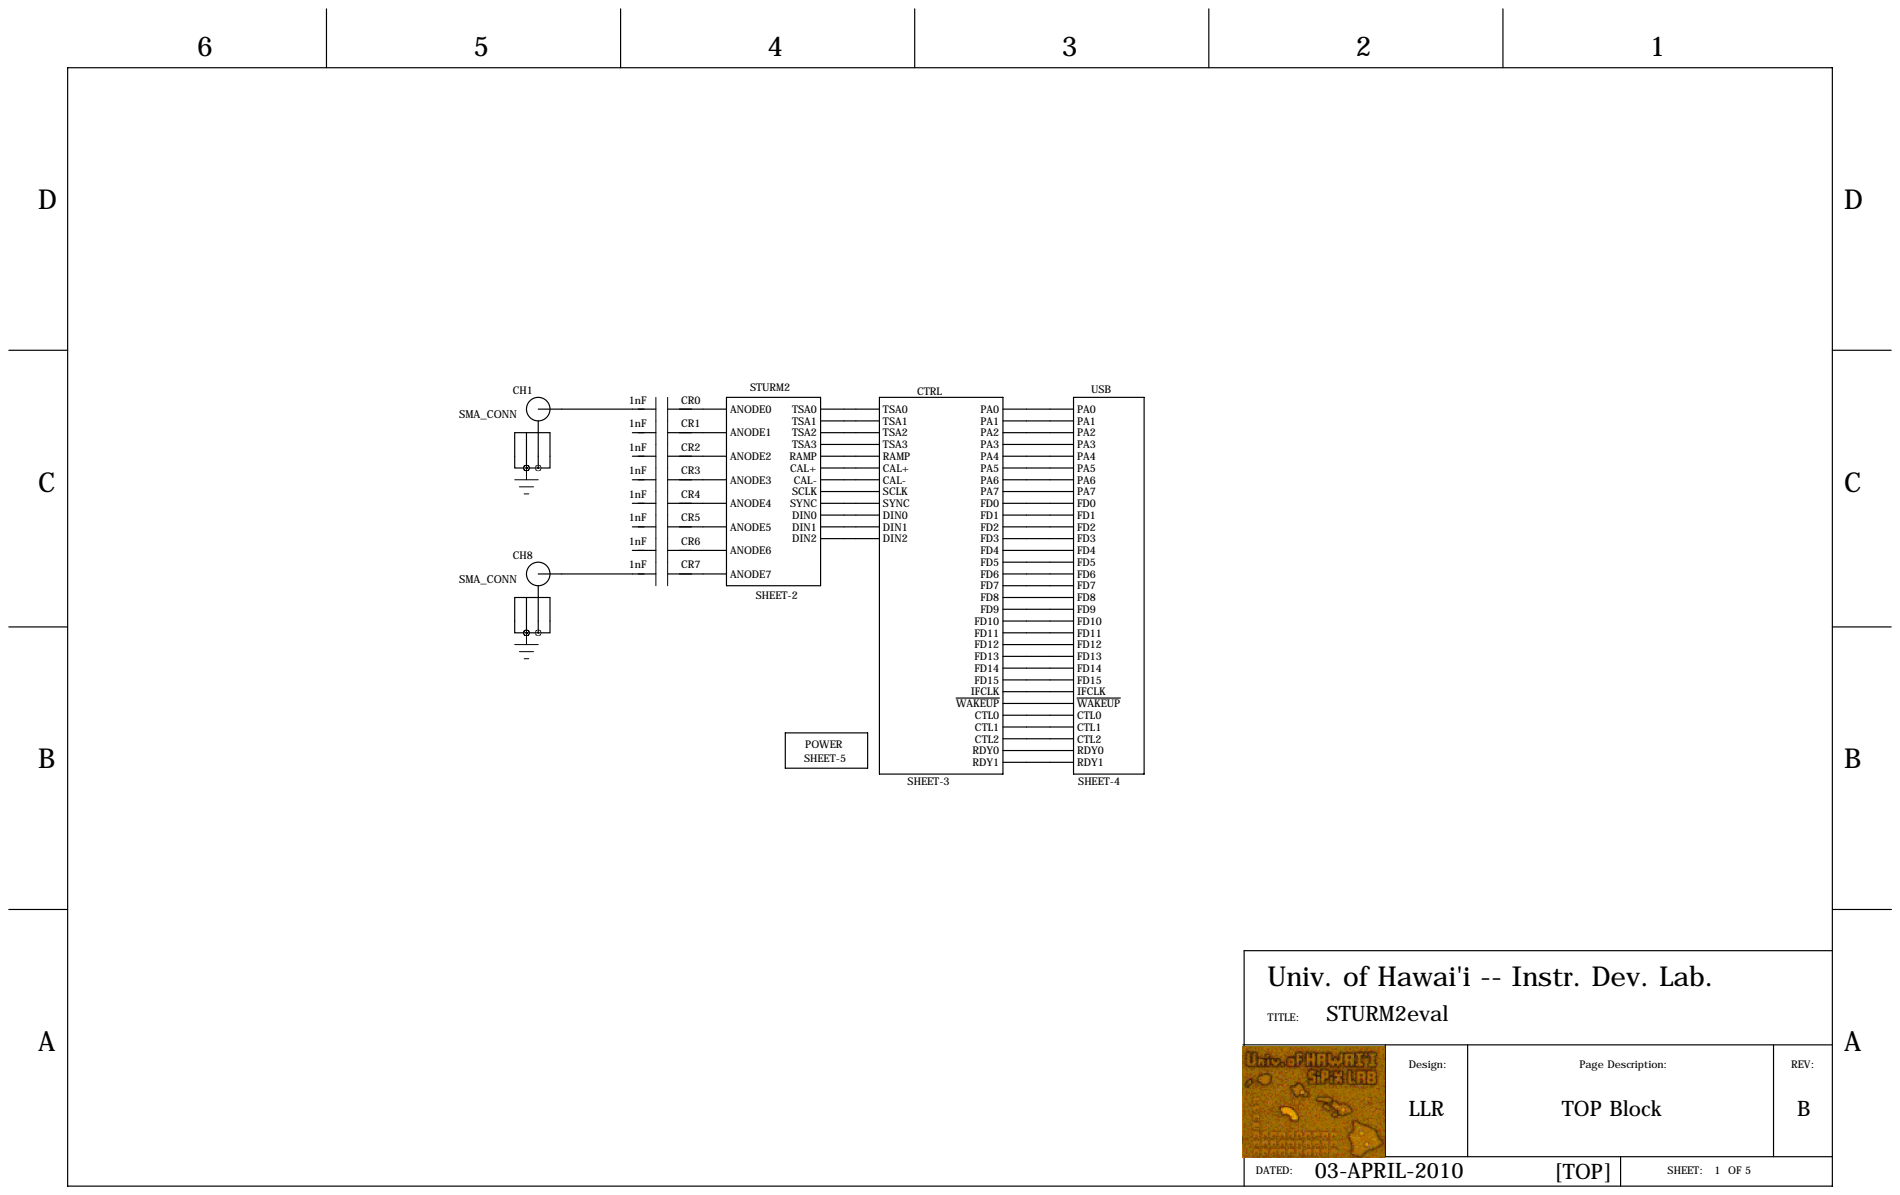
[picture p185: page 1]
TITLE:; STURM2eval; PA0 PA1 PA2 PA3 PA4 PA5 PA6 PA7 FD0 FD1 FD2 FD3 FD4 FD5 FD6 FD7 FD8 FD9 FD10 FD11 FD12 FD13 FD14 FD15 IFCLK WAKEUP CTL0 CTL1 CTL2 RDY0 RDY1; USB; SHEET-4; TSA0 TSA1 TSA2 TSA3; RAMP CAL+ CAL- SCLK SYNC DIN0 DIN1 DIN2; CTRL; SHEET-3; POWER; SHEET-5; TSA0 TSA1; DIN2; TSA2 TSA3; CAL-; CAL+; RAMP; DIN0; SCLK SYNC; DIN1; ANODE0; ANODE1; ANODE2; ANODE3; ANODE4; ANODE5; ANODE6; ANODE7; STURM2; SHEET-2; SMA_CONN

Univ. of Hawai'i -- Instr. Dev. Lab.

Design: LLR | Page Description: TOP Block | REV: B

03-APRIL-2010 [TOP] DATED: | SHEET: 1 OF 5

D

D

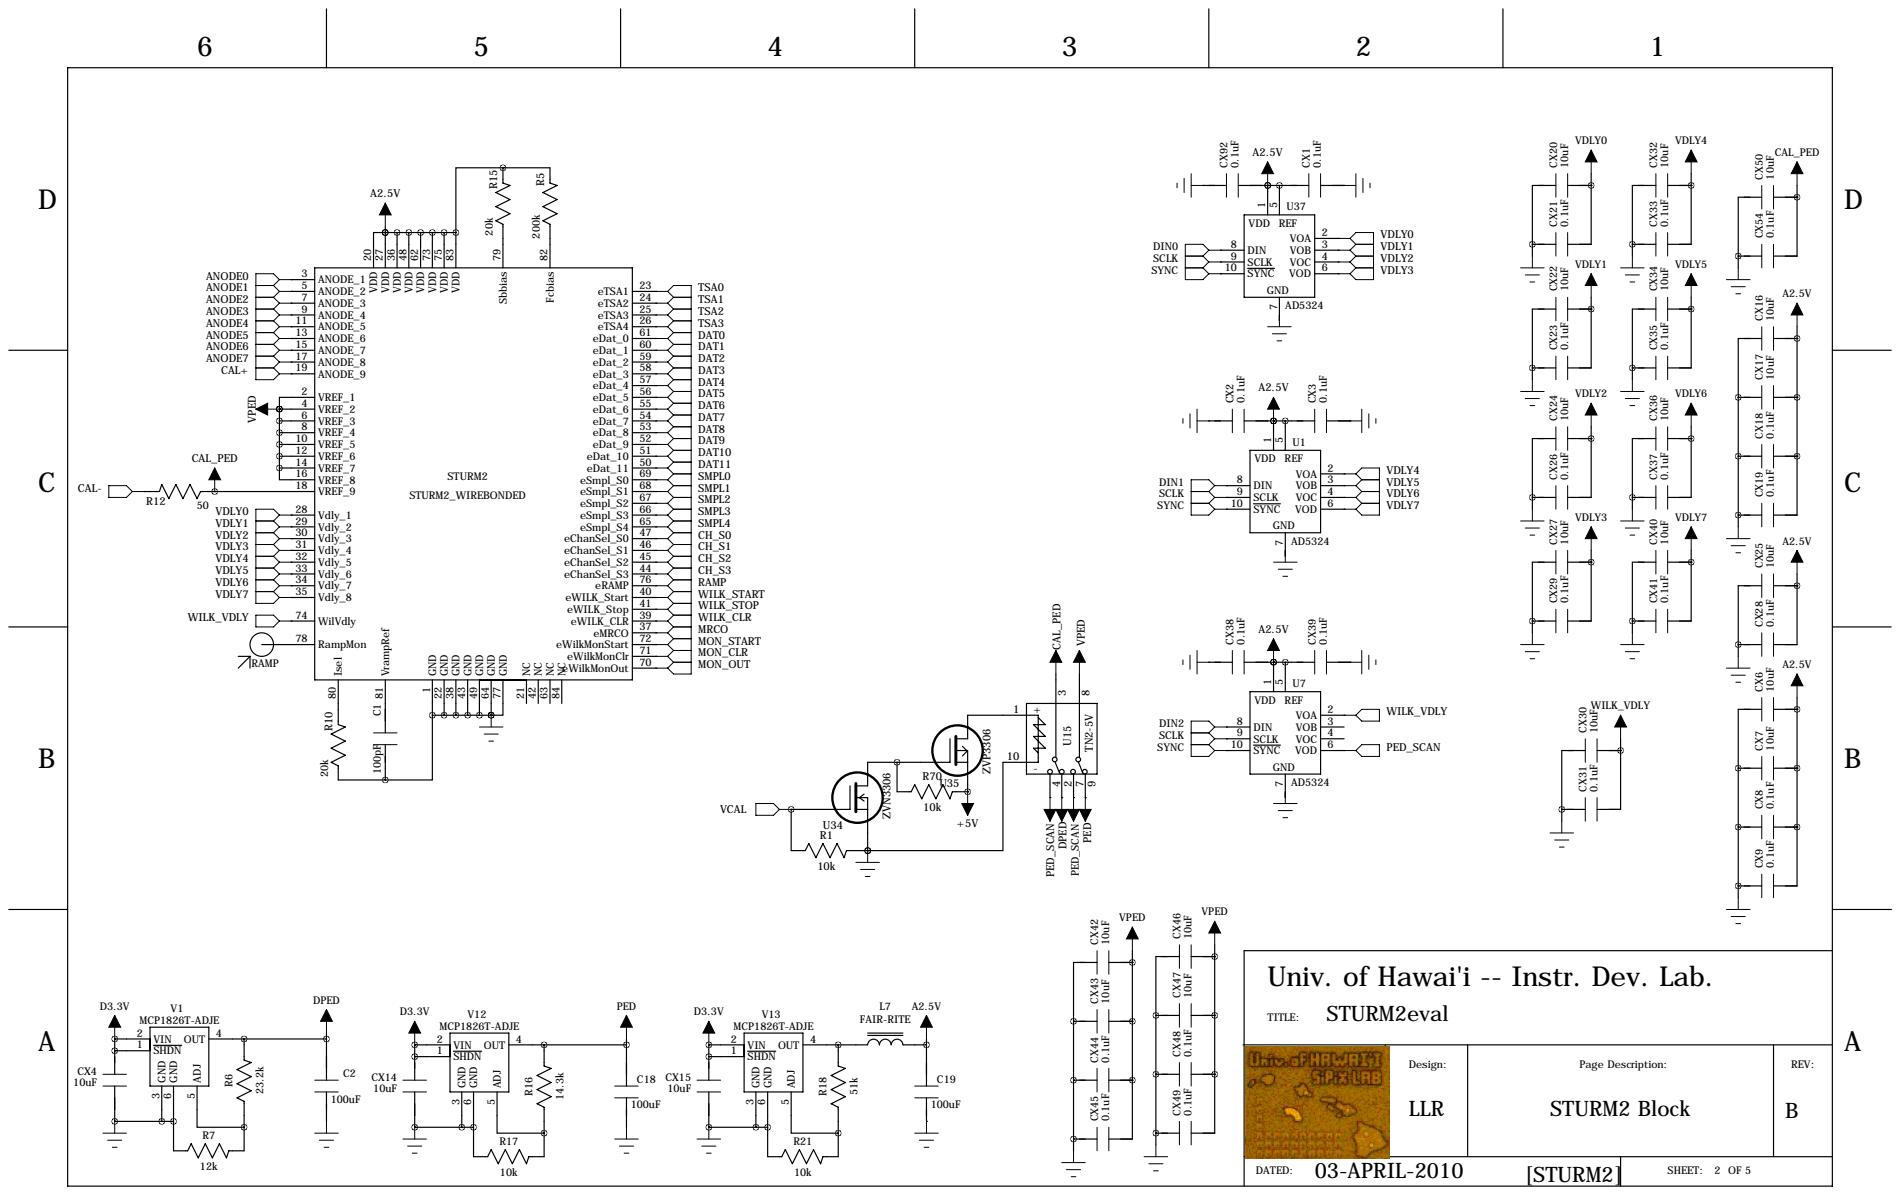
[picture p186: page 2]

Univ. of Hawai'i -- Instr. Dev. Lab.

$$$5188 | Design: LLR | Page Description: STURM2 Block | REV: B

03-APRIL-2010 [STURM2]

# BACD

6

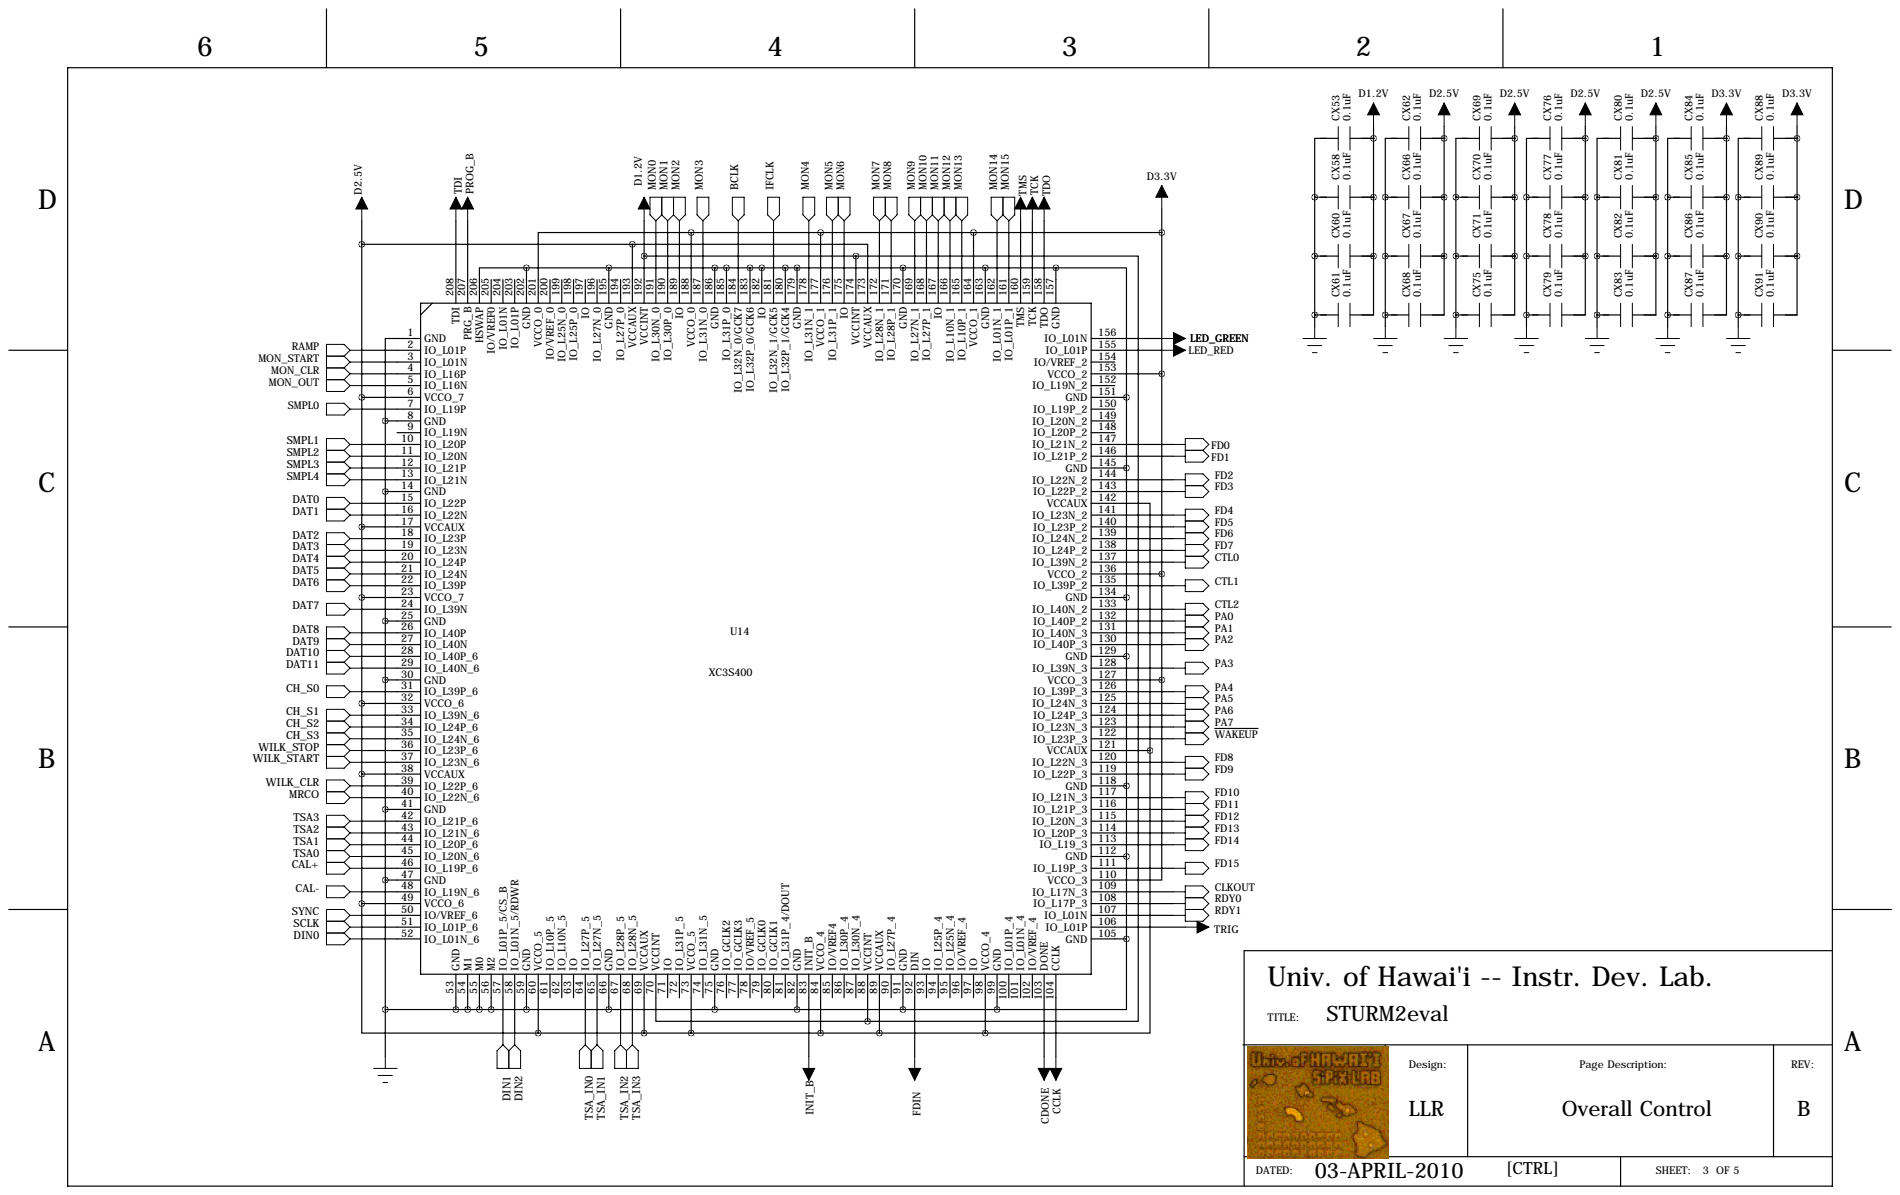
[picture p187: page 3]
DBA; TITLE:; STURM2eval; GND; VCCO_7; GND 15; VCCAUX 18; VCCO_7 24; GND 26; GND 31; VCCO_6 33; VCCAUX 39; GND 42; GND 48; VCCO_6 50; IO/VREF_6 51; 154 IO/VREF_2; 153 VCCO_2; 151 GND; 145 GND; 142 VCCAUX; 136 VCCO_2; 134 GND; 129 GND; 127 VCCO_3; 121 VCCAUX; 118 GND; 112 GND; 110 VCCO_3; 105 GND ¹⁵⁷ GND ¹⁵⁸ TDO; 159 TCK; 160 TMS 161 IO_L01P_1; 163 GND 164 VCCO_1; 170 GND 171 IO_L28P_1; 173 VCCAUX 174 VCCINT; 176 IO_L31P_1 177 VCCO_1; 178 IO_L31N_1 179 GND; 180 IO_L32P_1/GCK4 181 IO_L32N_1/GCK5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

Univ. of Hawai'i -- Instr. Dev. Lab.

Design: LLR | Page Description: Overall Control | REV: B

03-APRIL-2010 [CTRL]

# BACD

6

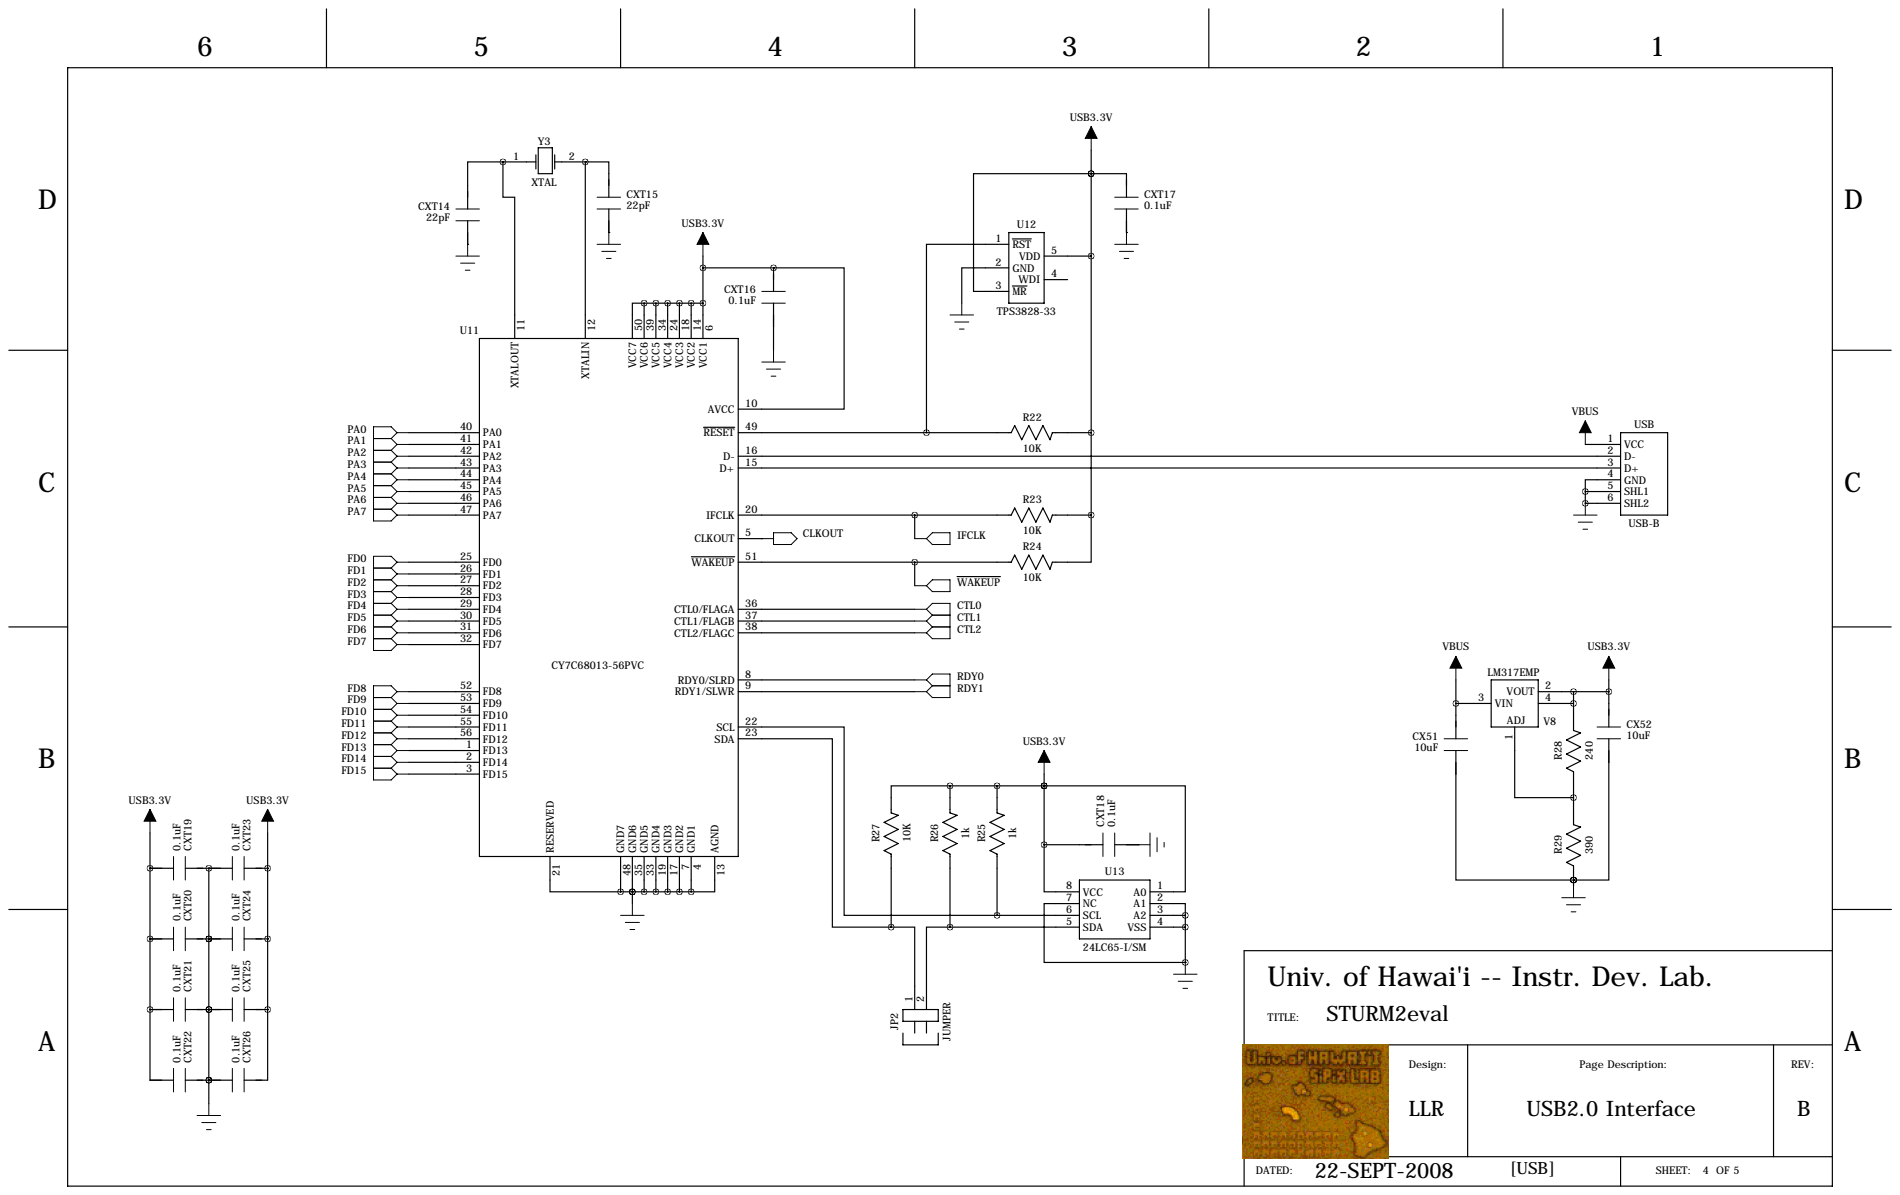
[picture p188: page 4]

Univ. of Hawai'i -- Instr. Dev. Lab.

Design: LLR | Page Description: USB2.0 Interface | REV: B

22-SEPT-2008 [USB]

D

D

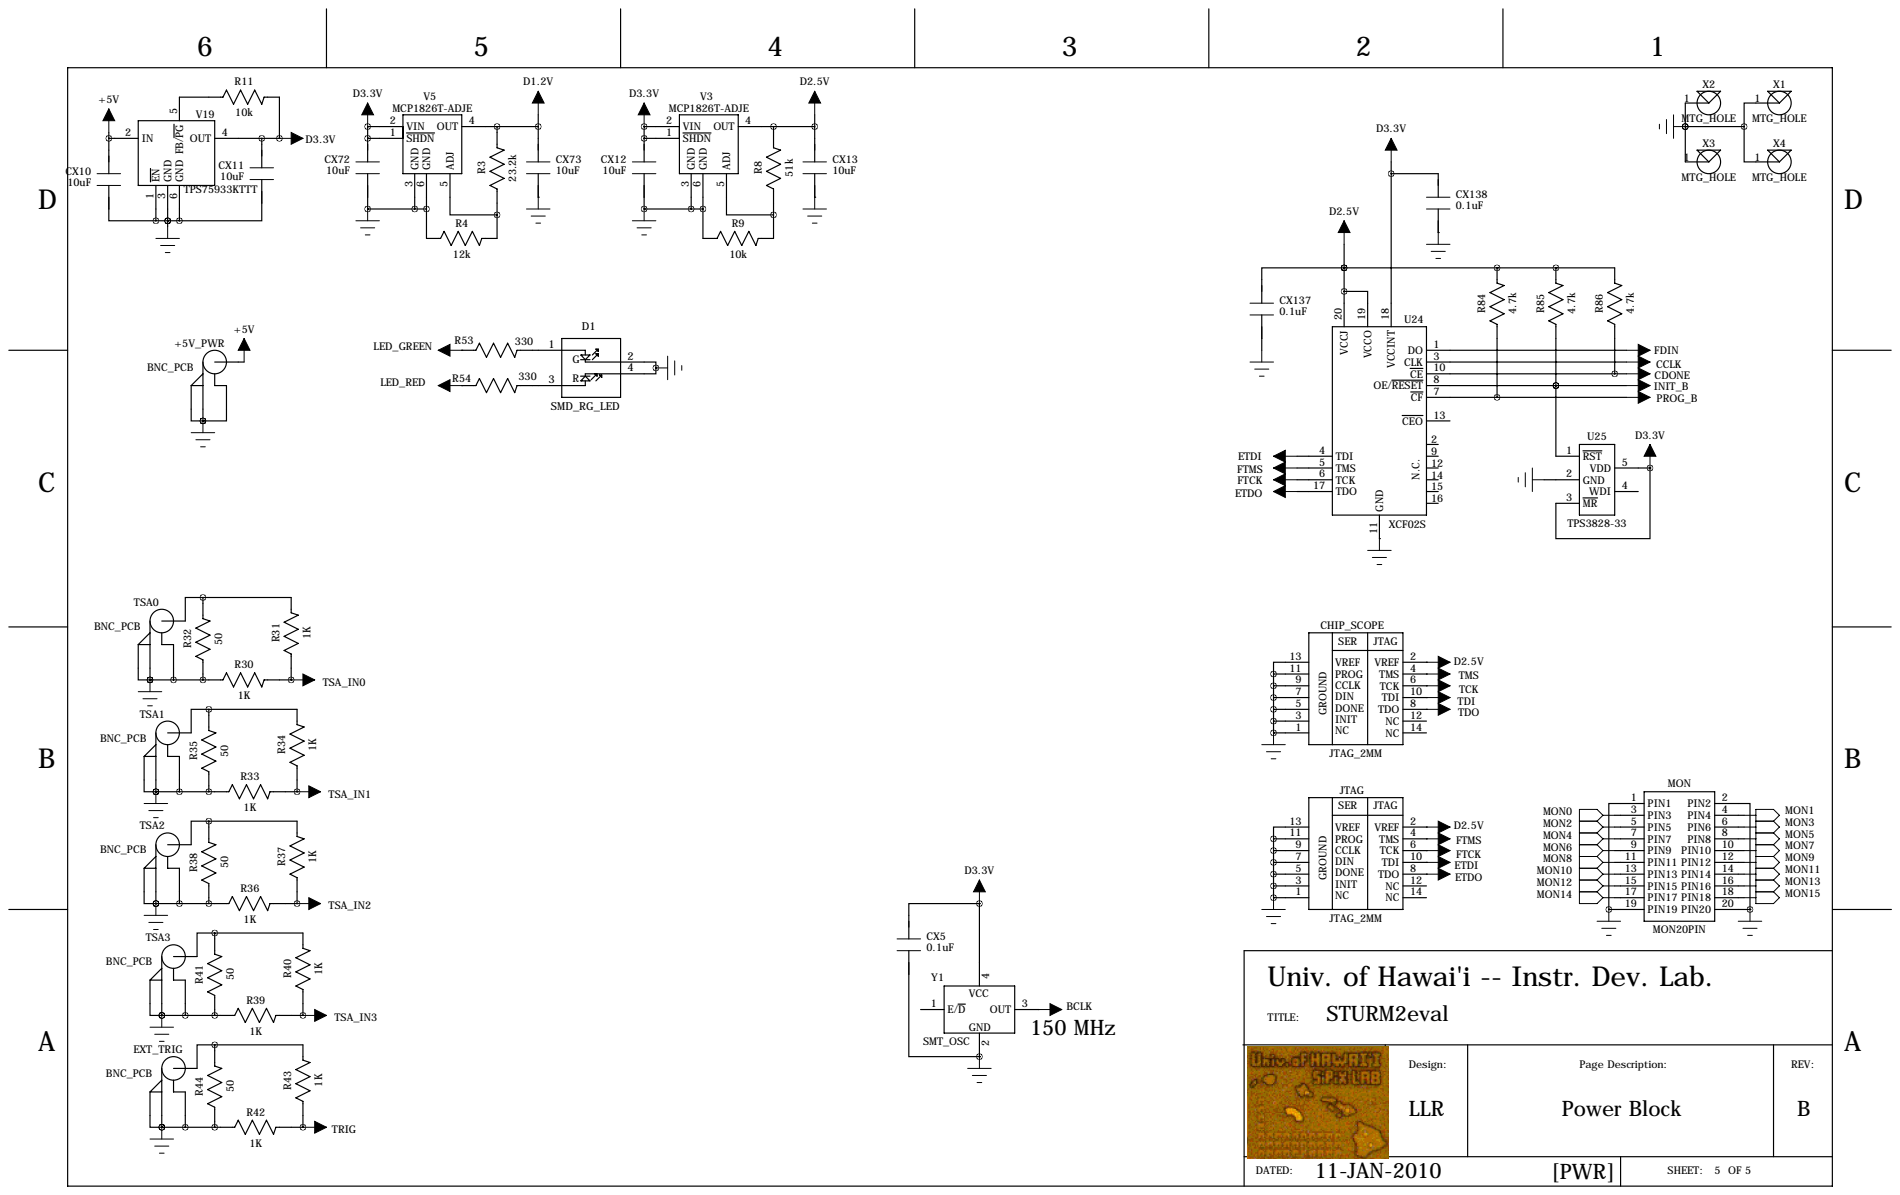
[picture p189: page 5]

SER | JTAG

Univ. of Hawai'i -- Instr. Dev. Lab.
