mzandrew/idlab-scrod/SCROD-boardstack/KLM/TX9UMB-4/src/KLM_SCROD_baseline/doc/SCROD.revA3.schematic.pdf

E

D

C

A

B

## Instrumentation Development Lab

## High Energy Physics Group

## University of Hawai'i at Manoa

## sheet #:

## title:

## date last modified:

## sheet description:

## PCB design:

## IDLAB design #:

## revision:

## circuit design:

## institution:

E

D

C

A

B

6 | 5 | 4 | 3 | 2 | 1

## IDL_13_037 LJR, MZA, GSV, KAN LJR, MZA

## SCROD

A3

2014-02-12

## block diagram

## Assembly instructions:

## install 2mm 2 pin jumper header 156_DIS and 250_DIS

## notes updated 2012-05-16

## install GND test points

## added size/package notes to schematic

## notes updated 2012-10-05 added notes about bank voltages and N18/M18/L10/K10/J2/M10

## sch: changed thermal wall holes to be the skinny type

2013-10-10

2013-10-09

## pcb: changed 2 pin molex connector to use bigger holes

2013-10-25:

## forgot pullup on shdn net for regulators holes for power connector too small changed note on what switch #4 does

2013-10-31:

be careful wiring up the 2 pin power connector; pin 1 on the schematic doesn't correspond to pin 1 on the connector

2014-01-09

## FPGA is XC6SLX150T-3FGG676I (RoHS; speed grade 3; industrial temp)

2014-02-12:

noticed that DIP sw for disconnecting cypress eeprom should probably be on other side of pull-up resistor

TX_FAULT0
TX_DIS0
MOD2_0
MOD1_0
MOD0_0
LOS_0
TX_FAULT1
TX_DIS1
MOD2_1
MOD1_1
MOD0_1
LOS_1

FPGA_FIBER_OPTICS SHEET-3

TX_FAULT0
TX_DIS0
MOD2_0
MOD1_0
MOD0_0
LOS_0
TX_FAULT1
TX_DIS1
MOD2_1
MOD1_1
MOD0_1
LOS_1

TD_MF
TMS
TCK
FDIN
CCLK
PROGRAM_B
DONE
INIT_B
TD_FP

FPGA_BANKS_0_5

SHEET-2

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
FD10
FD11
FD12
FD13
FD14
FD15
IFCLK
WAKEUP
CTL0
CTL1
CTL2
RDY0
RDY1
UT

CYPRESS_FX2LP_USB

SHEET-7

BOARD_TO_BOARD_INTERCONNECTS SHEET-5

TD_MF
TMS
TCK
FDIN
CCLK
PROGRAM_B
DONE
INIT_B
TD_FP

CAT1+
CAT1-
CAT2+
CAT2-
CAT3+
CAT3-
CAT4+
CAT4-

JTAG,CLOCKS,LEDS,PROM

SHEET-6

E

E

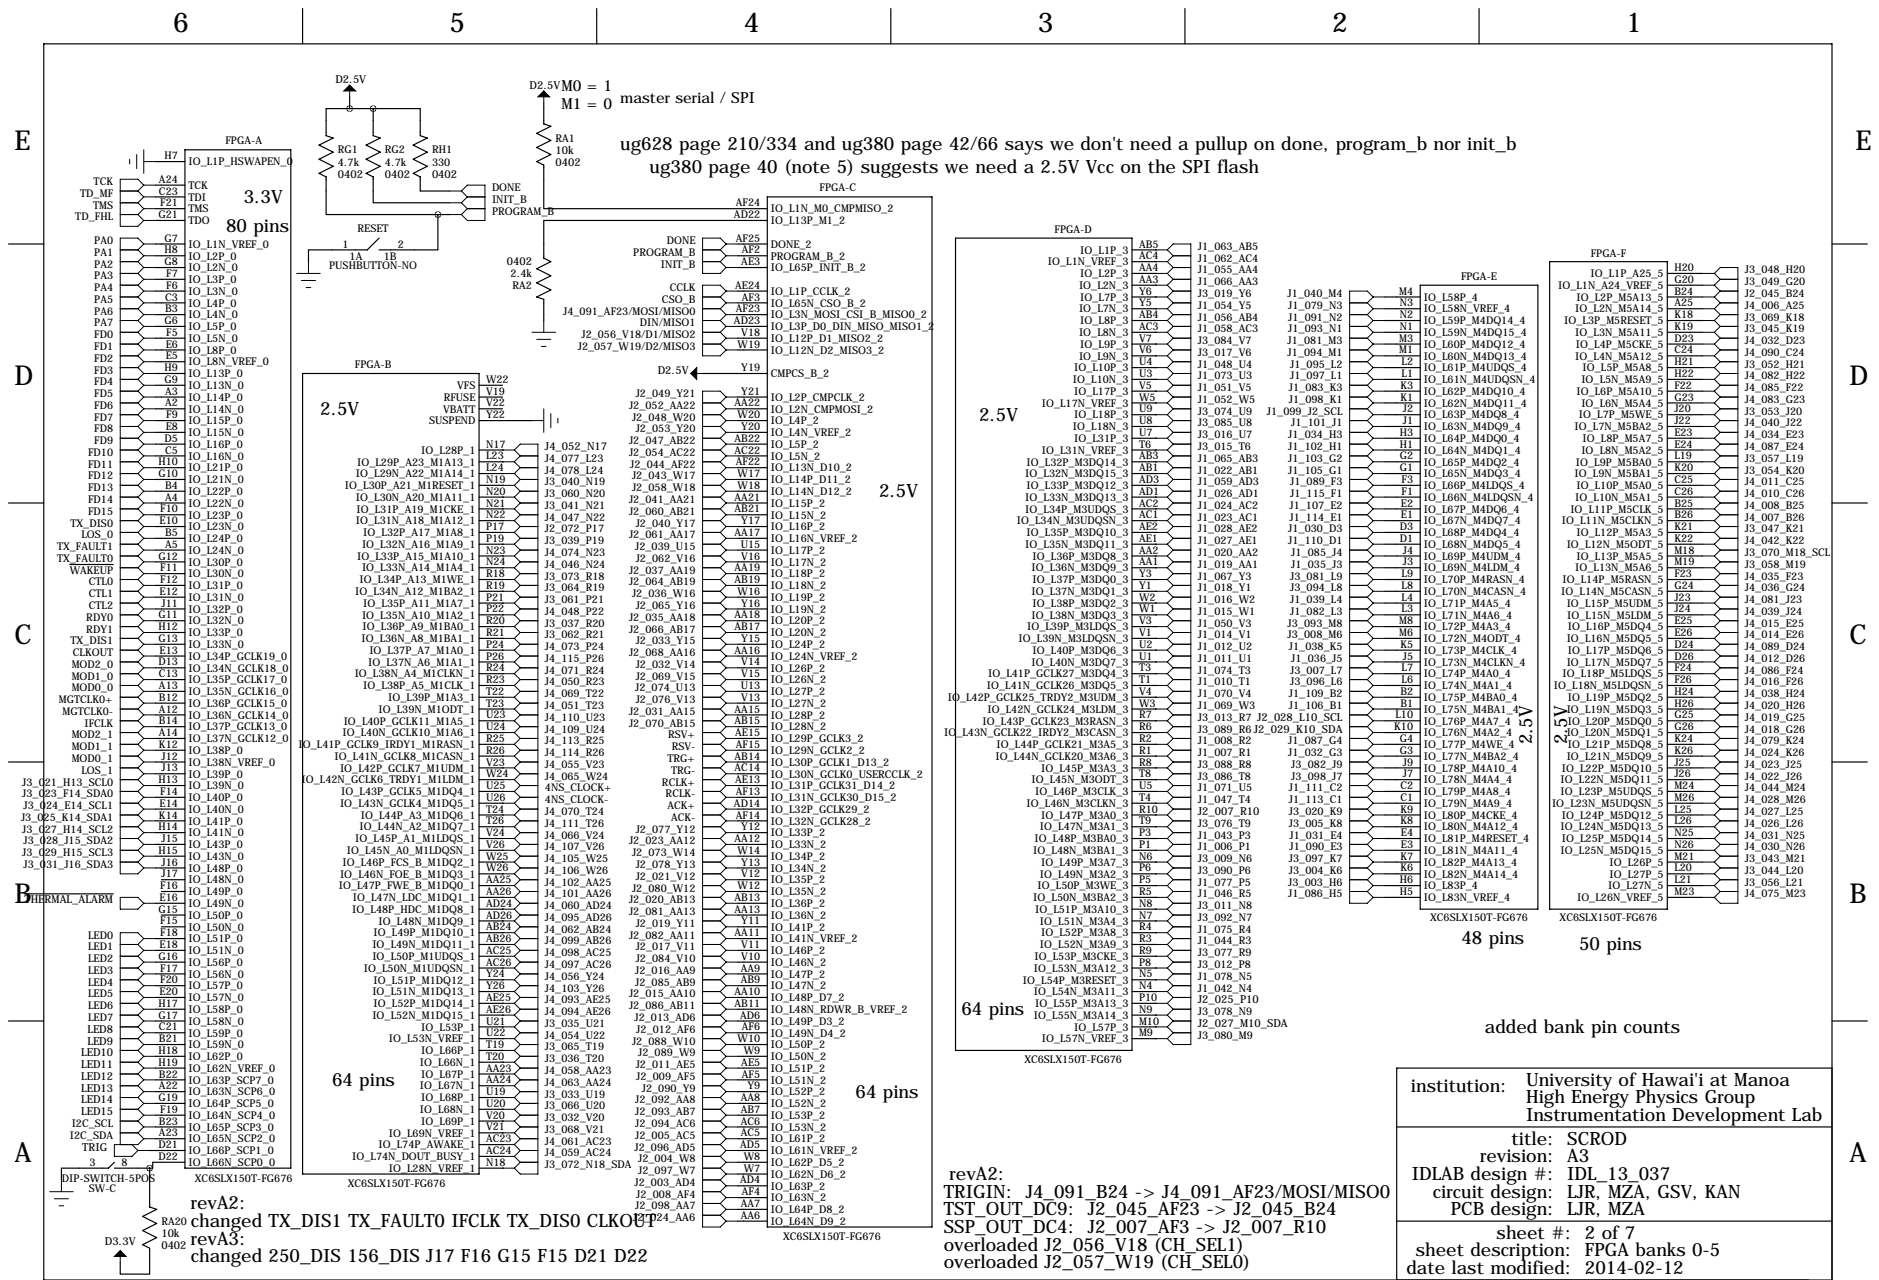
[picture p190: page 2]

ug628 page 210/334 and ug380 page 42/66 says we don't need a pullup on done, program_b nor init_b
ug380 page 40 (note 5) suggests we need a 2.5V Vcc on the SPI flash

added bank pin counts

University of Hawai'i at Manoa
High Energy Physics Group
Instrumentation Development Lab
title:
revision:

E

E

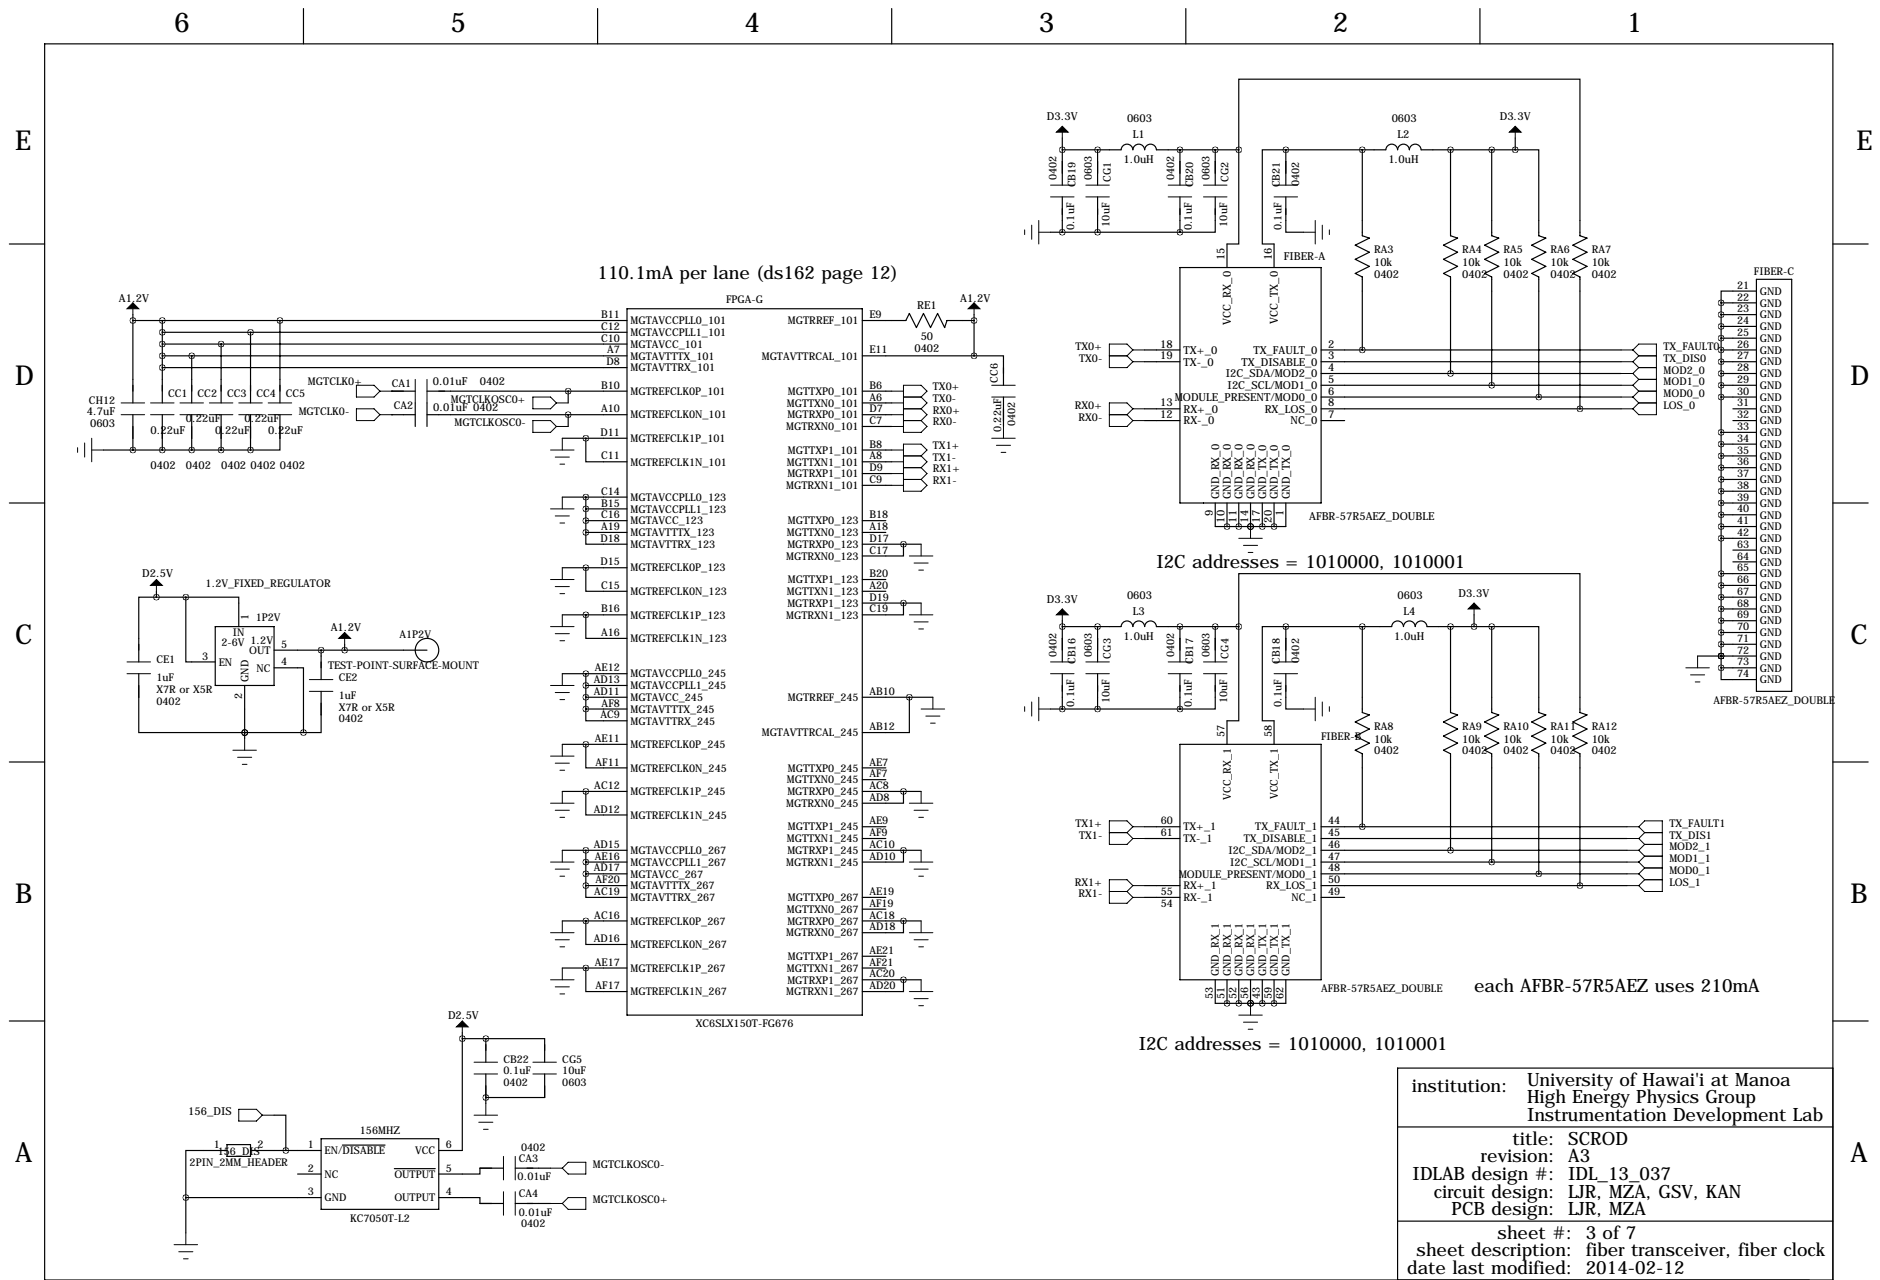
[picture p191: page 3]

University of Hawai'i at Manoa
High Energy Physics Group
Instrumentation Development Lab
title:
revision:

fiber transceiver, fiber clock

E

E

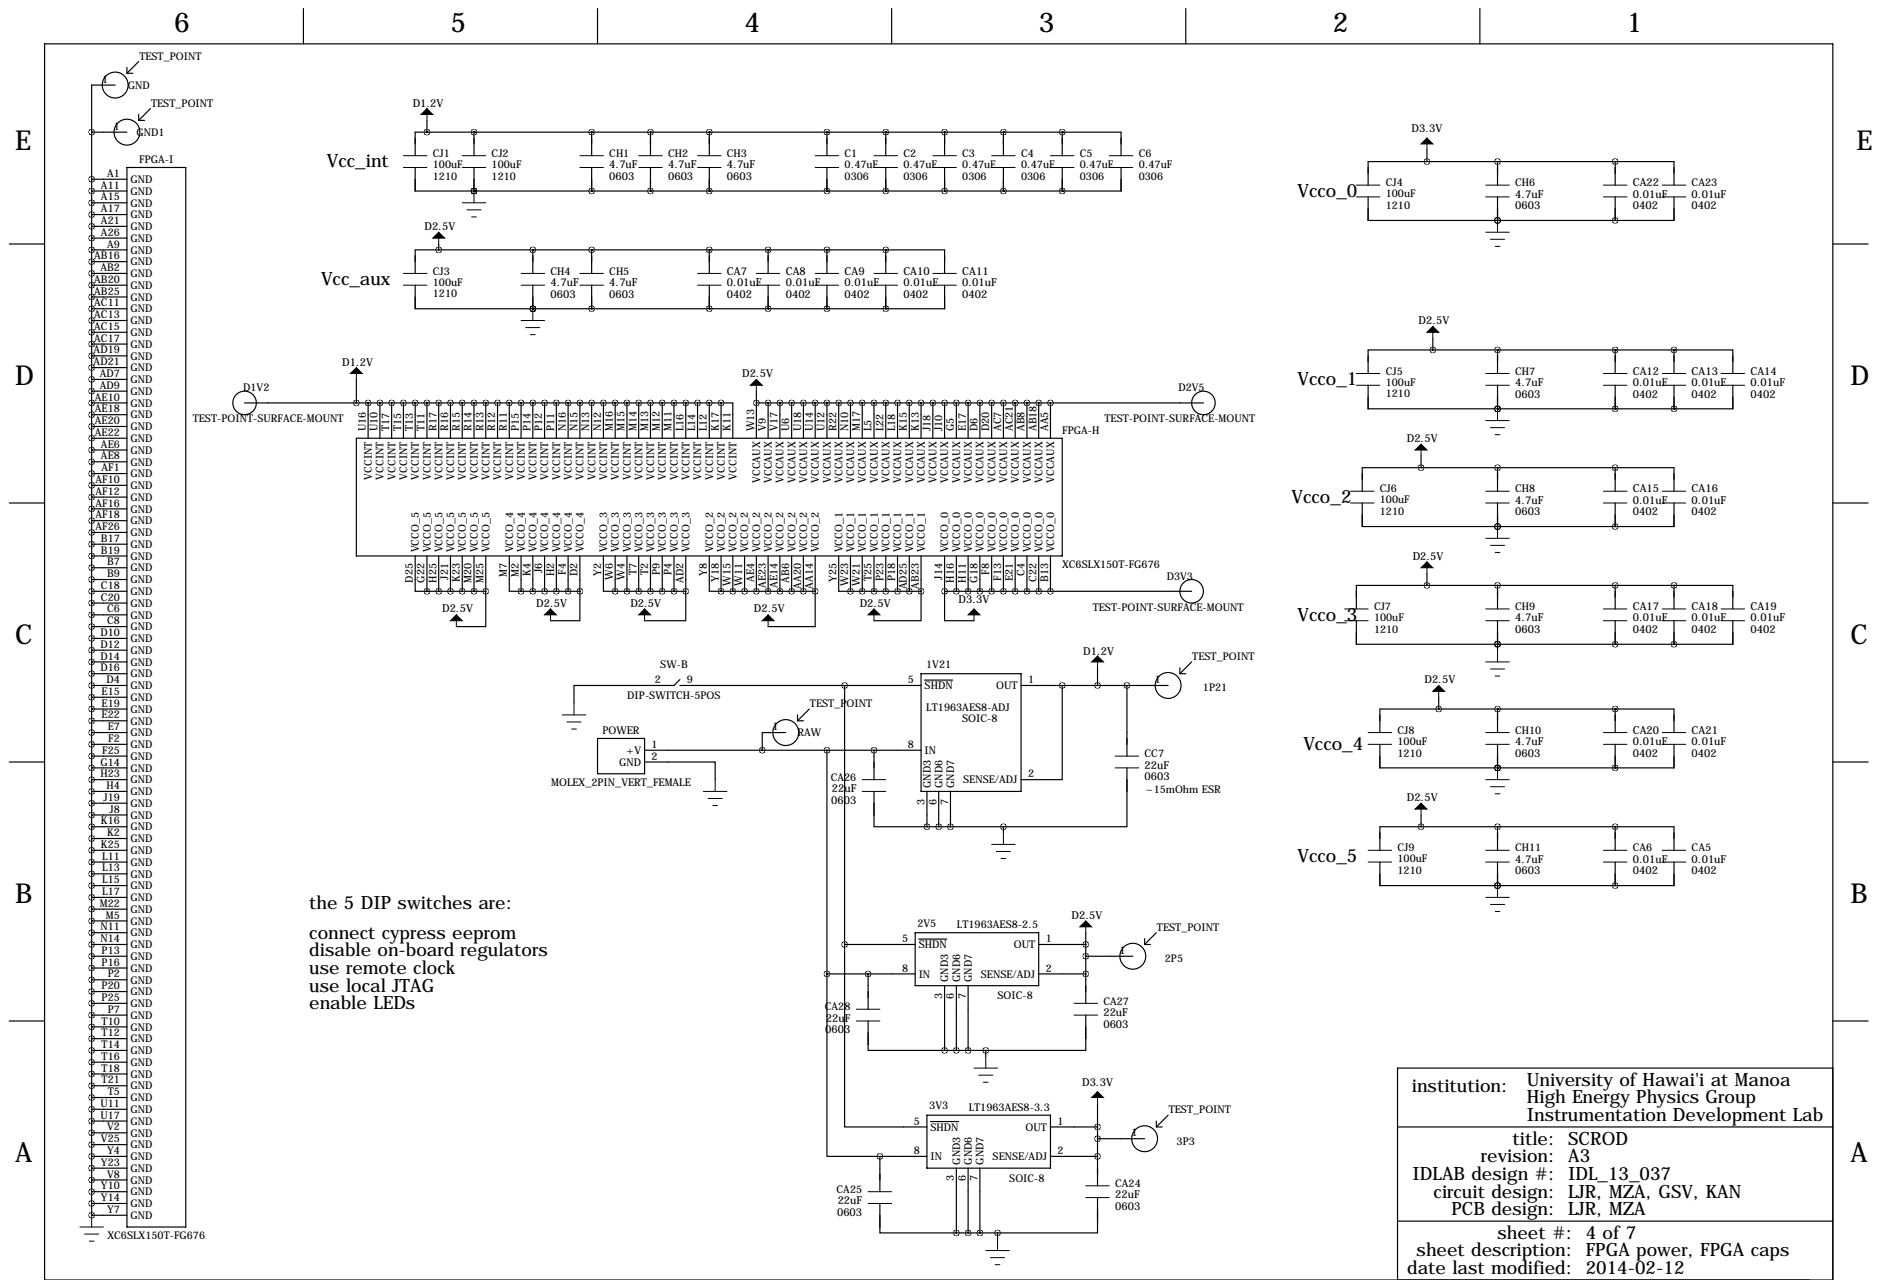
[picture p192: page 4]

TEST-POINT-SURFACE-MOUNT

the 5 DIP switches are:
connect cypress eeprom
disable on-board regulators
use remote clock
use local JTAG
enable LEDs

University of Hawai'i at Manoa
High Energy Physics Group
Instrumentation Development Lab
title:
revision:

FPGA power, FPGA caps

E

E

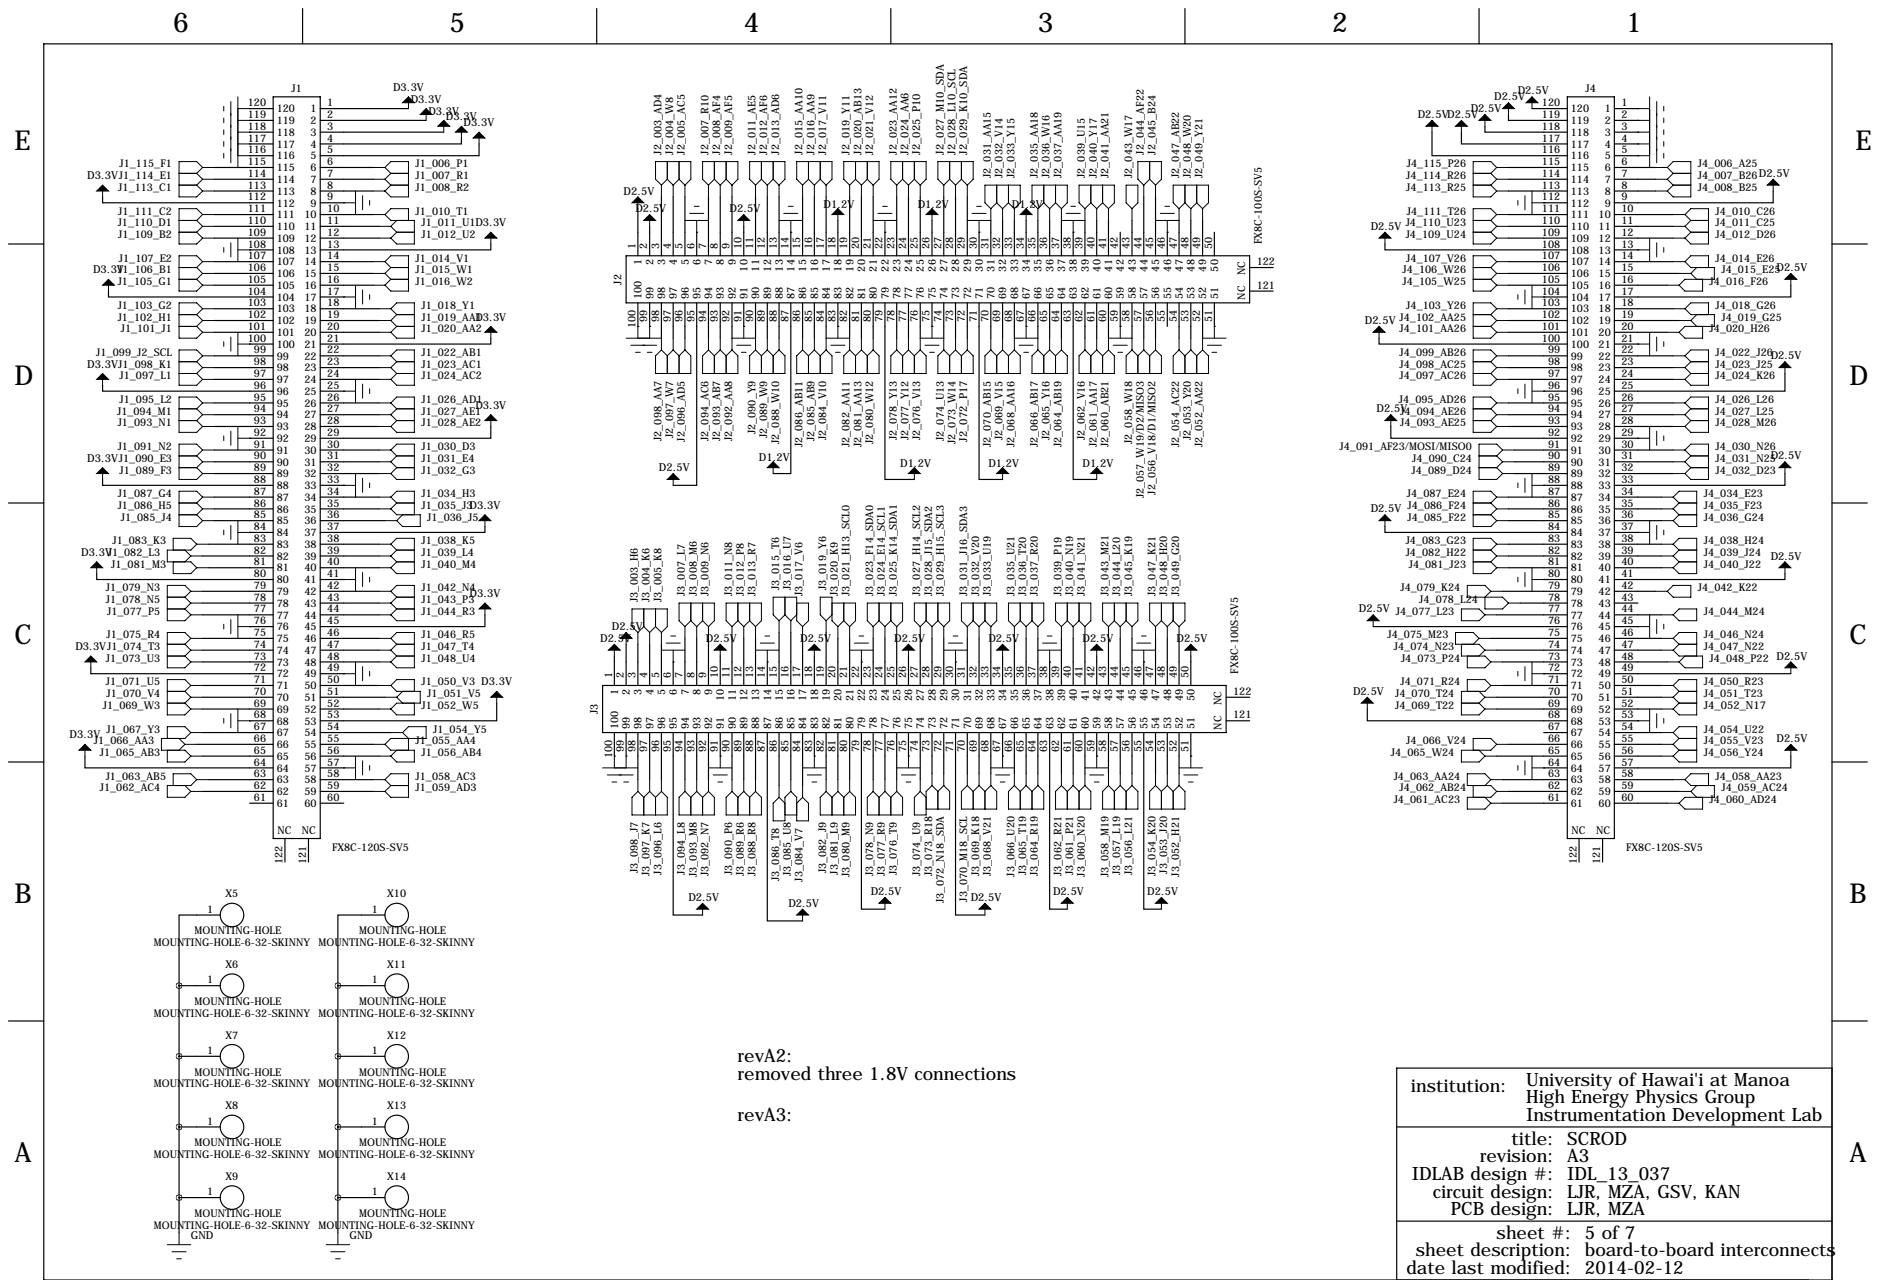
[picture p193: page 5]
institution:; SCROD A3; revA3:; MOUNTING-HOLE; J2_056_V18/D1/MISO2; J2_057_W19/D2/MISO3; J1_099_J2_SCL J1_098_K1 J1_097_L1; J4_091_AF23/MOSI/MISO0 J4_090_C24; J3_021_H13_SCL0; J3_023_F14_SDA0; J3_024_E14_SCL1; J3_025_K14_SDA1; J3_027_H14_SCL2; J3_028_J15_SDA2; J3_029_H15_SCL3; J3_031_J16_SDA3; J3_072_N18_SDA; J3_070_M18_SCL; J2_027_M10_SDA; J2_028_L10_SCL; J2_029_K10_SDA; GND

MOUNTING-HOLE-6-32-SKINNY

revA2:
removed three 1.8V connections

University of Hawai'i at Manoa
High Energy Physics Group
Instrumentation Development Lab
title:
revision:

board-to-board interconnects

E

E

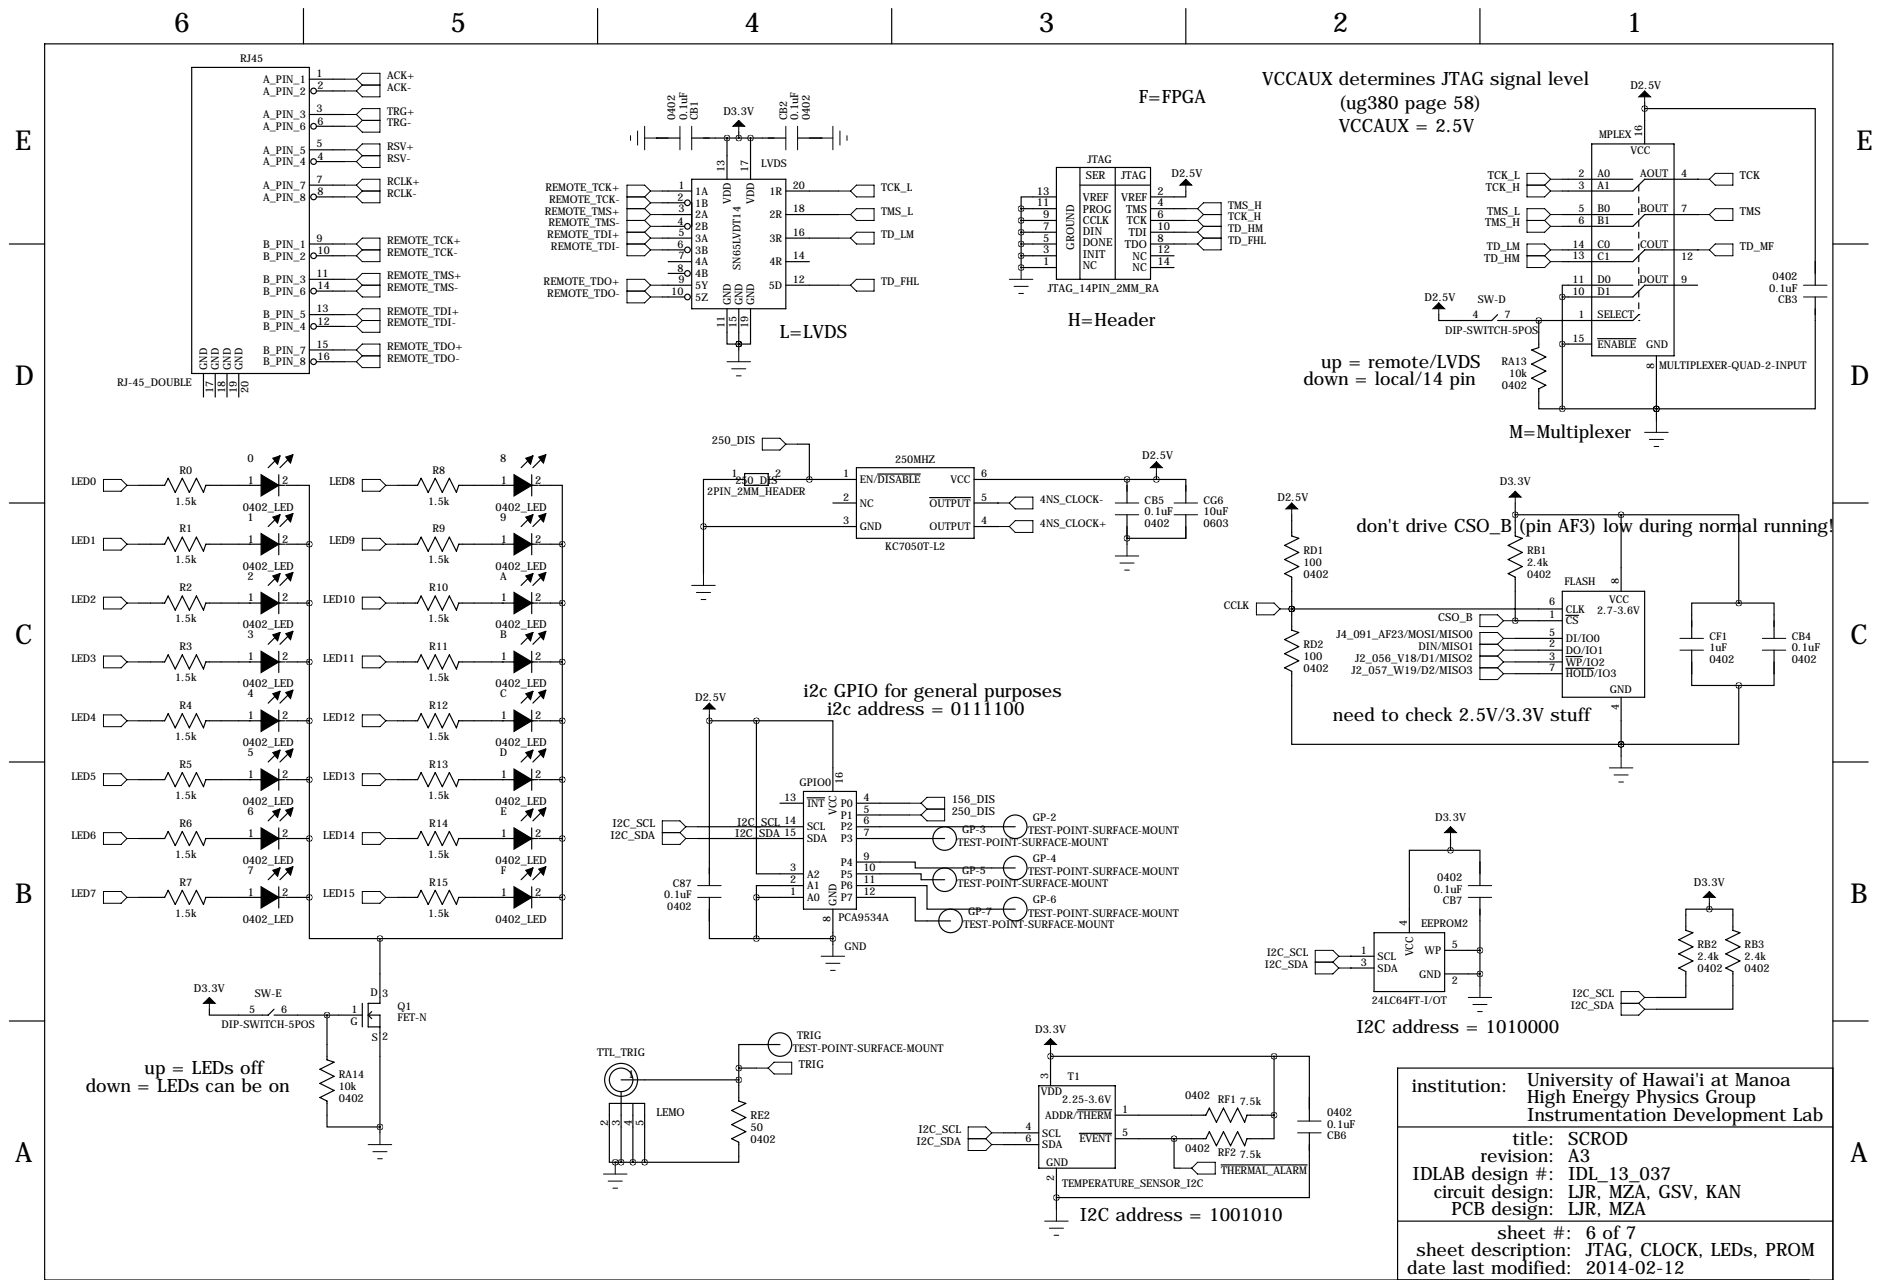
[picture p194: page 6]

VCCAUX determines JTAG signal level

i2c GPIO for general purposes
i2c address = 0111100

need to check 2.5V/3.3V stuff

TEST-POINT-SURFACE-MOUNT

TRIG

University of Hawai'i at Manoa
High Energy Physics Group
Instrumentation Development Lab
title:
revision:

down = LEDs can be on

JTAG, CLOCK, LEDs, PROM

E

E

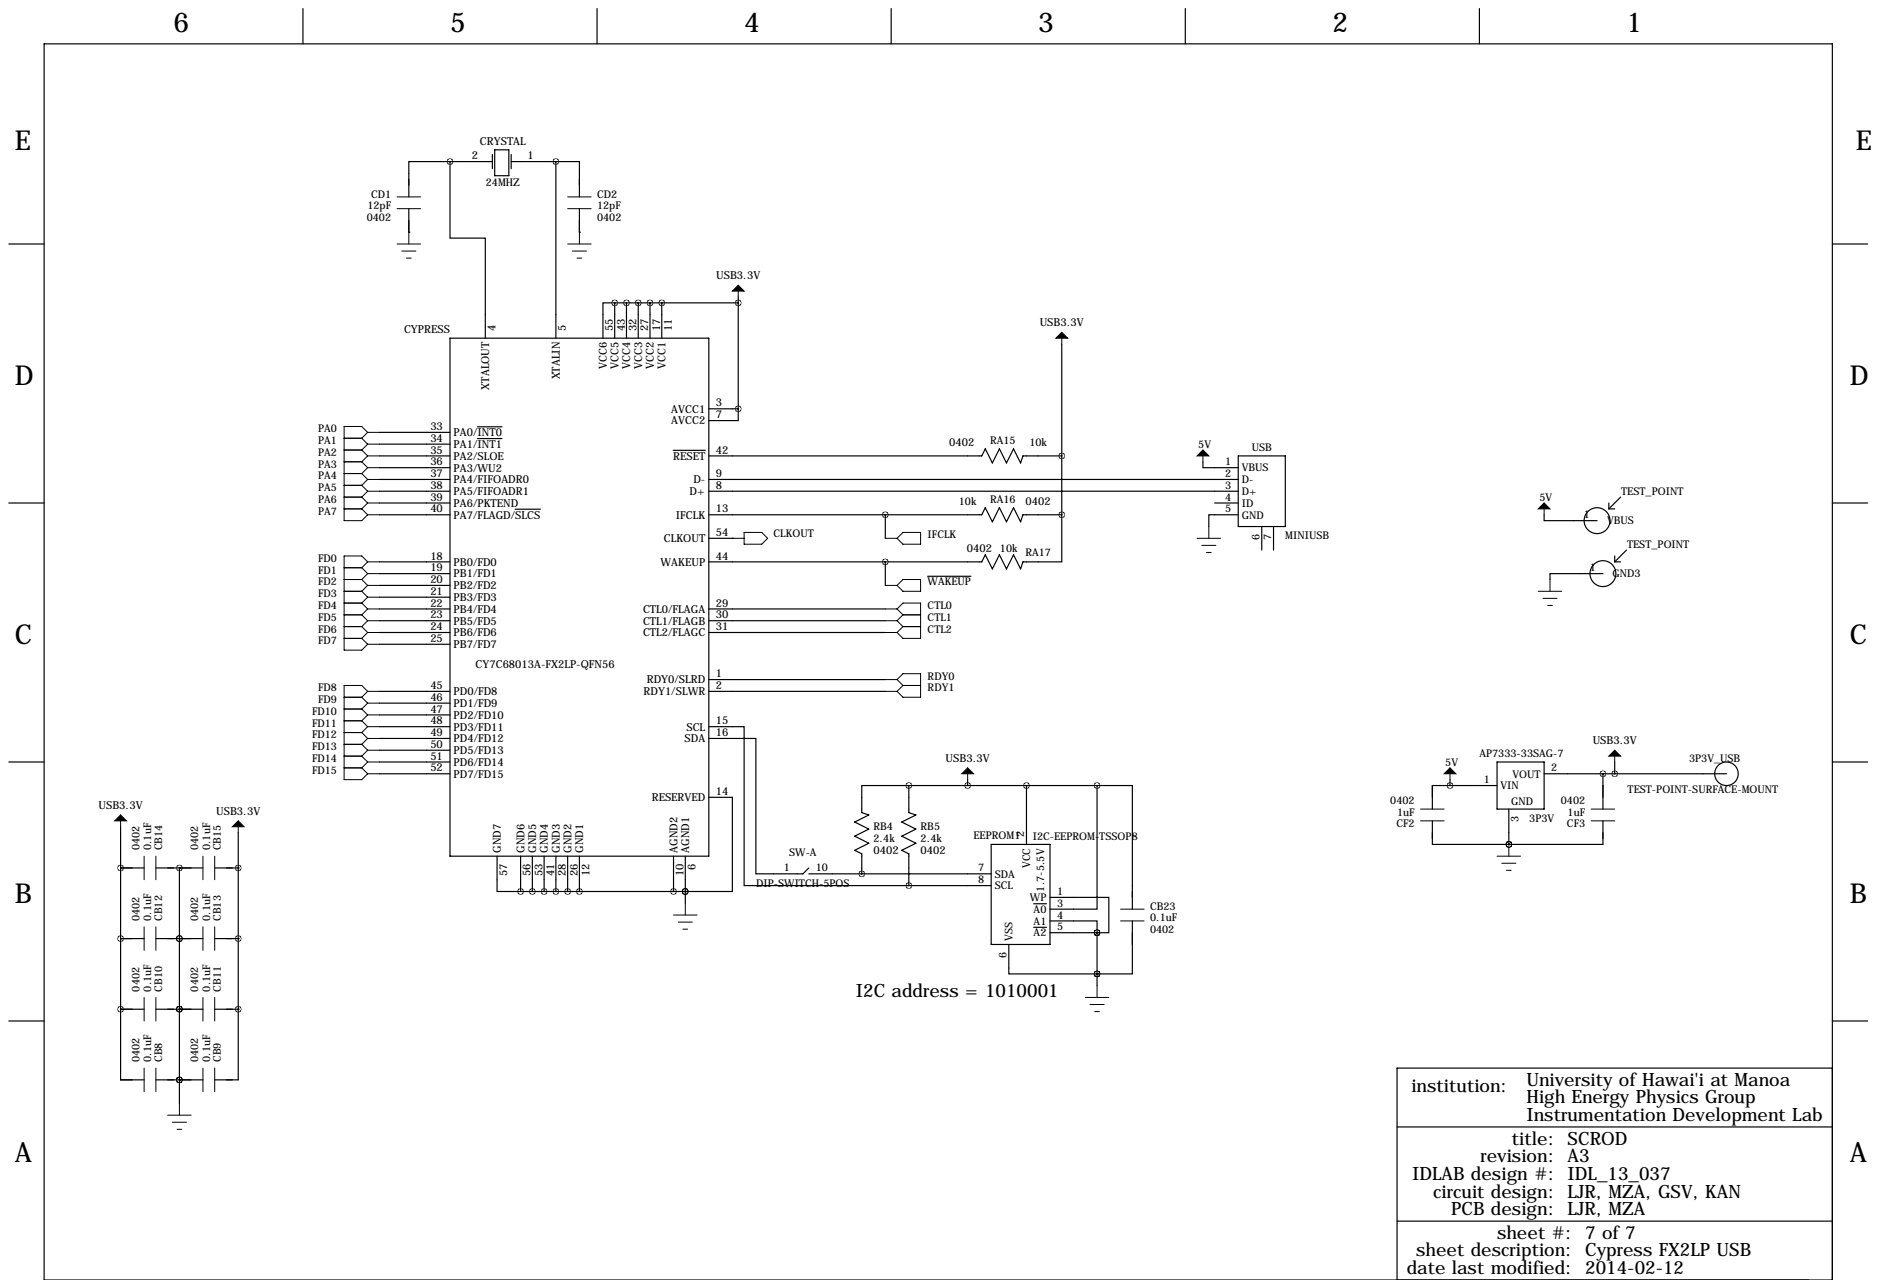
[picture p195: page 7]
institution:; SCROD A3; Cypress FX2LP USB; I2C address = 1010001; GND; 1 VBUS 2 D-; USB; MINIUSB; VIN; VOUT; AP7333-33SAG-7; AVCC1; 42 RESET; 13 IFCLK; 54 CLKOUT; 44 WAKEUP; 29 CTL0/FLAGA; 30 CTL1/FLAGB; 31 CTL2/FLAGC; RDY0/SLRD; RDY1/SLWR; 15 SCL; 16 SDA; PA0/INT0 34; PA1/INT1 35; PA2/SLOE 36; PA4/FIFOADR0 38; PA5/FIFOADR1 39; PA6/PKTEND 40; PA7/FLAGD/SLCS; 4 XTALOUT; 5 XTALIN; 55 VCC6; 43 VCC5 32 VCC4; 27 VCC3; 17 VCC2 11 VCC1; 14 RESERVED; 56 GND6 53 GND5 41 GND4; 28 GND3 26 GND2 12 GND1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

TEST-POINT-SURFACE-MOUNT

University of Hawai'i at Manoa
High Energy Physics Group
Instrumentation Development Lab
title:
revision:
