mzandrew/idlab-scrod/mechanical-designs/board-stack/iTOP/export/pogo-pin-carrier-for-signal-pins.PDF

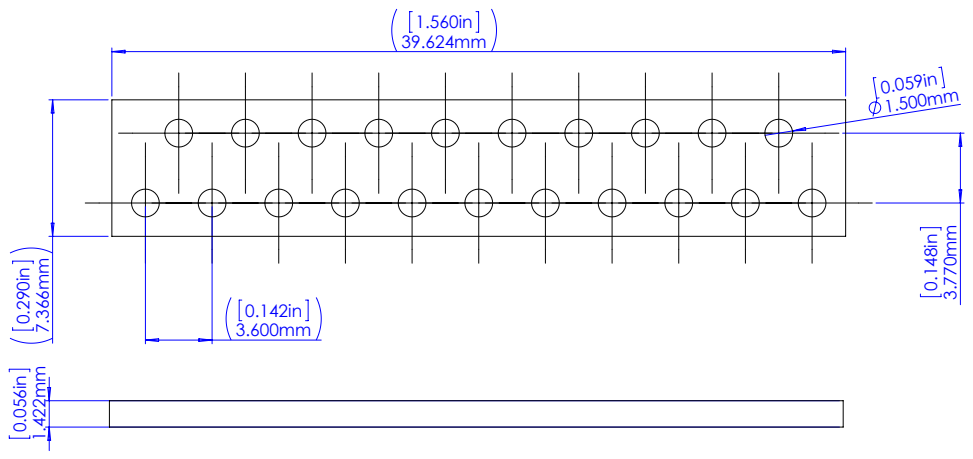
[picture p202: page 1]
