mzandrew/idlab-scrod/mechanical-designs/board-stack/iTOP/export/SCROD-and-carriers-with-walls-and-front-PMT-PEEK-assembly.PDF

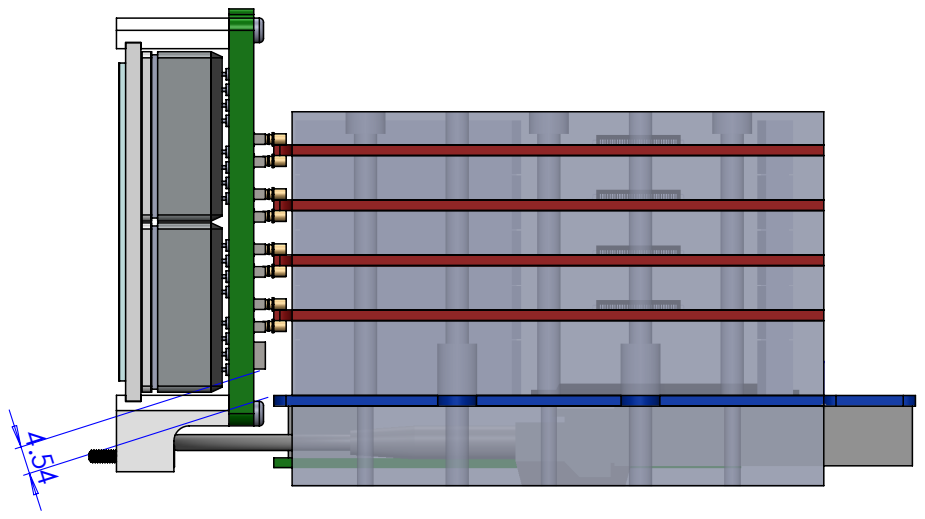
[picture p203: page 1]
