mzandrew/idlab-scrod/mechanical-designs/board-stack/iTOP/export/board-spacers.PDF

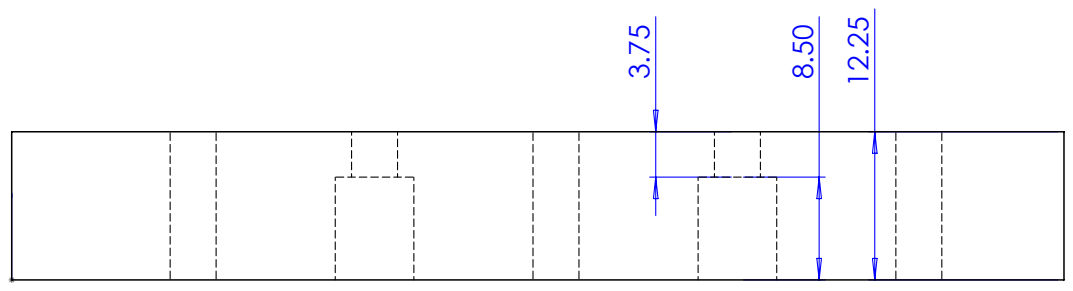
[picture p204: page 1]
