mzandrew/idlab-scrod/mechanical-designs/board-stack/iTOP/export/SCROD-and-carriers-with-walls.new-carrier-shape.PDF

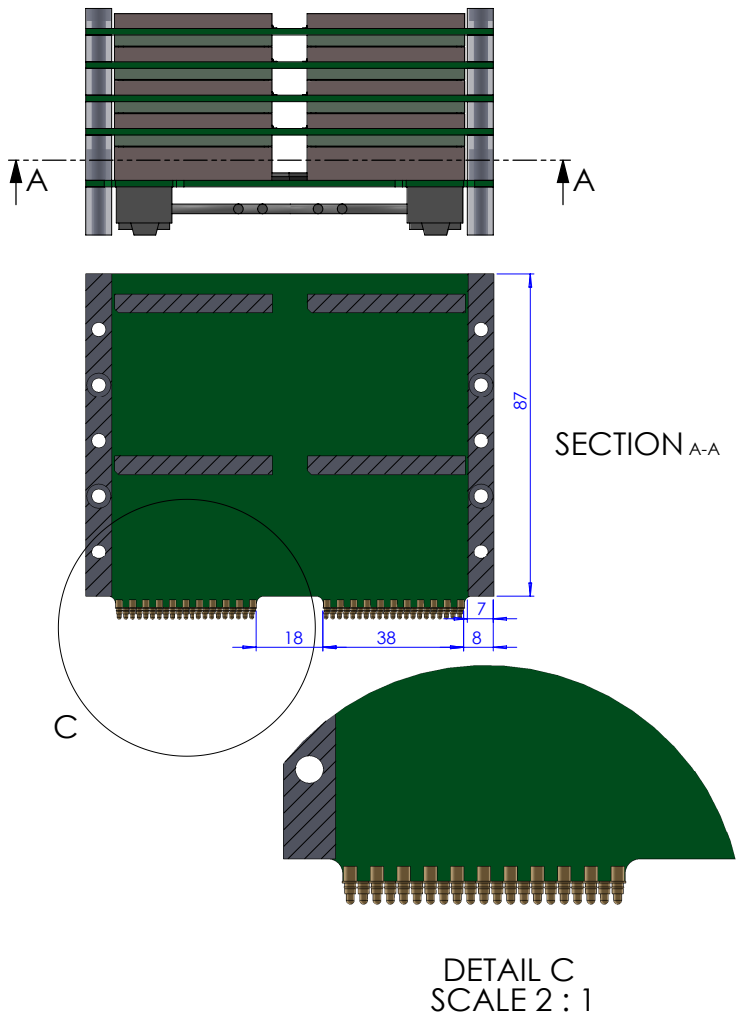
[picture p205: page 1]
SECTION A-A; DETAIL C SCALE 2 : 1
