mzandrew/idlab-scrod/mechanical-designs/common-components/connectors/export/fiber-optic.PDF

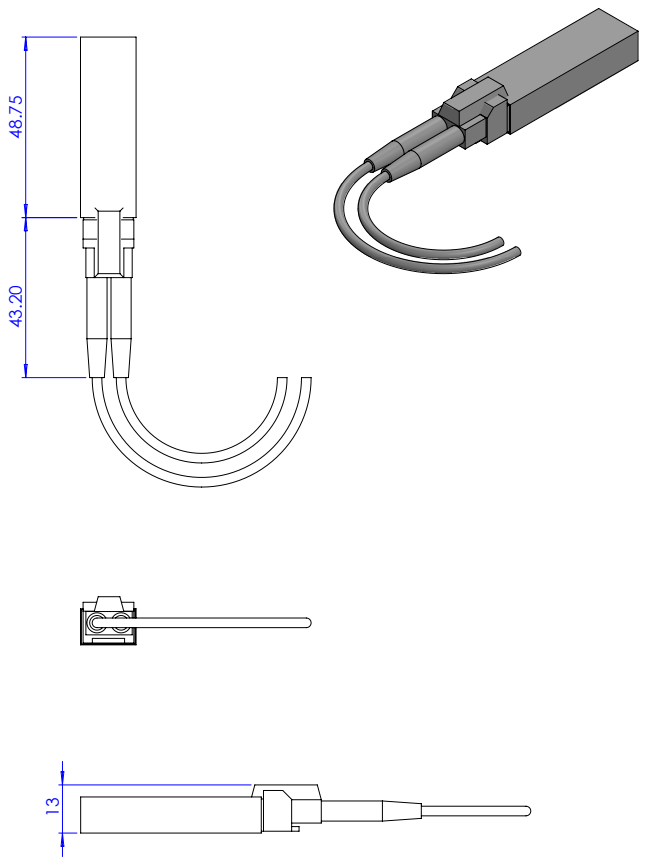
[picture p206: page 1]
