mzandrew/idlab-scrod/mechanical-designs/board-stack/iTOP/export/SCROD-and-carriers-with-walls.PDF

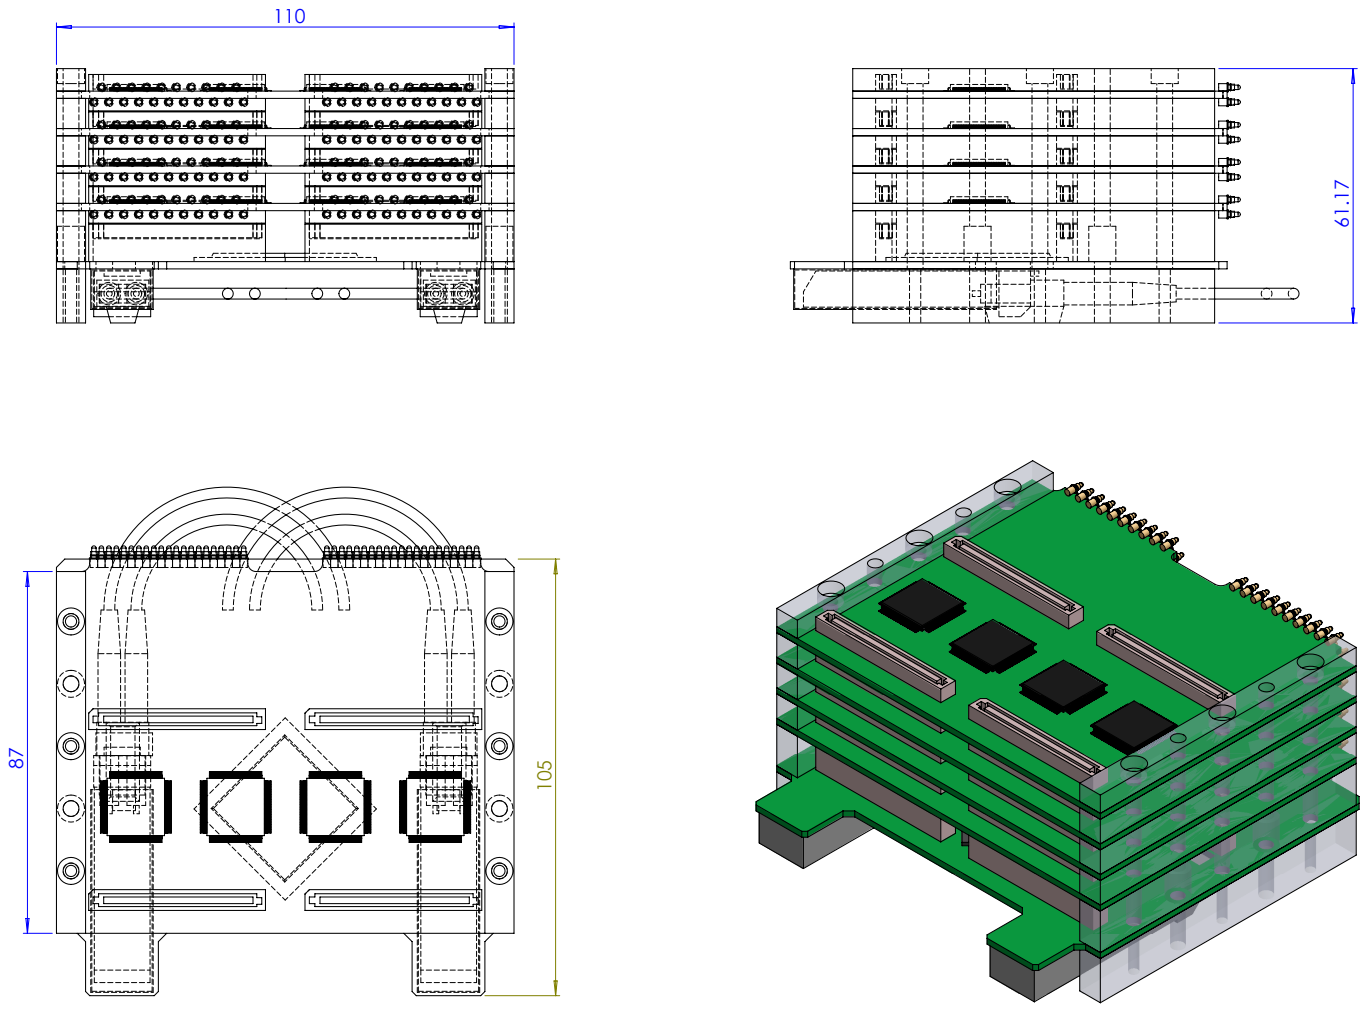
[picture p207: page 1]
