mzandrew/idlab-scrod/mechanical-designs/board-stack/iTOP/export/SCROD-and-carriers.PDF

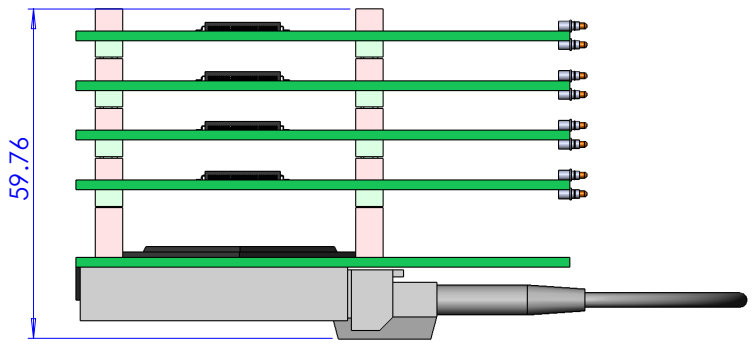
[picture p208: page 1]
