mzandrew/idlab-scrod/mechanical-designs/tags/r282.iTOP-module-used-at-LEPS-SPRING8/common-components/jigs/16pin-2mm-pin-puller.PDF

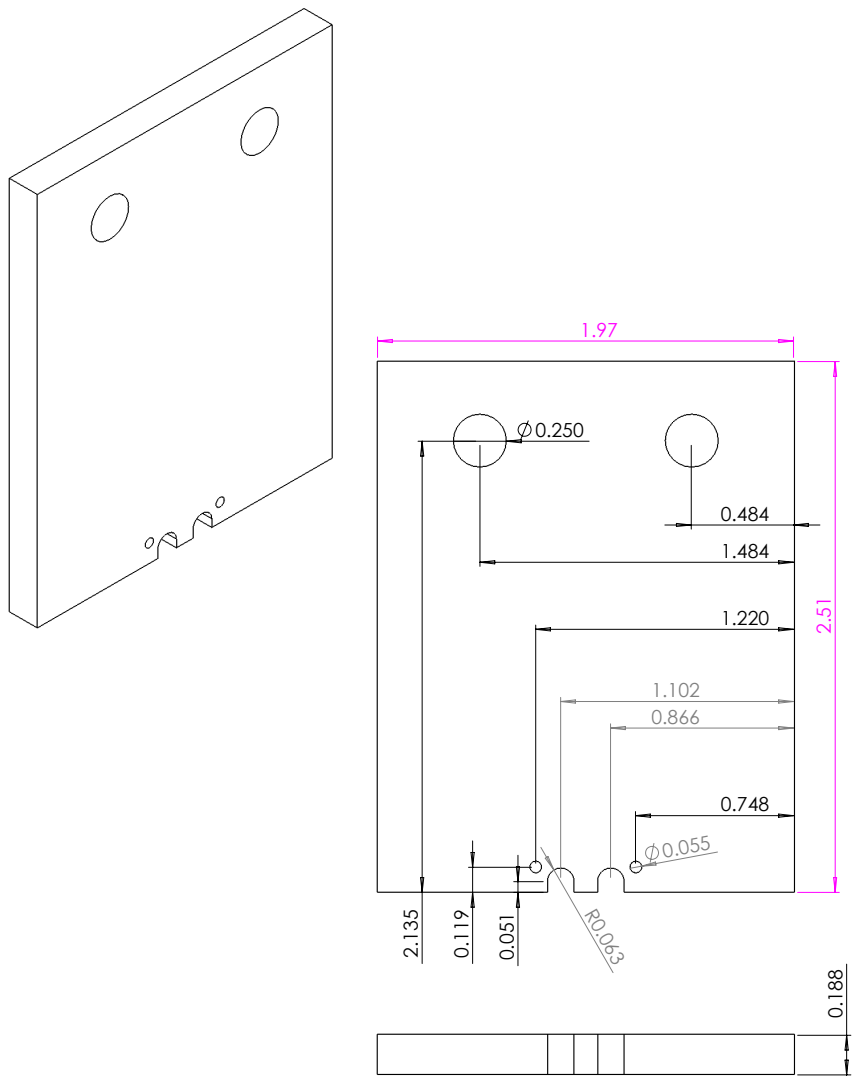
[picture p209: page 1]
