mzandrew/idlab-scrod/mechanical-designs/tags/r282.iTOP-module-used-at-LEPS-SPRING8/common-components/jigs/22pin-2mm-pin-puller.PDF

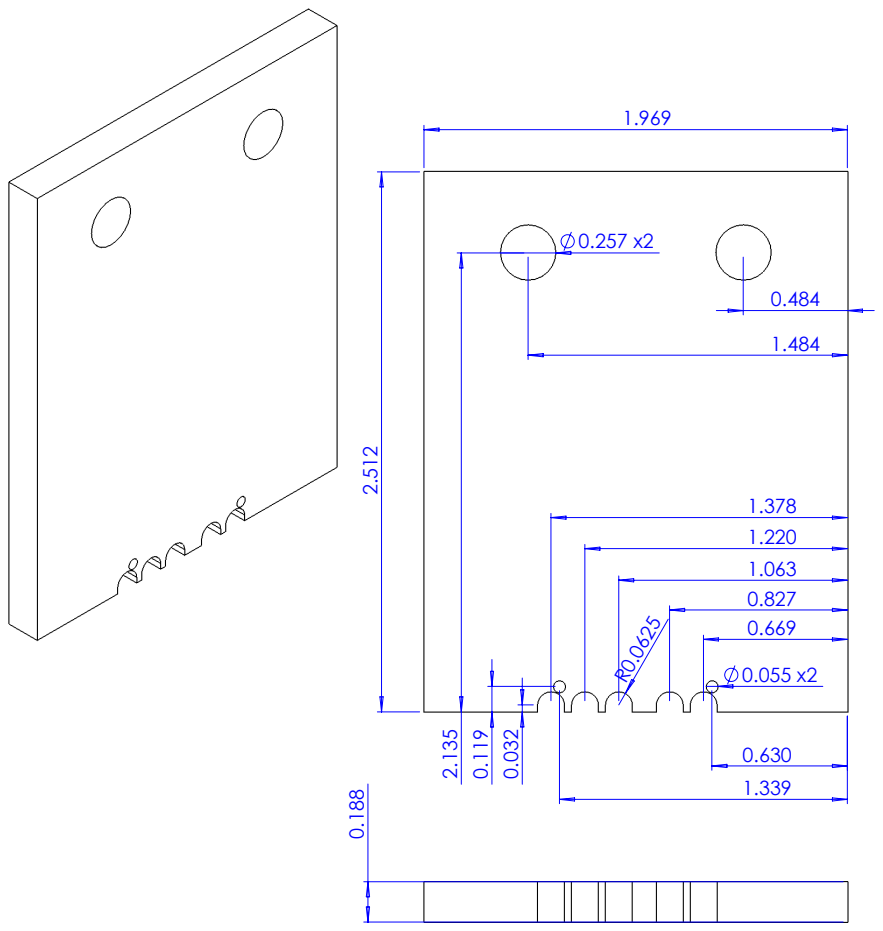
[picture p210: page 1]
