mzandrew/idlab-scrod/SCROD-boardstack/STURM2-ATF2/software/ezusbsys.h

#define ANCHOR_LOAD_INTERNAL  0xA0
#define ANCHOR_LOAD_EXTERNAL  0xA3
#define ANCHOR_ISFX2          0xAC
#define MAX_INTERNAL_ADDRESS  0x1B3F
#define INTERNAL_RAM(address) ((address <= MAX_INTERNAL_ADDRESS) ? 1 : 0)
#define CPUCS_REG_EZUSB    0x7F92
#define CPUCS_REG_FX2      0xE600
#define _BYTE_DEFINED
typedef unsigned char BYTE;
#define _WORD_DEFINED
typedef unsigned short WORD;
typedef struct _VENDOR_REQUEST_IN
{
    BYTE    bRequest;
    WORD    wValue;
    WORD    wIndex;
    WORD    wLength;
    BYTE    direction;
    BYTE    bData;
} VENDOR_REQUEST_IN, *PVENDOR_REQUEST_IN;
typedef struct _BULK_TRANSFER_CONTROL
{
   ULONG pipeNum;
} BULK_TRANSFER_CONTROL, *PBULK_TRANSFER_CONTROL;
typedef struct _BULK_LATENCY_CONTROL
{
   ULONG bulkPipeNum;
   ULONG intPipeNum;
   ULONG loops;
} BULK_LATENCY_CONTROL, *PBULK_LATENCY_CONTROL;
typedef struct _ISO_LOOPBACK_CONTROL
{
   ULONG outPipeNum;
   ULONG inPipeNum;
   ULONG packetSize;
} ISO_LOOPBACK_CONTROL, *PISO_LOOPBACK_CONTROL;
typedef struct _VENDOR_OR_CLASS_REQUEST_CONTROL
{
   UCHAR direction;
   UCHAR requestType;
   UCHAR recepient;
   UCHAR requestTypeReservedBits;
   UCHAR request;
   USHORT value;
   USHORT index;
} VENDOR_OR_CLASS_REQUEST_CONTROL, *PVENDOR_OR_CLASS_REQUEST_CONTROL;
typedef struct _SET_FEATURE_CONTROL
{
   USHORT FeatureSelector;
   USHORT Index;
} SET_FEATURE_CONTROL, *PSET_FEATURE_CONTROL;
typedef struct _ISO_TRANSFER_CONTROL
{
   ULONG PipeNum;
   ULONG PacketSize;
   ULONG PacketCount;
   ULONG FramesPerBuffer;     // 10 is a good value
   ULONG BufferCount;         // 2 is a good value
} ISO_TRANSFER_CONTROL, *PISO_TRANSFER_CONTROL;
typedef struct _ANCHOR_DOWNLOAD_CONTROL
{
   WORD Offset;
} ANCHOR_DOWNLOAD_CONTROL, *PANCHOR_DOWNLOAD_CONTROL;
#define MAX_INTEL_HEX_RECORD_LENGTH 16
typedef struct _INTEL_HEX_RECORD
{
   BYTE  Length;
   WORD  Address;
   BYTE  Type;
   BYTE  Data[MAX_INTEL_HEX_RECORD_LENGTH];
} INTEL_HEX_RECORD, *PINTEL_HEX_RECORD;
typedef struct _SET_INTERFACE_IN
{
   UCHAR interfaceNum;
   UCHAR alternateSetting;
} SET_INTERFACE_IN, *PSET_INTERFACE_IN;
typedef struct _GET_STRING_DESCRIPTOR_IN
{
   UCHAR    Index;
   USHORT   LanguageId;
} GET_STRING_DESCRIPTOR_IN, *PGET_STRING_DESCRIPTOR_IN;
typedef struct _EZUSB_DRIVER_VERSION
{
   WORD     MajorVersion;
   WORD     MinorVersion;
   WORD     BuildVersion;
} EZUSB_DRIVER_VERSION, *PEZUSB_DRIVER_VERSION;
#ifdef DRIVER
typedef struct _RING_BUFFER
{
   PUCHAR      inPtr;
   PUCHAR      outPtr;
   ULONG       totalSize;
   ULONG       currentSize;
   KSPIN_LOCK	spinLock;
   PUCHAR      buffer;
} RING_BUFFER, *PRING_BUFFER;
PRING_BUFFER
AllocRingBuffer(
   ULONG    Size
   );
VOID
FreeRingBuffer(
   PRING_BUFFER   ringBuffer
   );
ULONG
ReadRingBuffer(
   PRING_BUFFER   ringBuffer,
   PUCHAR         readBuffer,
   ULONG          numberOfBytesToRead
   );
ULONG
WriteRingBuffer(
   PRING_BUFFER   ringBuffer,
   PUCHAR         writeBuffer,
   ULONG          numberOfBytesToWrite
   );
typedef struct _EZUSB_FIRMWARE
{
   UCHAR tag[10];
   ULONG size;
   UCHAR firmware[];
} EZUSB_FIRMWARE, *PEZUSB_FIRMWARE;
#define DEFAULT_ISO_BUFFER_COUNT 2
#define DEFAULT_ISO_FRAMES_PER_BUFFER 10
typedef struct _ISO_STREAM_OBJECT ISO_STREAM_OBJECT, *PISO_STREAM_OBJECT;
typedef struct _ISO_TRANSFER_OBJECT
{
   ULONG Frame;
   PISO_STREAM_OBJECT StreamObject;
   PURB Urb;
   PIRP Irp;
   KEVENT Done;
} ISO_TRANSFER_OBJECT, *PISO_TRANSFER_OBJECT;
typedef struct _ISO_STREAM_OBJECT
{
   PDEVICE_OBJECT DeviceObject;
   ULONG PacketSize;
   ULONG NumPackets;
   PUSBD_PIPE_INFORMATION PipeInfo;
   PVOID TransferBuffer;
   ULONG TransferBufferLength;
   PVOID IsoDescriptorBuffer;
   ULONG FramesPerBuffer;
   ULONG BufferCount;
   ULONG PendingTransfers;
   PRING_BUFFER DataRingBuffer;
   PRING_BUFFER DescriptorRingBuffer;
   PISO_TRANSFER_OBJECT TransferObject;
} ISO_STREAM_OBJECT, *PISO_STREAM_OBJECT;
#define Ezusb_NAME_MAX  64
typedef struct _EZUSB_PIPE {
   ULONG Mode;
   ULONG Option;
   ULONG Param1;
   ULONG Param2;
   WCHAR Name[Ezusb_NAME_MAX];
   PUSBD_PIPE_INFORMATION PipeInfo;
} EZUSB_PIPE, *PEZUSB_PIPE;
#define SAMPLE_INTERFACE_NBR 0x00
typedef struct _DEVICE_EXTENSION
{
   PDEVICE_OBJECT PhysicalDeviceObject;
   PDEVICE_OBJECT		StackDeviceObject;
   BOOLEAN Stopped;
   BOOLEAN Started;
   BOOLEAN NeedCleanup;
   USBD_CONFIGURATION_HANDLE ConfigurationHandle;
   PUSB_DEVICE_DESCRIPTOR DeviceDescriptor;
   PUSBD_INTERFACE_INFORMATION Interface;
   ULONG                OpenHandles;
   WCHAR DeviceLinkNameBuffer[Ezusb_NAME_MAX];
   USBD_STATUS LastFailedUrbStatus;
   LONG usage;
	KEVENT evRemove;
   BOOLEAN removing;
   BOOLEAN StopIsoStream;
   PRING_BUFFER DataRingBuffer;
   PRING_BUFFER DescriptorRingBuffer;
} DEVICE_EXTENSION, *PDEVICE_EXTENSION;
#if DBG
#define Ezusb_KdPrint(_x_) DbgPrint("Ezusb.SYS: "); \
                             DbgPrint _x_ ;
#define TRAP() DbgBreakPoint()
#else
#define Ezusb_KdPrint(_x_)
#define TRAP()
#endif
NTSTATUS
Ezusb_Dispatch(
    IN PDEVICE_OBJECT DeviceObject,
    IN PIRP           Irp
    );
VOID
Ezusb_Unload(
    IN PDRIVER_OBJECT DriverObject
    );
NTSTATUS
Ezusb_StartDevice(
    IN  PDEVICE_OBJECT DeviceObject
    );
NTSTATUS
Ezusb_StopDevice(
    IN  PDEVICE_OBJECT DeviceObject
    );
NTSTATUS
Ezusb_RemoveDevice(
    IN  PDEVICE_OBJECT DeviceObject
    );
NTSTATUS
Ezusb_CallUSBD(
    IN PDEVICE_OBJECT DeviceObject,
    IN PURB Urb
    );
NTSTATUS
Ezusb_PnPAddDevice(
    IN PDRIVER_OBJECT DriverObject,
    IN PDEVICE_OBJECT PhysicalDeviceObject
    );
NTSTATUS
Ezusb_CreateDeviceObject(
    IN PDRIVER_OBJECT DriverObject,
    IN PDEVICE_OBJECT *DeviceObject,
    LONG Instance
    );
NTSTATUS
Ezusb_ConfigureDevice(
    IN  PDEVICE_OBJECT DeviceObject
    );
NTSTATUS
Ezusb_Create(
    IN PDEVICE_OBJECT DeviceObject,
    IN PIRP Irp
    );
NTSTATUS
Ezusb_Close(
    IN PDEVICE_OBJECT DeviceObject,
    IN PIRP Irp
    );
NTSTATUS
Ezusb_Read_Write(
   IN  PDEVICE_OBJECT DeviceObject,
   IN  PIRP Irp
   );
NTSTATUS
Ezusb_ProcessIOCTL(
    IN PDEVICE_OBJECT DeviceObject,
    IN PIRP Irp
    );
NTSTATUS
Ezusb_SelectInterfaces(
    IN PDEVICE_OBJECT DeviceObject,
    IN PUSB_CONFIGURATION_DESCRIPTOR ConfigurationDescriptor,
    IN PUSBD_INTERFACE_INFORMATION Interface
    );
NTSTATUS
Ezusb_ResetPipe(
   IN PDEVICE_OBJECT DeviceObject,
   IN ULONG PipeNum
   );
NTSTATUS
Ezusb_AbortPipe(
    IN PDEVICE_OBJECT DeviceObject,
    IN USBD_PIPE_HANDLE PipeHandle
    );
ULONG
Ezusb_GetCurrentFrameNumber(
    IN PDEVICE_OBJECT DeviceObject
    );
NTSTATUS
Ezusb_Read_Write_Direct(
    IN  PDEVICE_OBJECT DeviceObject,
    IN  PIRP Irp,
    IN  BOOLEAN Read
    );
ULONG
Ezusb_DownloadTest(
    IN PDEVICE_OBJECT DeviceObject,
    IN PVENDOR_REQUEST_IN pVendorRequest
    );
NTSTATUS
Ezusb_ResetParentPort(
    IN IN PDEVICE_OBJECT DeviceObject
    );
VOID
Ezusb_Cleanup(
    PDEVICE_OBJECT DeviceObject
    );
ULONG
Ezusb_GetDescriptor(
    IN PDEVICE_OBJECT fdo,
    PVOID             DescriptorBuffer,
    ULONG             BufferLength,
    UCHAR             DescriptorType
    );
ULONG
Ezusb_GetDeviceDescriptor(
    IN PDEVICE_OBJECT DeviceObject,
    PVOID             pvOutputBuffer
    );
ULONG
Ezusb_GetConfigDescriptor(
    IN PDEVICE_OBJECT DeviceObject,
    PVOID             pvOutputBuffer,
    ULONG             ulngth
    );
ULONG
Ezusb_VendorRequest(
    IN PDEVICE_OBJECT DeviceObject,
    PVENDOR_REQUEST_IN pVendorRequest
    );
ULONG
Ezusb_GetCurrentConfig(
    IN PDEVICE_OBJECT DeviceObject,
    IN PVENDOR_REQUEST_IN pVendorRequest
    );
ULONG
Ezusb_GetCurrentInterface(
    IN PDEVICE_OBJECT DeviceObject,
    IN PVENDOR_REQUEST_IN pVendorRequest
    );
PUSB_CONFIGURATION_DESCRIPTOR
GetConfigDescriptor(
    IN PDEVICE_OBJECT DeviceObject
    );
NTSTATUS
ConfigureDevice(
    IN  PDEVICE_OBJECT DeviceObject
    );
NTSTATUS
SetInterface(
   IN PDEVICE_OBJECT DeviceObject,
   IN UCHAR InterfaceNumber,
   IN UCHAR AlternateSetting
   );
ULONG
Ezusb_GetStringDescriptor(
    IN PDEVICE_OBJECT DeviceObject,
    UCHAR             Index,
    USHORT            LanguageId,
    PVOID             pvOutputBuffer,
    ULONG             ulLength
    );
NTSTATUS
Ezusb_VendorRequest2(
   IN PDEVICE_OBJECT DeviceObject,
   IN PIRP Irp
   );
NTSTATUS
ForwardAndWait(
   IN PDEVICE_OBJECT DeviceObject,
   IN PIRP Irp
   );
NTSTATUS
Ezusb_DefaultPnpHandler(
   IN PDEVICE_OBJECT fdo,
   IN PIRP Irp
   );
NTSTATUS
Ezusb_DispatchPnp(
   IN PDEVICE_OBJECT DeviceObject,
   IN PIRP           Irp
   );
NTSTATUS
Ezusb_DispatchPower(
    IN PDEVICE_OBJECT DeviceObject,
    IN PIRP           Irp
    );
NTSTATUS
Ezusb_HandleStartDevice(
   IN PDEVICE_OBJECT DeviceObject,
   IN PIRP Irp
   );
NTSTATUS
Ezusb_HandleRemoveDevice(
   IN PDEVICE_OBJECT fdo,
   IN PIRP Irp
   );
NTSTATUS
OnRequestComplete(
   IN PDEVICE_OBJECT DeviceObject,
   IN PIRP Irp,
   IN PKEVENT pev
   );
NTSTATUS
CompleteRequest(
   IN PIRP Irp,
   IN NTSTATUS status,
   IN ULONG info
   );
BOOLEAN LockDevice(
   IN PDEVICE_OBJECT fdo
   );
void UnlockDevice(
   PDEVICE_OBJECT fdo
   );
NTSTATUS InitTransferObject(
   IN OUT PISO_STREAM_OBJECT streamObject,
   IN ULONG index
   );
NTSTATUS Ezusb_StartIsoTransfer(
   IN PDEVICE_OBJECT fdo,
   IN PIRP Irp
   );
NTSTATUS IsoTransferComplete(
   IN PDEVICE_OBJECT fdo,
   IN PIRP Irp,
   IN PVOID Context
   );
NTSTATUS Ezusb_AnchorDownload(
   PDEVICE_OBJECT fdo,
   WORD offset,
   PUCHAR downloadBuffer,
   ULONG downloadSize
   );
NTSTATUS Ezusb_DownloadIntelHex(
   PDEVICE_OBJECT fdo,
   PINTEL_HEX_RECORD hexRecord
   );
NTSTATUS Ezusb_8051Reset(
   PDEVICE_OBJECT fdo,
   UCHAR resetBit
   );
NTSTATUS Ezusb_StartIsoStream(
   IN PDEVICE_OBJECT fdo,
   IN PIRP Irp
   );
BOOLEAN IsFx2(
   IN  PDEVICE_OBJECT fdo
   );
NTSTATUS Ezusb_SetFeature(
   IN PDEVICE_OBJECT fdo,
   IN PSET_FEATURE_CONTROL setFeatureControl
   );
#endif      //DRIVER section
#define Ezusb_IOCTL_INDEX  0x0800
#define IOCTL_Ezusb_GET_PIPE_INFO     CTL_CODE(FILE_DEVICE_UNKNOWN,  \
                                                   Ezusb_IOCTL_INDEX+0,\
                                                   METHOD_BUFFERED,  \
                                                   FILE_ANY_ACCESS)
#define IOCTL_Ezusb_GET_DEVICE_DESCRIPTOR CTL_CODE(FILE_DEVICE_UNKNOWN,  \
                                                   Ezusb_IOCTL_INDEX+1,\
                                                   METHOD_BUFFERED,  \
                                                   FILE_ANY_ACCESS)
#define IOCTL_Ezusb_GET_CONFIGURATION_DESCRIPTOR CTL_CODE(FILE_DEVICE_UNKNOWN,  \
                                                   Ezusb_IOCTL_INDEX+2,\
                                                   METHOD_BUFFERED,  \
                                                   FILE_ANY_ACCESS)
#define IOCTL_Ezusb_BULK_OR_INTERRUPT_WRITE     CTL_CODE(FILE_DEVICE_UNKNOWN,  \
                                                   Ezusb_IOCTL_INDEX+3,\
                                                   METHOD_BUFFERED,  \
                                                   FILE_ANY_ACCESS)
#define IOCTL_Ezusb_BULK_OR_INTERRUPT_READ      CTL_CODE(FILE_DEVICE_UNKNOWN,  \
                                                   Ezusb_IOCTL_INDEX+4,\
                                                   METHOD_BUFFERED,  \
                                                   FILE_ANY_ACCESS)
#define IOCTL_Ezusb_VENDOR_REQUEST              CTL_CODE(FILE_DEVICE_UNKNOWN,  \
                                                   Ezusb_IOCTL_INDEX+5,\
                                                   METHOD_BUFFERED,  \
                                                   FILE_ANY_ACCESS)
#define IOCTL_Ezusb_GET_CURRENT_CONFIG          CTL_CODE(FILE_DEVICE_UNKNOWN,  \
                                                   Ezusb_IOCTL_INDEX+6,\
                                                   METHOD_BUFFERED,  \
                                                   FILE_ANY_ACCESS)
#define IOCTL_Ezusb_ANCHOR_DOWNLOAD             CTL_CODE(FILE_DEVICE_UNKNOWN,  \
                                                   Ezusb_IOCTL_INDEX+7,\
                                                   METHOD_BUFFERED,  \
                                                   FILE_ANY_ACCESS)
#define IOCTL_Ezusb_RESET  CTL_CODE(FILE_DEVICE_UNKNOWN,  \
                                                   Ezusb_IOCTL_INDEX+12,\
                                                   METHOD_IN_DIRECT,  \
                                                   FILE_ANY_ACCESS)
#define IOCTL_Ezusb_RESETPIPE  CTL_CODE(FILE_DEVICE_UNKNOWN,  \
                                                   Ezusb_IOCTL_INDEX+13,\
                                                   METHOD_IN_DIRECT,  \
                                                   FILE_ANY_ACCESS)
#define IOCTL_Ezusb_ABORTPIPE  CTL_CODE(FILE_DEVICE_UNKNOWN,  \
                                                   Ezusb_IOCTL_INDEX+15,\
                                                   METHOD_IN_DIRECT,  \
                                                   FILE_ANY_ACCESS)
#define IOCTL_Ezusb_SETINTERFACE  CTL_CODE(FILE_DEVICE_UNKNOWN,  \
                                                   Ezusb_IOCTL_INDEX+16,\
                                                   METHOD_BUFFERED,  \
                                                   FILE_ANY_ACCESS)
#define IOCTL_Ezusb_GET_STRING_DESCRIPTOR CTL_CODE(FILE_DEVICE_UNKNOWN,  \
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
#define IOCTL_EZUSB_SET_FEATURE         CTL_CODE(FILE_DEVICE_UNKNOWN,  \
                                                   Ezusb_IOCTL_INDEX+33,\
                                                   METHOD_BUFFERED,  \
                                                   FILE_ANY_ACCESS)
