mzandrew/idlab-scrod/SCROD-boardstack/fDIRC/pseudo-data_by_fiber/src/pseudo_data_by_fiber.vhdl

-- 2011-06 Xilinx coregen
-- 2011-06 kurtis
-- 2011-07 to 2011-09 mza
---------------------------------------------------------------------------------------------
library IEEE;
use IEEE.STD_LOGIC_1164.all;
use ieee.numeric_std.all;
library UNISIM;
use UNISIM.VCOMPONENTS.ALL;

entity pseudo_data_by_fiber is
	generic(
		CURRENT_PROTOCOL_FREEZE_DATE                   : std_logic_vector(31 downto 0) := x"20110910";
		NUMBER_OF_INPUT_BLOCK_RAMS                     : integer :=  2;
		WIDTH_OF_ASIC_DATA_BLOCKRAM_DATA_BUS           : integer := 16;
		WIDTH_OF_ASIC_DATA_BLOCKRAM_ADDRESS_BUS        : integer := 13;
		USE_CHIPSCOPE                                  : integer := 1
	);
	port (
		-- fiber optic dual clock input
		Aurora_RocketIO_GTP_MGT_101_CLOCK_156_MHz_P             : in    std_logic;
		Aurora_RocketIO_GTP_MGT_101_CLOCK_156_MHz_N             : in    std_logic;
		-- fiber optic transceiver #101 lane 0 I/O
		Aurora_RocketIO_GTP_MGT_101_lane0_Receive_P             : in    std_logic;
		Aurora_RocketIO_GTP_MGT_101_lane0_Receive_N             : in    std_logic;
		Aurora_RocketIO_GTP_MGT_101_lane0_Transmit_P            :   out std_logic;
		Aurora_RocketIO_GTP_MGT_101_lane0_Transmit_N            :   out std_logic;
		FIBER_TRANSCEIVER_0_LASER_FAULT_DETECTED_IN_TRANSMITTER : in    std_logic;
		FIBER_TRANSCEIVER_0_LOSS_OF_SIGNAL_DETECTED_BY_RECEIVER : in    std_logic;
 		FIBER_TRANSCEIVER_0_MODULE_DEFINITION_0_LOW_IF_PRESENT  : in    std_logic;
		FIBER_TRANSCEIVER_0_DISABLE_MODULE                      :   out std_logic;
		-- fiber optic transceiver #101 lane 1 I/O
		FIBER_TRANSCEIVER_1_DISABLE_MODULE                      :   out std_logic;
		-----------------------------------------------------------------------------
		-- remote trigger, revolution pulse and distributed clock
		REMOTE_SIMPLE_TRIGGER_P    : in    std_logic;
		REMOTE_SIMPLE_TRIGGER_N    : in    std_logic;
		REMOTE_ENCODED_TRIGGER_P   : in    std_logic;
		REMOTE_ENCODED_TRIGGER_N   : in    std_logic;
		REMOTE_CLOCK_P             : in    std_logic;
		REMOTE_CLOCK_N             : in    std_logic;
		-- other I/O
		board_clock_250MHz_P	: in    std_logic;
		board_clock_250MHz_N	: in    std_logic;
		LEDS                 :   out std_logic_vector(15 downto 0);
		MONITOR_HEADER_OUTPUT :   out std_logic_vector(14 downto 0);
		MONITOR_HEADER_INPUT  : in    std_logic_vector(15 downto 15)
	);
end pseudo_data_by_fiber;

library IEEE;
use IEEE.STD_LOGIC_1164.all;
use ieee.numeric_std.all;
library UNISIM;
use UNISIM.VCOMPONENTS.ALL;

architecture PDBF of pseudo_data_by_fiber is
	signal global_reset : std_logic := '1';
	signal internal_REQUEST_A_GLOBAL_RESET_1 : std_logic := '0';
	signal internal_REQUEST_A_GLOBAL_RESET_2 : std_logic := '0';
	signal request_a_global_reset            : std_logic := '0';
-- clocks -------------------------------------------------------------------
	signal internal_clock_from_remote_source : std_logic;
	signal internal_clock_250MHz             : std_logic;
	signal internal_COUNTER : std_logic_vector(31 downto 0);
	signal clock_1MHz : std_logic;
	signal clock_1kHz : std_logic;
	signal internal_clock_for_state_machine : std_logic;
	signal clock_select : std_logic := '0'; -- '0' = local; '1' = remote
-- chipscope signals --------------------------------------------------------
	signal chipscope_vio_buttons : std_logic_vector(255 downto 0);
	signal chipscope_vio_display : std_logic_vector(255 downto 0);
	signal chipscope_ila_data    : std_logic_vector(255 downto 0) := (others => '0');
	signal chipscope_ila_trigger : std_logic_vector(255 downto 0) := (others => '0');
	signal fiber_readout_chipscope_vio_buttons     : std_logic_vector(255 downto 0) := (others => '0');
	signal fiber_readout_chipscope_vio_display     : std_logic_vector(255 downto 0) := (others => '0');
	signal fake_button : std_logic := '1';
-- trigger signals ----------------------------------------------------------
	signal external_trigger_1_from_monitor_header   : std_logic;
	signal external_trigger_2_from_LVDS             : std_logic;
	signal external_encoded_trigger_from_LVDS       : std_logic;
	signal external_trigger_disable                 : std_logic := '0';
	signal internal_TRIGGER                         : std_logic := '0';
	signal fake_spill_structure_enable              : std_logic;
	signal spill_active                             : std_logic;
	signal raw_5Hz_fake_trigger                     : std_logic := '0';
-- aurora/fiber signals -----------------------------------------------------
	signal transmit_disable : std_logic := '0';
	signal transmit_always : std_logic;
	signal request_a_fiber_link_reset                         : std_logic;
	signal should_not_automatically_try_to_keep_fiber_link_up : std_logic;
	signal fiber_link_is_up                                   : std_logic;
	signal Aurora_data_link_reset                             : std_logic;
	signal internal_Aurora_78MHz_clock                                 : std_logic;
	signal internal_Aurora_RocketIO_GTP_MGT_101_status_LEDs            : std_logic_vector(3 downto 0);
	signal internal_DONE_BUILDING_A_QUARTER_EVENT      : std_logic;
-----------------------------------------------------------------------------
	signal internal_ADDRESS_OF_STARTING_WINDOW_IN_ASIC : std_logic_vector(8 downto 0) := "1" & x"f0";
	signal internal_INPUT_BLOCK_RAM_ADDRESS            : std_logic_vector(NUMBER_OF_INPUT_BLOCK_RAMS-1  downto 0);
	signal internal_ASIC_DATA_BLOCKRAM_DATA_BUS        : std_logic_vector(WIDTH_OF_ASIC_DATA_BLOCKRAM_DATA_BUS-1        downto 0);
	signal internal_ASIC_DATA_BLOCKRAM_ADDRESS_BUS     : std_logic_vector(WIDTH_OF_ASIC_DATA_BLOCKRAM_ADDRESS_BUS-1     downto 0);
begin
	process(internal_clock_for_state_machine, request_a_global_reset)
		variable internal_COUNTER  : integer range 0 to 250000000 := 0;
	begin
		if (rising_edge(internal_clock_for_state_machine)) then
			if (request_a_global_reset = '1') then
				internal_COUNTER := 0;
				global_reset <= '1';
			elsif (internal_COUNTER < 2500000) then
				internal_COUNTER := internal_COUNTER + 1;
			else
				global_reset <= '0';
			end if;
		end if;
	end process;
	request_a_global_reset <= internal_REQUEST_A_GLOBAL_RESET_1 or internal_REQUEST_A_GLOBAL_RESET_2;
-----------------------------------------------------------------------------
	process(internal_clock_for_state_machine, global_reset)
		variable counter_250_MHz  : integer range 0 to 250 := 0;
	begin
		if (global_reset = '1') then
			counter_250_MHz := 0;
		elsif rising_edge(internal_clock_for_state_machine) then
			counter_250_MHz := counter_250_MHz + 1;
			clock_1MHz <= '0';
			if (counter_250_MHz > 124) then
				clock_1MHz <= '1';
			end if;
			if (counter_250_MHz > 249) then -- is 1 to 250 at this part of the loop
				counter_250_MHz := 0;
			end if;
		end if;
	end process;
-----------------------------------------------------------------------------
	process(clock_1MHz, global_reset)
		variable counter_1_MHz    : integer range 0 to 10 := 0;
		variable counter_100_kHz  : integer range 0 to 10 := 0;
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
